dmolinagarcia/74HCT6526/img/20220725_B0.jpg

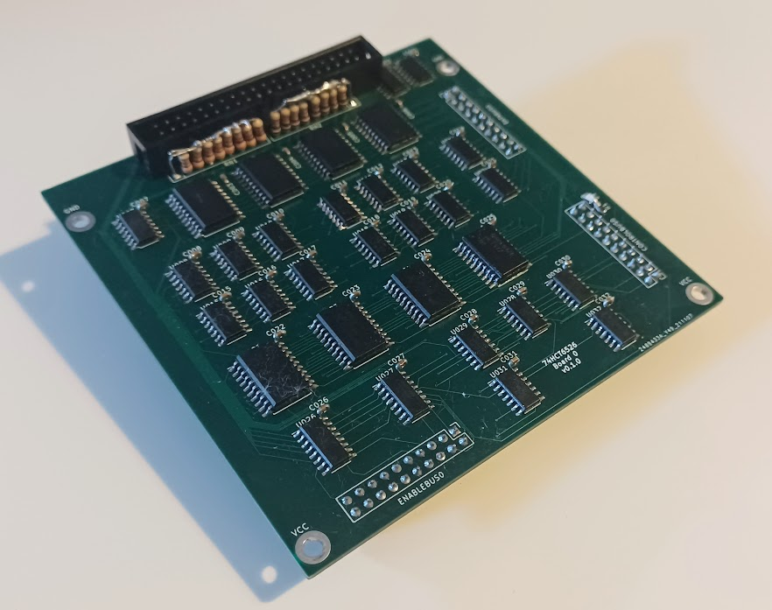
img/20220725_B0.jpg
