dmolinagarcia/74HCT6526/img/20220726_B1+B0+SBC.jpg

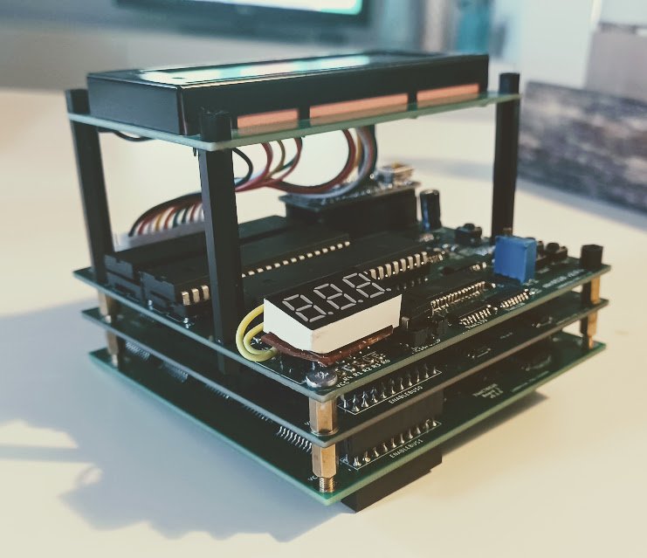
img/20220726_B1+B0+SBC.jpg
