dmolinagarcia/74HCT6526/img/20220726_B1.jpg

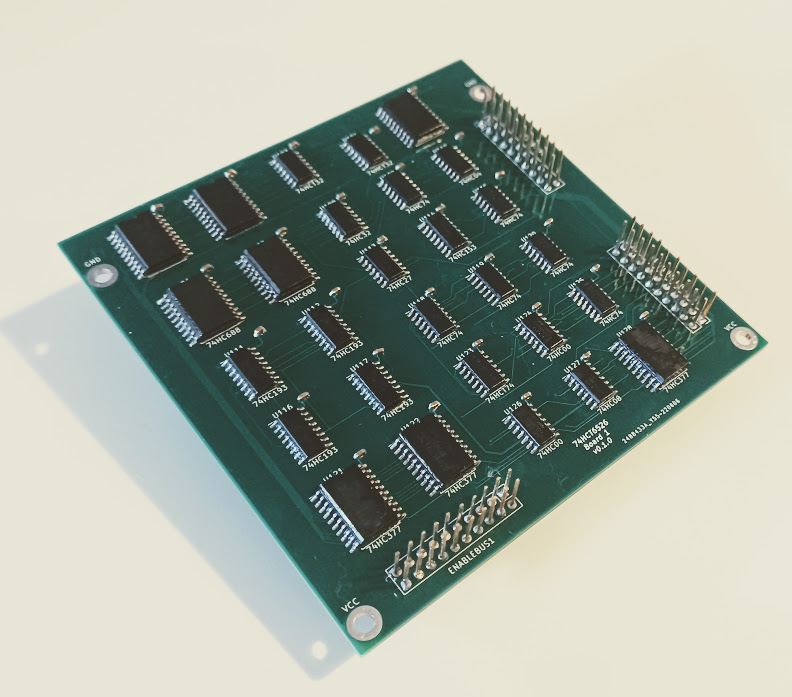
img/20220726_B1.jpg
