dmolinagarcia/74HCT6526/img/20230119_SDR_INPUT_fail.jpg

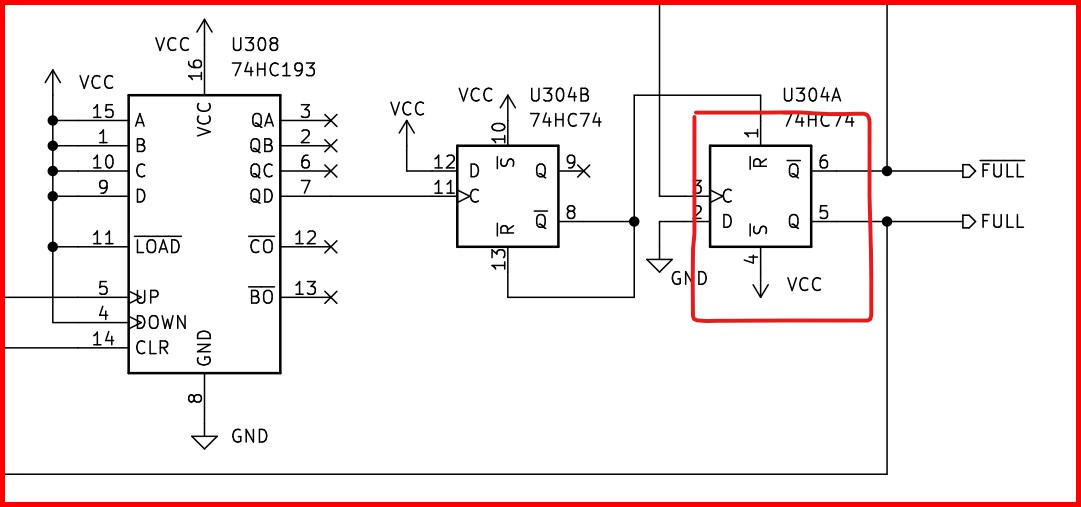
img/20230119_SDR_INPUT_fail.jpg
