dmolinagarcia/74HCT6526/img/20230120_SDR_RECEIVE_0x15.jpg

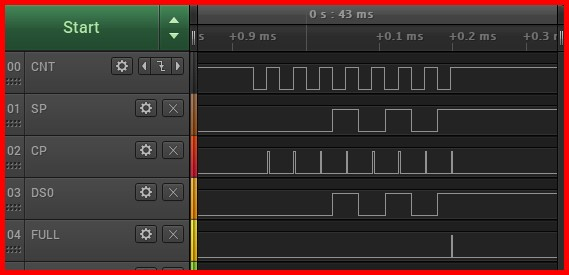
img/20230120_SDR_RECEIVE_0x15.jpg
