dmolinagarcia/74HCT6526/img/20230120_SDR_surgery2.jpg

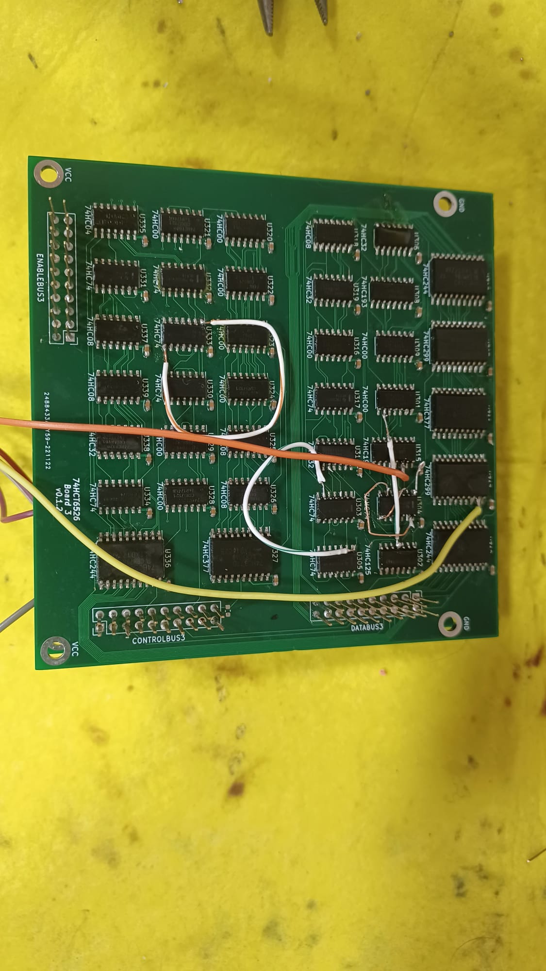
img/20230120_SDR_surgery2.jpg
