dmolinagarcia/74HCT6526/img/20230506_B3_NEWLOOK.jpeg

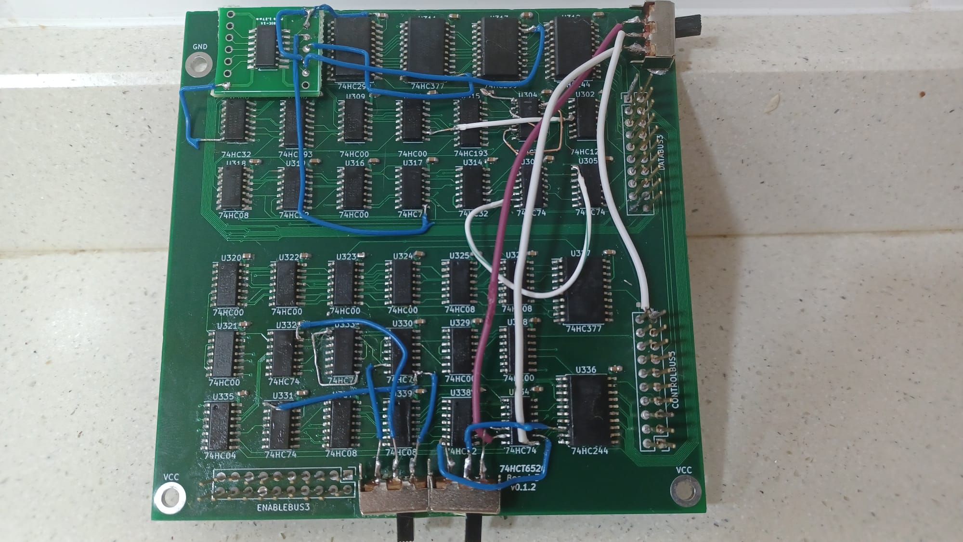
img/20230506_B3_NEWLOOK.jpeg
