dmolinagarcia/74HCT6526/img/All3_20221001.jpg

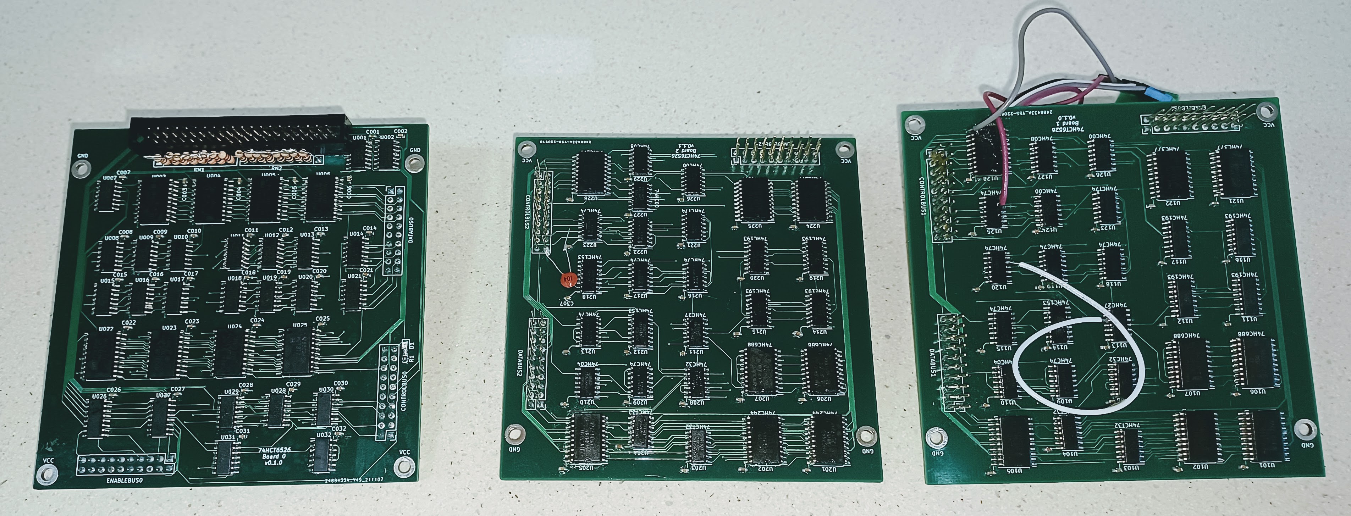
img/All3_20221001.jpg
