dmolinagarcia/74HCT6526/img/flag_detector_fail.jpg

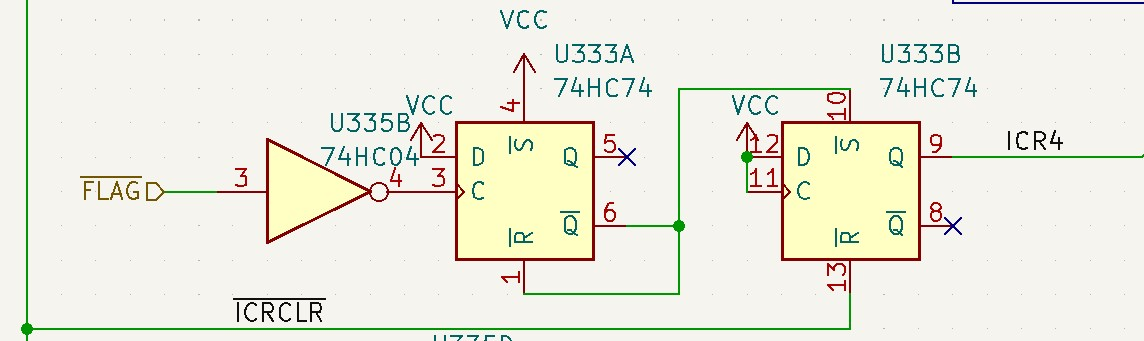
img/flag_detector_fail.jpg
