dmolinagarcia/74HCT6526/img/flag_detector_ok.jpg

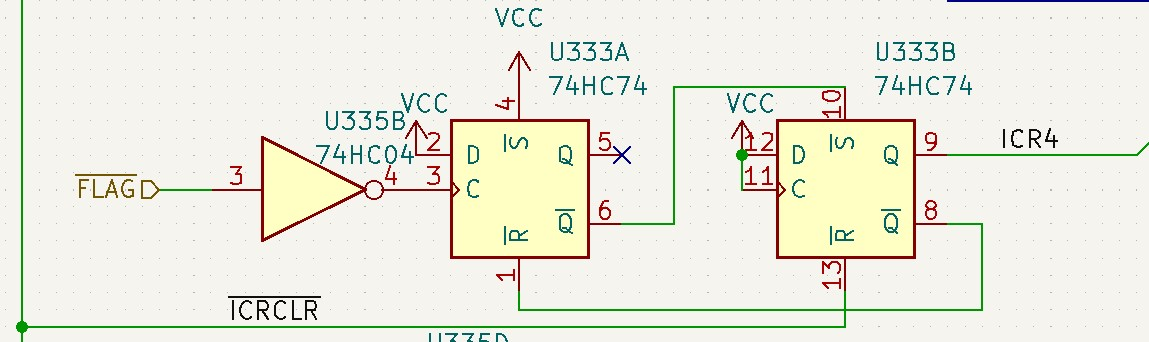
img/flag_detector_ok.jpg
