dmolinagarcia/74HCT6526/img/Photos-001/20230319_prefix.jpg

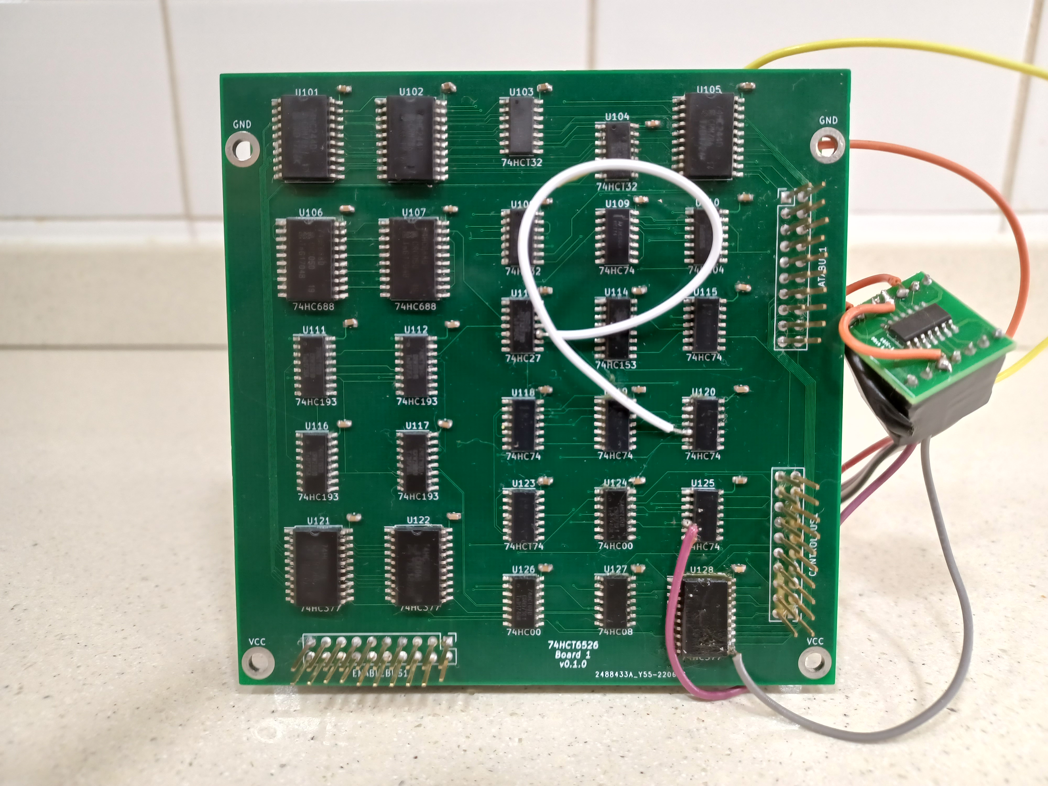
img/Photos-001/20230319_prefix.jpg
