dmolinagarcia/74HCT6526/img/SDR_stateMachine_v1.jpg

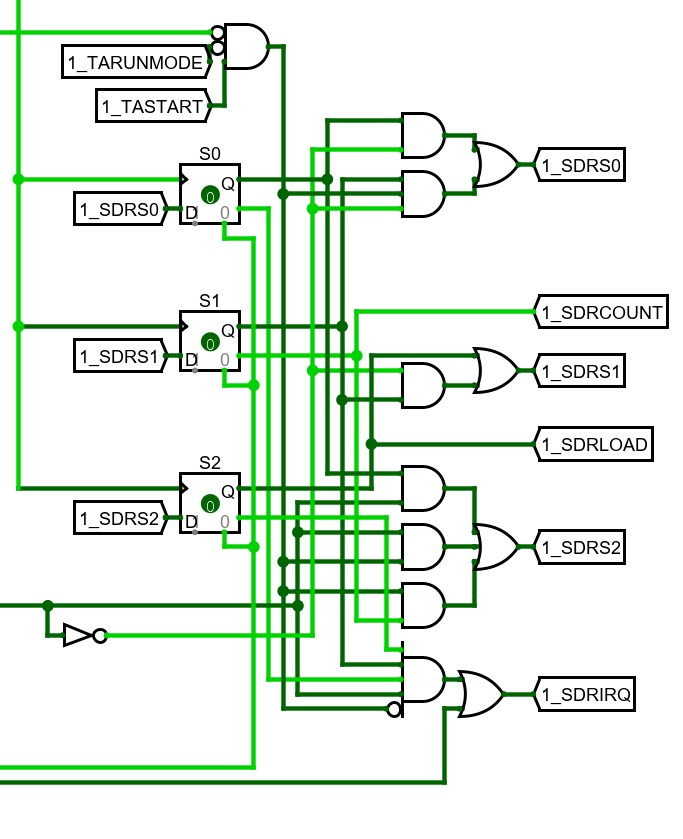
img/SDR_stateMachine_v1.jpg
