dmolinagarcia/74HCT6526/img/SDR_stateMachine_v2.jpg

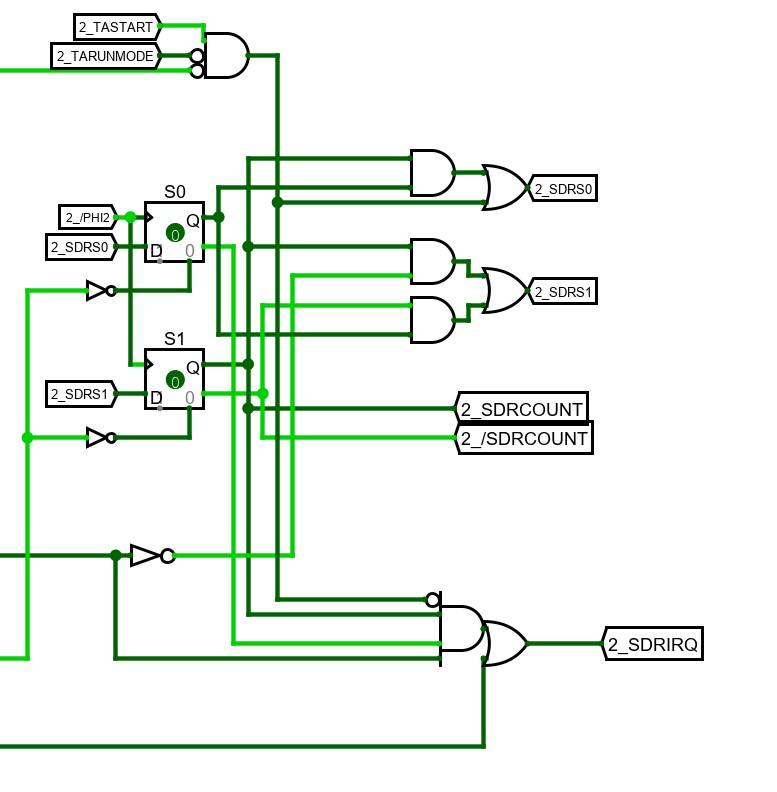
img/SDR_stateMachine_v2.jpg
