dmolinagarcia/74HCT6526/img/STACK_20221001.jpg

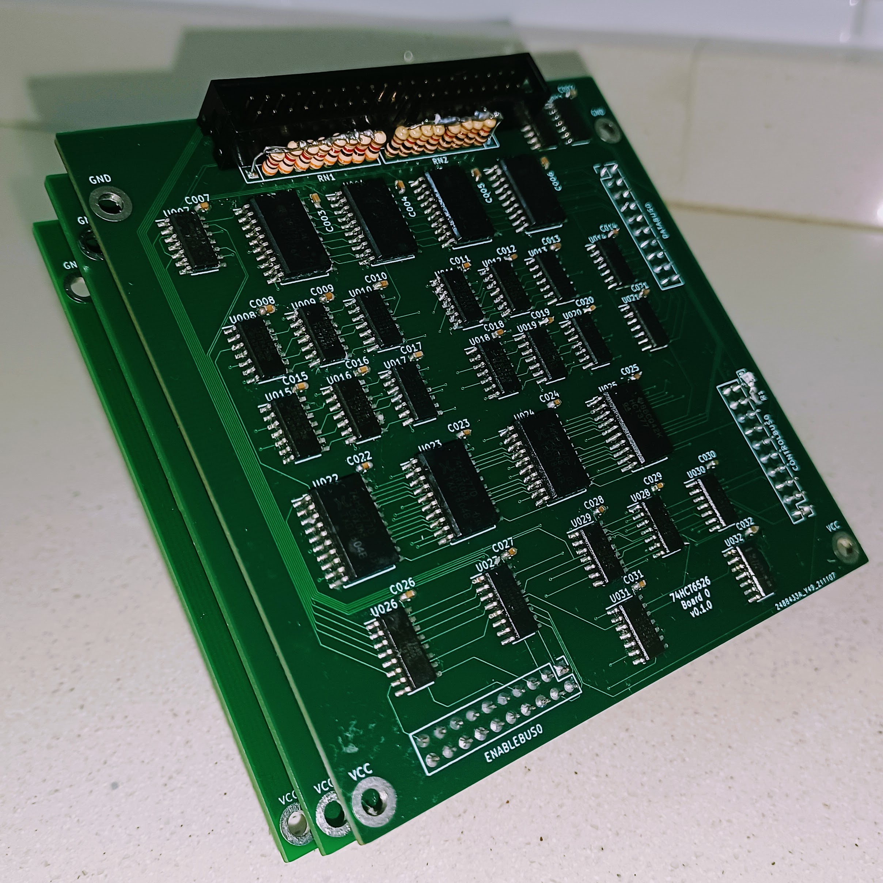
img/STACK_20221001.jpg
