dmolinagarcia/74HCT6526/img/timer2_clockpipeline - copia.png

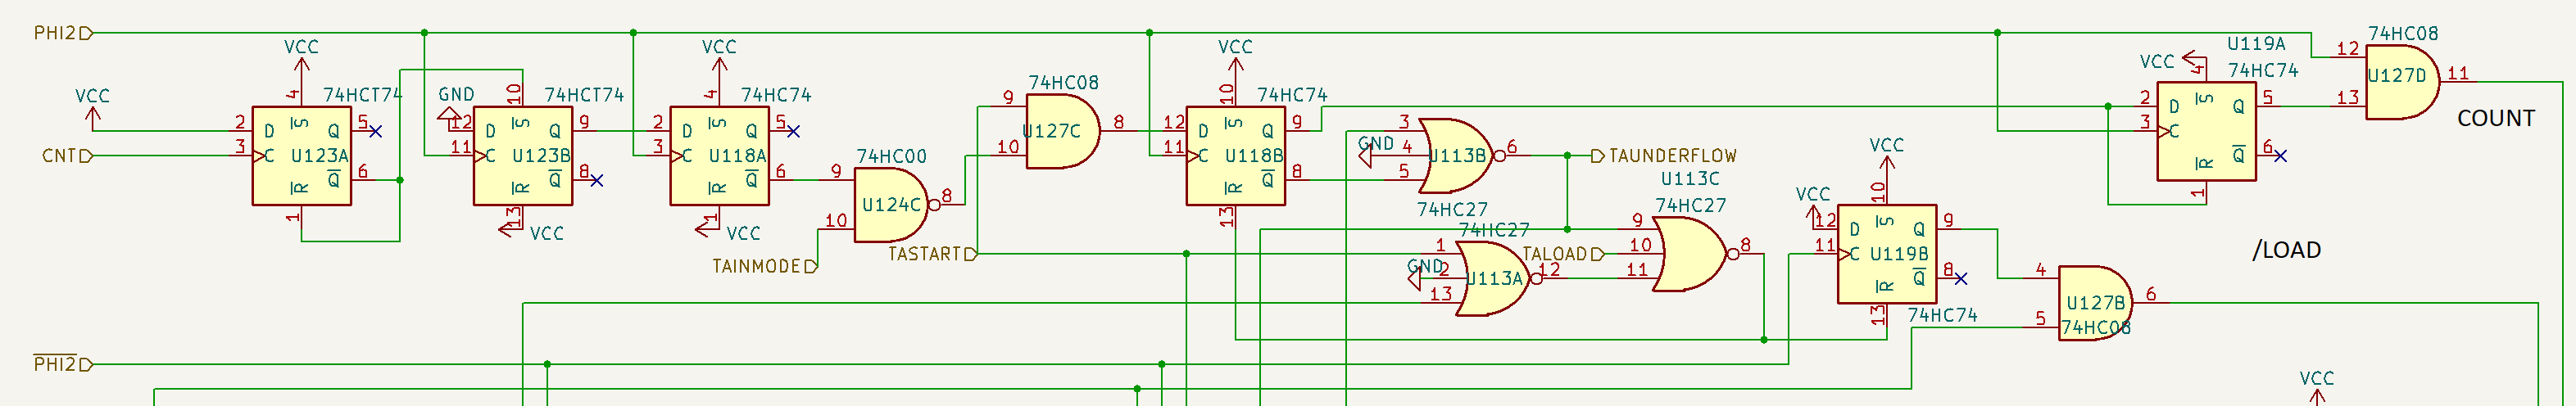
img/timer2_clockpipeline - copia.png
