dmolinagarcia/74HCT6526/img/timer2_clockpipeline_annotated.png

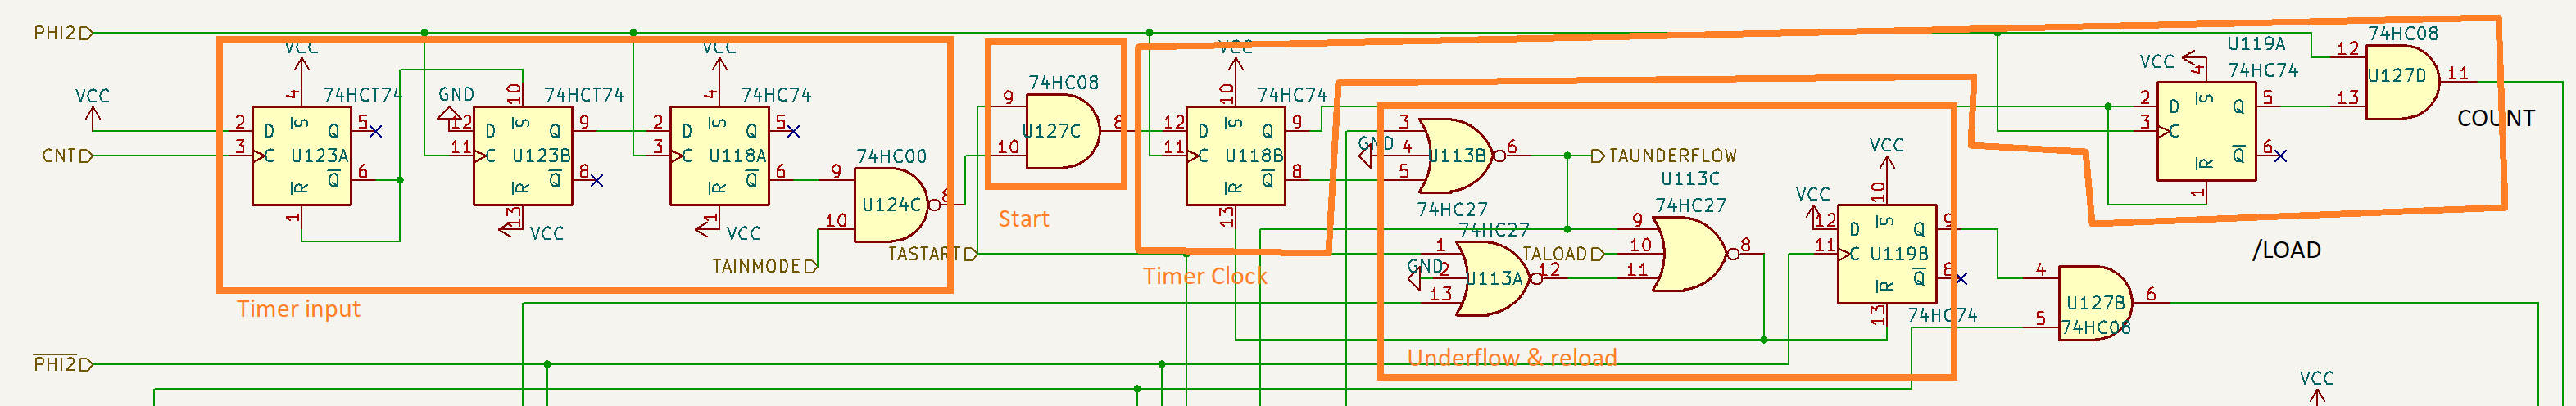
img/timer2_clockpipeline_annotated.png
