dmolinagarcia/74HCT6526/img/Photos-001/20230319_step2.jpg

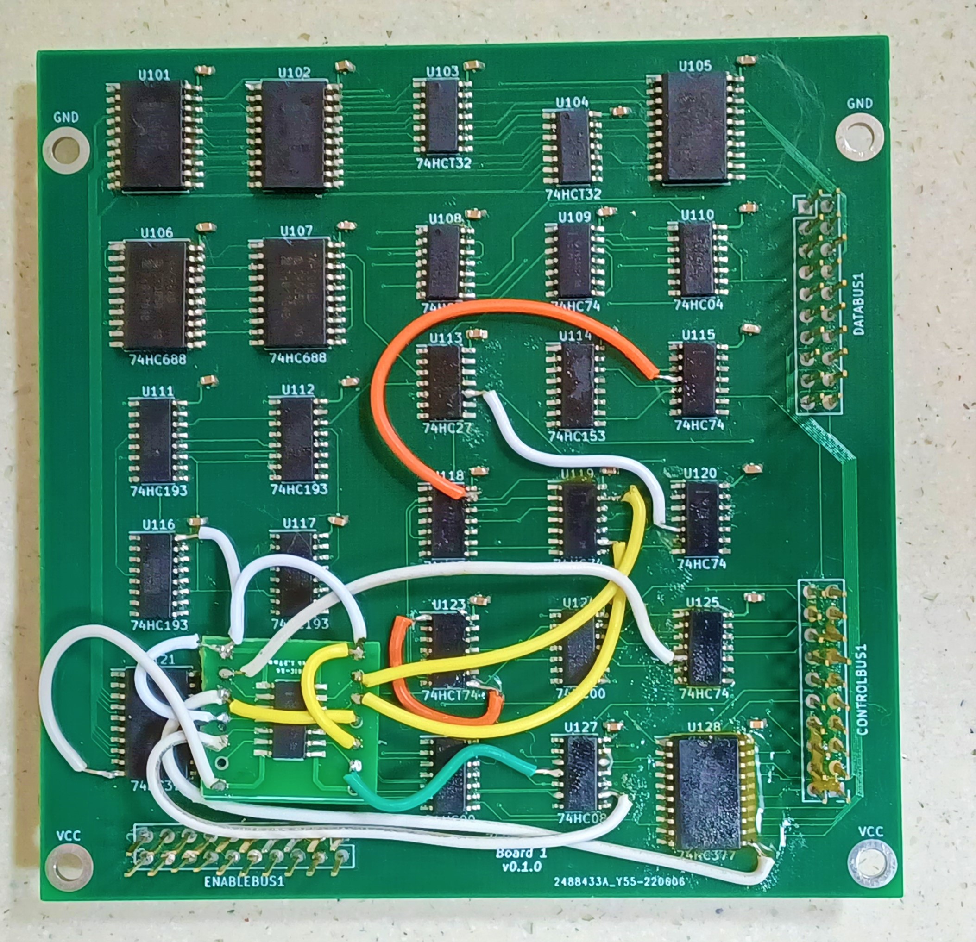
img/Photos-001/20230319_step2.jpg
