dmolinagarcia/74HCT6526/B3/Issues/02/STAGE0/02_old_hct_test6.csv

Time[s] | PHI2 | PB6 | PB7 | /CS | /IRQ | D0 | D1 | D7
0.099773000000000 | 1 | 1 | 1 | 0 | 1 | 0 | 0 | 0
0.099773125000000 | 1 | 1 | 1 | 0 | 1 | 0 | 0 | 0
0.099773250000000 | 1 | 1 | 1 | 0 | 1 | 0 | 0 | 0
0.099773375000000 | 1 | 1 | 1 | 0 | 1 | 0 | 0 | 0
0.099773500000000 | 0 | 1 | 1 | 1 | 1 | 0 | 0 | 0
0.099773625000000 | 0 | 1 | 1 | 1 | 1 | 0 | 0 | 0
0.099773750000000 | 0 | 1 | 1 | 1 | 1 | 0 | 0 | 1
0.099773875000000 | 0 | 1 | 1 | 1 | 1 | 0 | 0 | 1
0.099774000000000 | 1 | 1 | 1 | 1 | 1 | 0 | 0 | 1
0.099774125000000 | 1 | 1 | 1 | 1 | 1 | 0 | 0 | 1
0.099774250000000 | 1 | 1 | 1 | 1 | 1 | 1 | 0 | 1
0.099774375000000 | 1 | 1 | 1 | 1 | 1 | 1 | 0 | 1
0.099774500000000 | 0 | 1 | 1 | 1 | 1 | 1 | 0 | 1
0.099774625000000 | 0 | 1 | 1 | 1 | 1 | 1 | 0 | 1
0.099774750000000 | 0 | 1 | 1 | 1 | 1 | 0 | 0 | 0
0.099774875000000 | 0 | 1 | 1 | 1 | 1 | 0 | 0 | 0
0.099775000000000 | 1 | 1 | 1 | 1 | 1 | 0 | 0 | 0
0.099775125000000 | 1 | 1 | 1 | 1 | 1 | 0 | 0 | 0
0.099775250000000 | 1 | 1 | 1 | 1 | 1 | 0 | 0 | 0
0.099775375000000 | 1 | 1 | 1 | 1 | 1 | 0 | 0 | 0
0.099775500000000 | 0 | 1 | 1 | 1 | 1 | 0 | 0 | 0
0.099775625000000 | 0 | 1 | 1 | 1 | 1 | 0 | 0 | 0
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
