dmolinagarcia/74HCT6526/B3/Issues/02/STAGE0/02_old_hct_test7.csv

Time[s] | PHI2 | PB6 | PB7 | /CS | /IRQ | D0 | D1 | D7
0.119735750000000 | 1 | 1 | 1 | 0 | 1 | 0 | 0 | 0
0.119735875000000 | 1 | 1 | 1 | 0 | 1 | 0 | 0 | 0
0.119736000000000 | 1 | 1 | 1 | 0 | 1 | 0 | 0 | 0
0.119736125000000 | 1 | 1 | 1 | 0 | 1 | 0 | 0 | 0
0.119736250000000 | 0 | 1 | 1 | 1 | 1 | 0 | 0 | 0
0.119736375000000 | 0 | 1 | 1 | 1 | 1 | 0 | 0 | 0
0.119736500000000 | 0 | 1 | 1 | 1 | 1 | 0 | 0 | 0
0.119736625000000 | 0 | 1 | 1 | 1 | 1 | 0 | 0 | 0
0.119736750000000 | 1 | 1 | 1 | 1 | 1 | 0 | 0 | 0
0.119736875000000 | 1 | 1 | 1 | 1 | 1 | 0 | 0 | 0
0.119737000000000 | 1 | 1 | 1 | 1 | 1 | 1 | 0 | 1
0.119737125000000 | 1 | 1 | 1 | 1 | 1 | 1 | 0 | 1
0.119737250000000 | 0 | 1 | 1 | 1 | 1 | 1 | 0 | 1
0.119737375000000 | 0 | 1 | 1 | 1 | 1 | 1 | 0 | 1
0.119737500000000 | 0 | 1 | 1 | 1 | 1 | 0 | 0 | 0
0.119737625000000 | 0 | 1 | 1 | 1 | 1 | 0 | 0 | 0
0.119737750000000 | 1 | 1 | 1 | 1 | 1 | 0 | 0 | 0
0.119737875000000 | 1 | 1 | 1 | 1 | 1 | 0 | 0 | 0
0.119738000000000 | 1 | 1 | 1 | 1 | 1 | 0 | 0 | 0
0.119738125000000 | 1 | 1 | 1 | 1 | 1 | 0 | 0 | 0
0.119738250000000 | 0 | 1 | 1 | 1 | 1 | 0 | 0 | 0
0.119738375000000 | 0 | 1 | 1 | 1 | 1 | 0 | 0 | 0
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
