dmolinagarcia/74HCT6526/B3/Issues/02/STAGE0/02_old_real_test4.csv

Time[s] | PHI2 | PB6 | PB7 | /CS | /IRQ | D0 | D1 | D7
0.019945375000000 | 1 | 1 | 1 | 1 | 1 | 0 | 0 | 1
0.019945500000000 | 1 | 1 | 1 | 0 | 1 | 0 | 0 | 1
0.019945625000000 | 1 | 1 | 1 | 0 | 1 | 0 | 0 | 0
0.019945750000000 | 1 | 1 | 1 | 0 | 1 | 0 | 0 | 0
0.019945875000000 | 0 | 1 | 1 | 0 | 1 | 0 | 0 | 0
0.019946000000000 | 0 | 1 | 1 | 1 | 1 | 0 | 0 | 0
0.019946125000000 | 0 | 1 | 1 | 1 | 1 | 0 | 0 | 0
0.019946250000000 | 0 | 1 | 1 | 1 | 1 | 0 | 0 | 0
0.019946375000000 | 0 | 1 | 1 | 1 | 1 | 0 | 0 | 0
0.019946500000000 | 1 | 1 | 1 | 1 | 1 | 0 | 0 | 0
0.019946625000000 | 1 | 1 | 1 | 1 | 1 | 0 | 0 | 0
0.019946750000000 | 1 | 1 | 1 | 1 | 1 | 1 | 0 | 1
0.019946875000000 | 0 | 1 | 1 | 1 | 1 | 1 | 0 | 1
0.019947000000000 | 0 | 1 | 1 | 1 | 1 | 1 | 0 | 1
0.019947125000000 | 0 | 1 | 1 | 1 | 1 | 1 | 0 | 1
0.019947250000000 | 0 | 1 | 1 | 1 | 1 | 0 | 0 | 0
0.019947375000000 | 0 | 1 | 1 | 1 | 1 | 0 | 0 | 0
0.019947500000000 | 1 | 1 | 1 | 1 | 1 | 0 | 0 | 0
0.019947625000000 | 1 | 1 | 1 | 1 | 1 | 0 | 0 | 0
0.019947750000000 | 1 | 1 | 1 | 1 | 1 | 0 | 0 | 0
0.019947875000000 | 1 | 1 | 1 | 1 | 1 | 0 | 0 | 0
0.019948000000000 | 0 | 1 | 1 | 1 | 1 | 0 | 0 | 0
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
