dmolinagarcia/74HCT6526/B3/Issues/02/STAGE0/02_old_real_test5.csv

Time[s] | PHI2 | PB6 | PB7 | /CS | /IRQ | D0 | D1 | D7
0.139693500000000 | 1 | 1 | 1 | 0 | 1 | 1 | 1 | 1
0.139693625000000 | 1 | 1 | 1 | 0 | 1 | 0 | 0 | 0
0.139693750000000 | 1 | 1 | 1 | 0 | 1 | 0 | 0 | 0
0.139693875000000 | 0 | 1 | 1 | 0 | 1 | 0 | 0 | 0
0.139694000000000 | 0 | 1 | 1 | 1 | 1 | 0 | 0 | 0
0.139694125000000 | 0 | 1 | 1 | 1 | 1 | 0 | 0 | 0
0.139694250000000 | 0 | 1 | 1 | 1 | 1 | 0 | 0 | 0
0.139694375000000 | 0 | 1 | 1 | 1 | 1 | 0 | 0 | 0
0.139694500000000 | 1 | 1 | 1 | 1 | 1 | 0 | 0 | 0
0.139694625000000 | 1 | 1 | 1 | 1 | 1 | 0 | 0 | 0
0.139694750000000 | 1 | 1 | 1 | 1 | 1 | 1 | 0 | 1
0.139694875000000 | 1 | 1 | 1 | 1 | 1 | 1 | 0 | 1
0.139695000000000 | 0 | 1 | 1 | 1 | 1 | 1 | 0 | 1
0.139695125000000 | 0 | 1 | 1 | 1 | 1 | 1 | 0 | 1
0.139695250000000 | 0 | 1 | 1 | 1 | 1 | 0 | 0 | 0
0.139695375000000 | 0 | 1 | 1 | 1 | 1 | 0 | 0 | 0
0.139695500000000 | 1 | 1 | 1 | 1 | 1 | 0 | 0 | 0
0.139695625000000 | 1 | 1 | 1 | 1 | 1 | 0 | 0 | 0
0.139695750000000 | 1 | 1 | 1 | 1 | 1 | 0 | 0 | 0
0.139695875000000 | 1 | 1 | 1 | 1 | 1 | 0 | 0 | 0
0.139696000000000 | 0 | 1 | 1 | 1 | 1 | 0 | 0 | 0
0.139696125000000 | 0 | 1 | 1 | 1 | 1 | 0 | 0 | 0
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
