dmolinagarcia/74HCT6526/img/20230506_TEST02_NEWHCT.jpeg

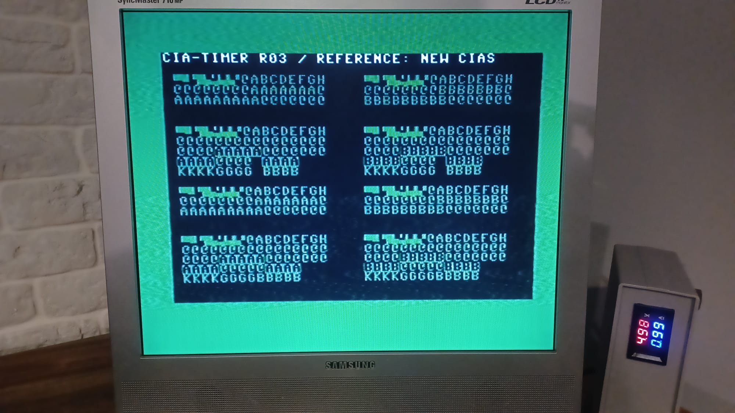
img/20230506_TEST02_NEWHCT.jpeg
