dmolinagarcia/74HCT6526/img/v0.2.2 6526 forum post/20230622_test02_new_ok.jpg

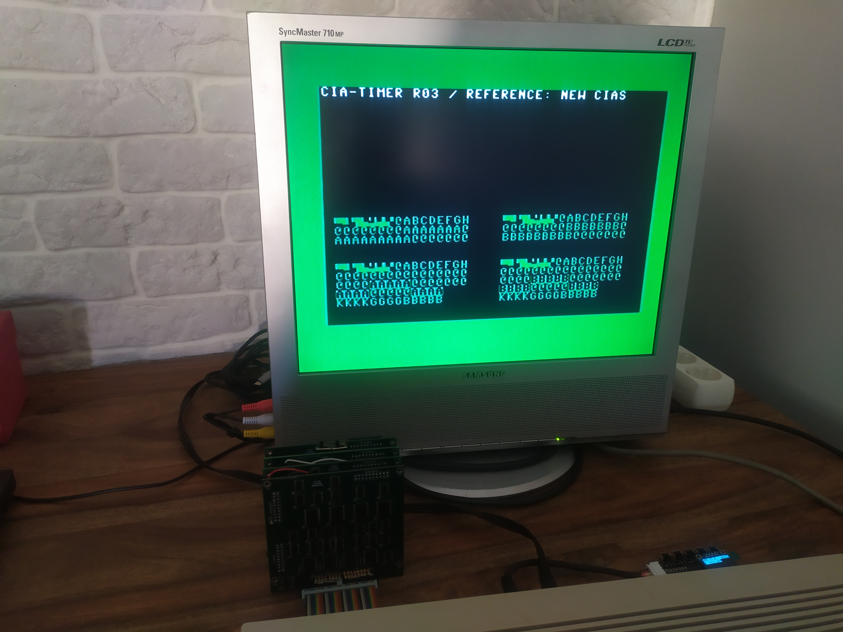
img/v0.2.2 6526 forum post/20230622_test02_new_ok.jpg
