dmolinagarcia/74HCT6526/img/20220810_TA_fix_sch.jpg

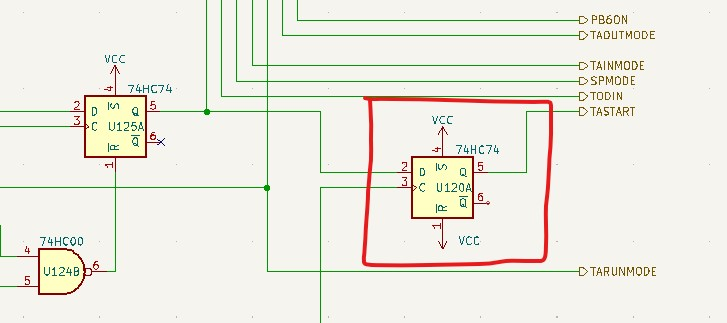
img/20220810_TA_fix_sch.jpg
