dmolinagarcia/74HCT6526/img/20230118_SDR_Output_Fix.jpg

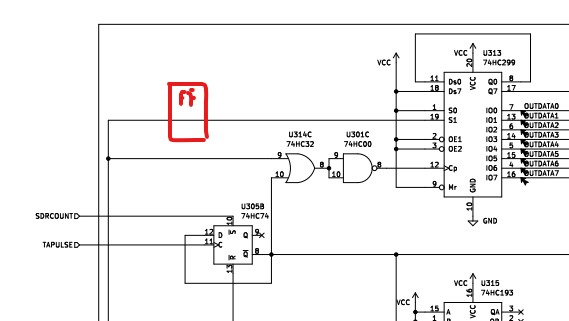
img/20230118_SDR_Output_Fix.jpg
