dmolinagarcia/74HCT6526/img/20230206_TB_Underflow_Issue.png

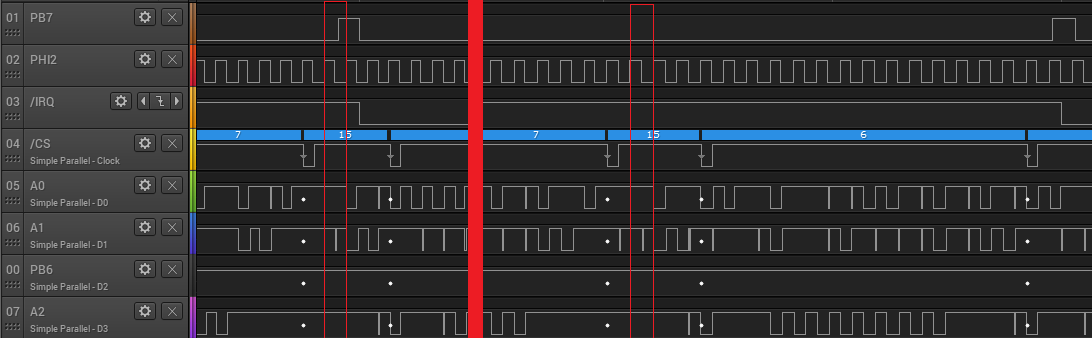
img/20230206_TB_Underflow_Issue.png
