dmolinagarcia/74HCT6526/pdf/B0.sch.v0.1.0.pdf

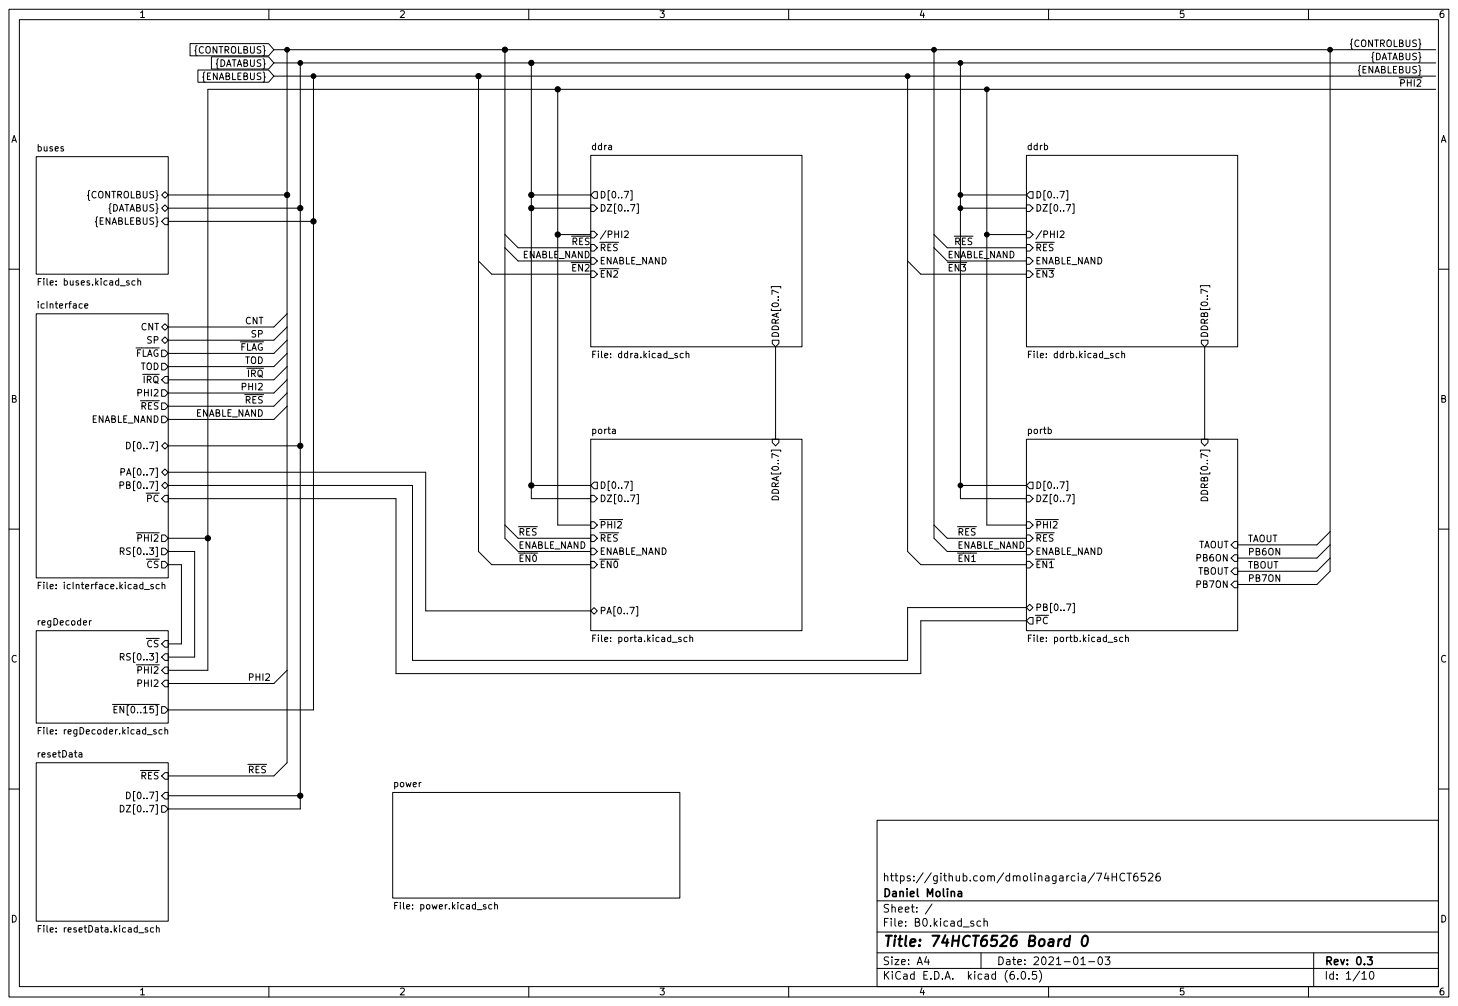
[picture p89: page 1]

DZ[0..7] resetData File: resetData.kicad_sch

https://github.com/dmolinagarcia/74HCT6526
File: B0.kicad_sch Sheet: / Daniel Molina

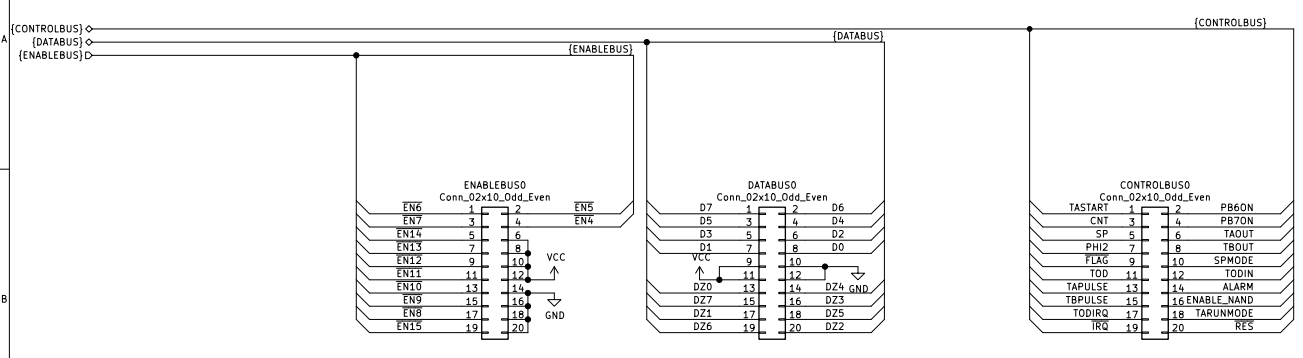
[picture p90: page 2]

https://github.com/dmolinagarcia/74HCT6526
File: buses.kicad_sch Sheet: /buses/ Daniel Molina

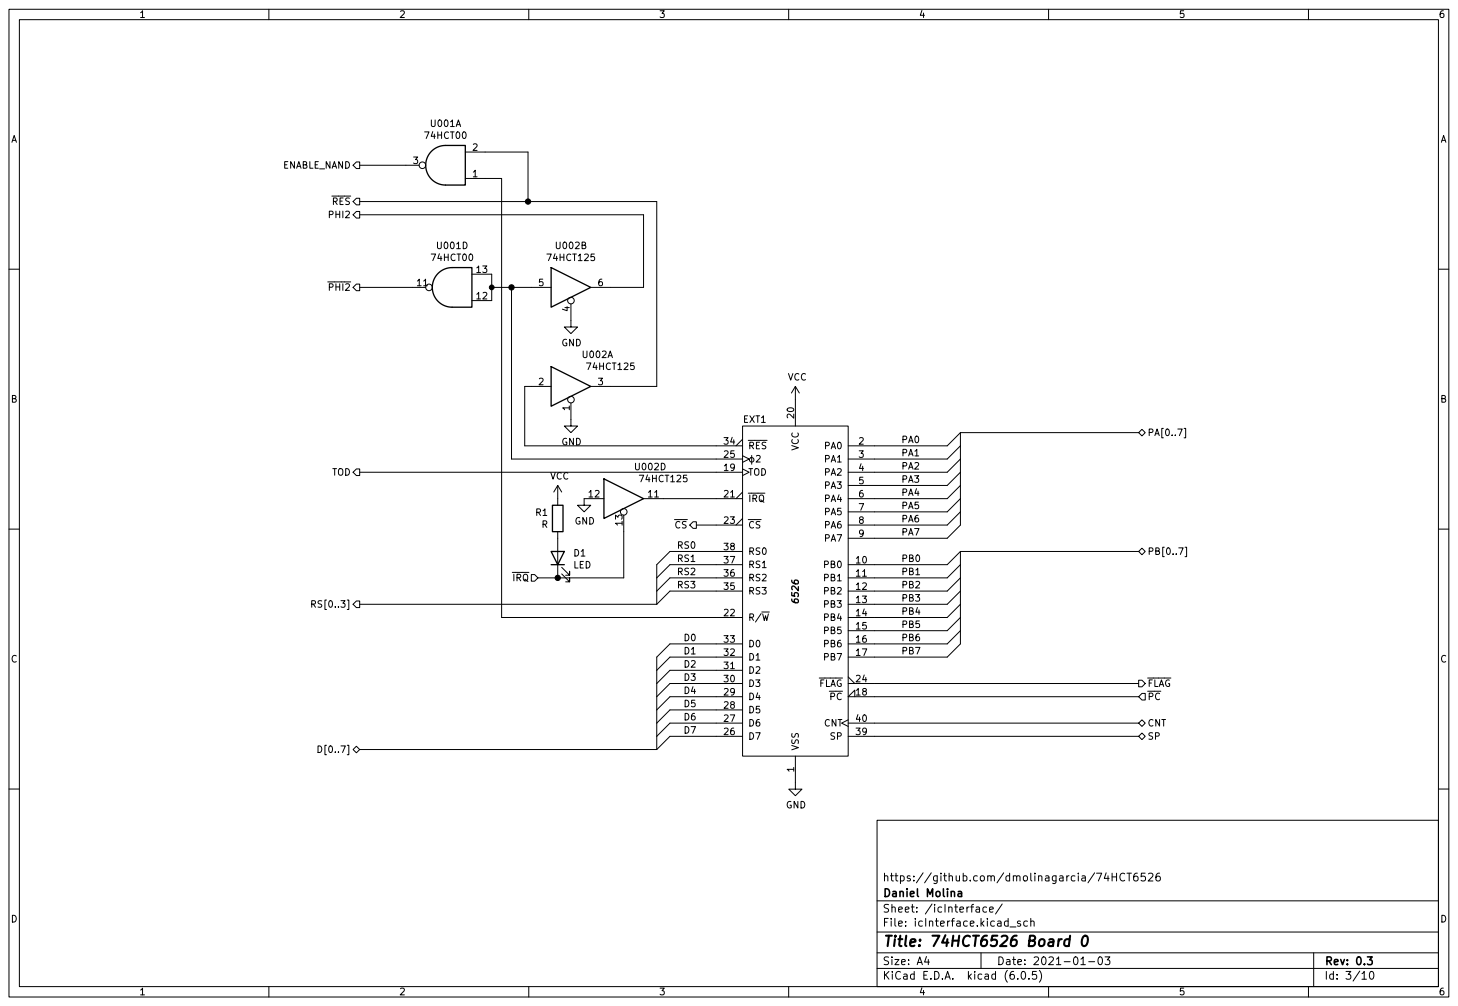
[picture p91: page 3]

https://github.com/dmolinagarcia/74HCT6526 12 3 U001A
74HCT00

File: icInterface.kicad_sch Sheet: /icInterface/ Daniel Molina

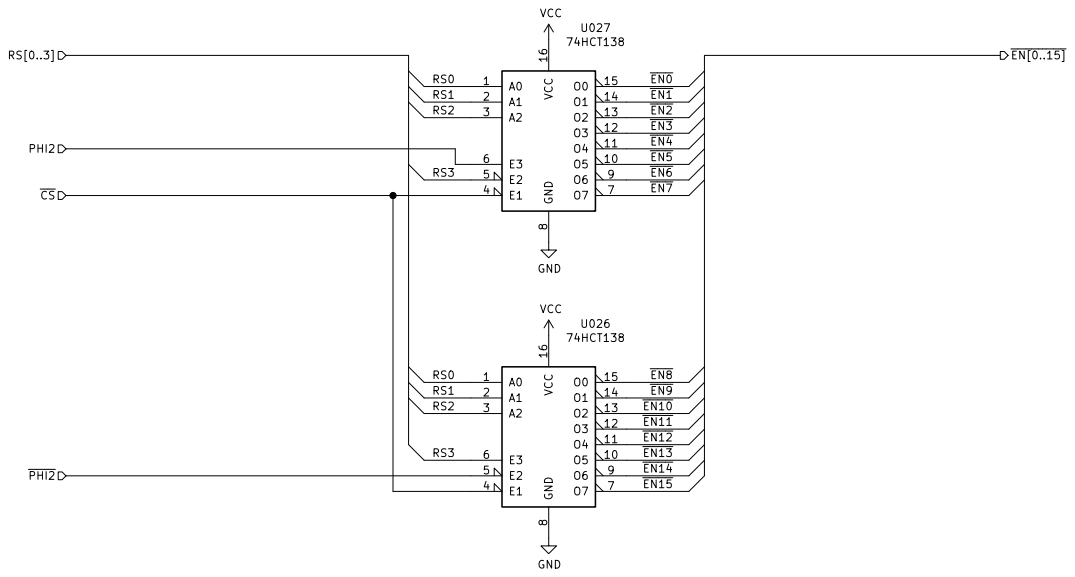
[picture p92: page 4]

https://github.com/dmolinagarcia/74HCT6526
Sheet: /regDecoder/ Daniel Molina

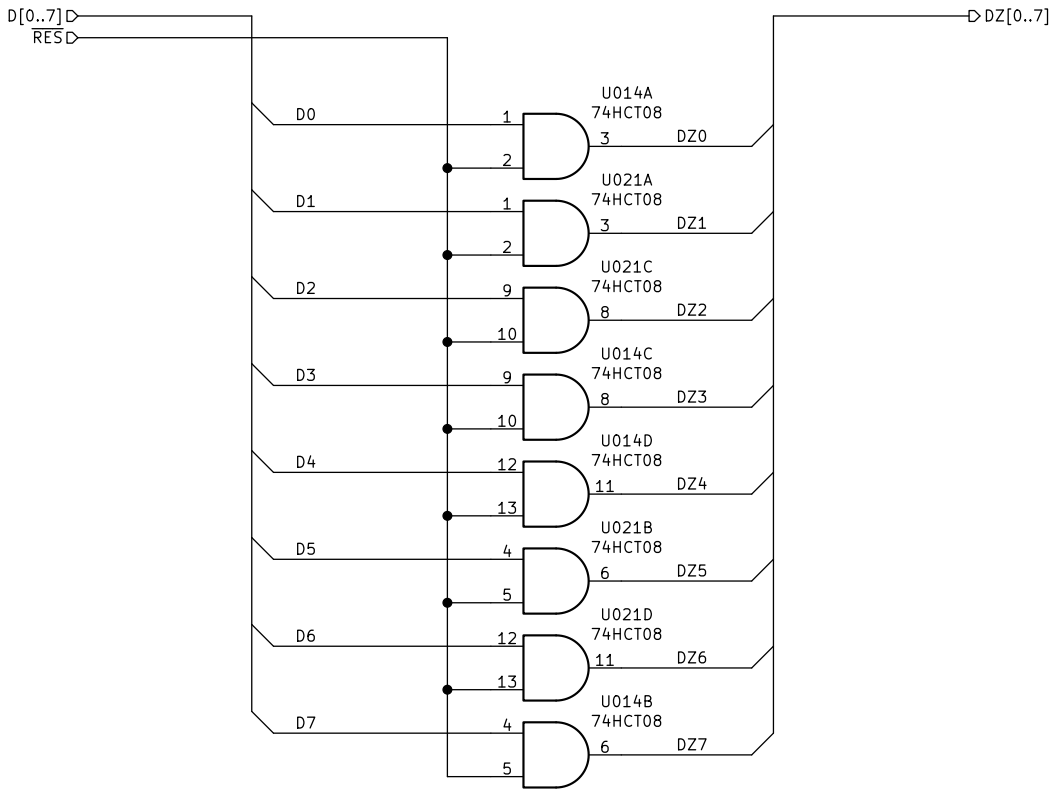
[picture p93: page 5]

https://github.com/dmolinagarcia/74HCT6526
File: resetData.kicad_sch Sheet: /resetData/ Daniel Molina

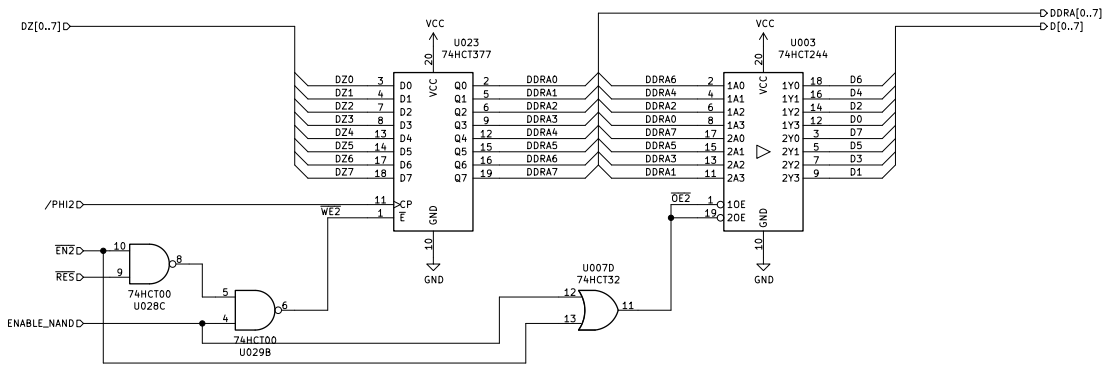
[picture p94: page 6]

https://github.com/dmolinagarcia/74HCT6526 GND

File: ddra.kicad_sch Sheet: /ddra/ Daniel Molina

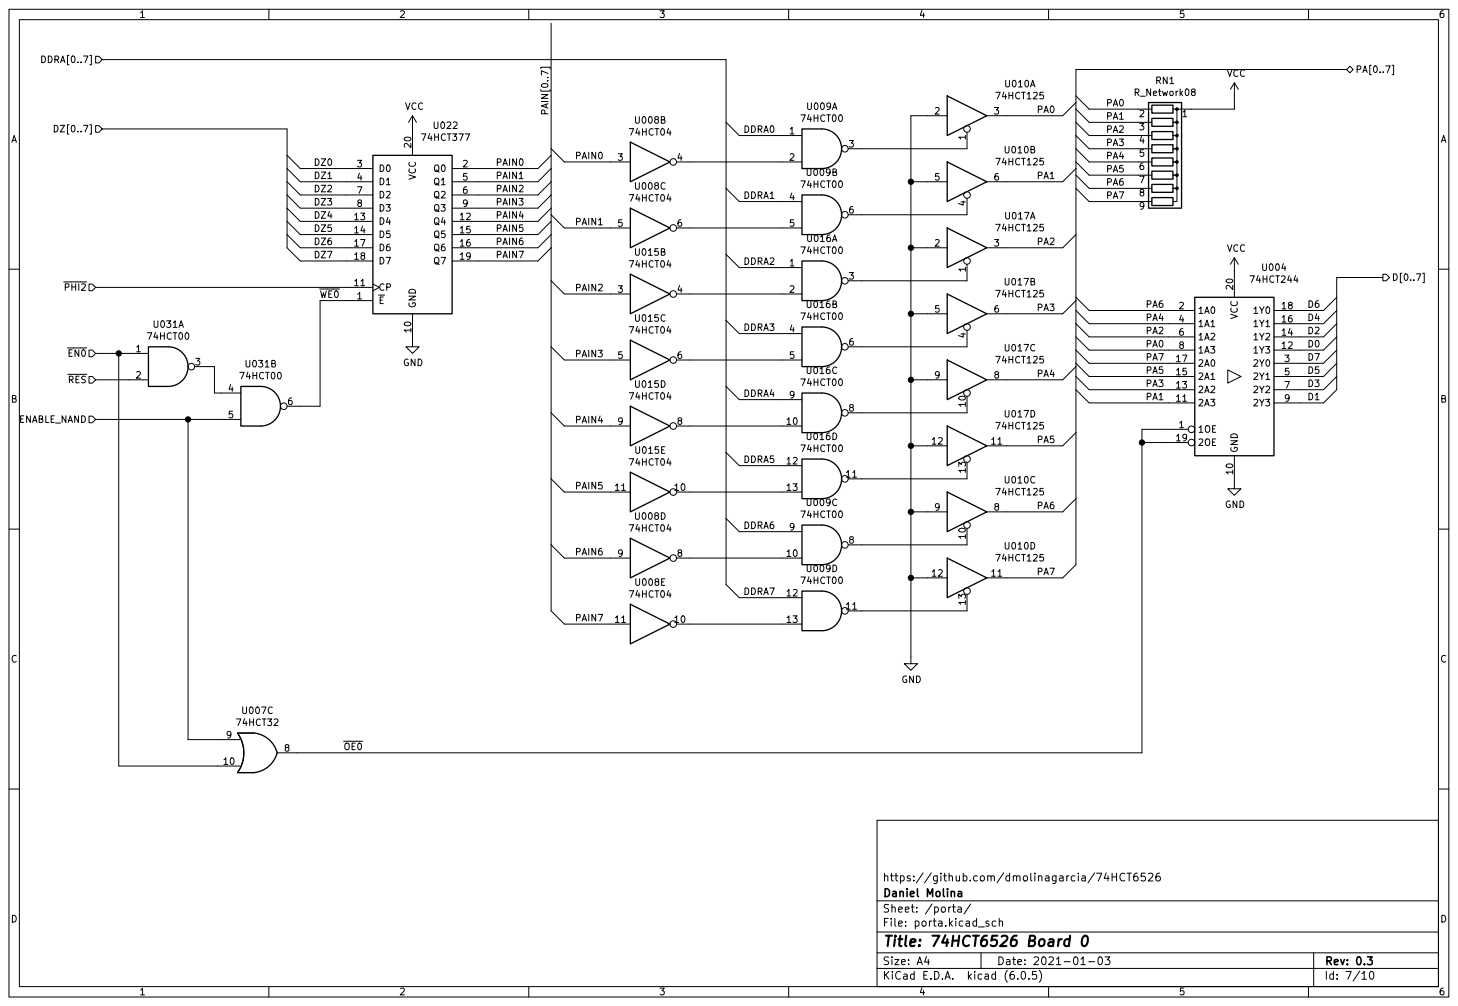
[picture p95: page 7]

Sheet: /porta/ Daniel Molina

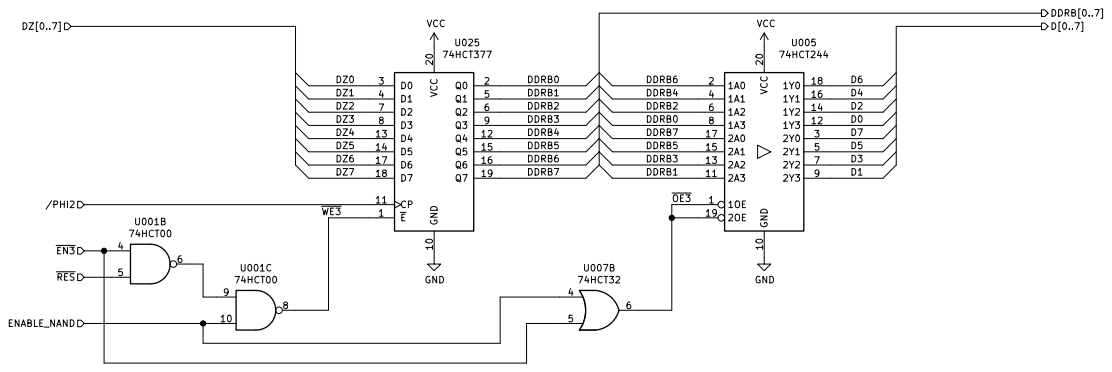
[picture p96: page 8]

https://github.com/dmolinagarcia/74HCT6526
File: ddrb.kicad_sch Sheet: /ddrb/ Daniel Molina

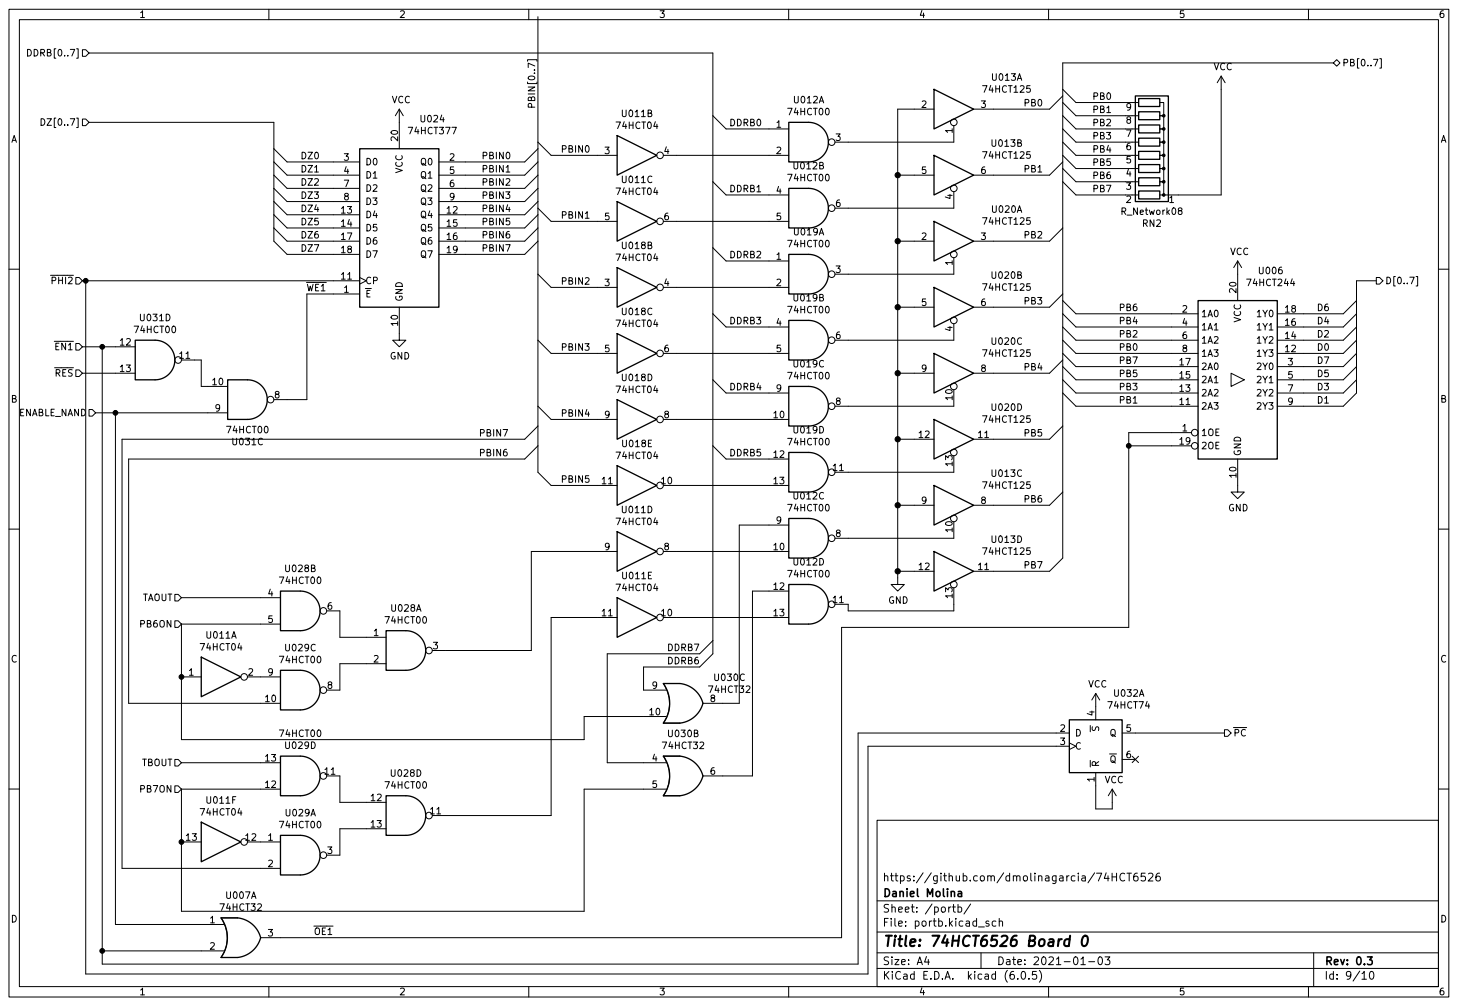
[picture p97: page 9]

https://github.com/dmolinagarcia/74HCT6526
Sheet: /portb/ Daniel Molina

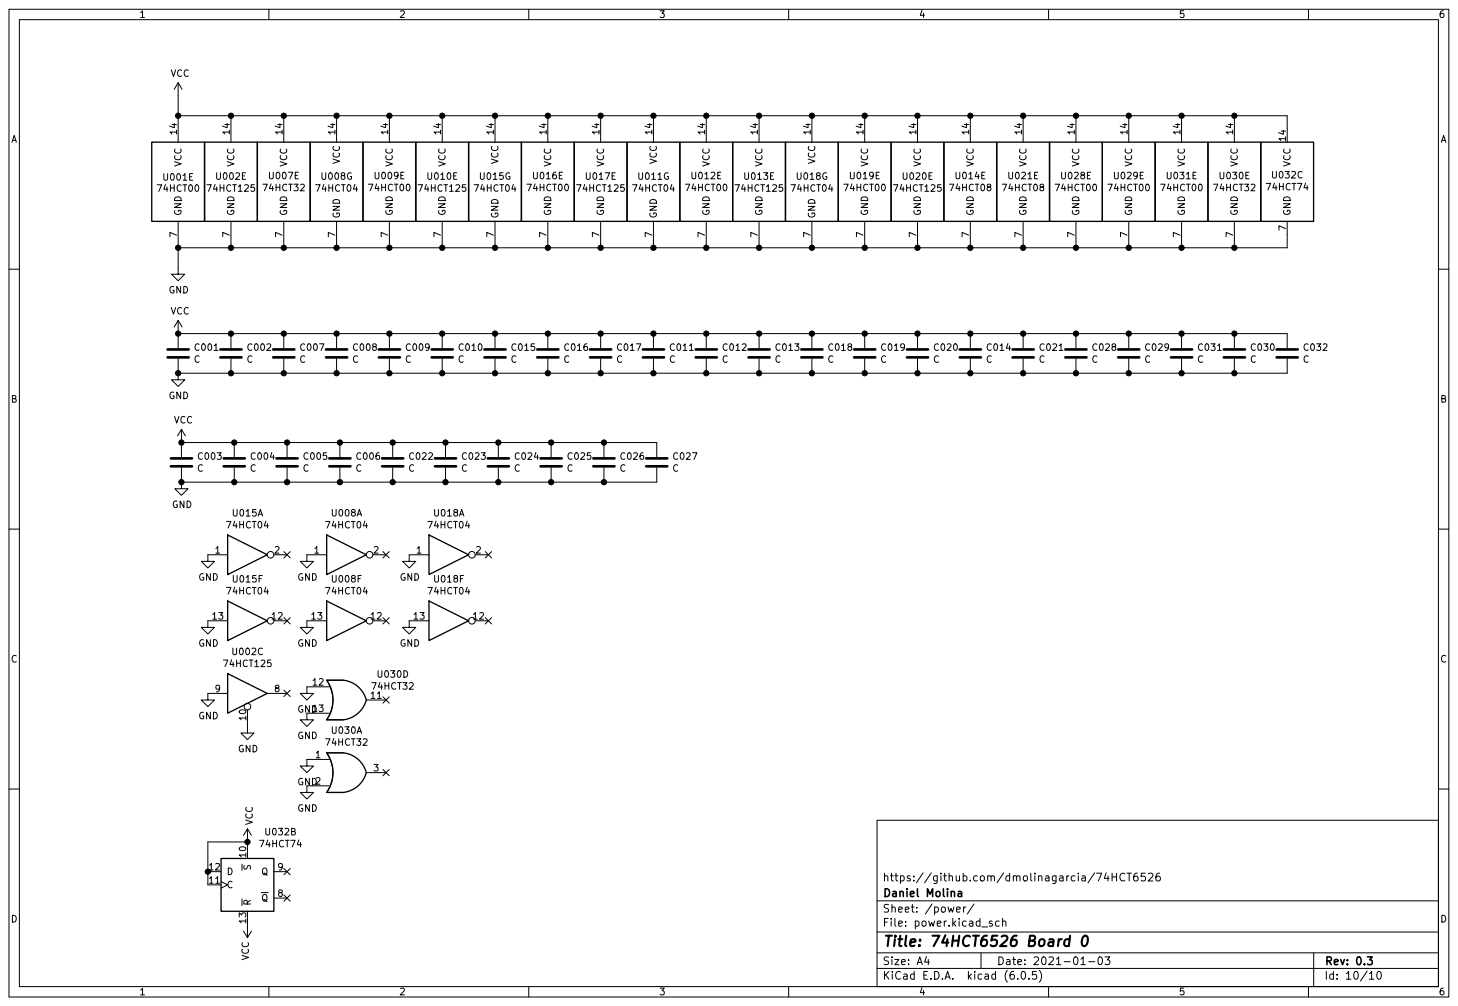
[picture p98: page 10]

https://github.com/dmolinagarcia/74HCT6526 GND

Sheet: /power/ Daniel Molina
