dmolinagarcia/74HCT6526/pdf/B0.sch.v0.1.2.pdf

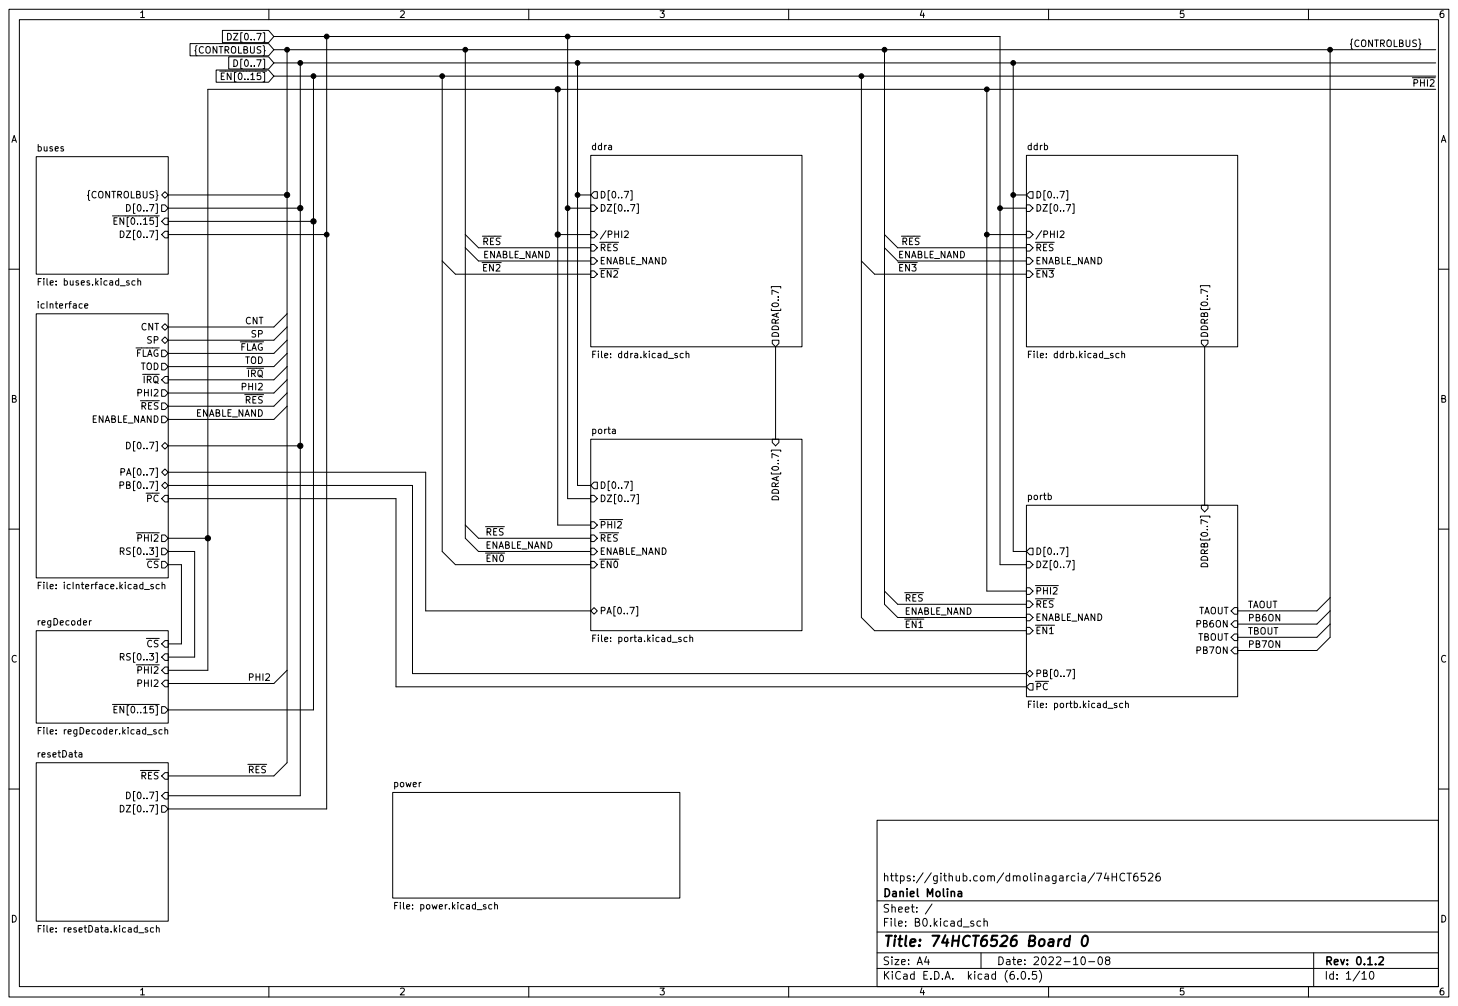
[picture p105: page 1]

DZ[0..7] buses File: buses.kicad_sch D[0..7]

DZ[0..7] resetData File: resetData.kicad_sch

https://github.com/dmolinagarcia/74HCT6526
File: B0.kicad_sch Sheet: / Daniel Molina

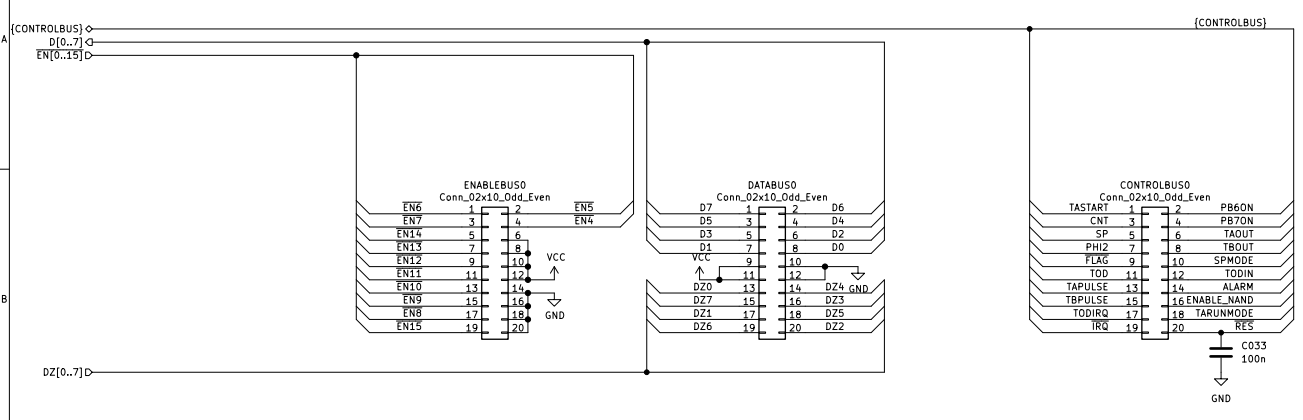
[picture p106: page 2]

https://github.com/dmolinagarcia/74HCT6526
File: buses.kicad_sch Sheet: /buses/ Daniel Molina

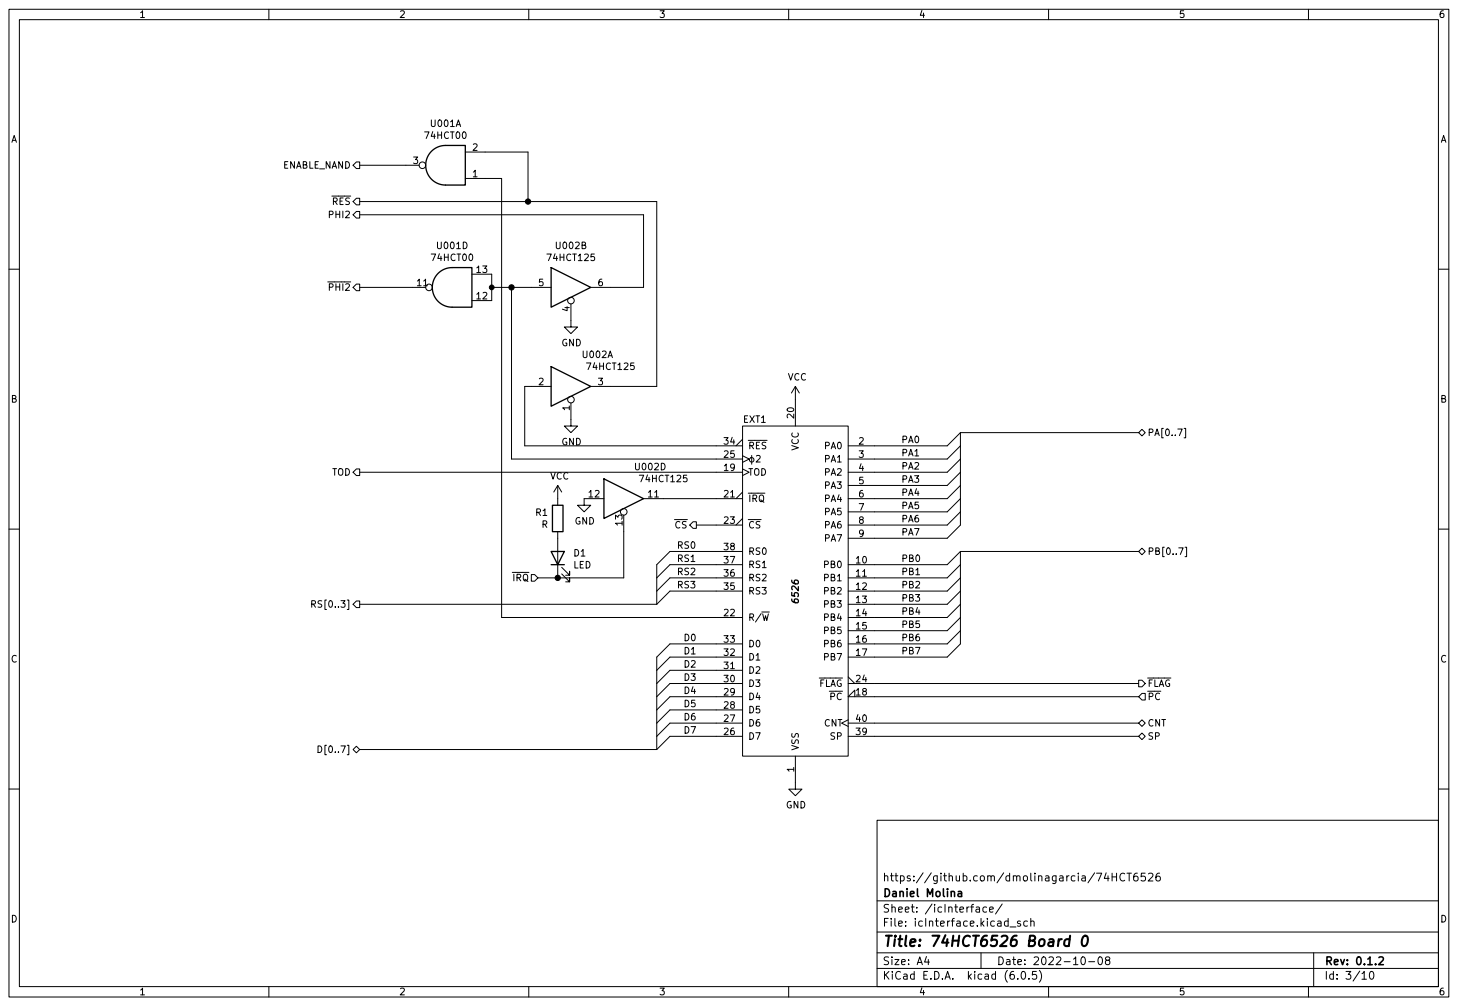
[picture p107: page 3]

https://github.com/dmolinagarcia/74HCT6526 12 3 U001A
74HCT00

File: icInterface.kicad_sch Sheet: /icInterface/ Daniel Molina


https://github.com/dmolinagarcia/74HCT6526
Sheet: /regDecoder/ Daniel Molina


https://github.com/dmolinagarcia/74HCT6526
File: resetData.kicad_sch Sheet: /resetData/ Daniel Molina


https://github.com/dmolinagarcia/74HCT6526 GND

File: ddra.kicad_sch Sheet: /ddra/ Daniel Molina

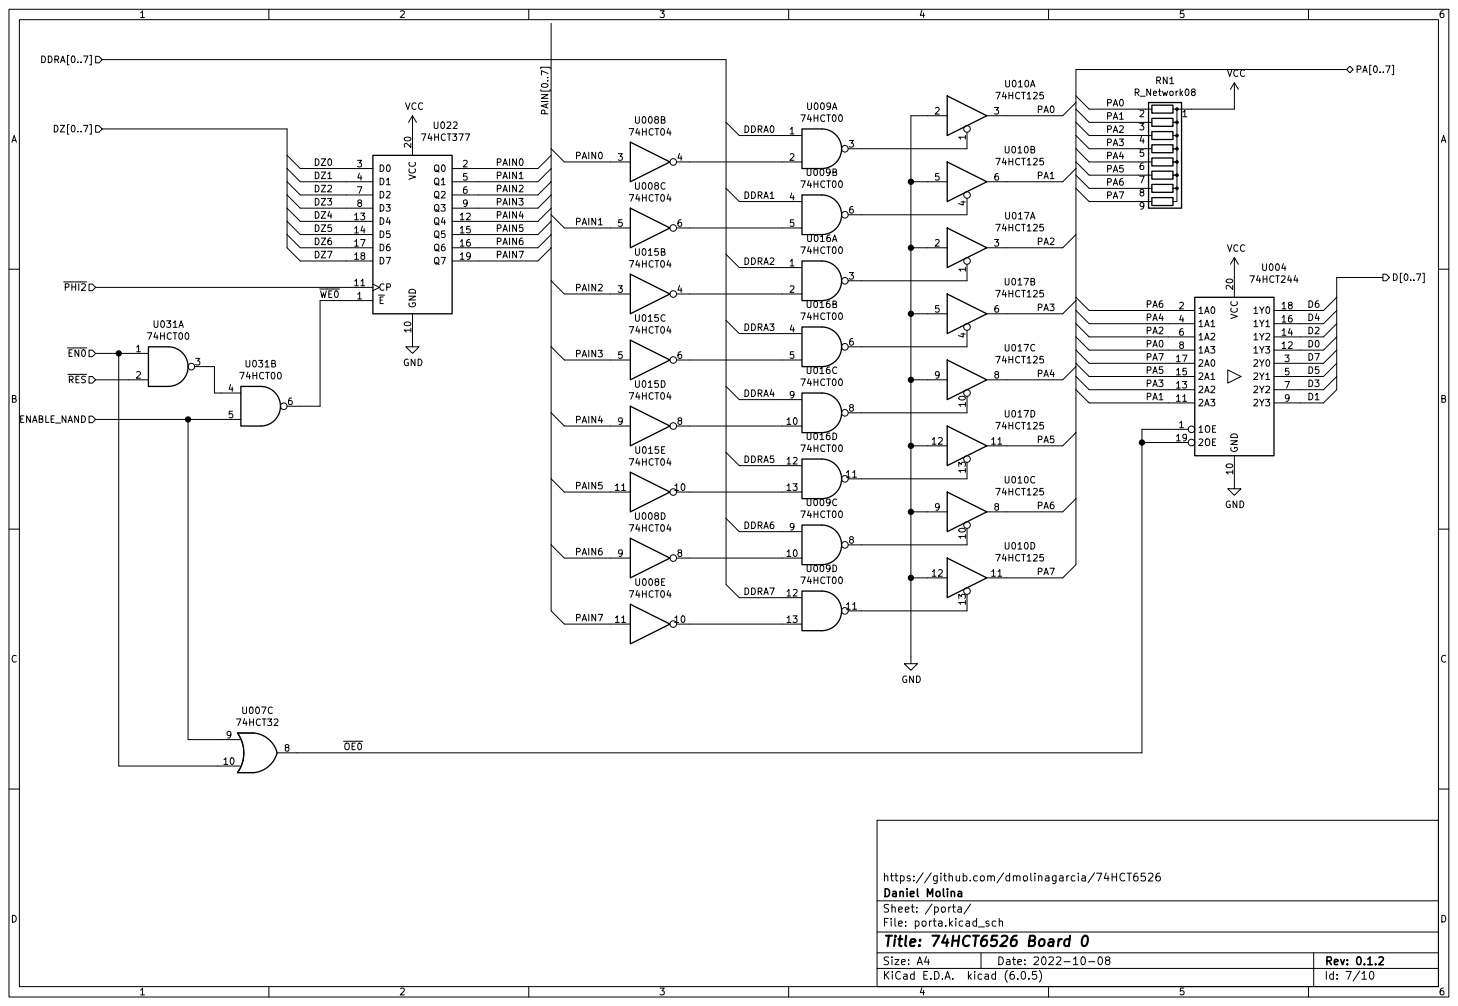
[picture p108: page 7]

Sheet: /porta/ Daniel Molina


https://github.com/dmolinagarcia/74HCT6526
File: ddrb.kicad_sch Sheet: /ddrb/ Daniel Molina

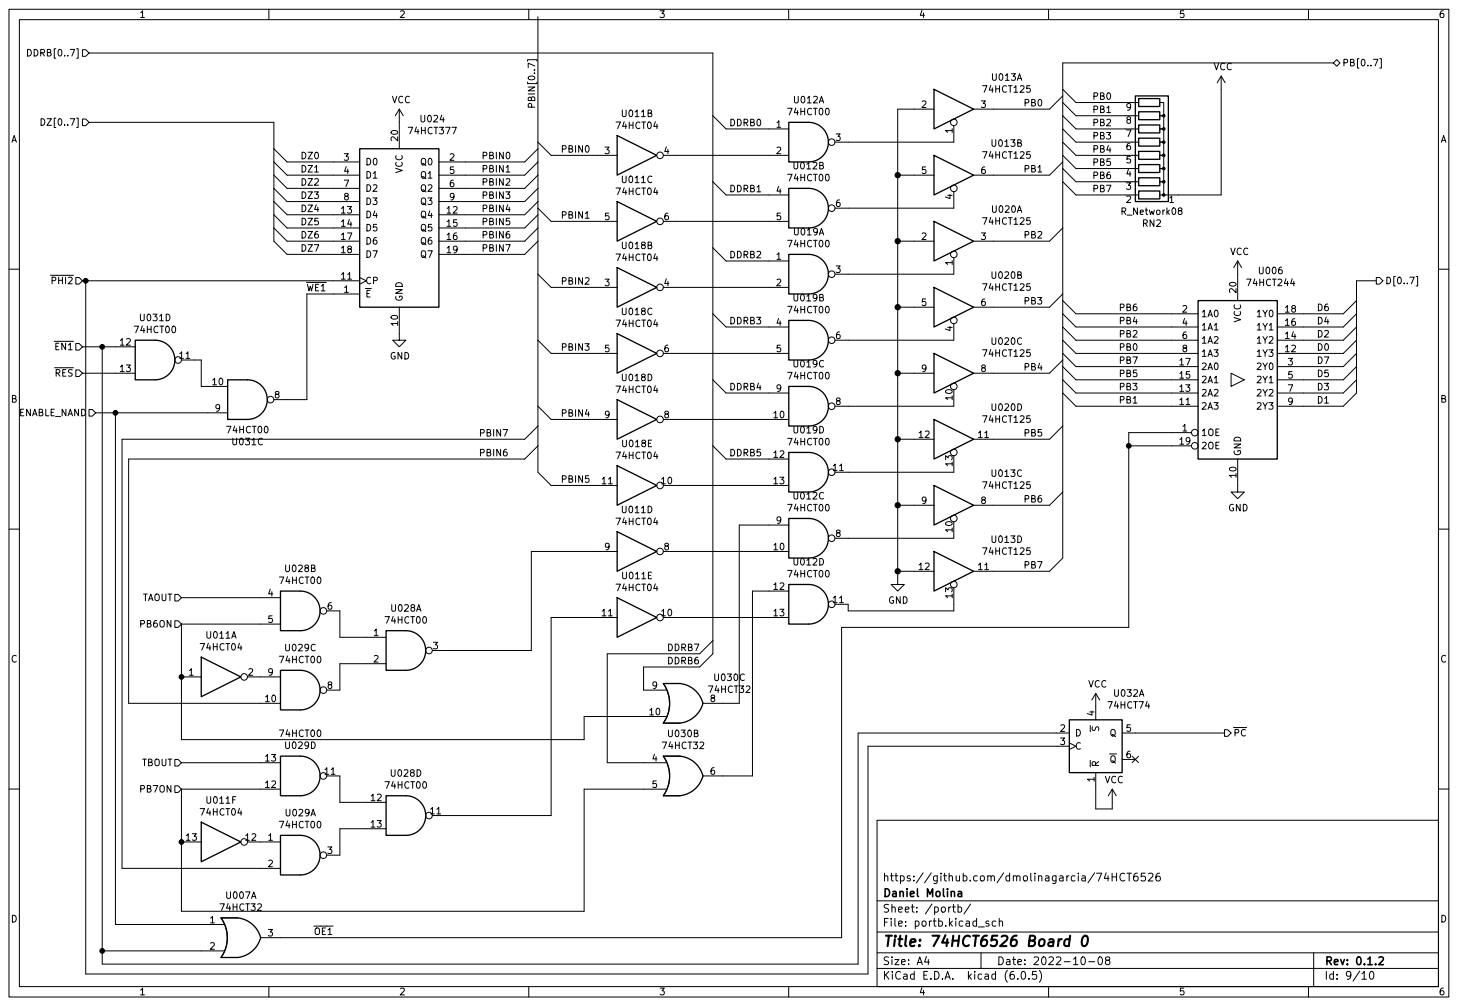
[picture p109: page 9]

https://github.com/dmolinagarcia/74HCT6526
Sheet: /portb/ Daniel Molina

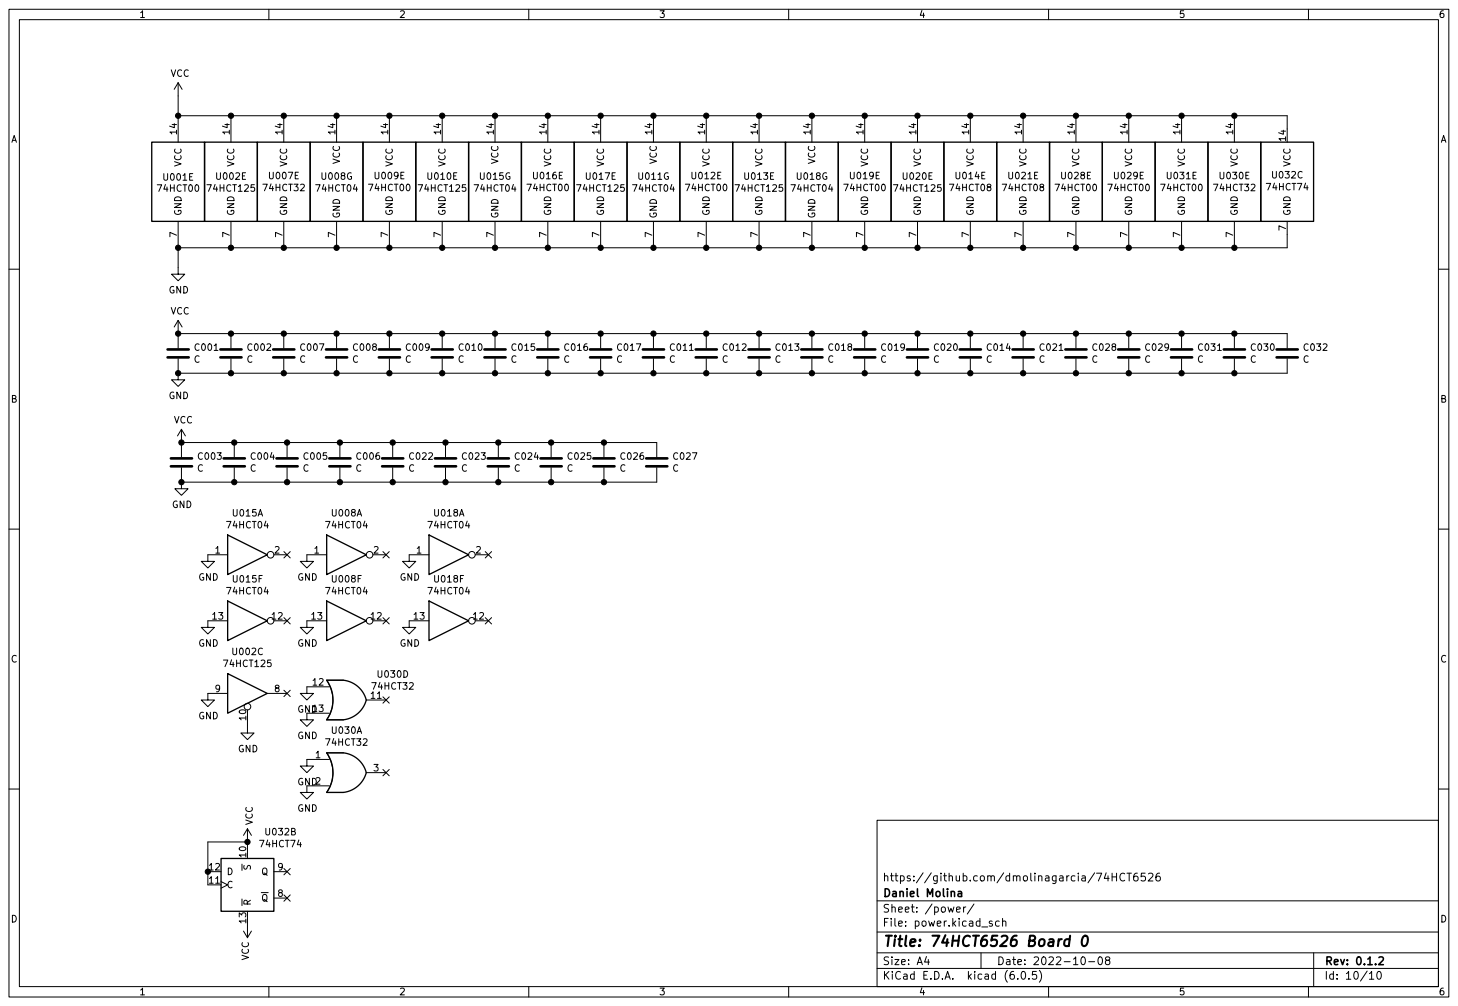
[picture p110: page 10]

https://github.com/dmolinagarcia/74HCT6526 GND

Sheet: /power/ Daniel Molina
