dmolinagarcia/74HCT6526/pdf/B1.sch.v0.1.0.pdf

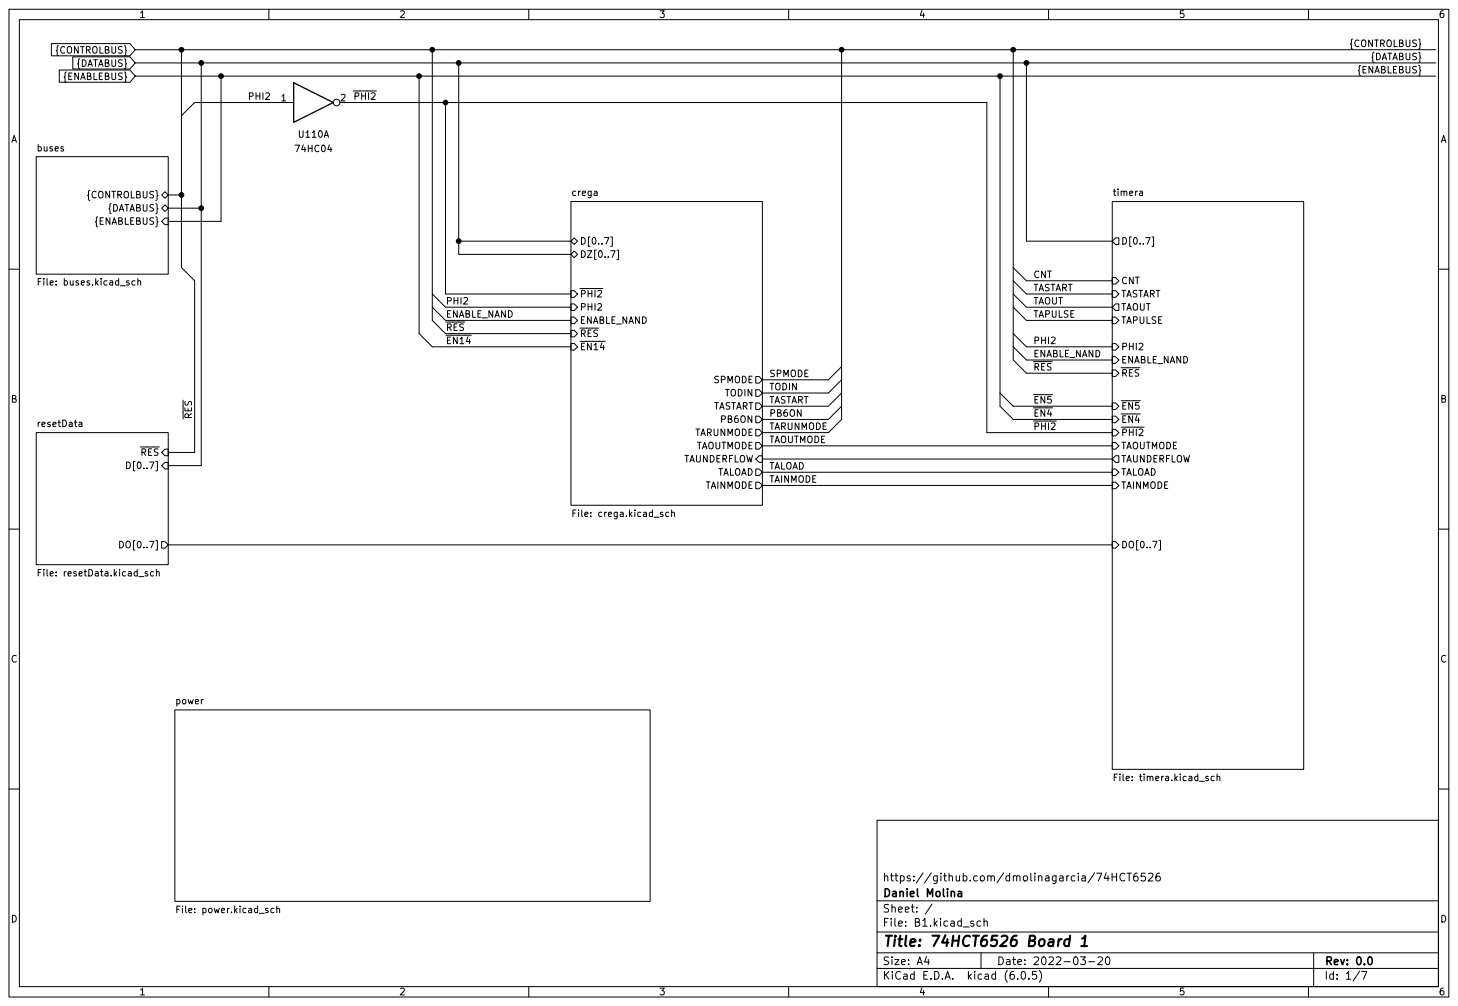
[picture p111: page 1]

{ENABLEBUS} buses File: buses.kicad_sch

timera File: timera.kicad_sch DO[0..7]
{DATABUS}

https://github.com/dmolinagarcia/74HCT6526
File: B1.kicad_sch Sheet: / Daniel Molina

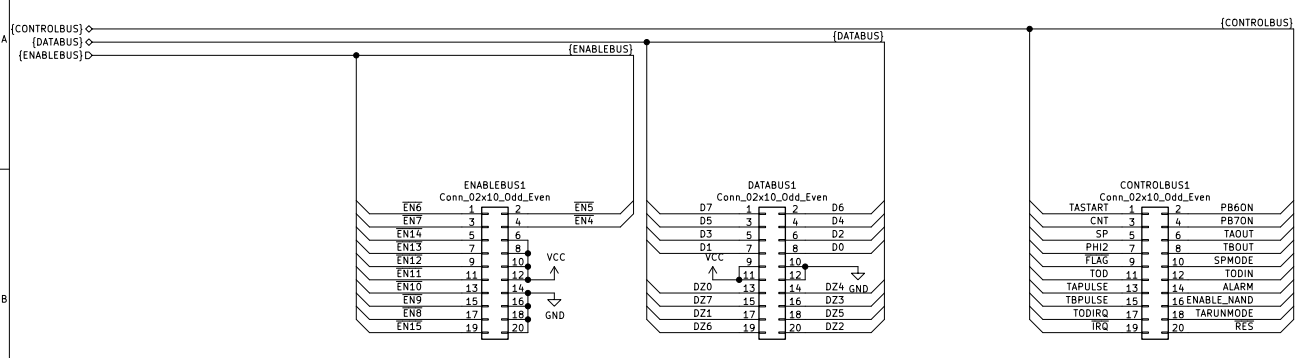
[picture p112: page 2]

https://github.com/dmolinagarcia/74HCT6526
File: buses.kicad_sch Sheet: /buses/ Daniel Molina

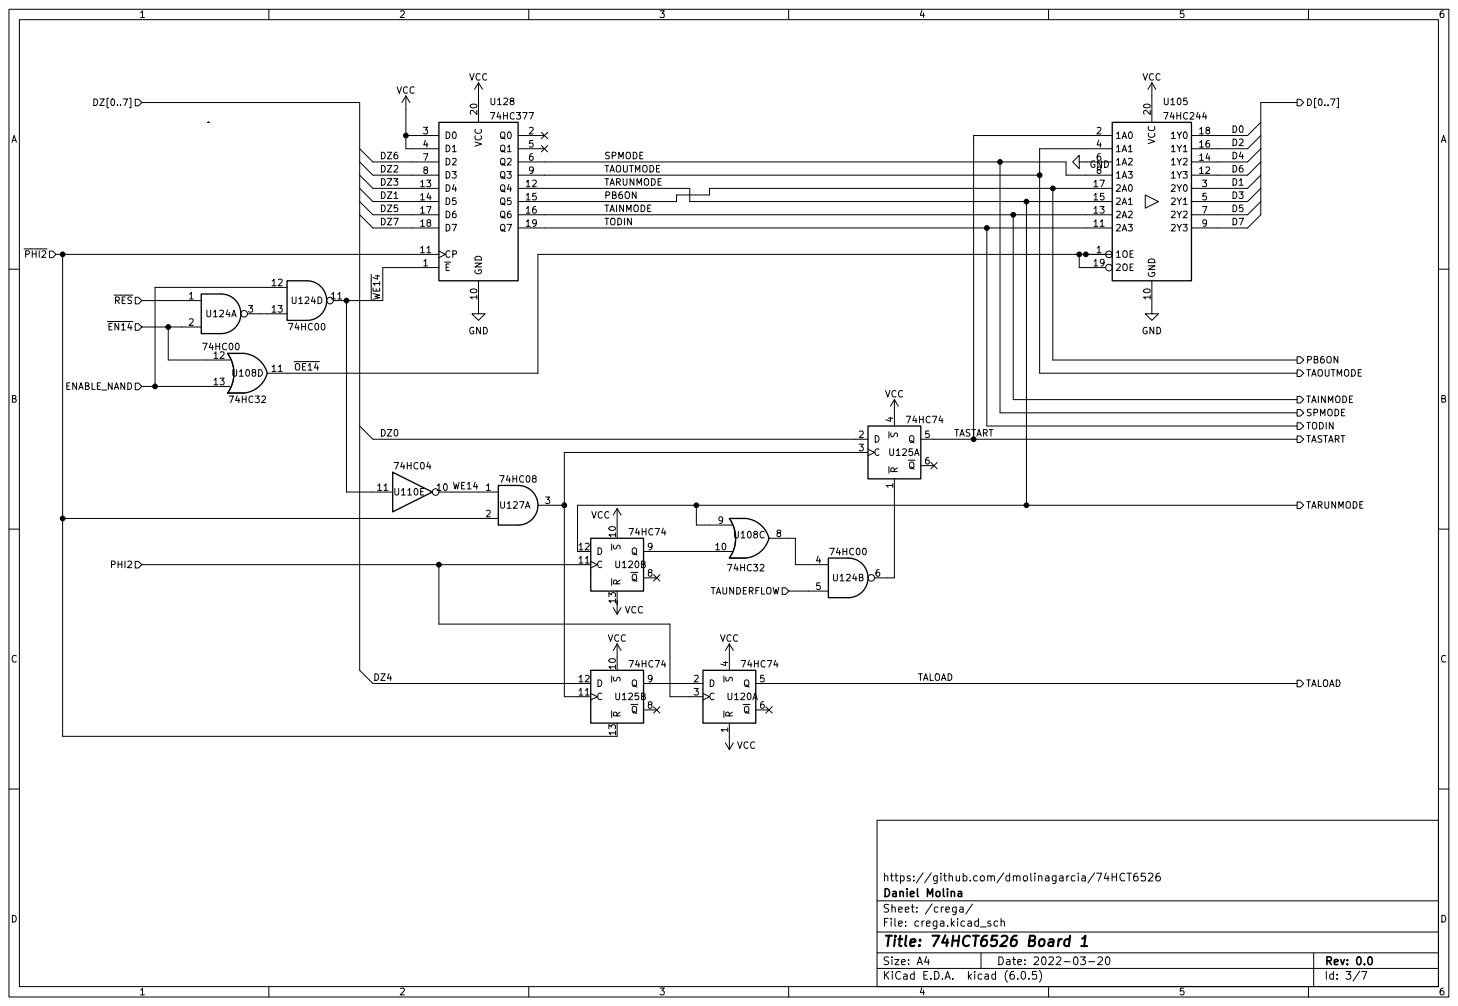
[picture p113: page 3]

1A1 4
1A2 6 1A3 8

https://github.com/dmolinagarcia/74HCT6526
Sheet: /crega/ Daniel Molina

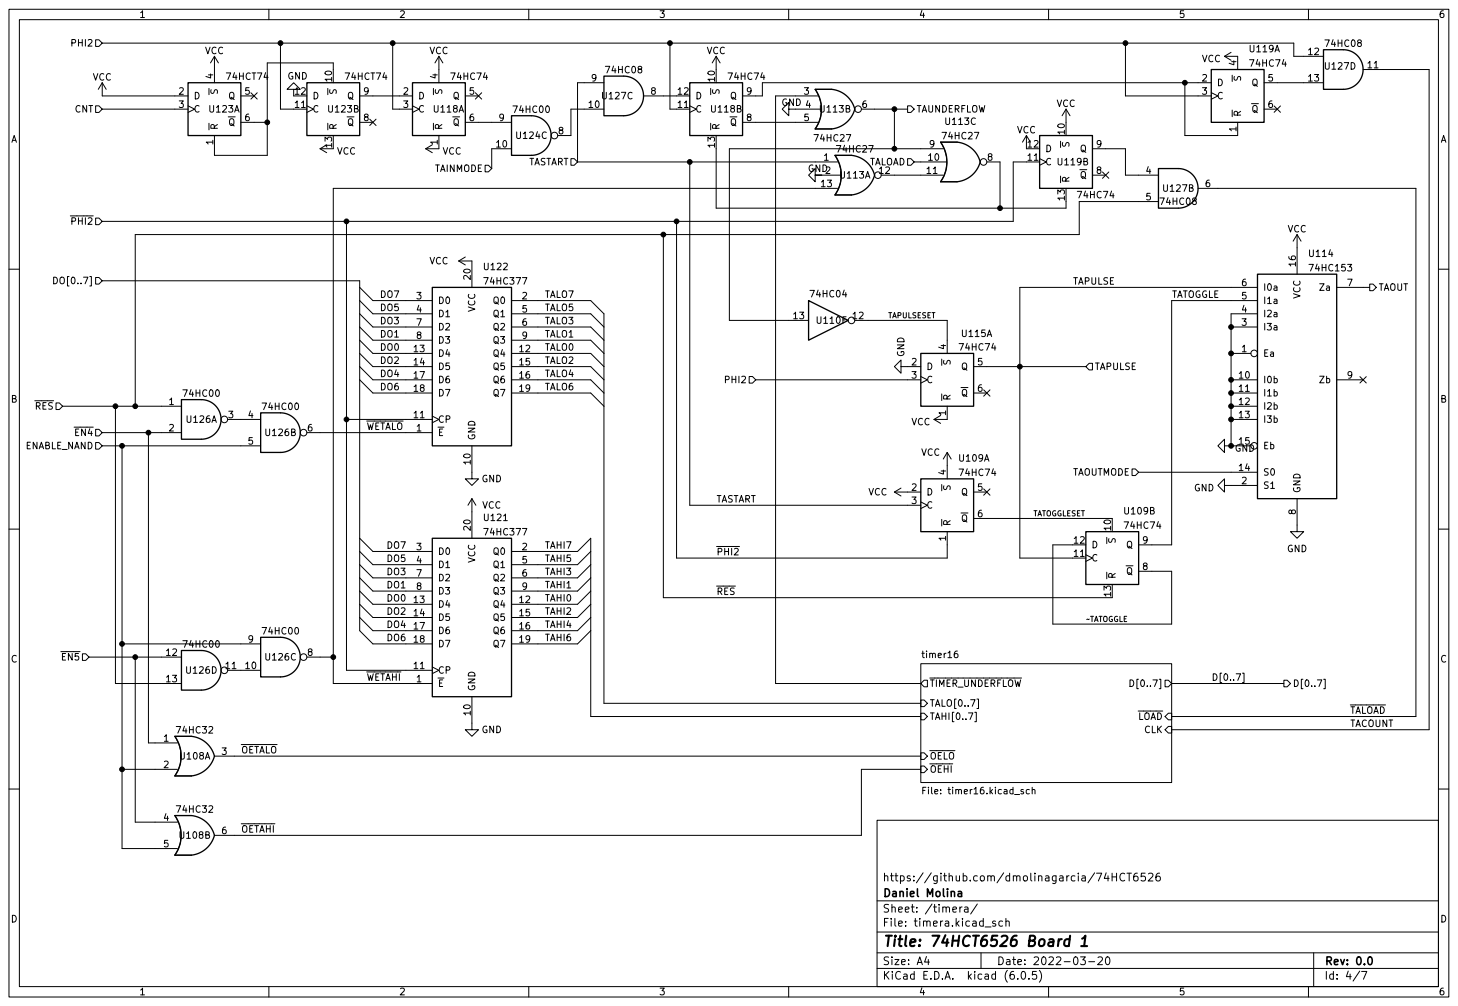
[picture p114: page 4]

File: timera.kicad_sch Sheet: /timera/ Daniel Molina

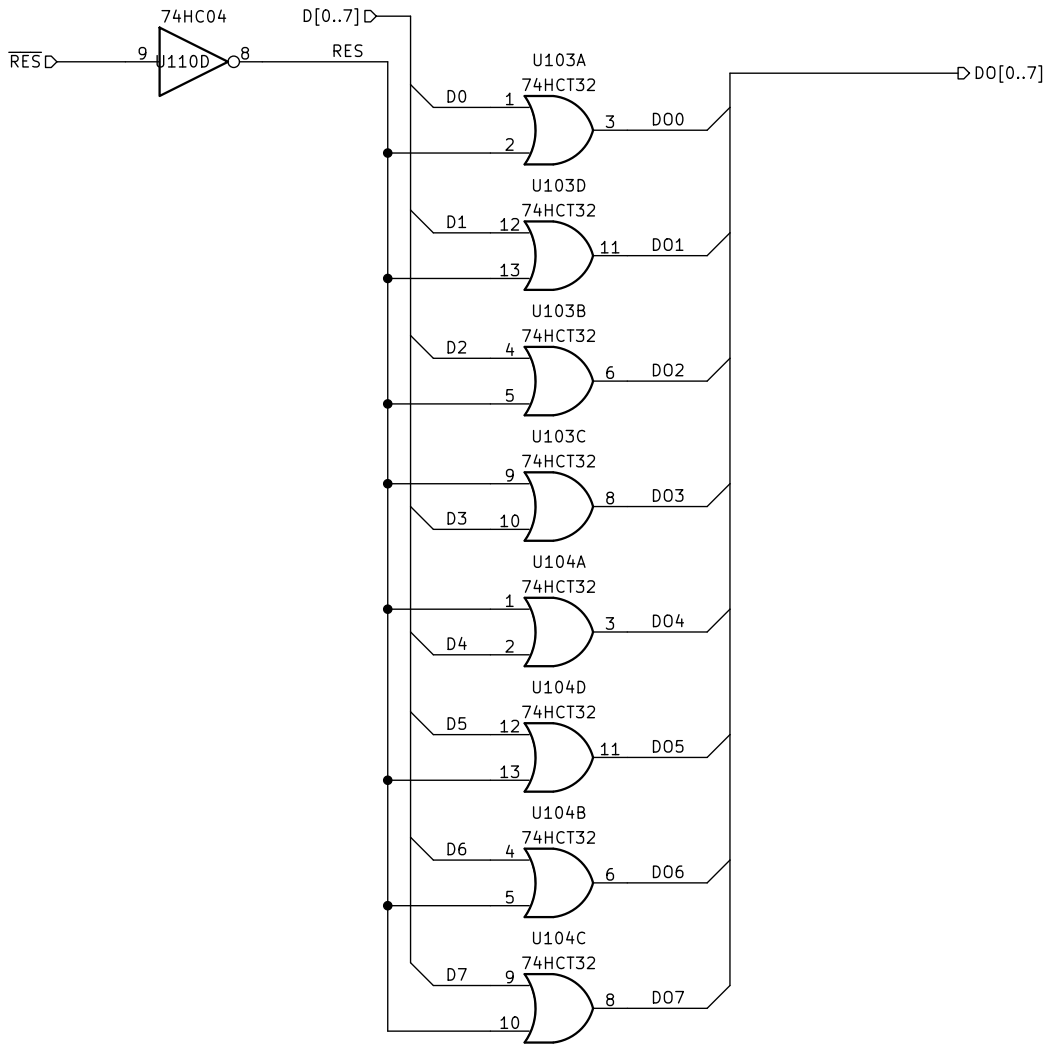
[picture p115: page 5]

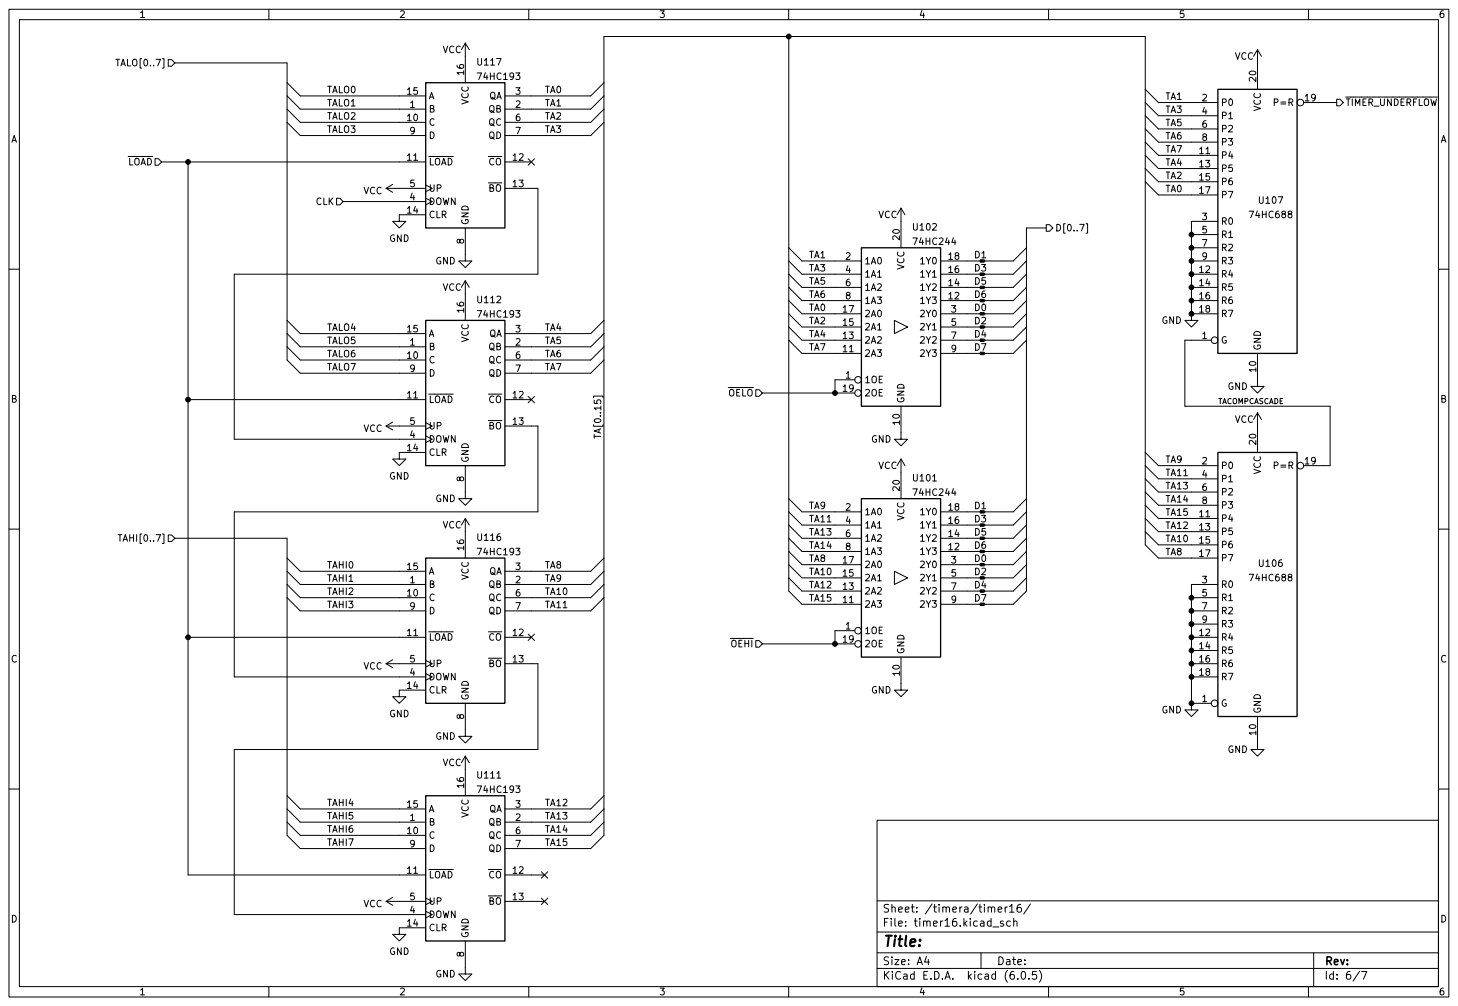
[picture p116: page 6]

File: timer16.kicad_sch Sheet: /timera/timer16/ VCC

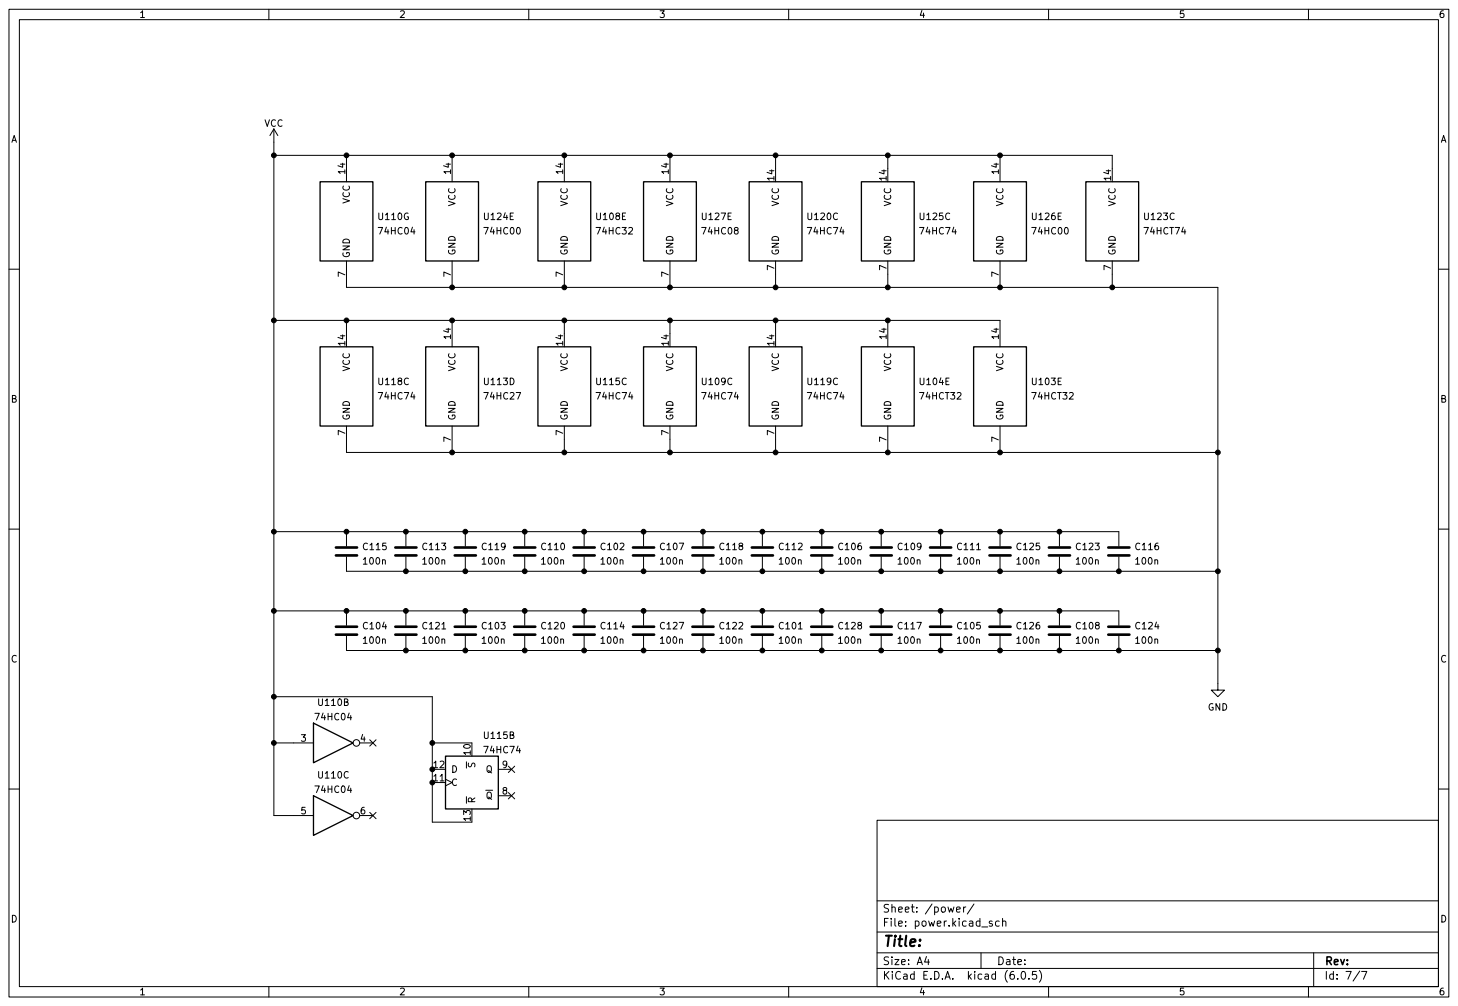
[picture p117: page 7]
