dmolinagarcia/74HCT6526/pdf/B1.sch.v0.1.1.pdf

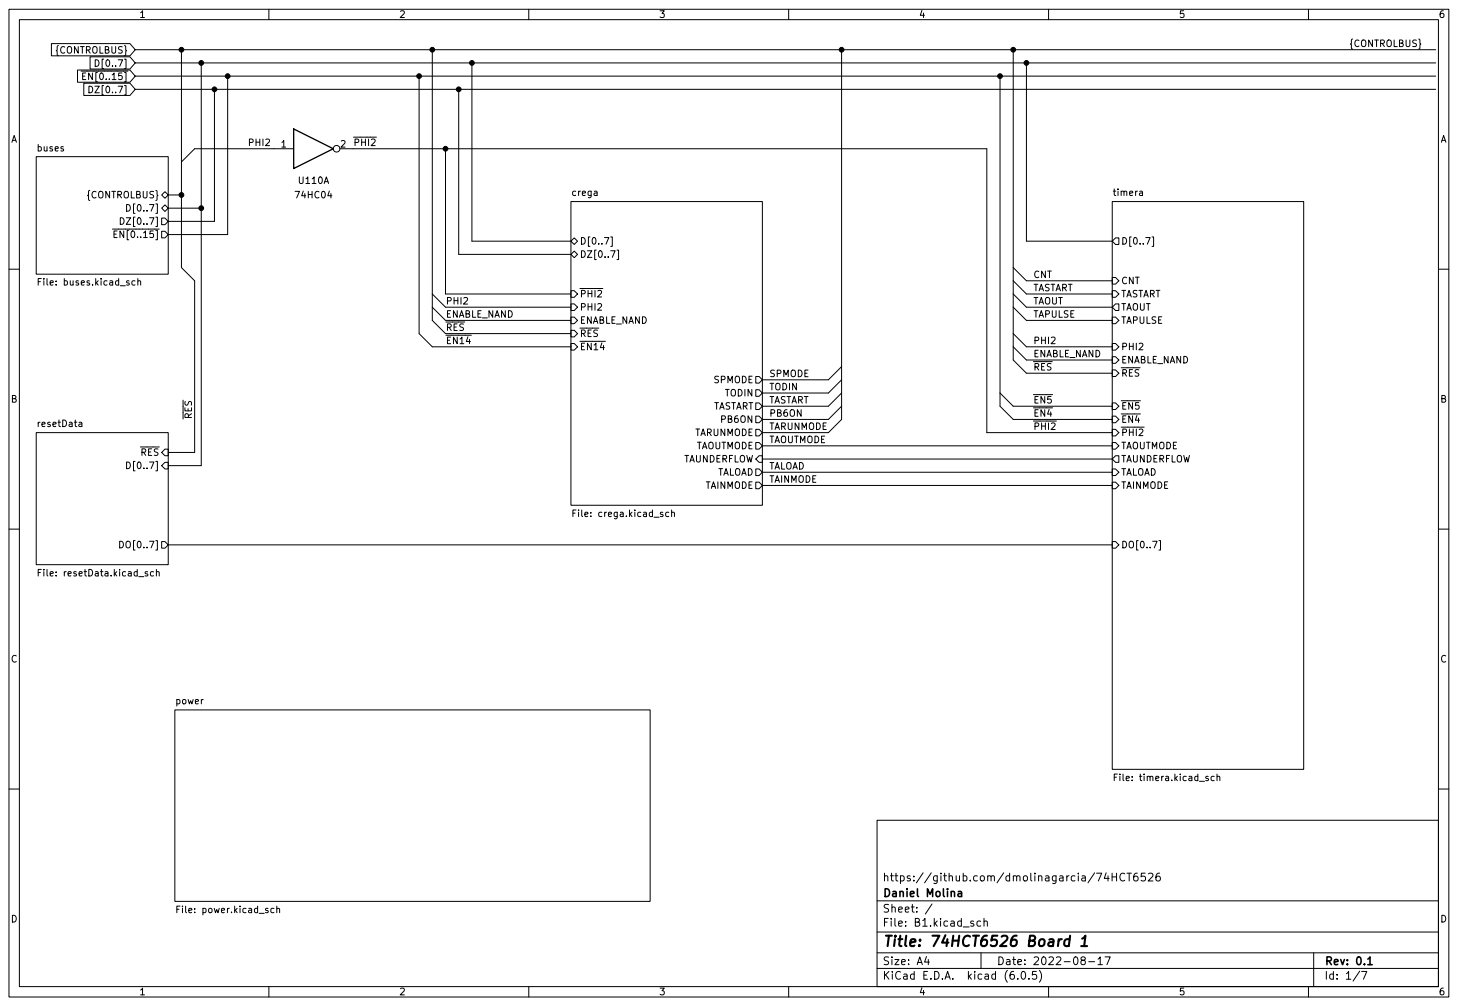
[picture p118: page 1]

~{EN[0..15]} buses File: buses.kicad_sch

https://github.com/dmolinagarcia/74HCT6526
File: B1.kicad_sch Sheet: / Daniel Molina

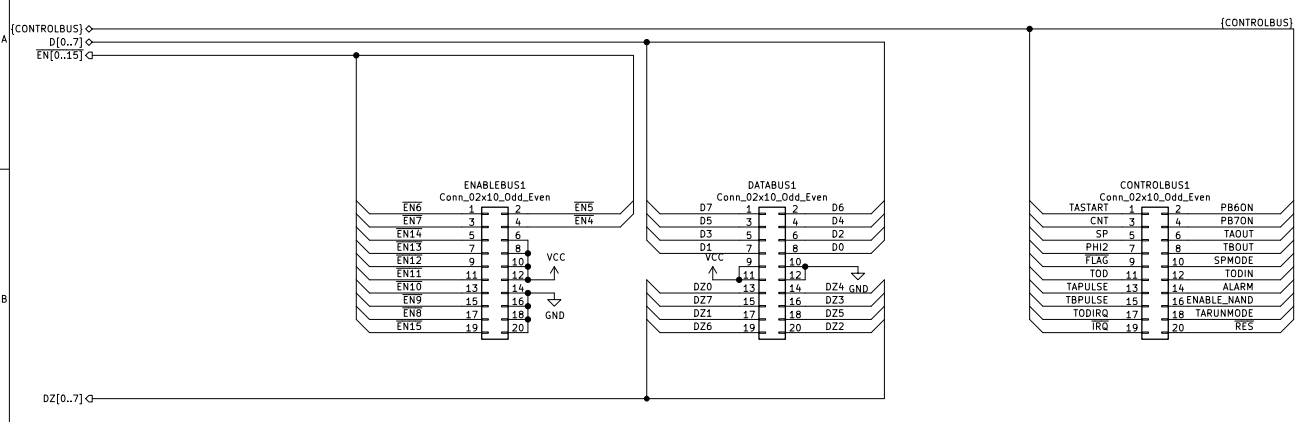
[picture p119: page 2]

https://github.com/dmolinagarcia/74HCT6526
File: buses.kicad_sch Sheet: /buses/ Daniel Molina

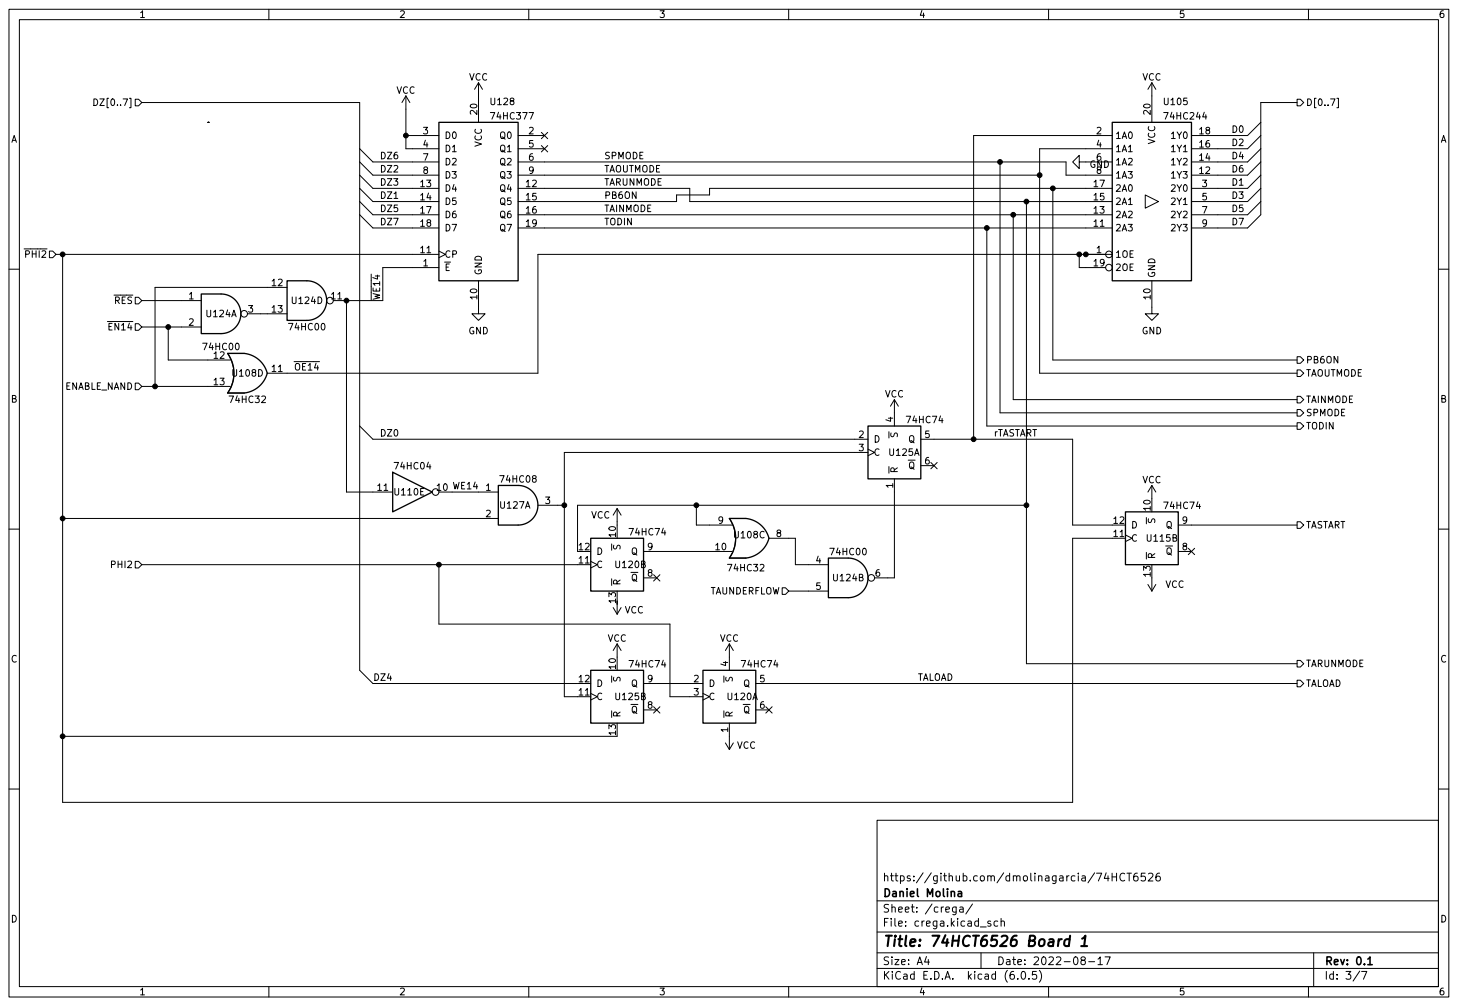
[picture p120: page 3]

TAOUTMODE | D4 DZ7 D6 D2 TODIN

1A1 4
1A2 6 1A3 8

https://github.com/dmolinagarcia/74HCT6526
Sheet: /crega/ Daniel Molina

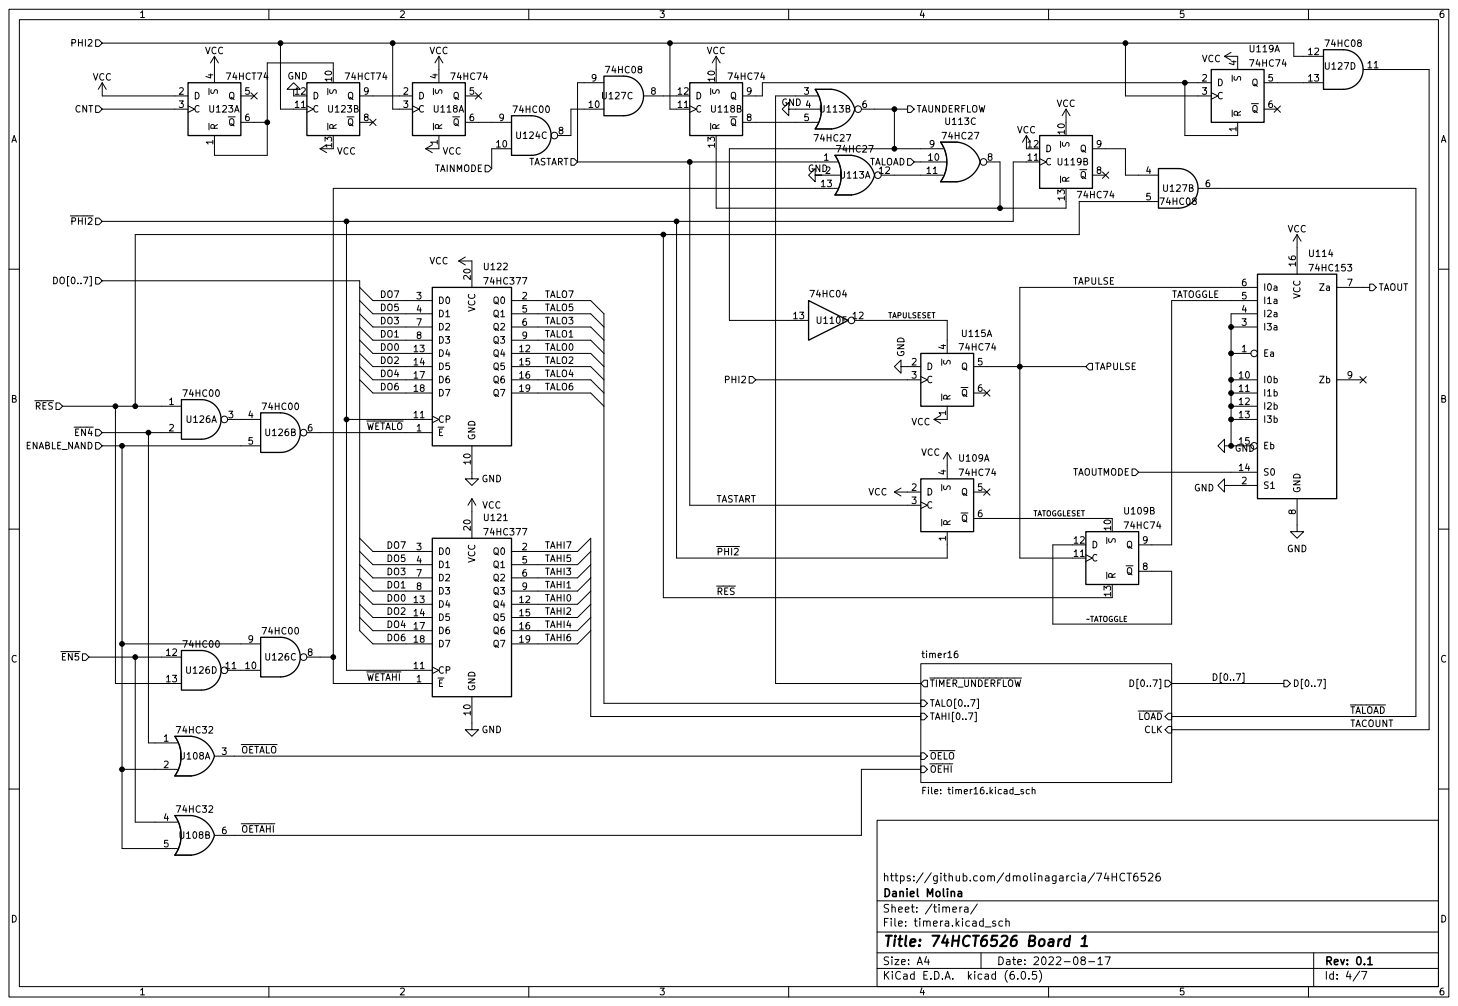
[picture p121: page 4]

File: timera.kicad_sch Sheet: /timera/ Daniel Molina


https://github.com/dmolinagarcia/74HCT6526
File: resetData.kicad_sch Sheet: /resetData/ Daniel Molina

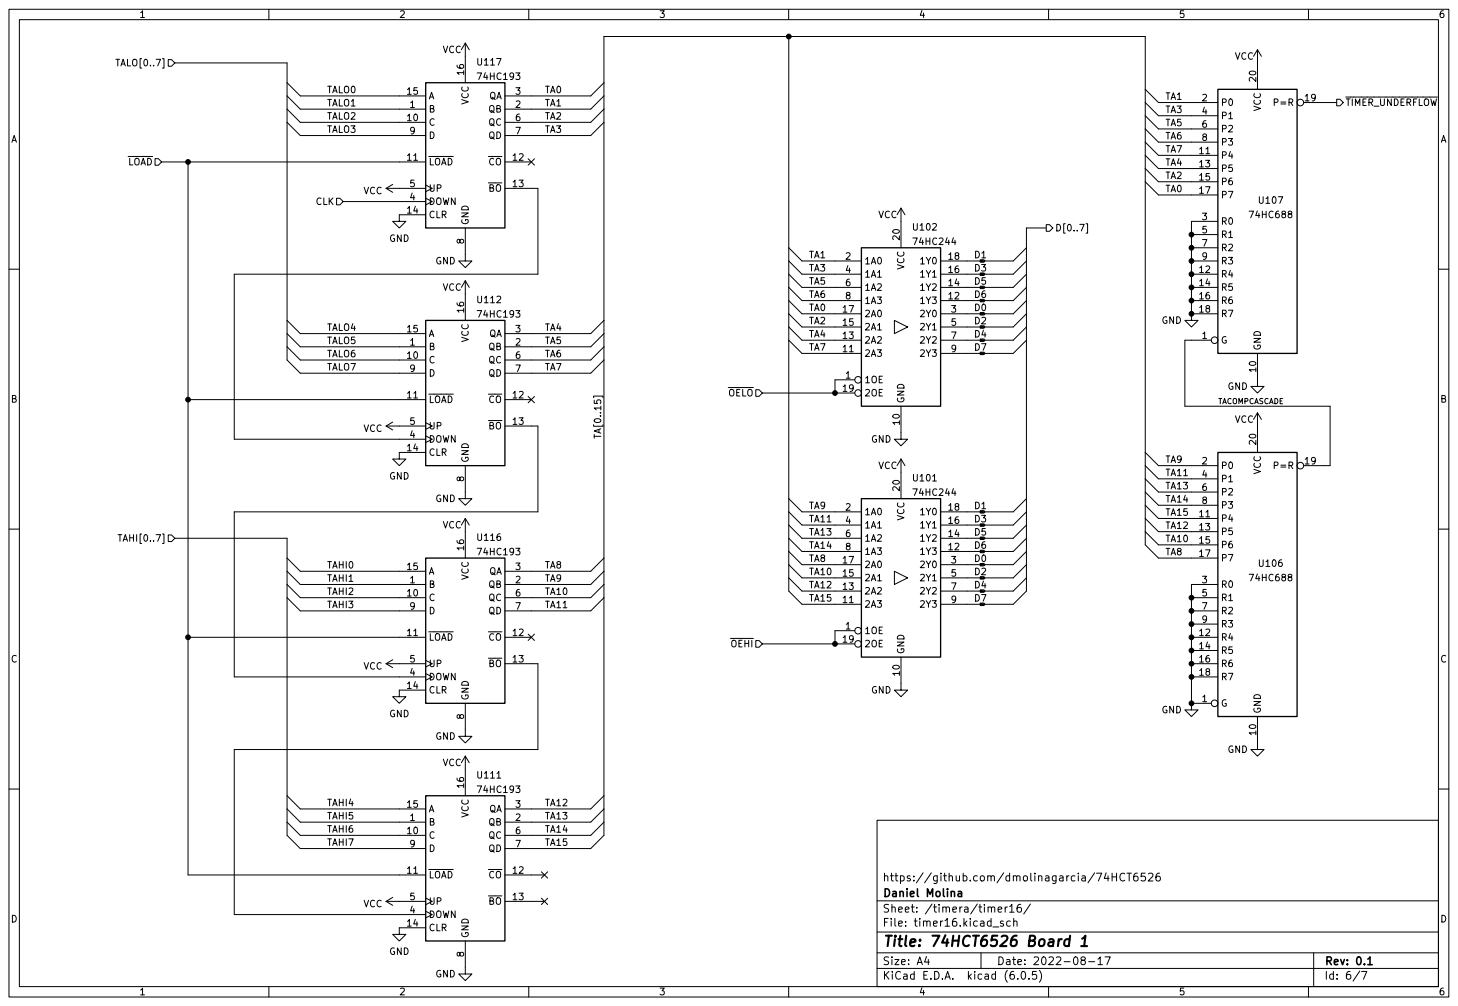
[picture p122: page 6]

https://github.com/dmolinagarcia/74HCT6526 VCC

File: timer16.kicad_sch Sheet: /timera/timer16/ Daniel Molina

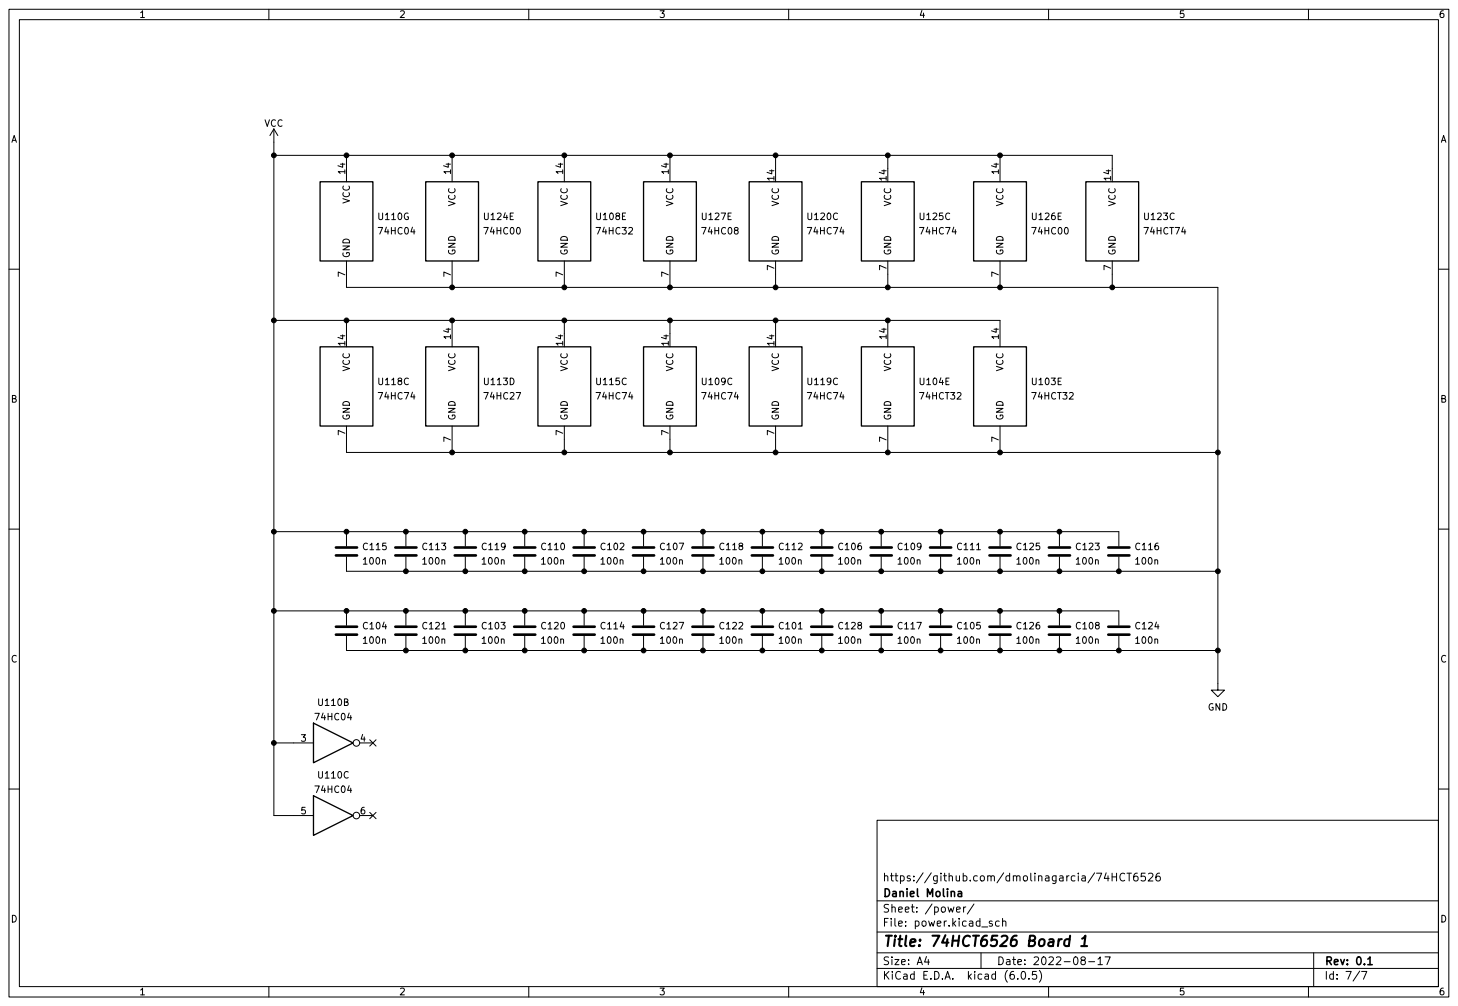
[picture p123: page 7]

C125 | 100n VCC 14 GND

74HC74 | 100n VCC 14 GND 74HCT32 C111 | 100n VCC 14 GND

https://github.com/dmolinagarcia/74HCT6526 C109

Sheet: /power/ Daniel Molina
