dmolinagarcia/74HCT6526/pdf/B2.sch.v0.1.1.pdf

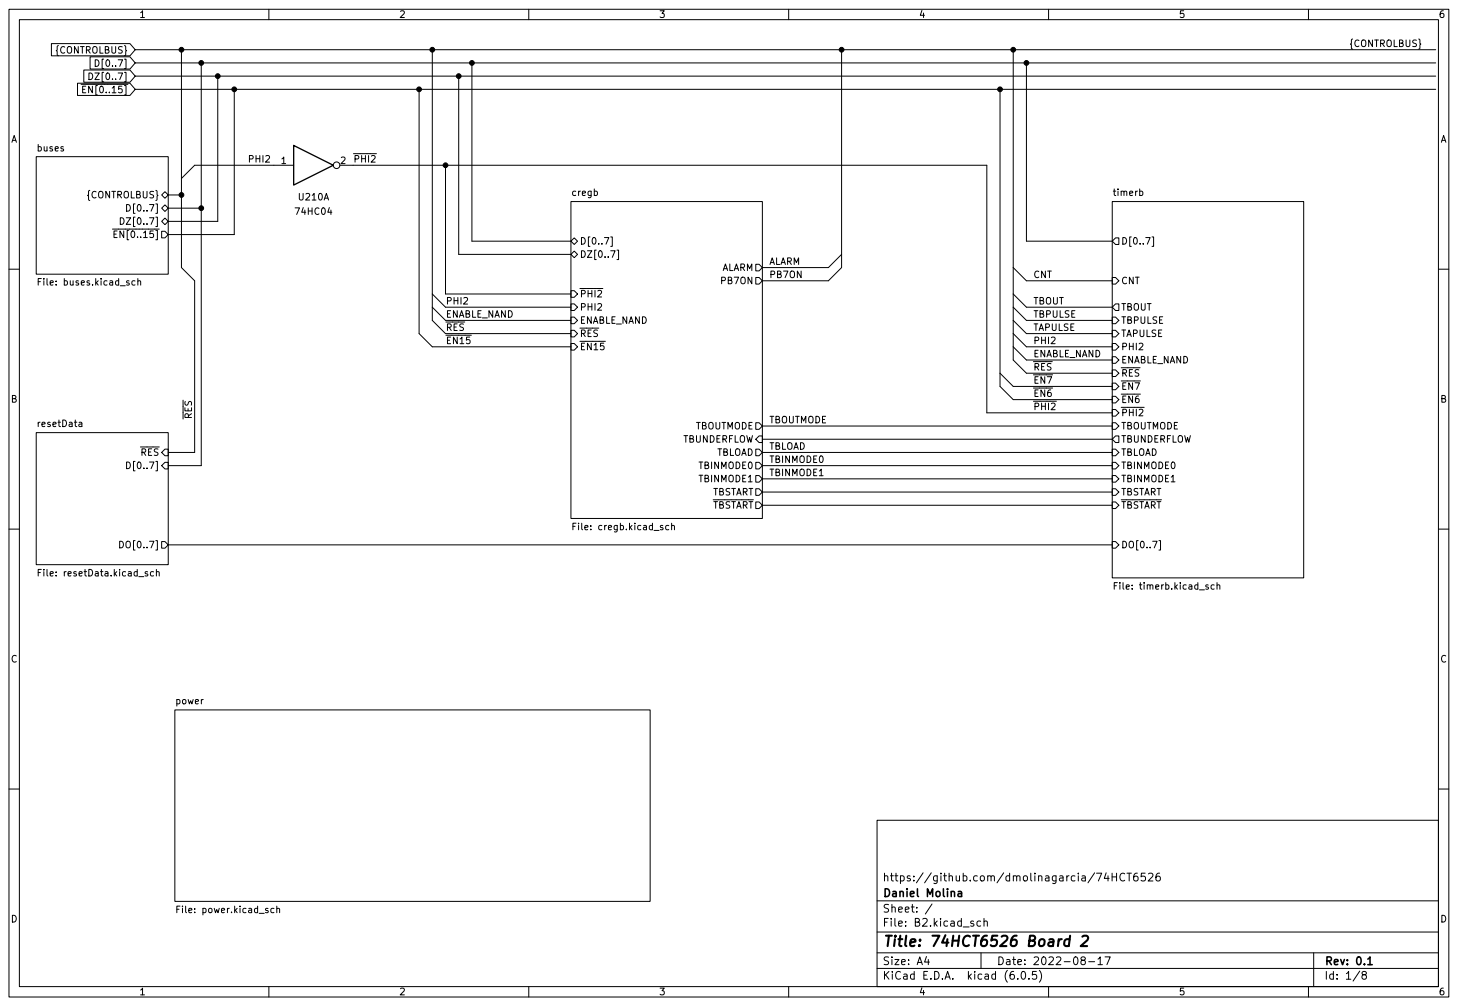
[picture p130: page 1]

~{EN[0..15]} buses File: buses.kicad_schDO[0..7]

timerb File: timerb.kicad_sch DZ[0..7]
TBINMODE0 ALARM

https://github.com/dmolinagarcia/74HCT6526
File: B2.kicad_sch Sheet: / Daniel Molina

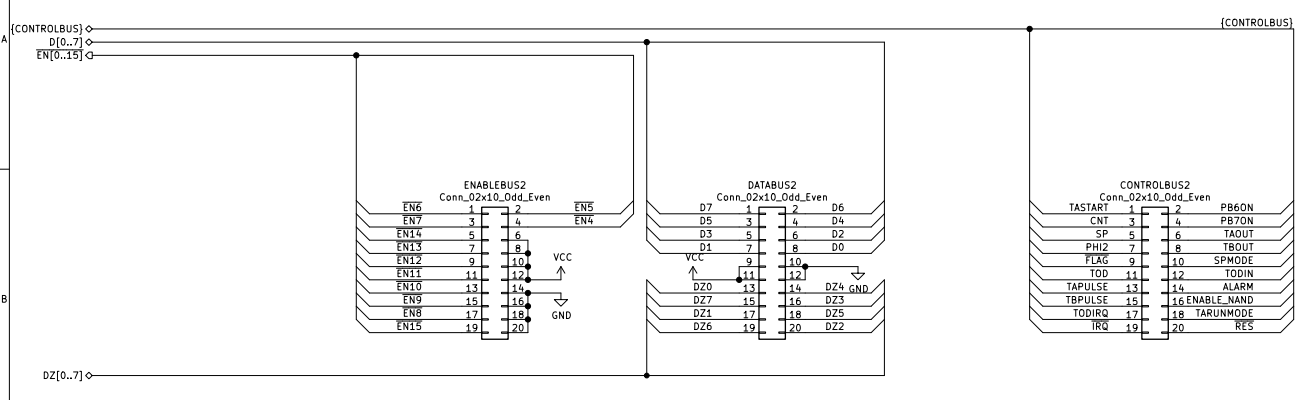
[picture p131: page 2]

https://github.com/dmolinagarcia/74HCT6526
File: buses.kicad_sch Sheet: /buses/ Daniel Molina

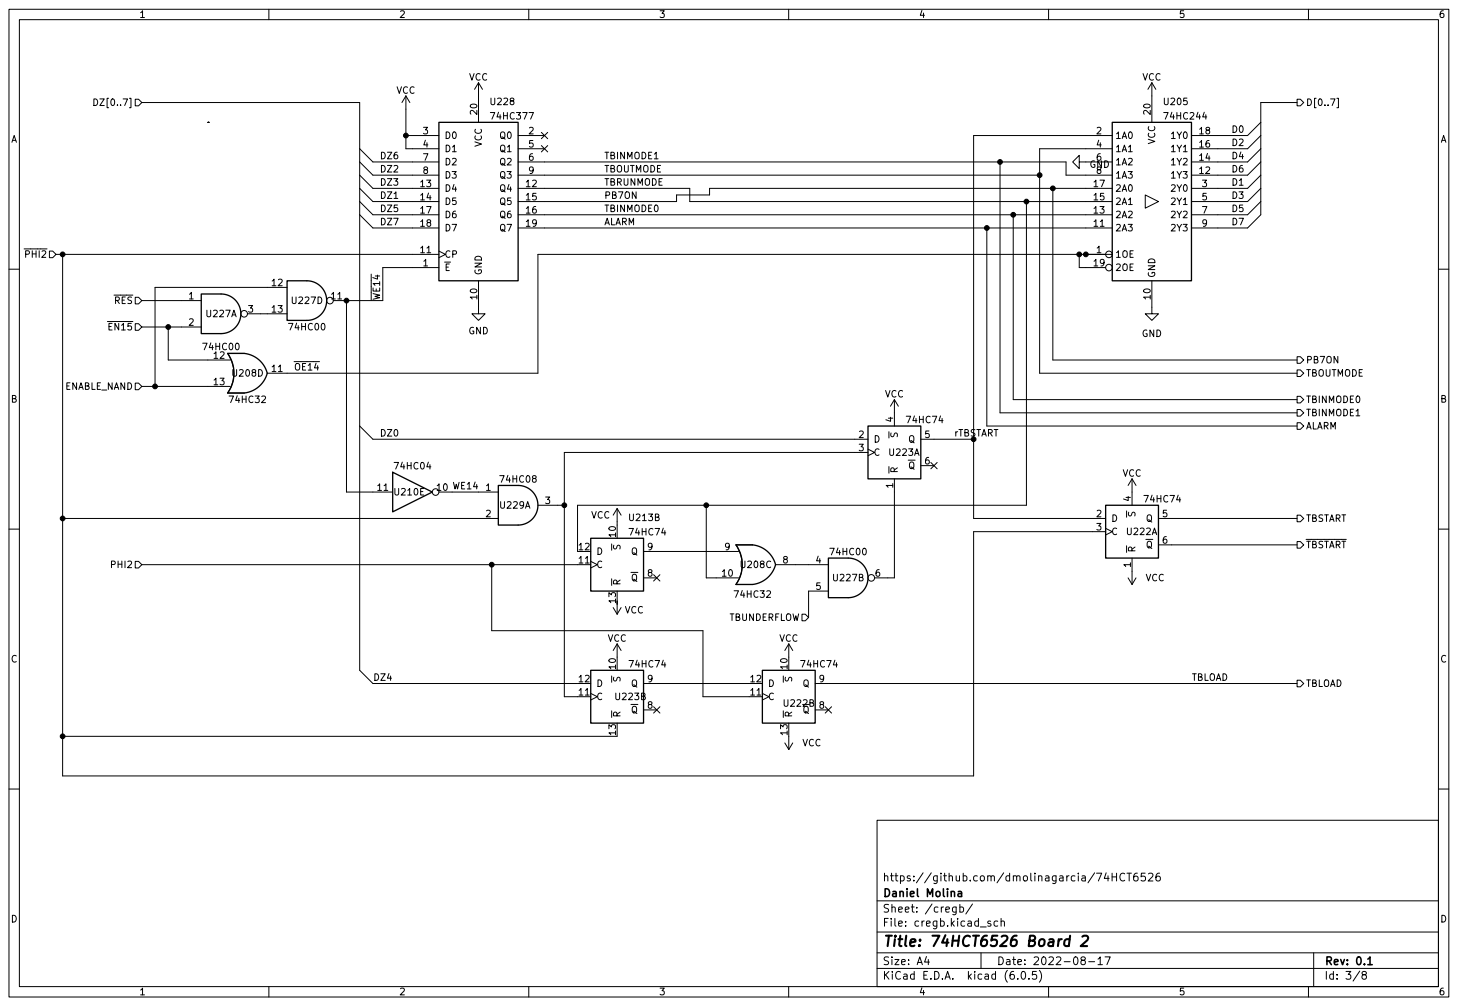
[picture p132: page 3]

1A1 4
1A2 6 1A3 8

TBRUNMODE | | 2A0 17

https://github.com/dmolinagarcia/74HCT6526
Sheet: /cregb/ Daniel Molina

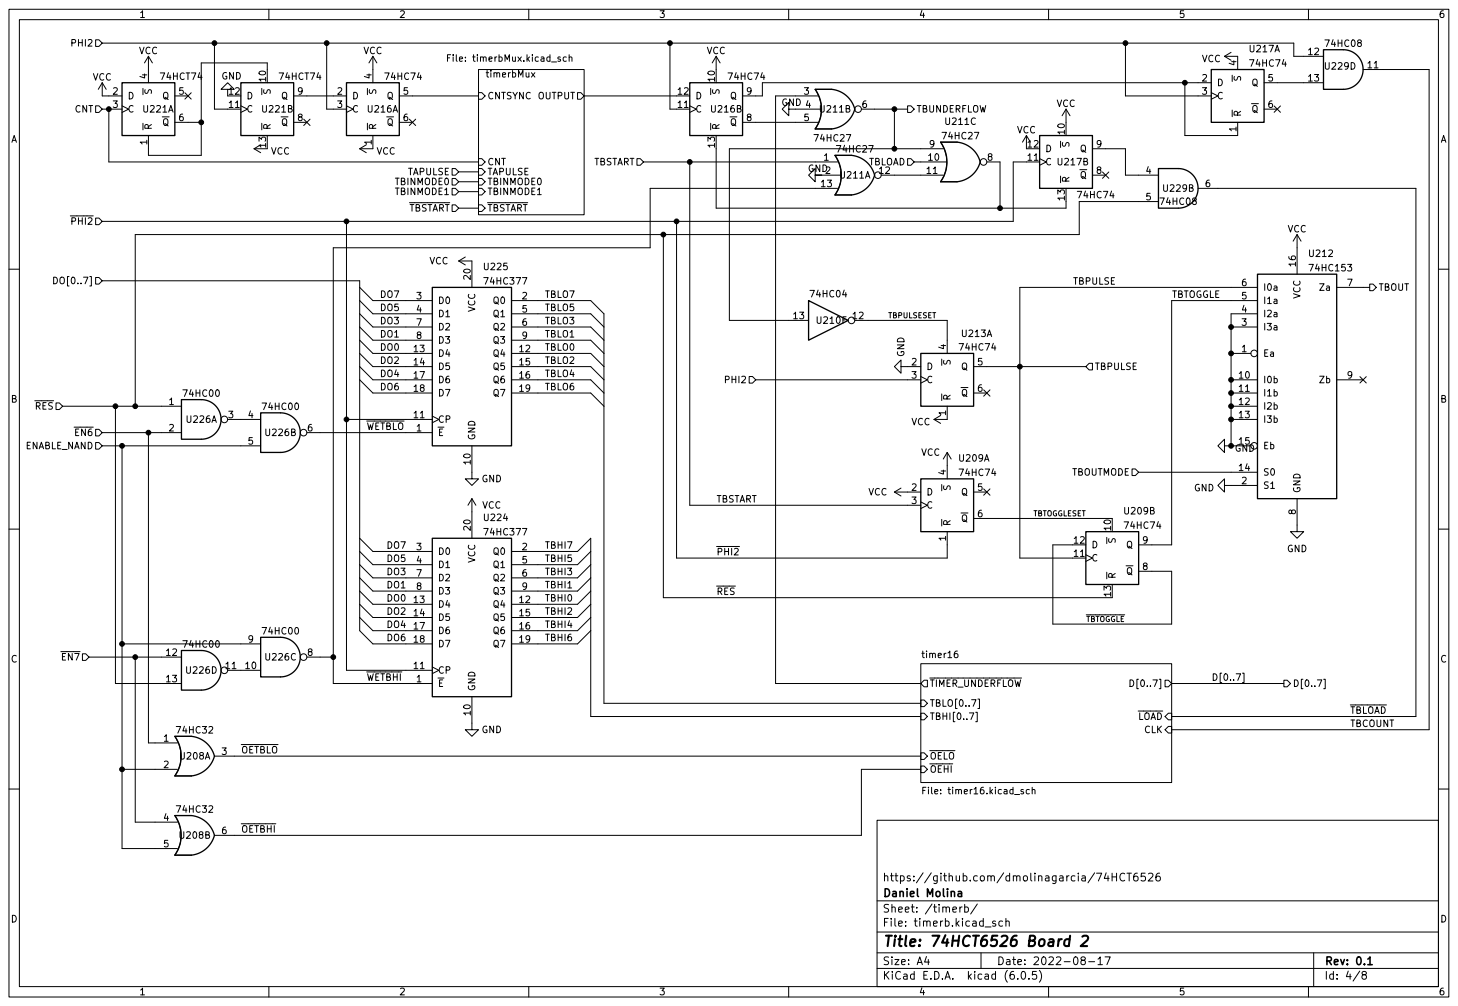
[picture p133: page 4]

https://github.com/dmolinagarcia/74HCT6526
File: timerb.kicad_sch Sheet: /timerb/ Daniel Molina

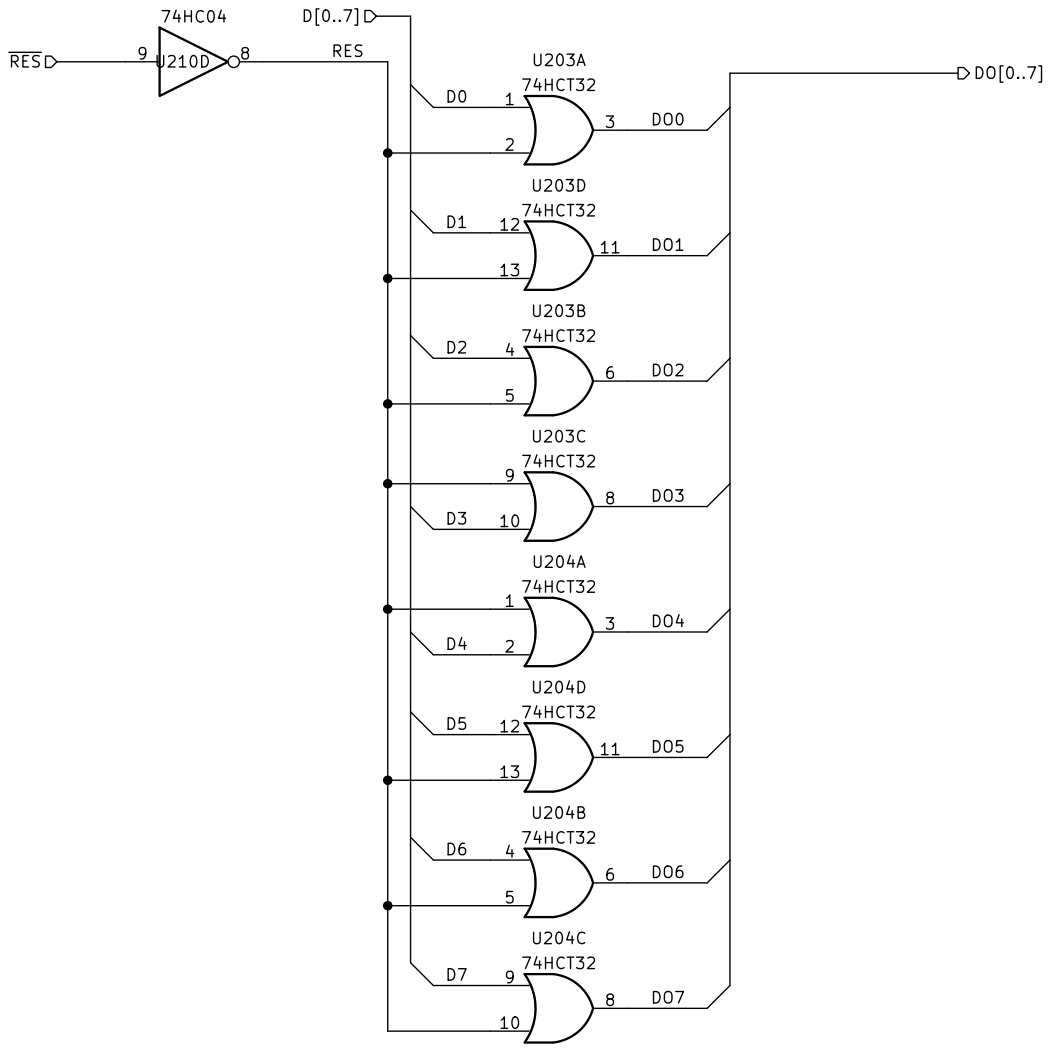
[picture p134: page 5]

https://github.com/dmolinagarcia/74HCT6526
File: resetData.kicad_sch Sheet: /resetData/ Daniel Molina

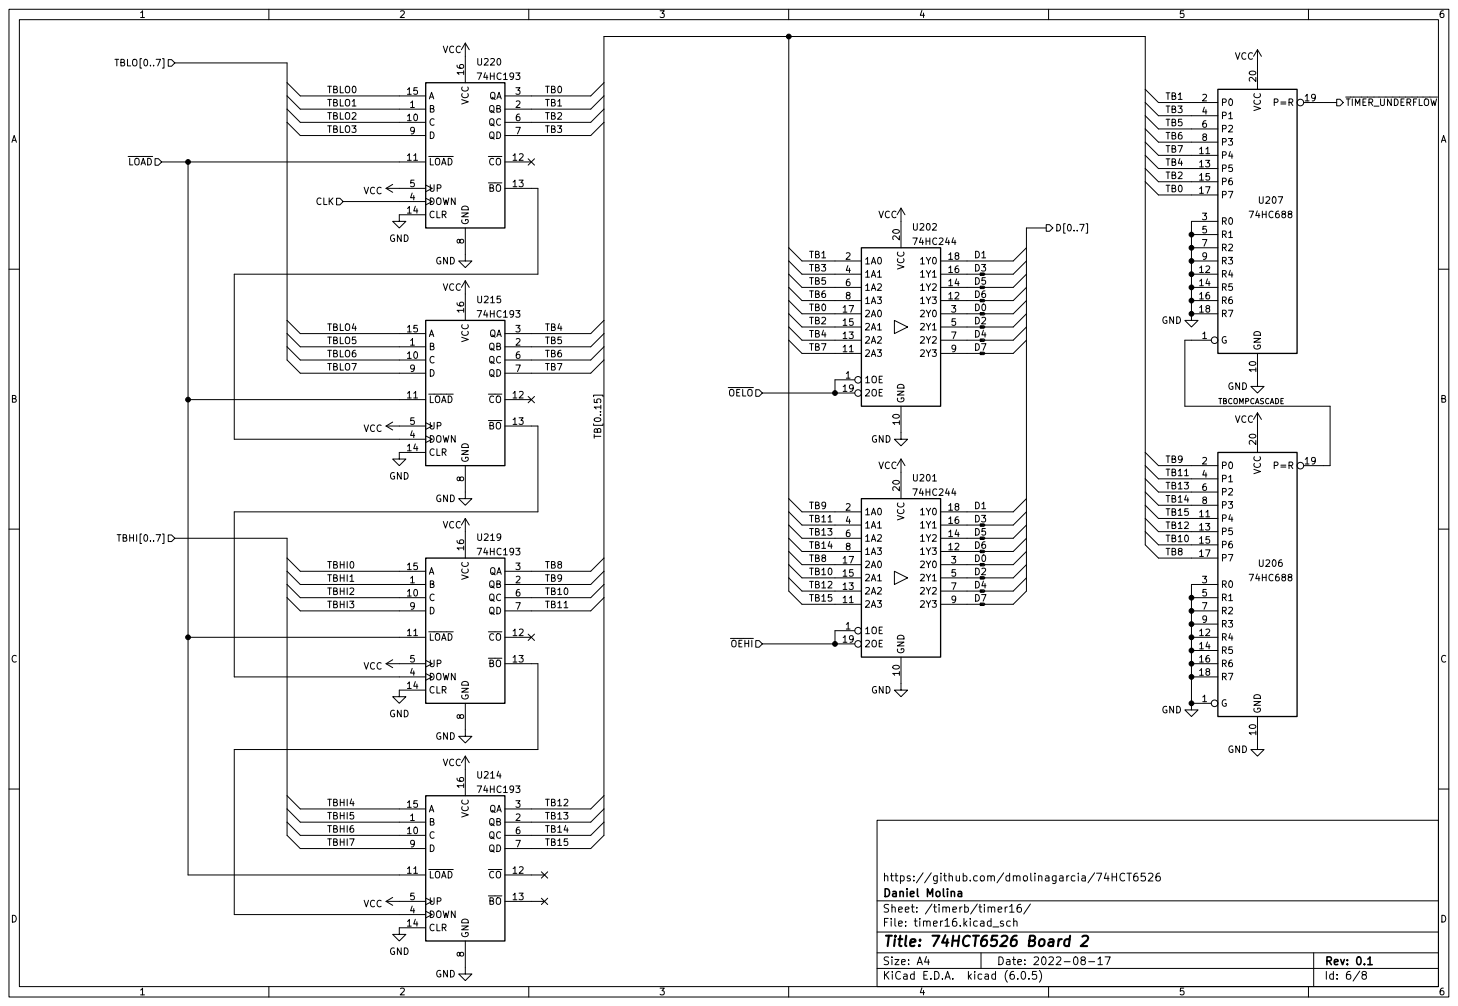
[picture p135: page 6]

https://github.com/dmolinagarcia/74HCT6526 VCC

File: timer16.kicad_sch Sheet: /timerb/timer16/ Daniel Molina

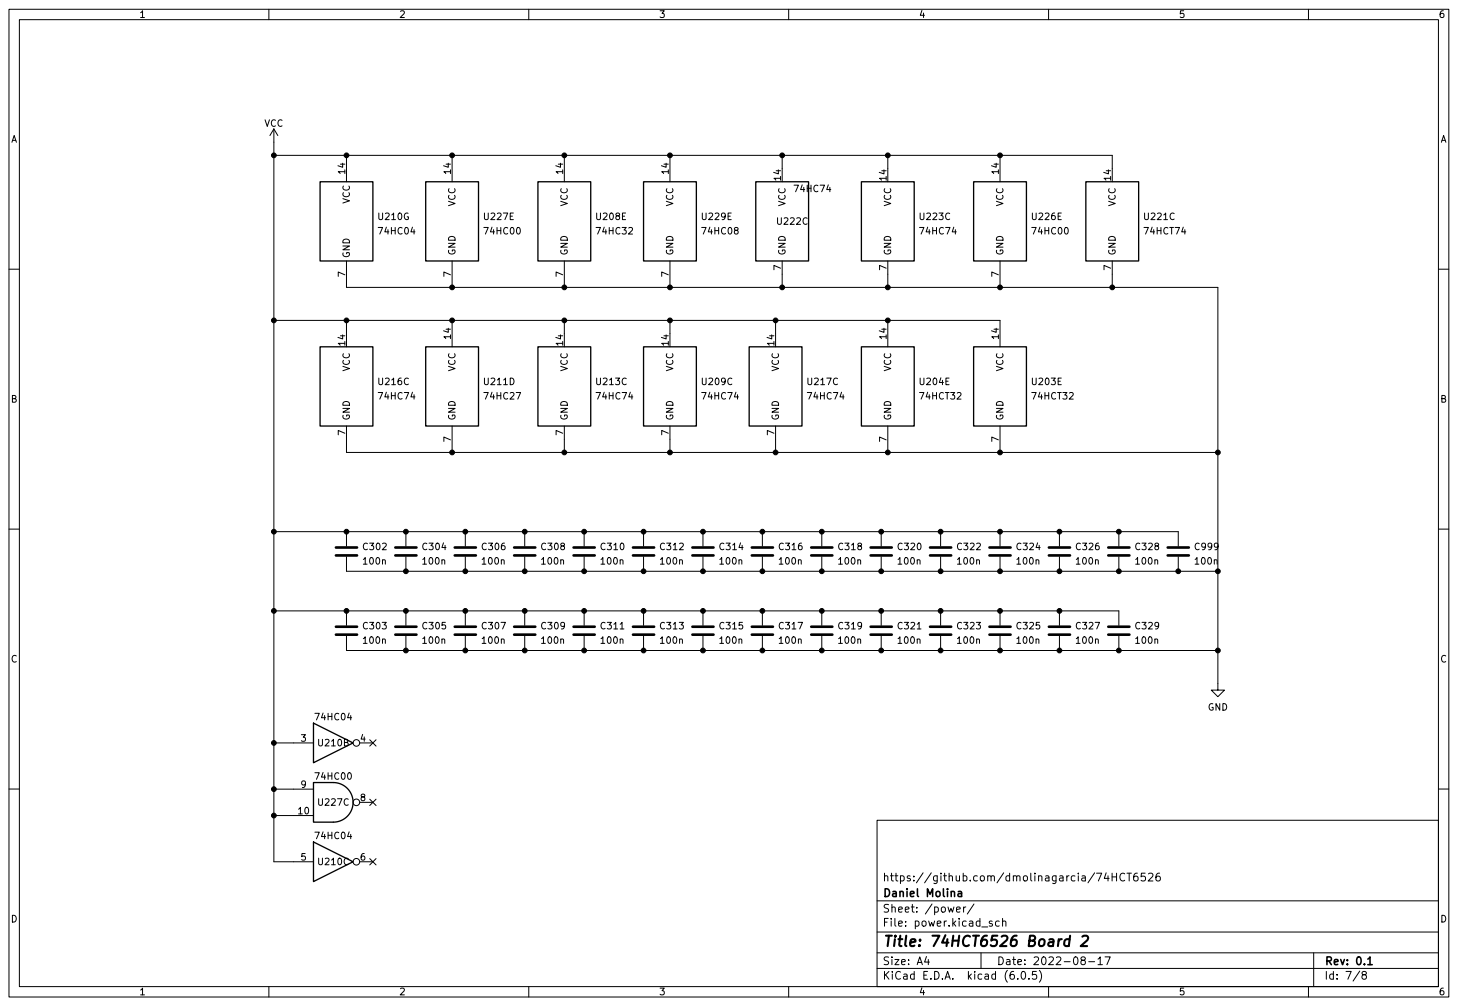
[picture p136: page 7]

Sheet: /power/ Daniel Molina

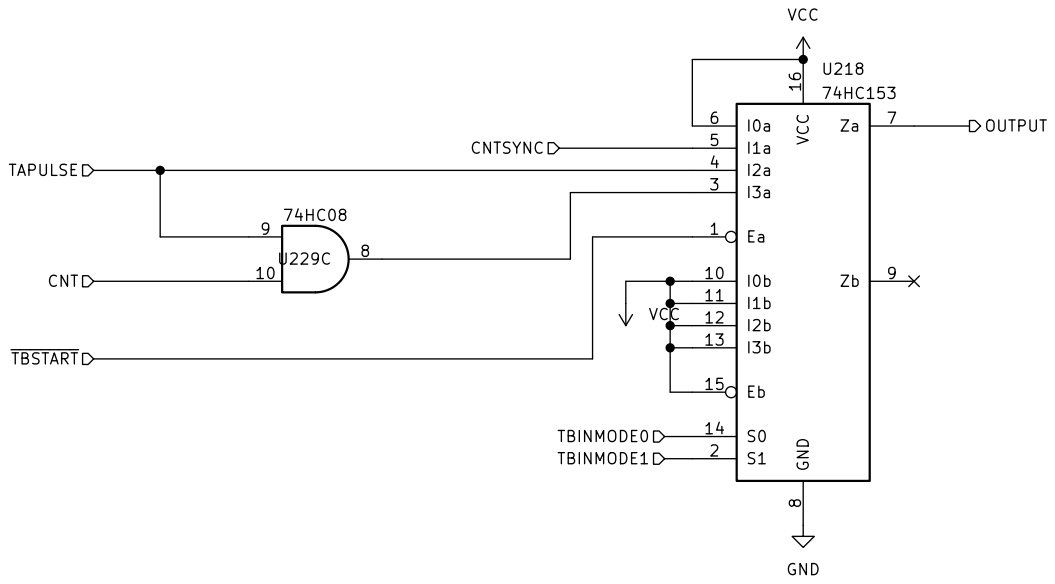
[picture p137: page 8]

https://github.com/dmolinagarcia/74HCT6526
File: timerbMux.kicad_sch Sheet: /timerb/timerbMux/ Daniel Molina
