dmolinagarcia/74HCT6526/pdf/B3.sch.v0.1.2.pdf

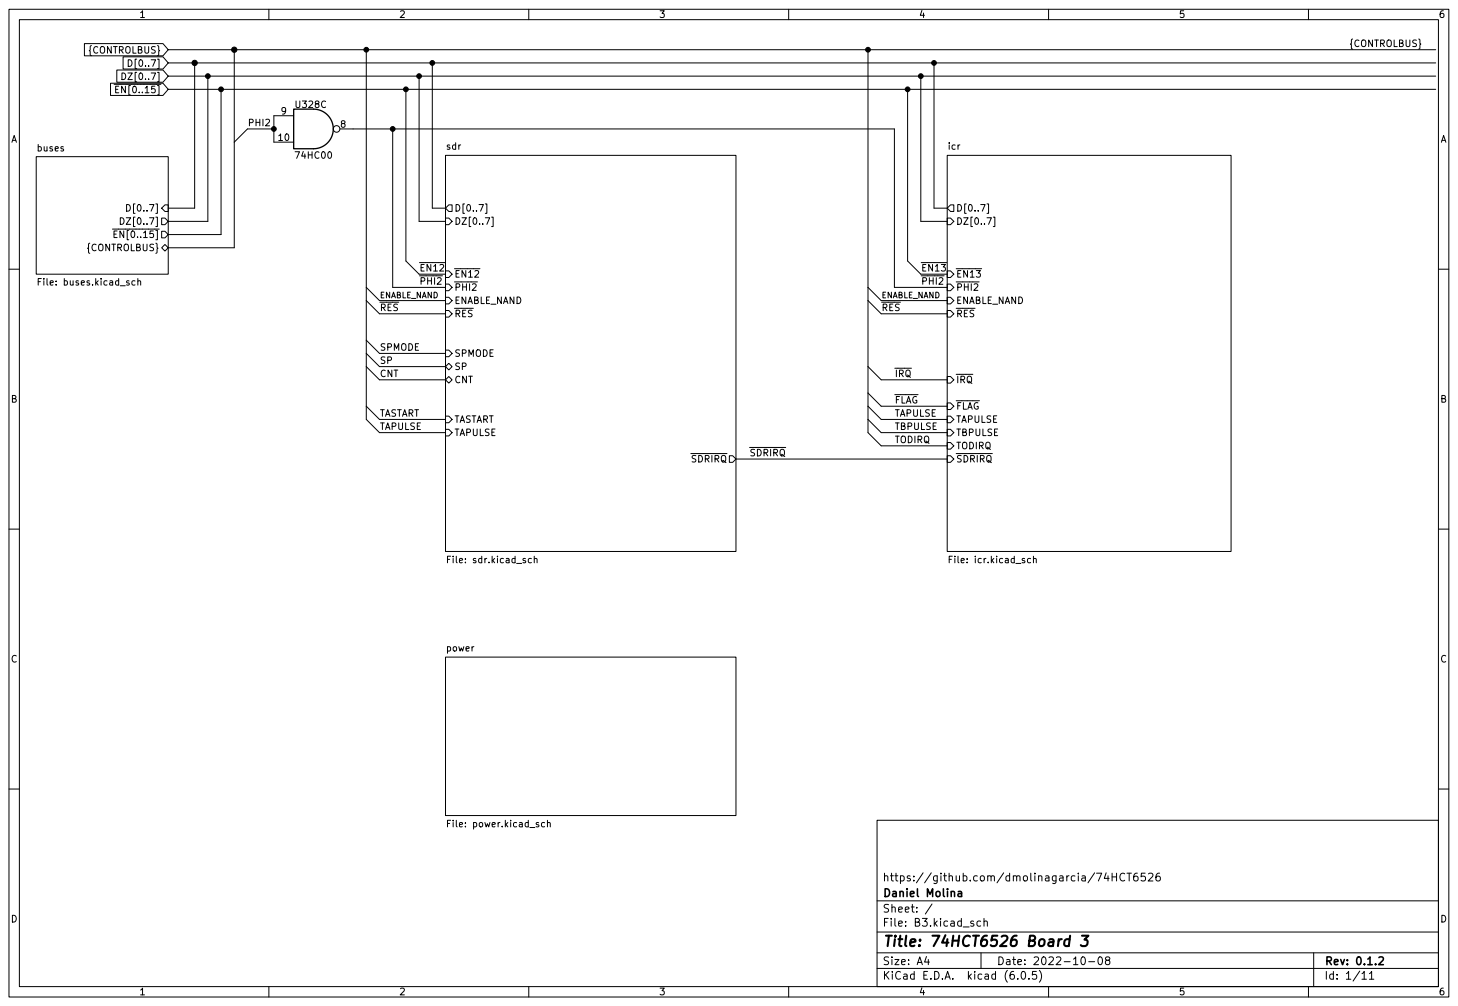
[picture p145: page 1]

https://github.com/dmolinagarcia/74HCT6526
File: B3.kicad_sch Sheet: / Daniel Molina

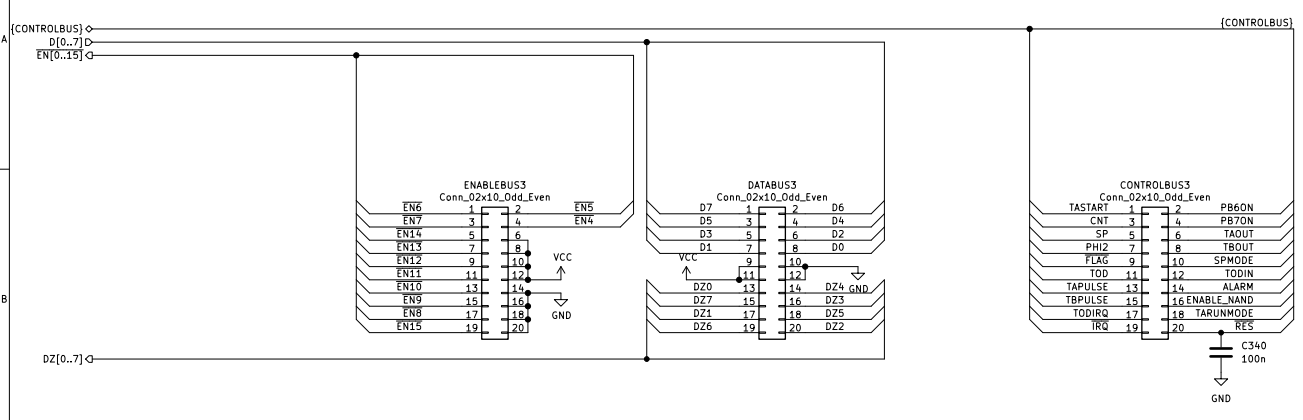
[picture p146: page 2]

https://github.com/dmolinagarcia/74HCT6526
File: buses.kicad_sch Sheet: /buses/ Daniel Molina

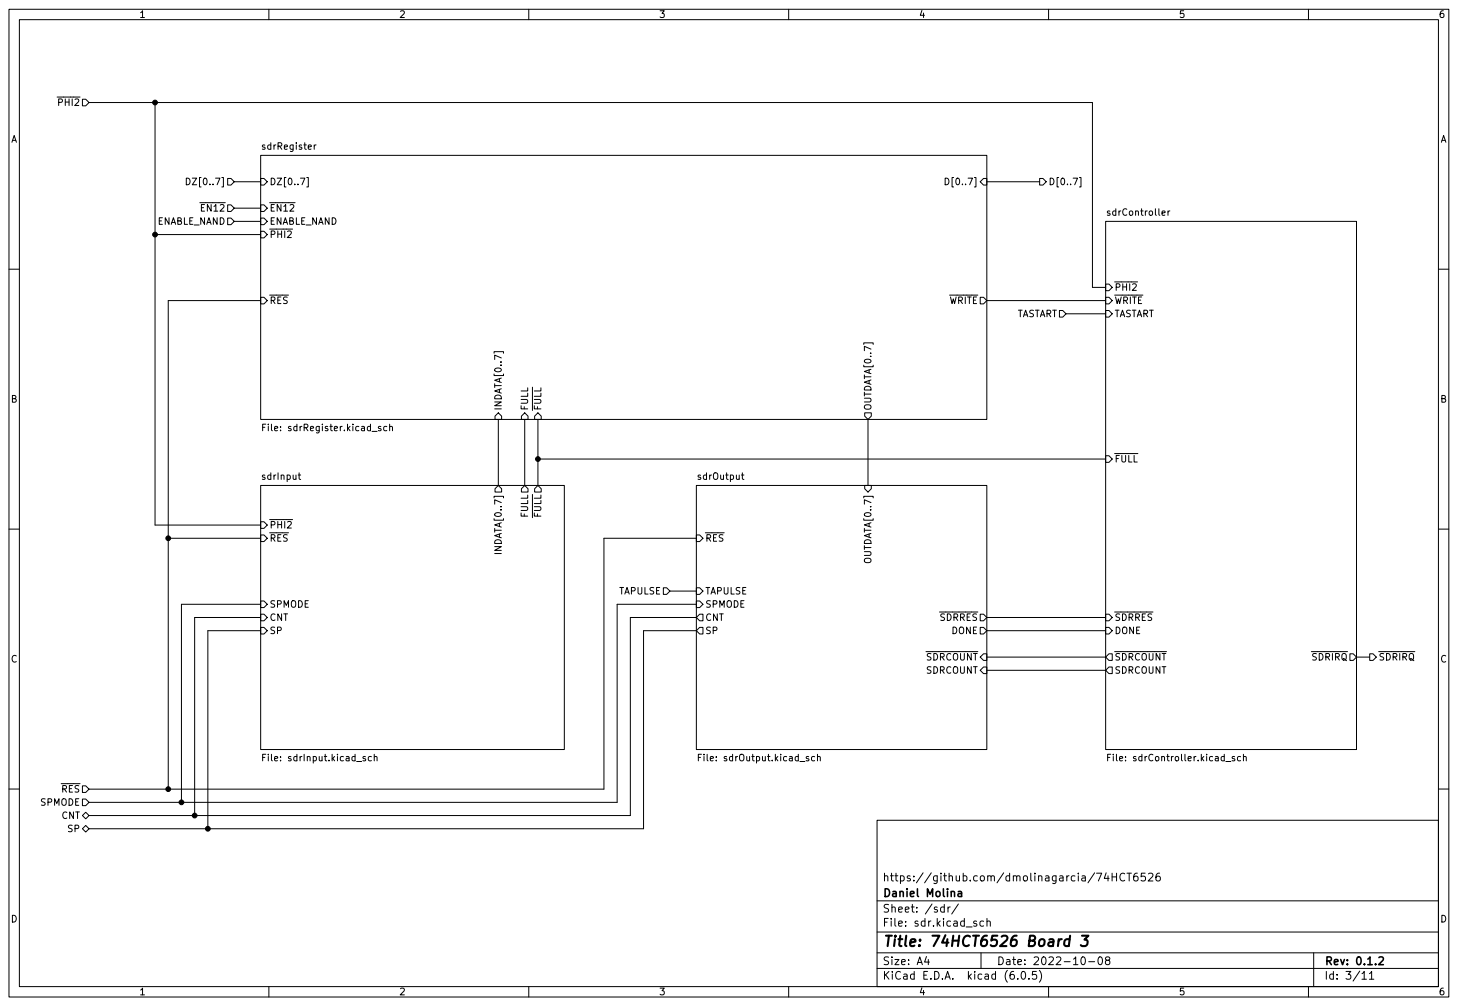
[picture p147: page 3]

~{EN12} ENABLE_NAND
sdrController File: sdrController.kicad_sch CNT

File: sdrOutput.kicad_sch SP CNT SPMODE

https://github.com/dmolinagarcia/74HCT6526
File: sdr.kicad_sch Sheet: /sdr/ Daniel Molina

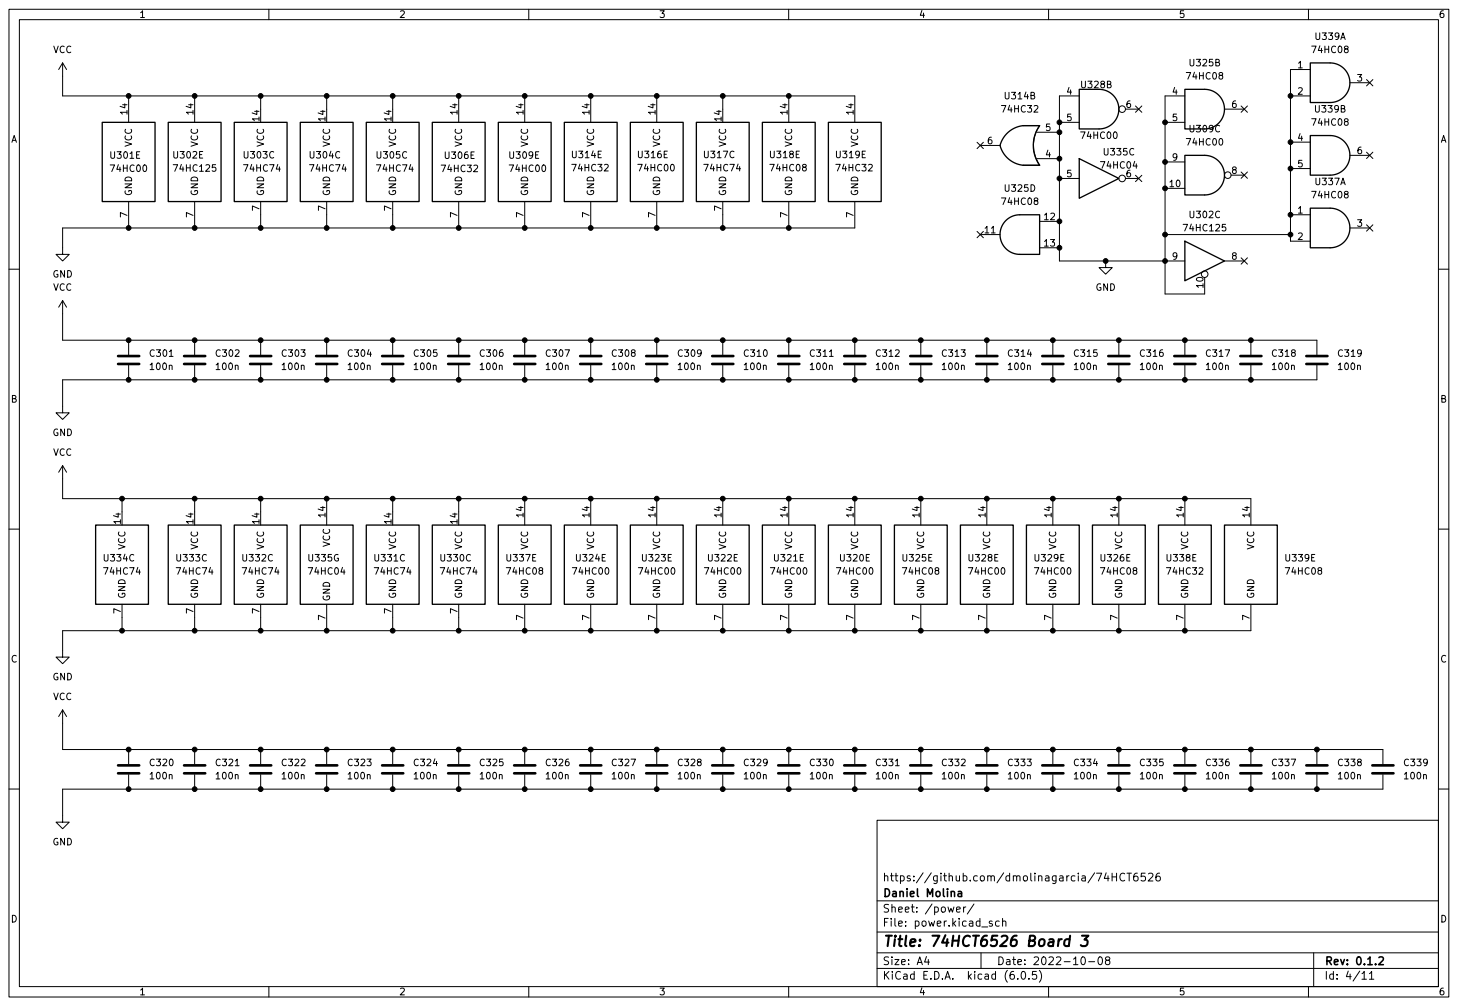
[picture p148: page 4]

https://github.com/dmolinagarcia/74HCT6526
Sheet: /power/ Daniel Molina

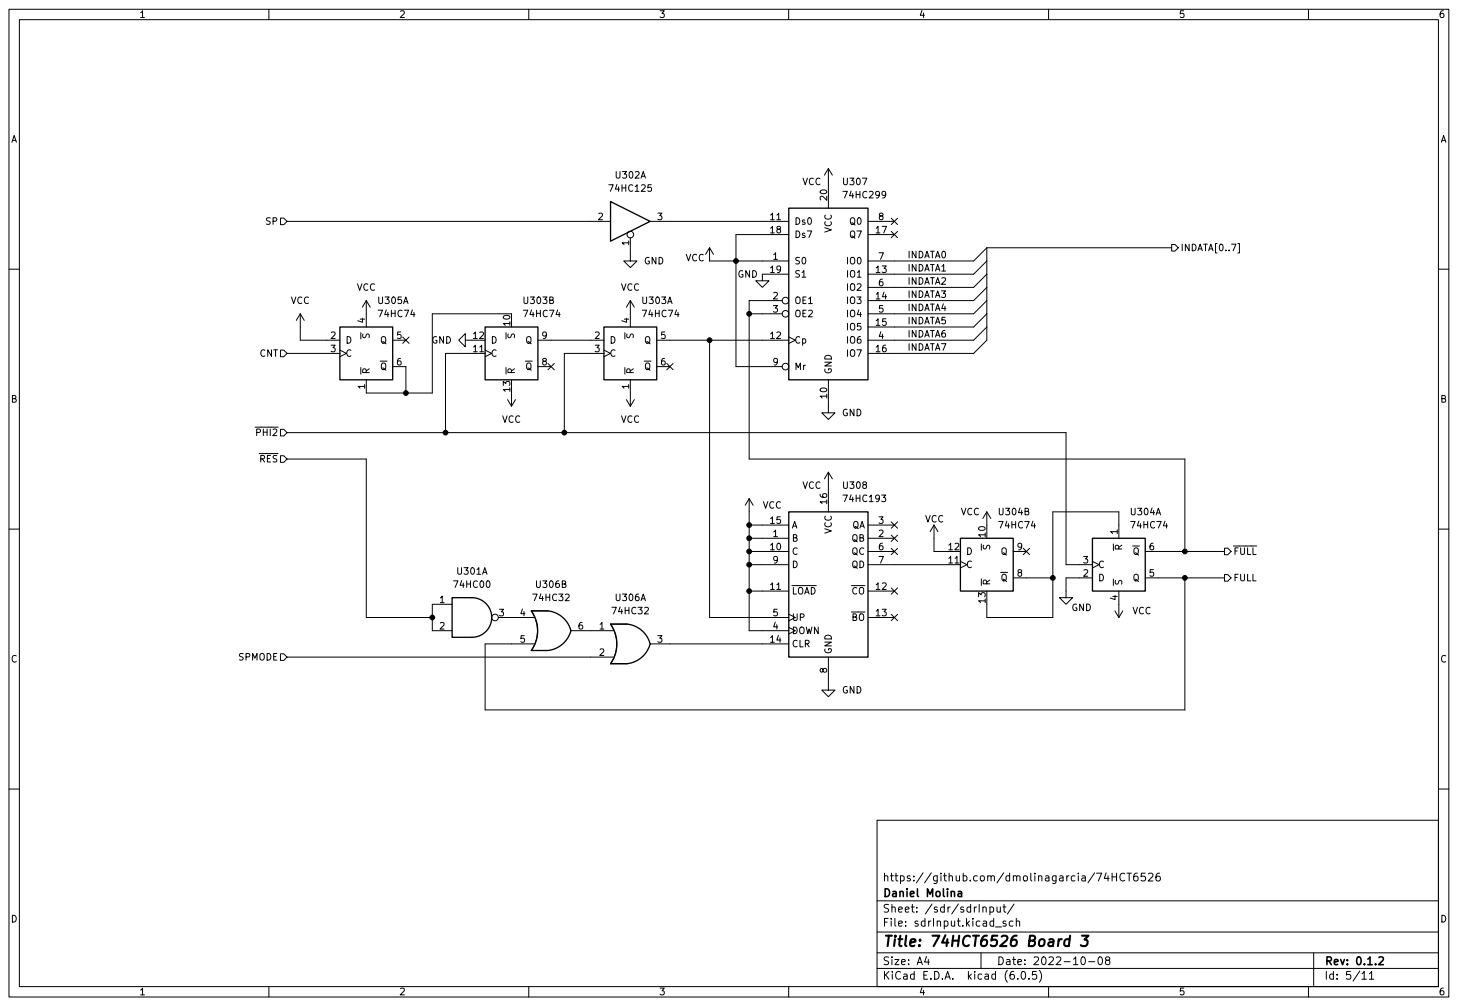
[picture p149: page 5]

https://github.com/dmolinagarcia/74HCT6526 GND

Sheet: /sdr/sdrInput/ Daniel Molina

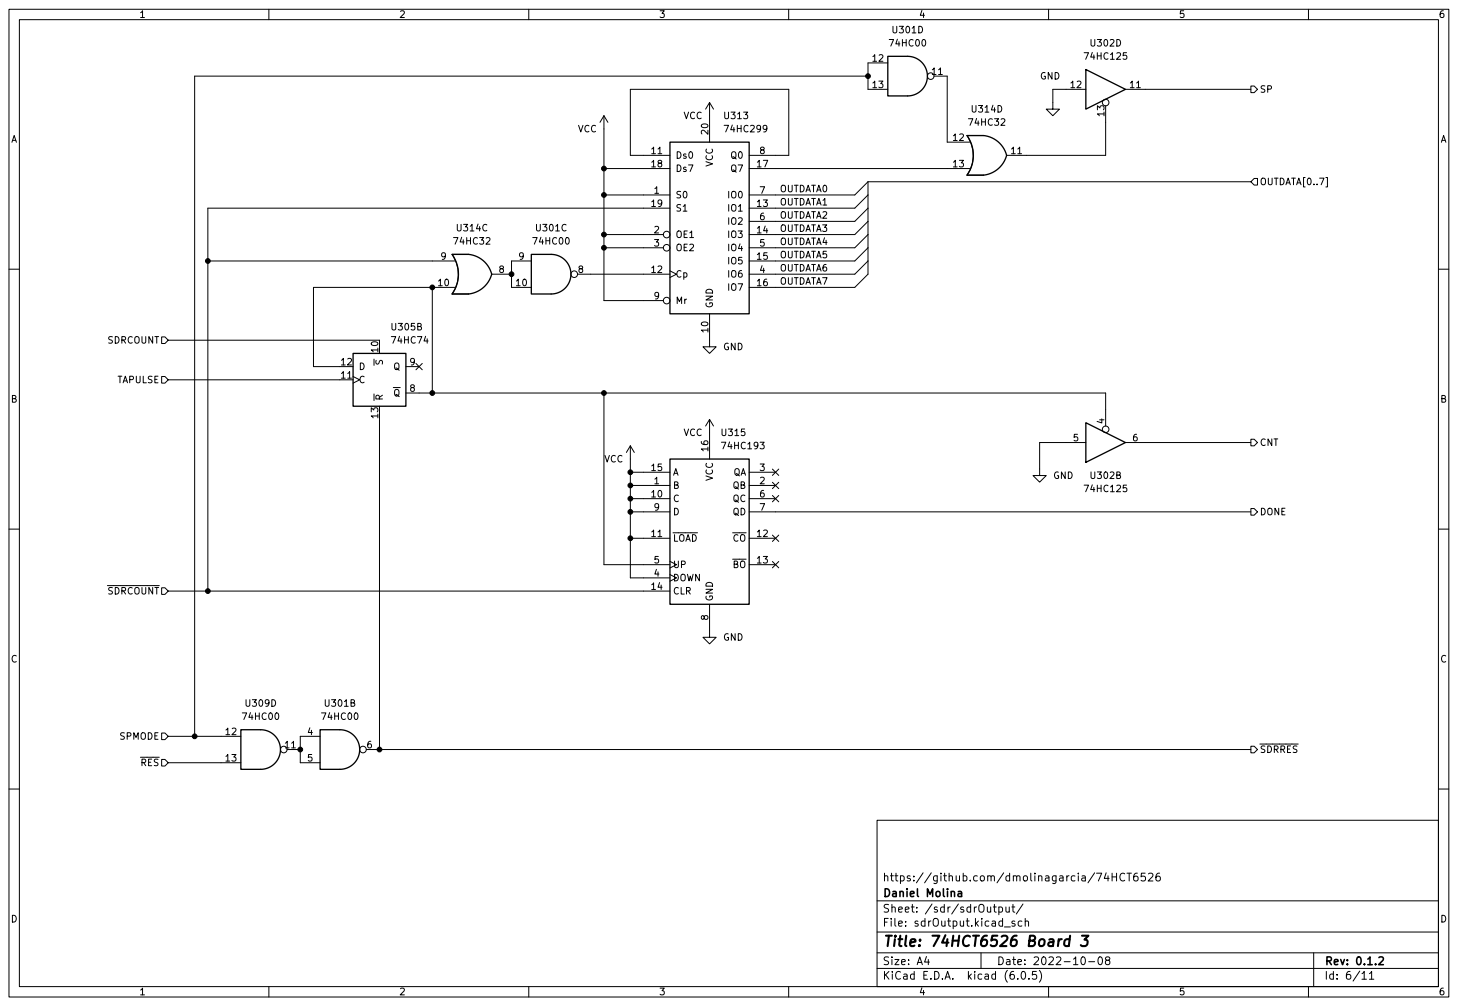
[picture p150: page 6]

~{SDRRES} DONE CNT SPMODE

https://github.com/dmolinagarcia/74HCT6526 VCC

Sheet: /sdr/sdrOutput/ Daniel Molina

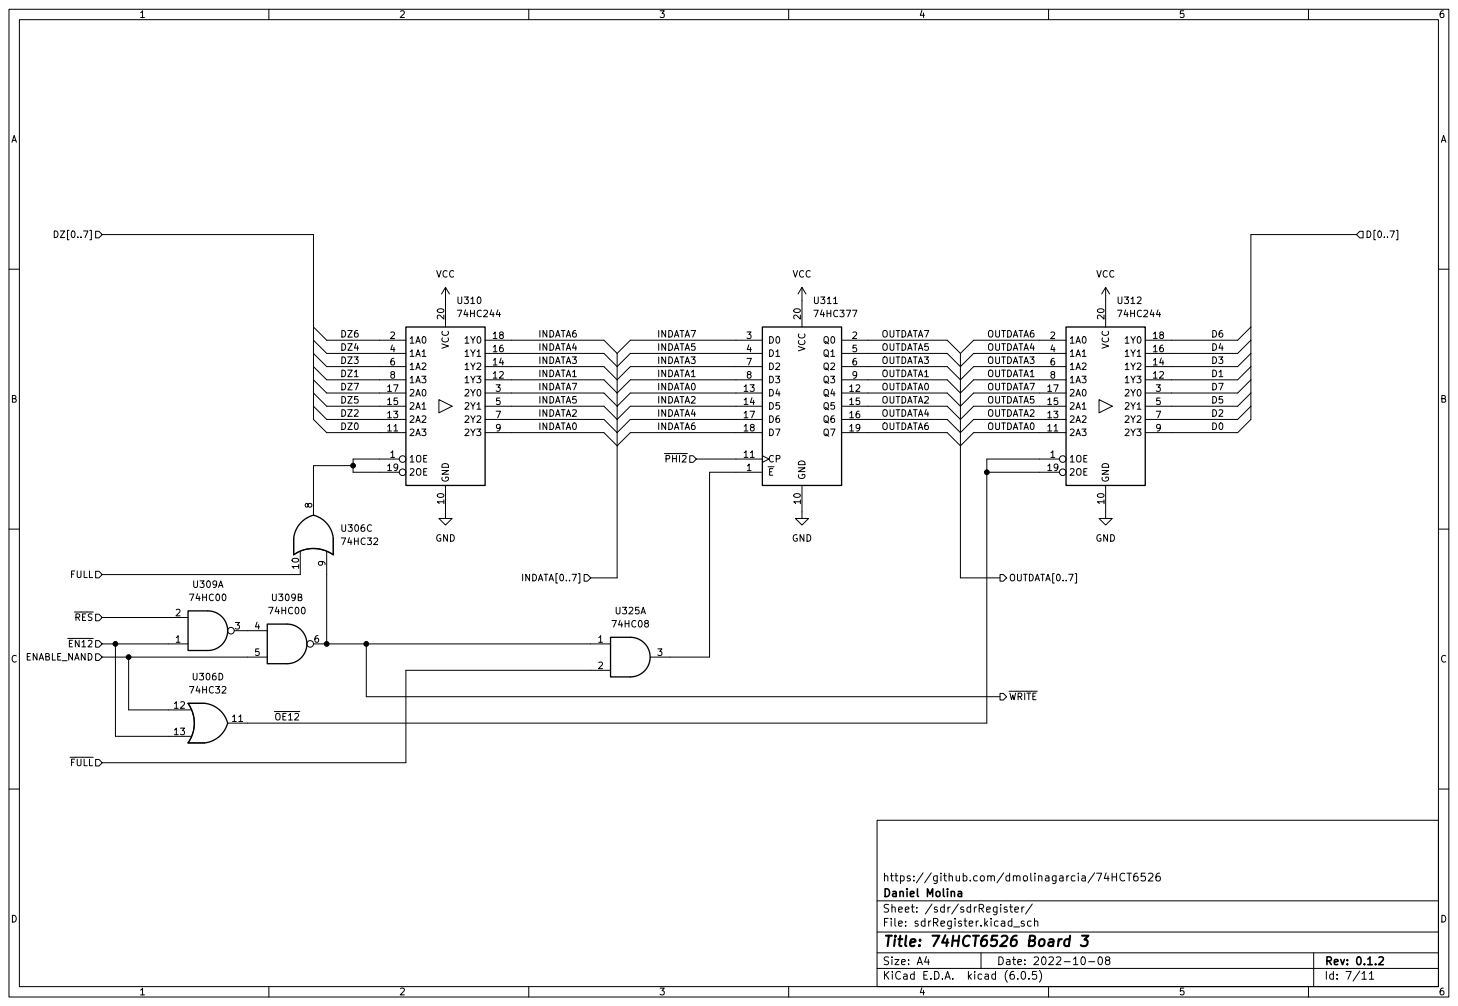
[picture p151: page 7]

https://github.com/dmolinagarcia/74HCT6526
Sheet: /sdr/sdrRegister/ Daniel Molina

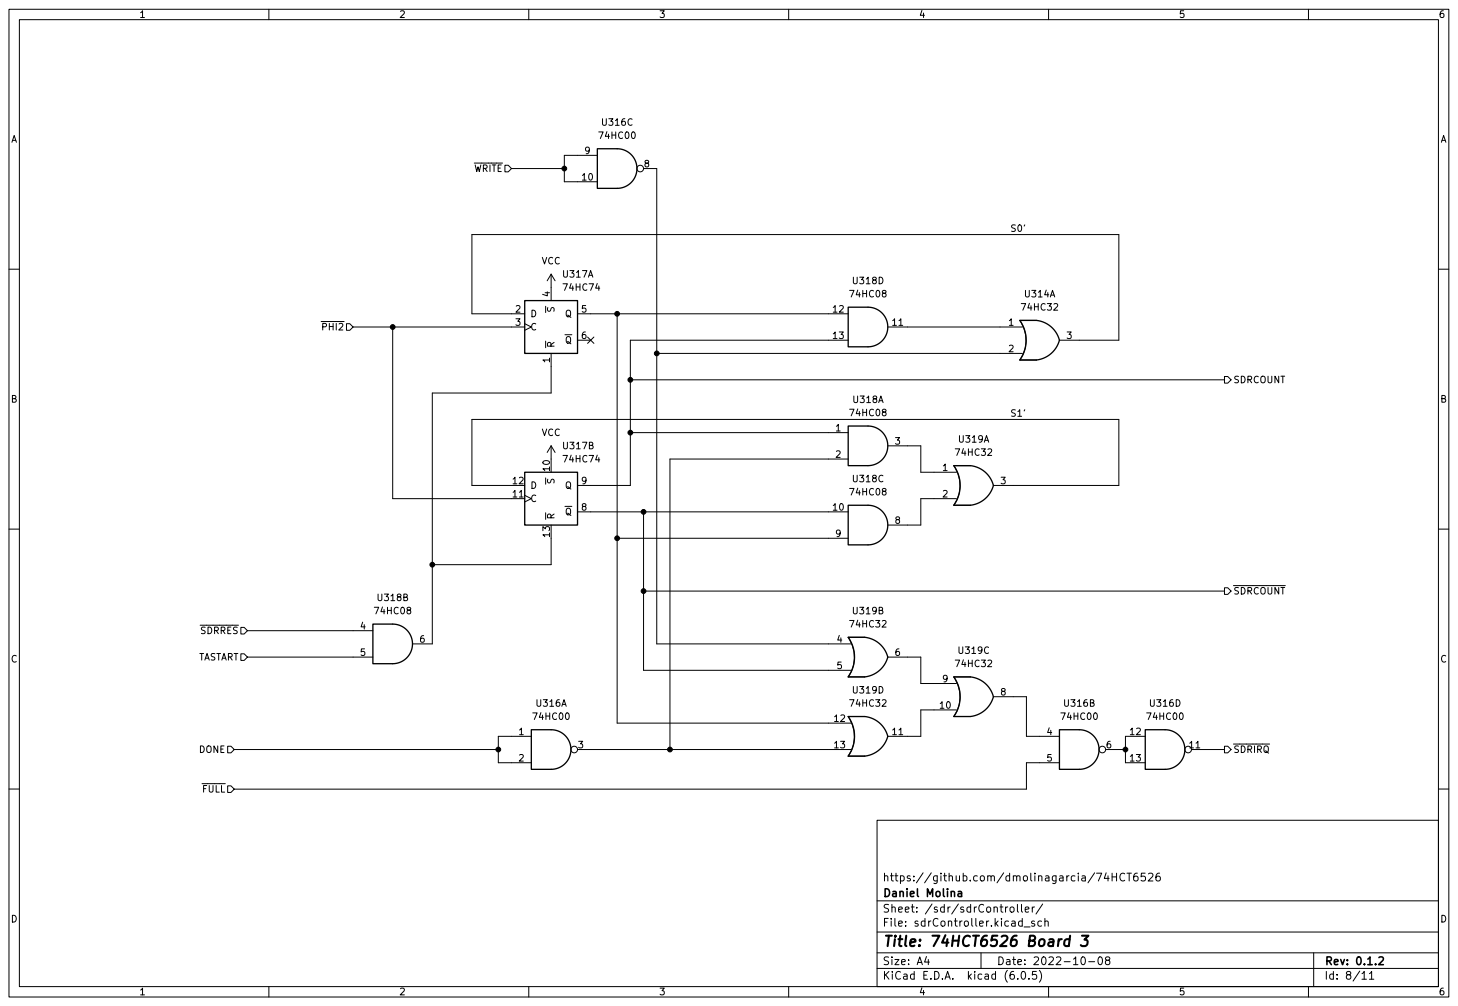
[picture p152: page 8]

https://github.com/dmolinagarcia/74HCT6526
File: sdrController.kicad_sch Sheet: /sdr/sdrController/ Daniel Molina

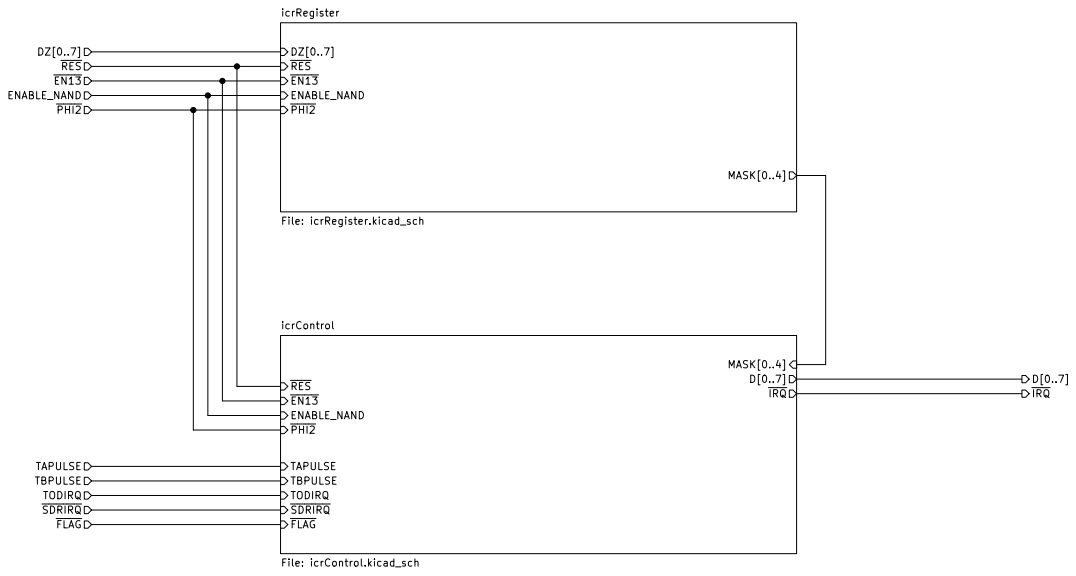
[picture p153: page 9]

https://github.com/dmolinagarcia/74HCT6526
File: icr.kicad_sch Sheet: /icr/ Daniel Molina

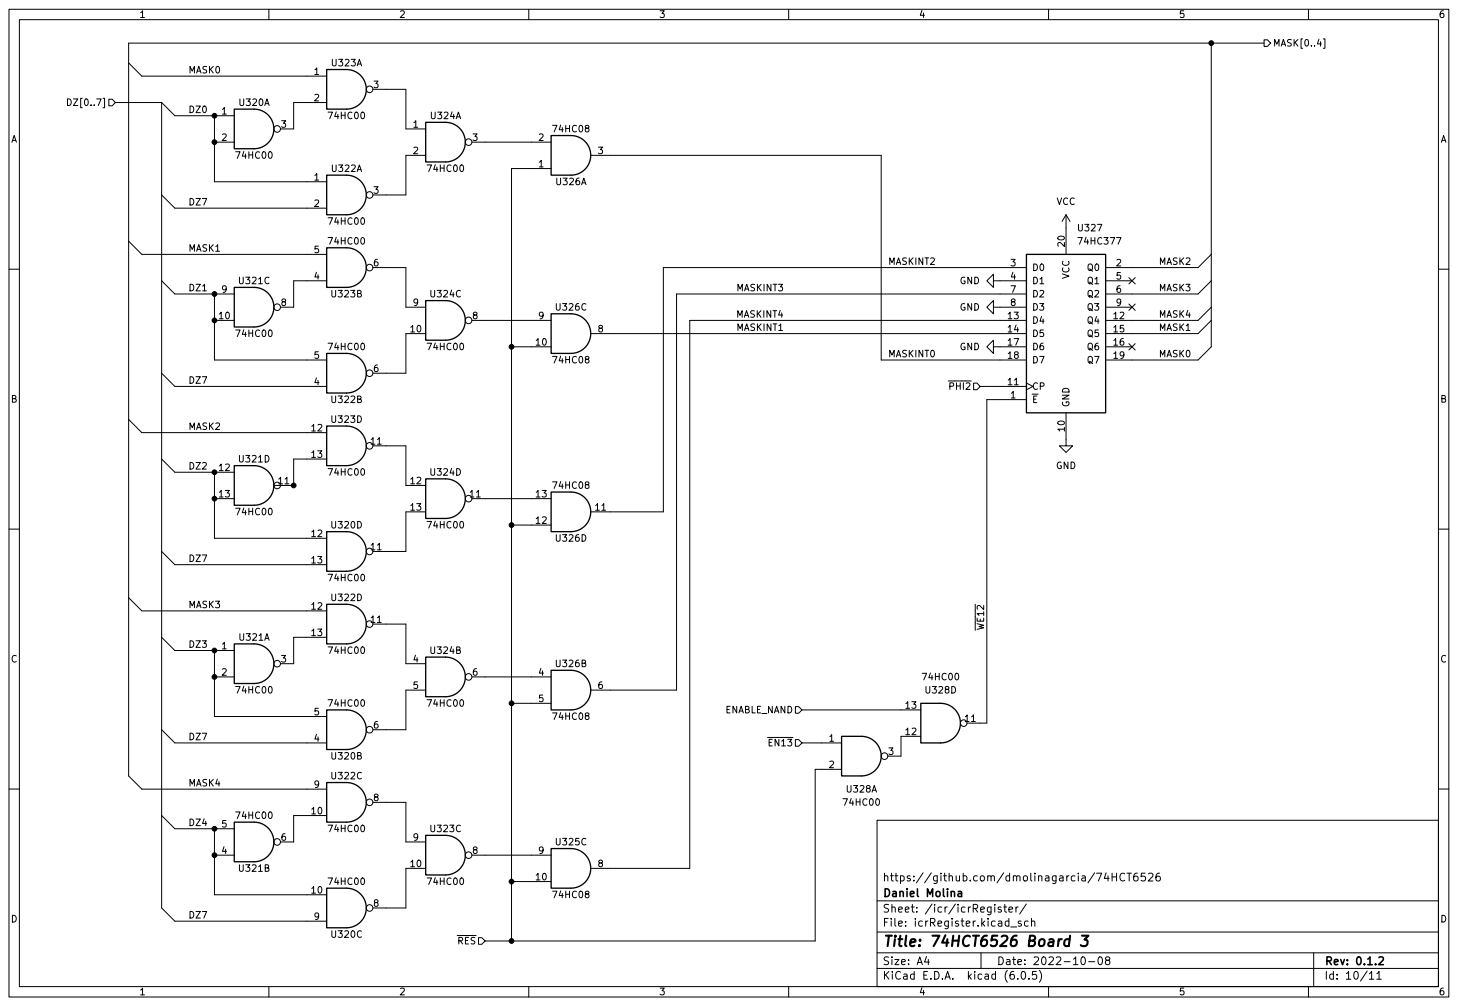
[picture p154: page 10]

Sheet: /icr/icrRegister/ Daniel Molina

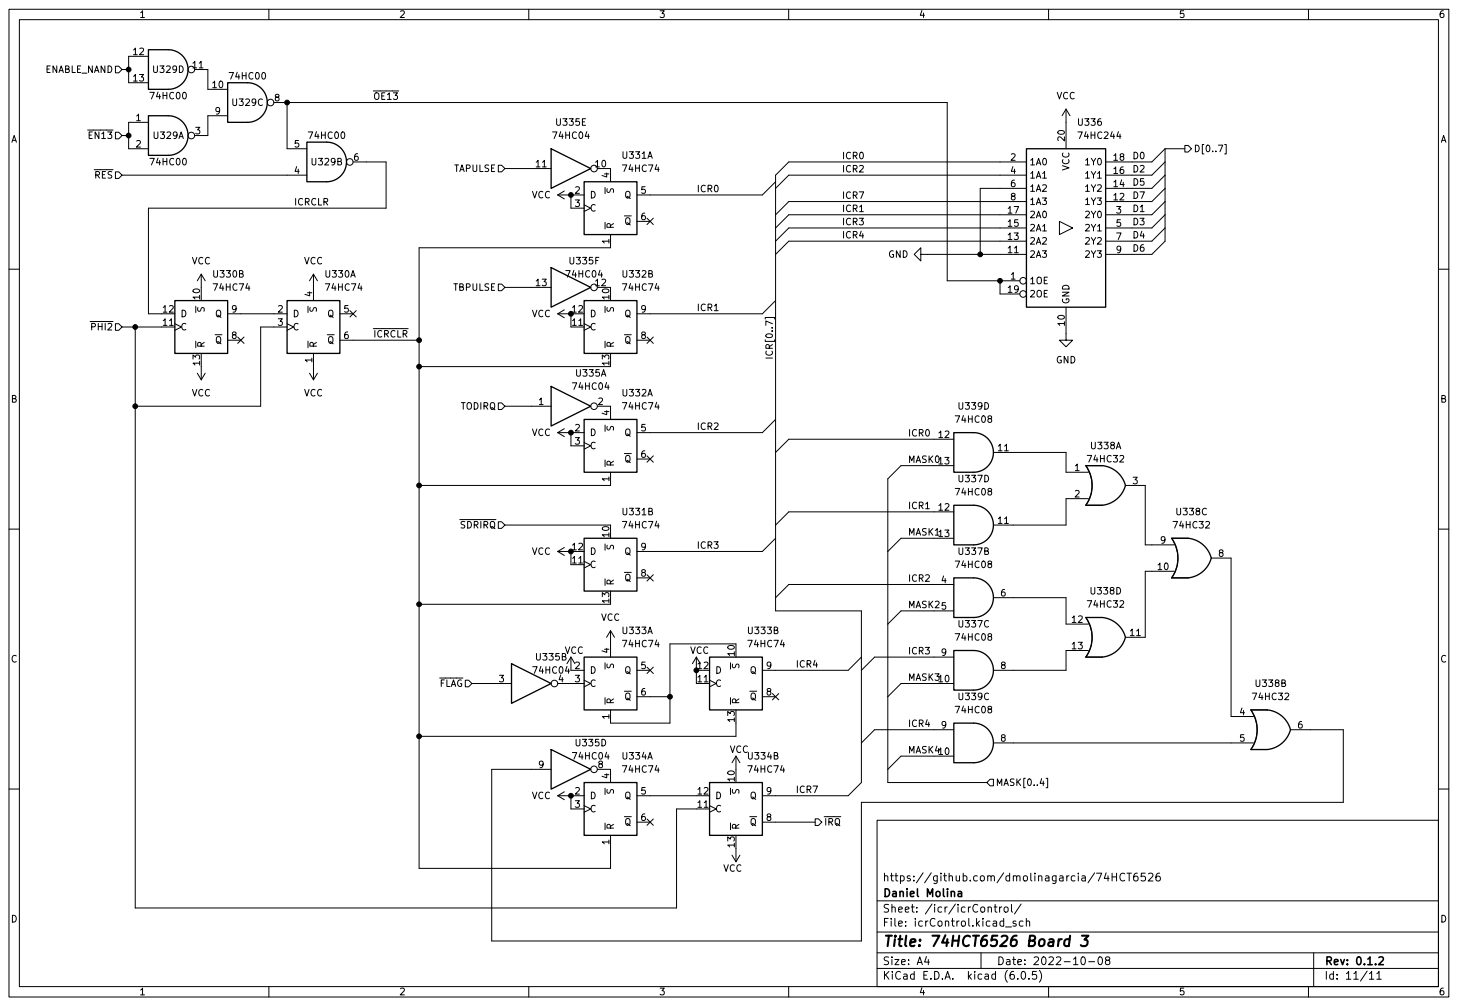
[picture p155: page 11]

https://github.com/dmolinagarcia/74HCT6526
File: icrControl.kicad_sch Sheet: /icr/icrControl/ Daniel Molina
