dmolinagarcia/74HCT6526/pdf/B0.sch.v0.2.1.pdf

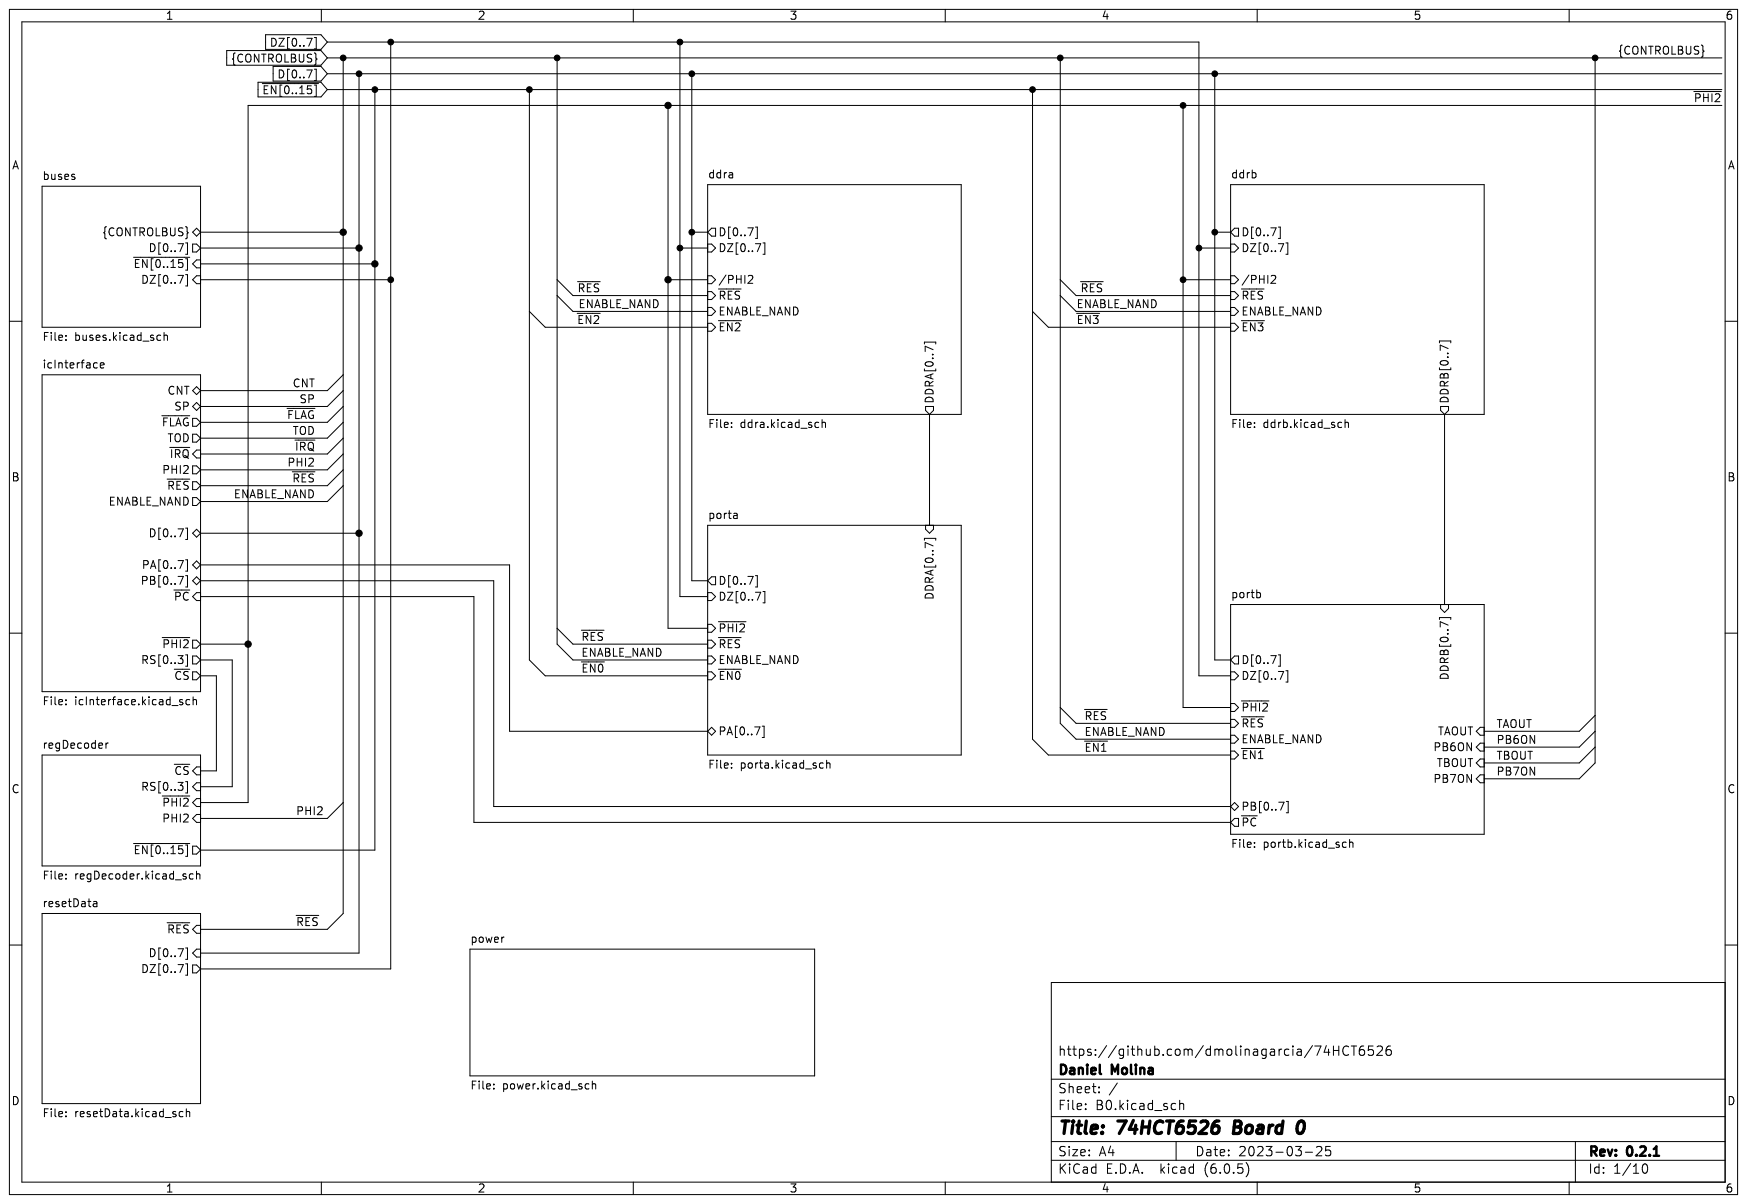
[picture p157: page 1]


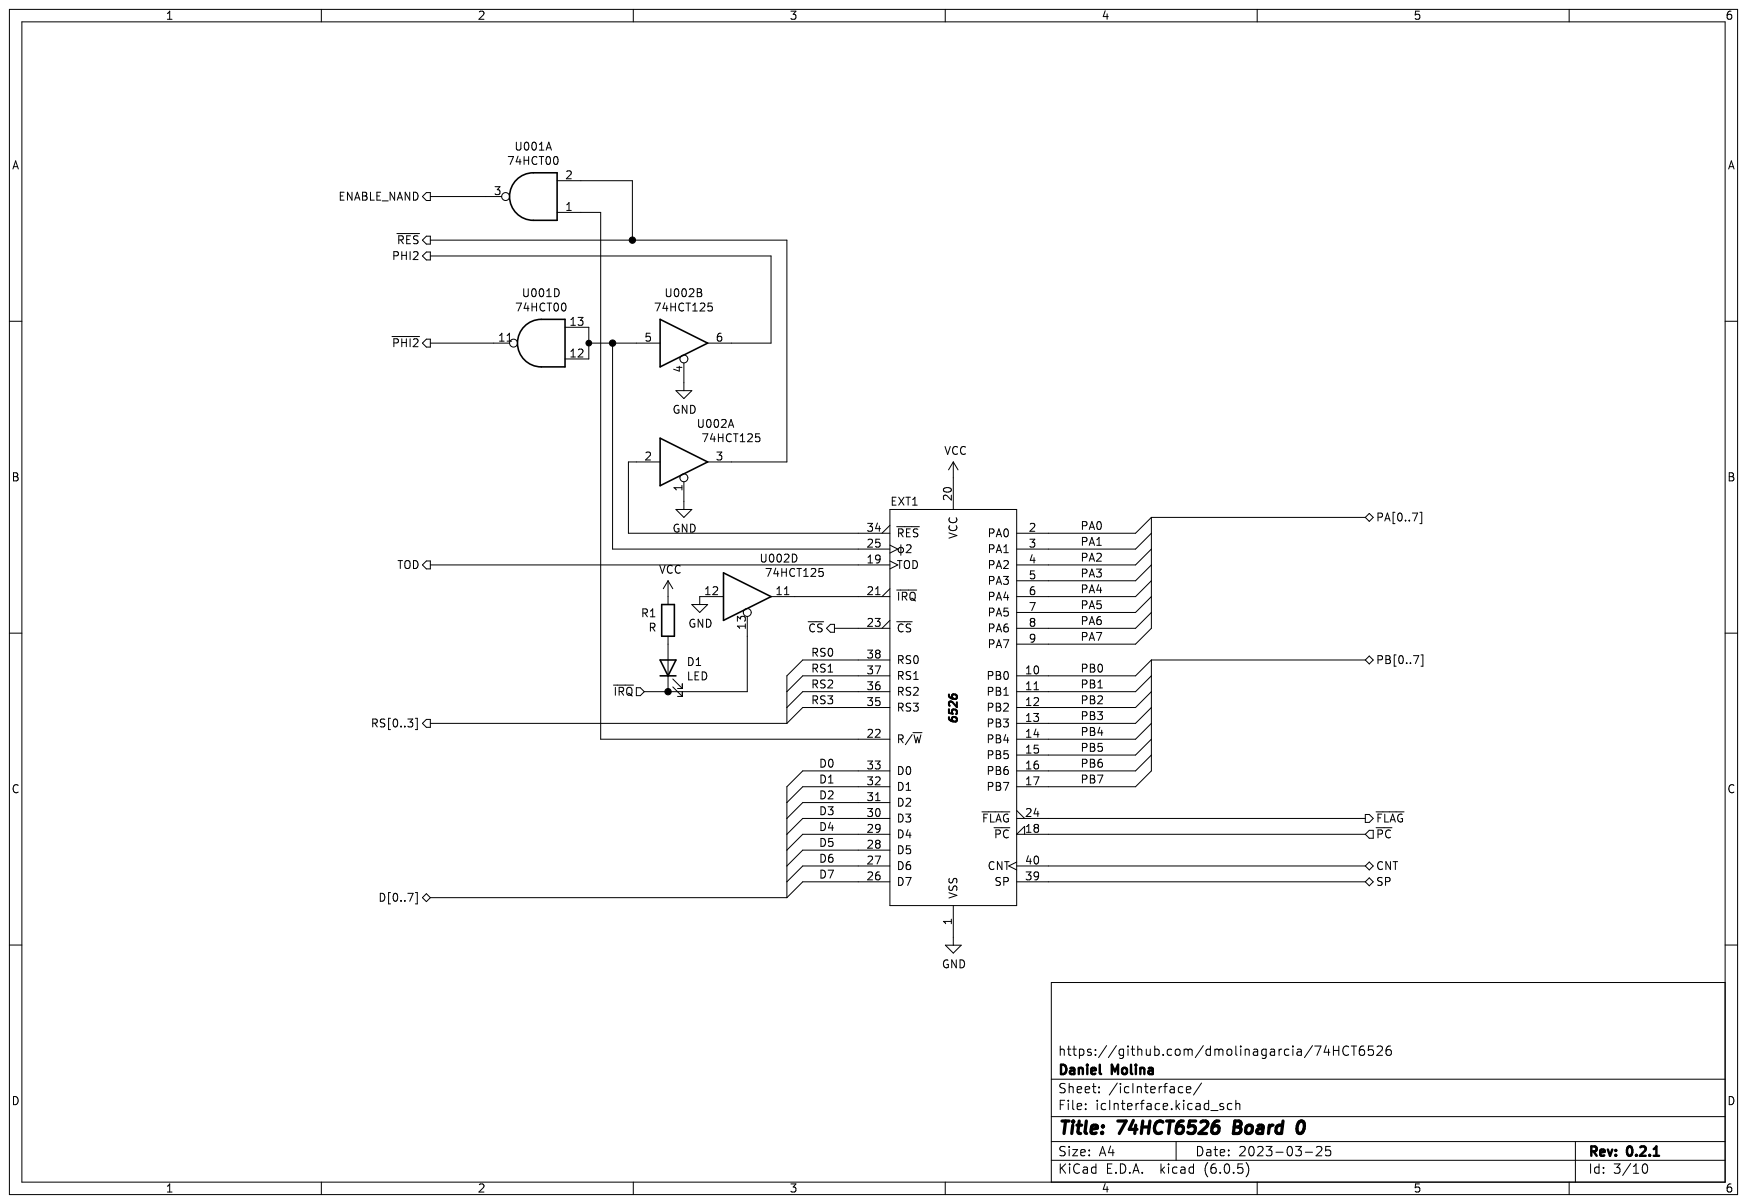
[picture p158: page 3]



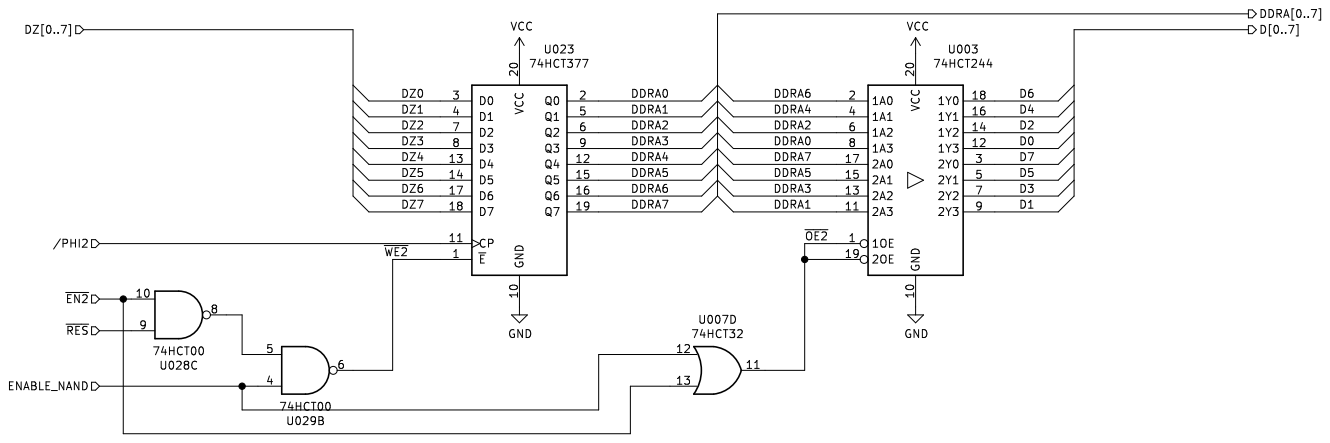
[picture p159: page 6]

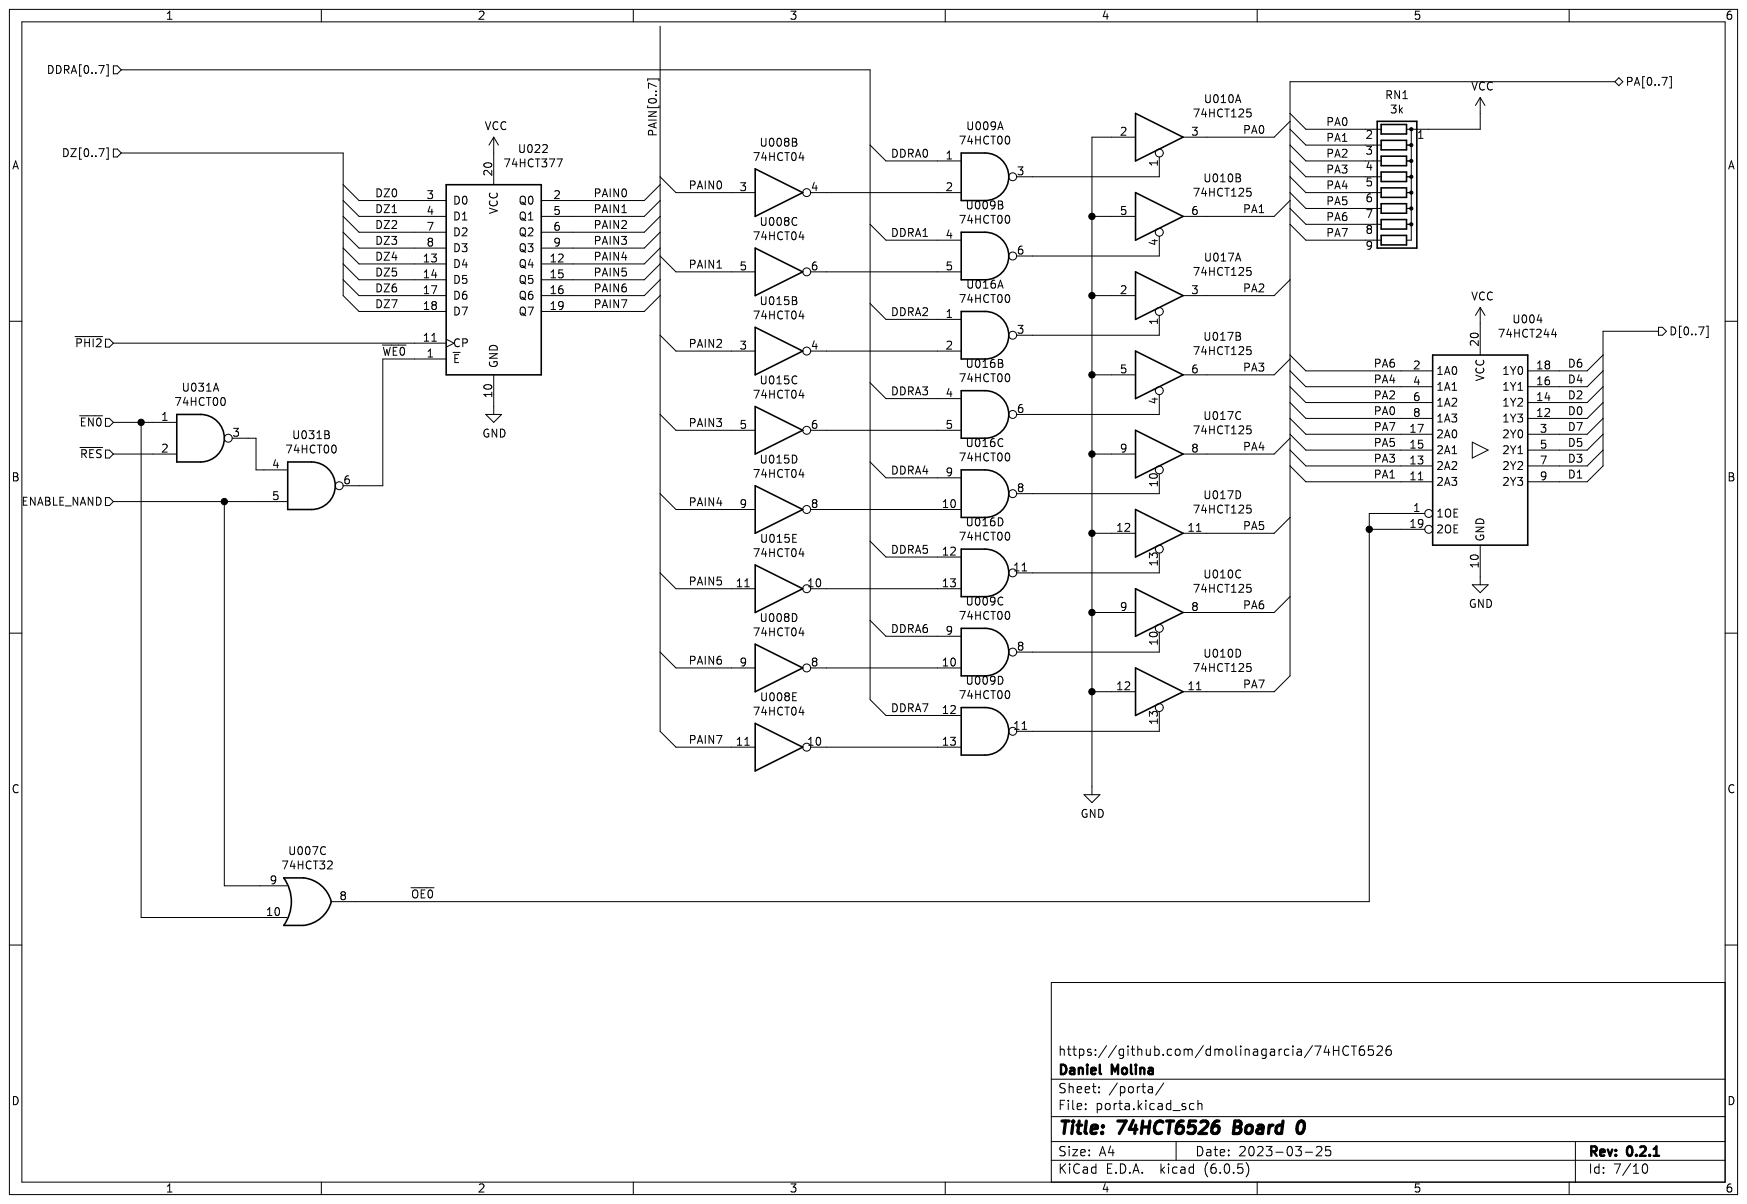
[picture p160: page 7]

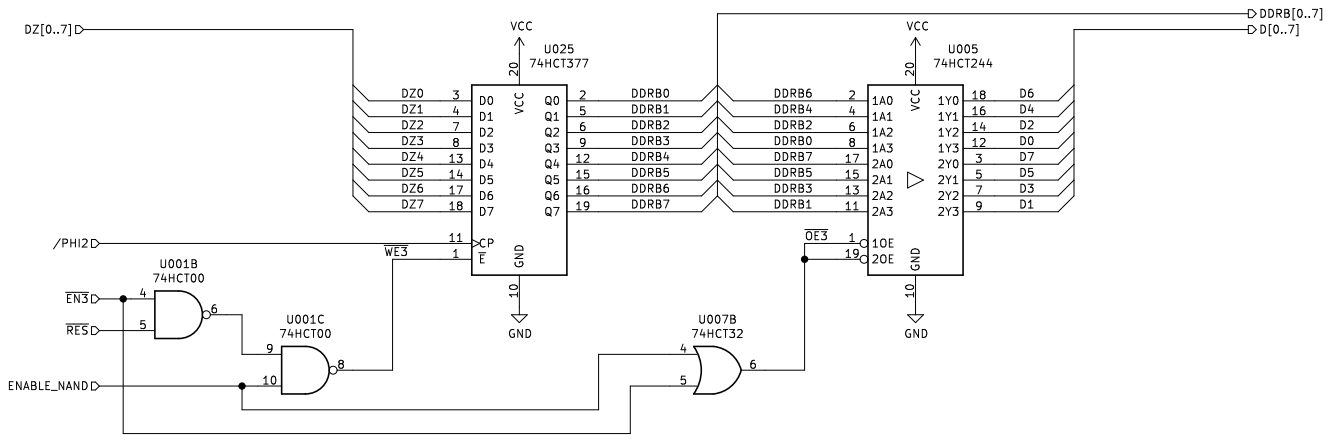
[picture p161: page 8]

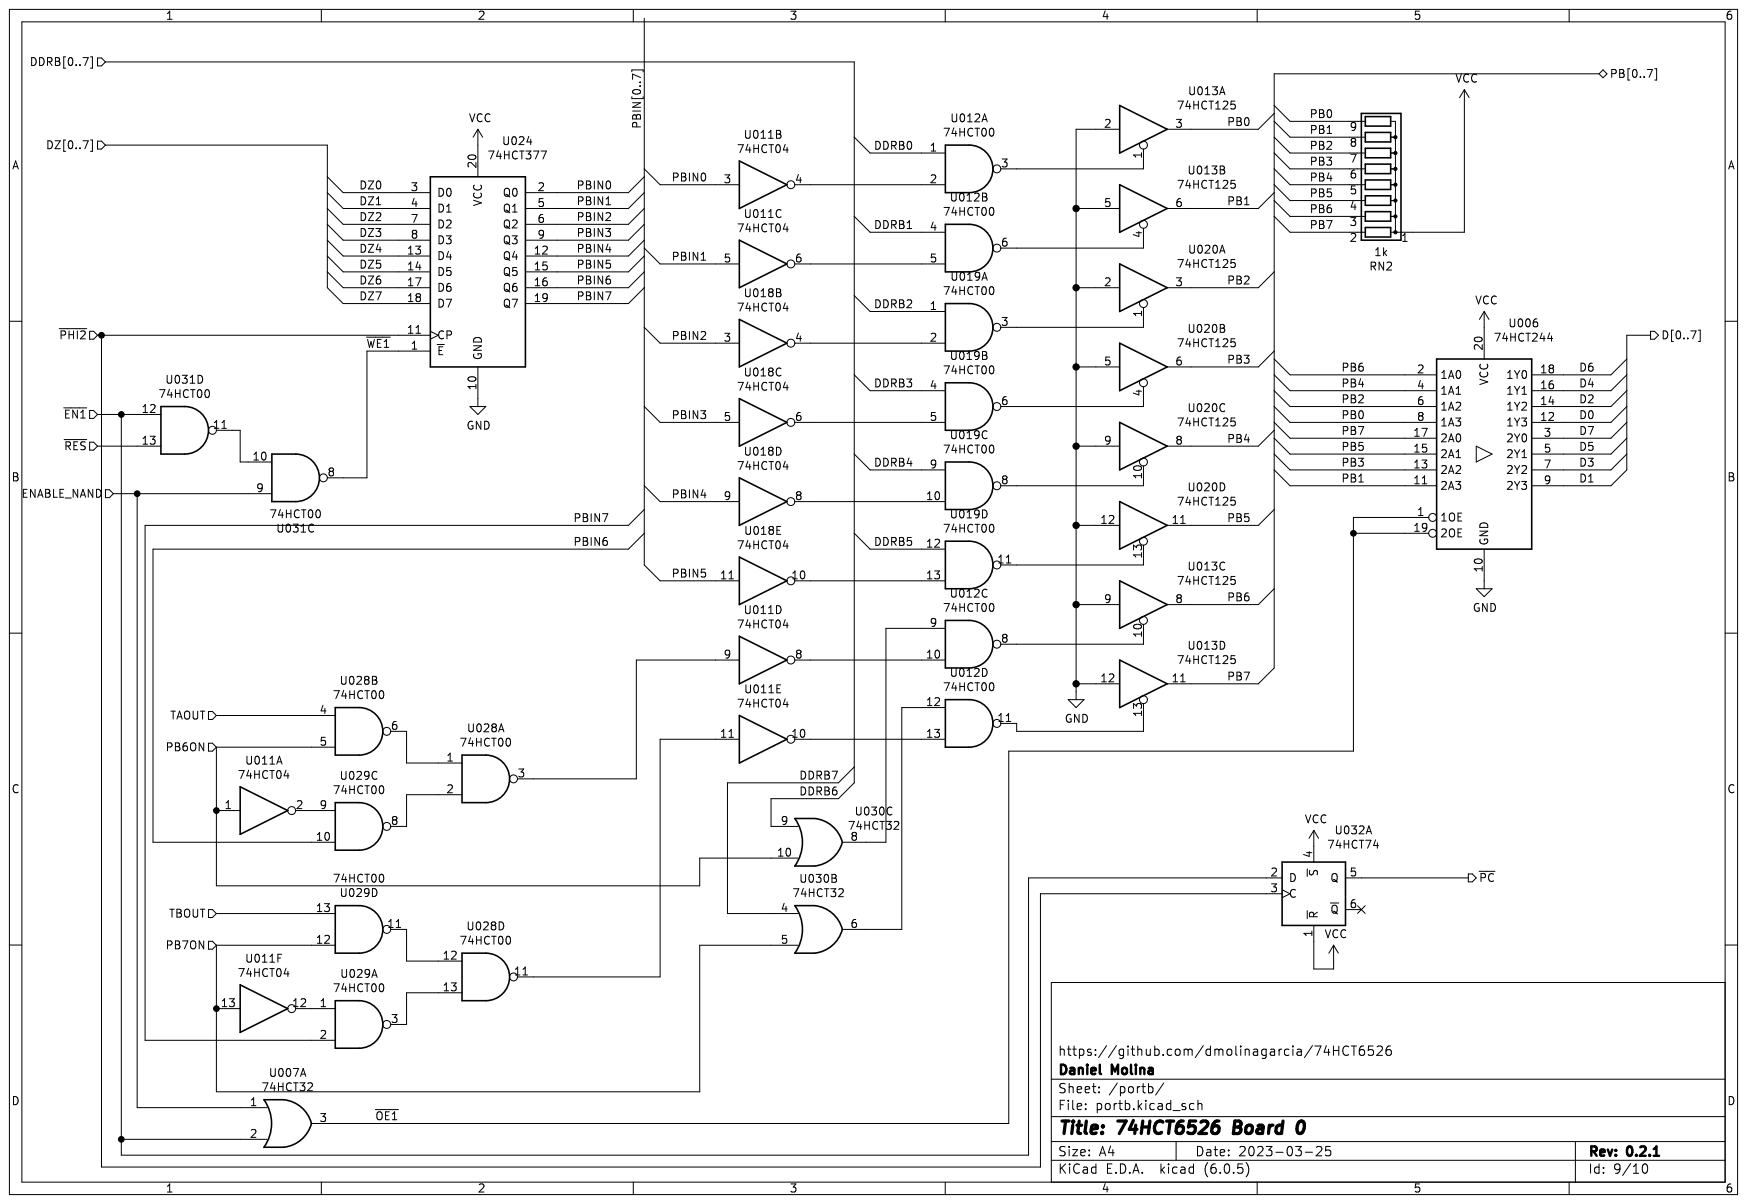
[picture p162: page 9]

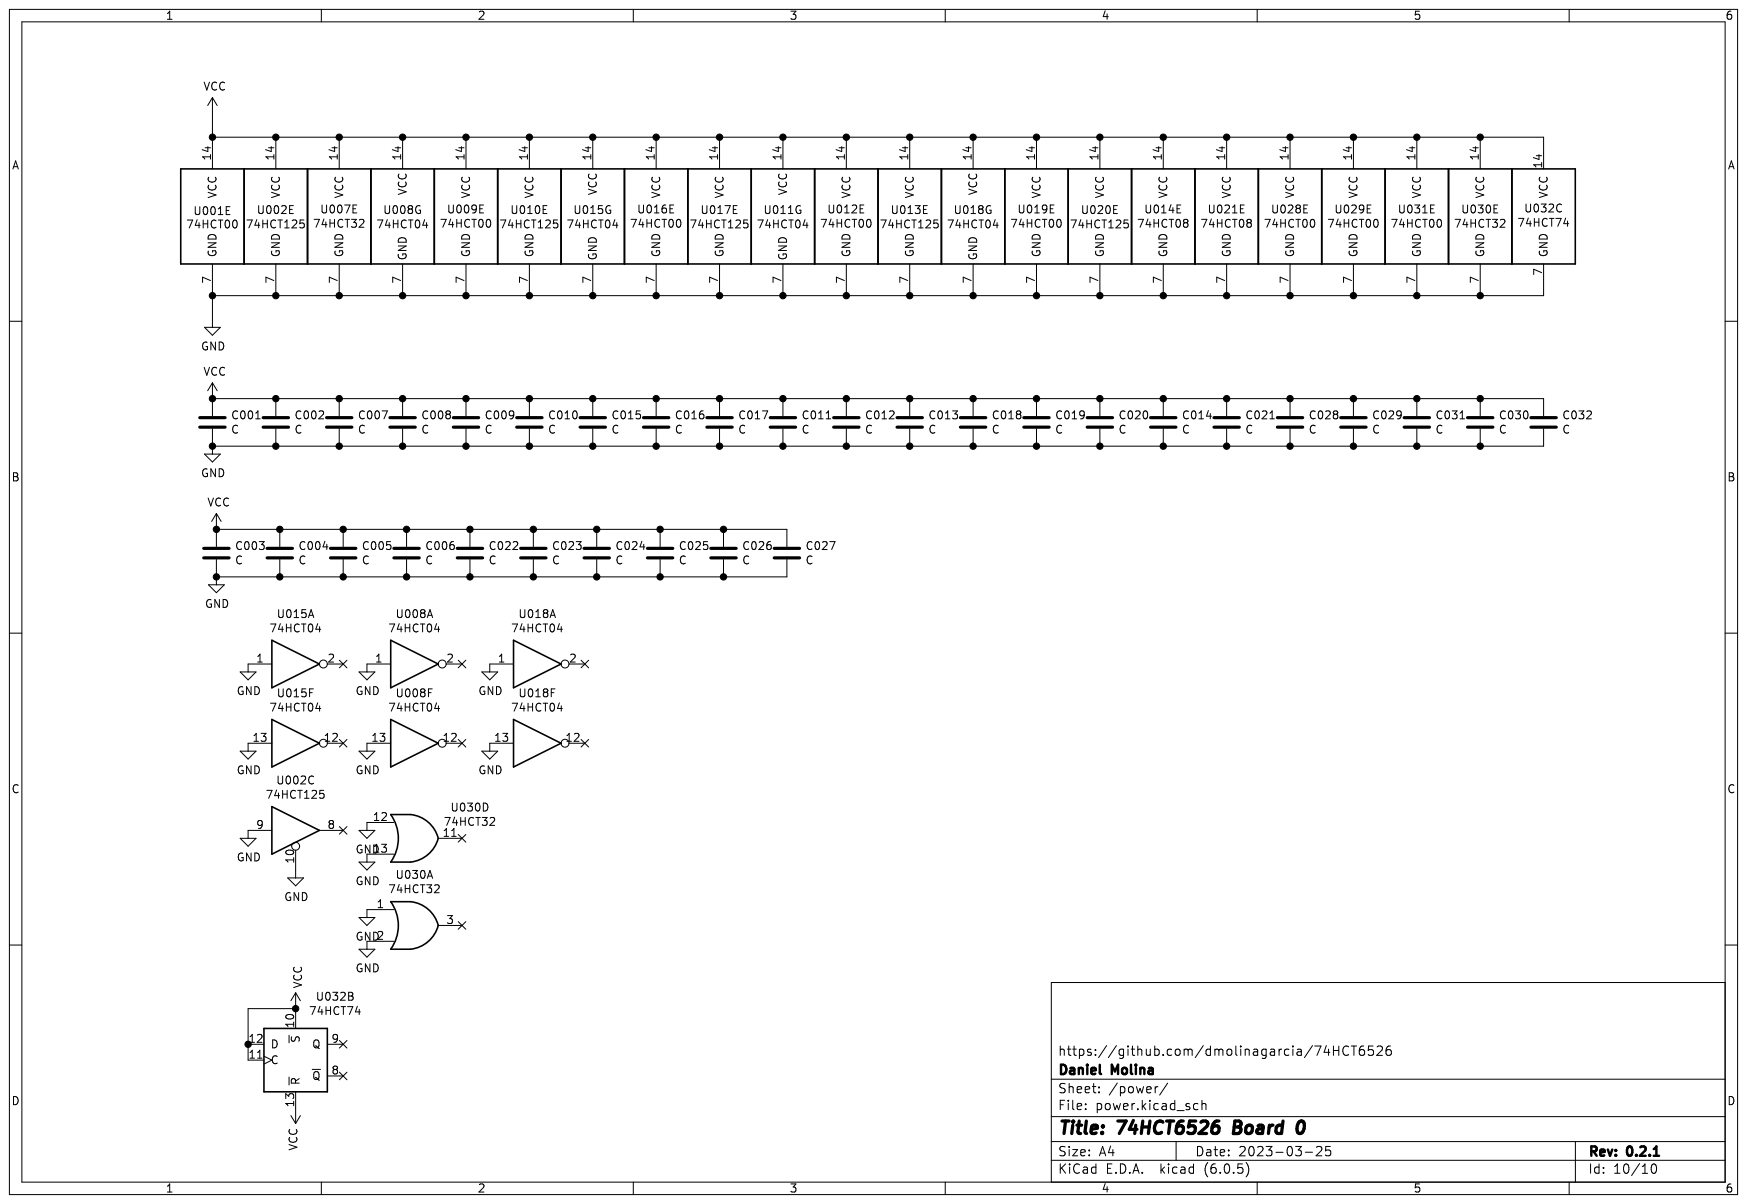
[picture p163: page 10]
