dmolinagarcia/74HCT6526/pdf/B1.pcb.v0.2.1.pdf

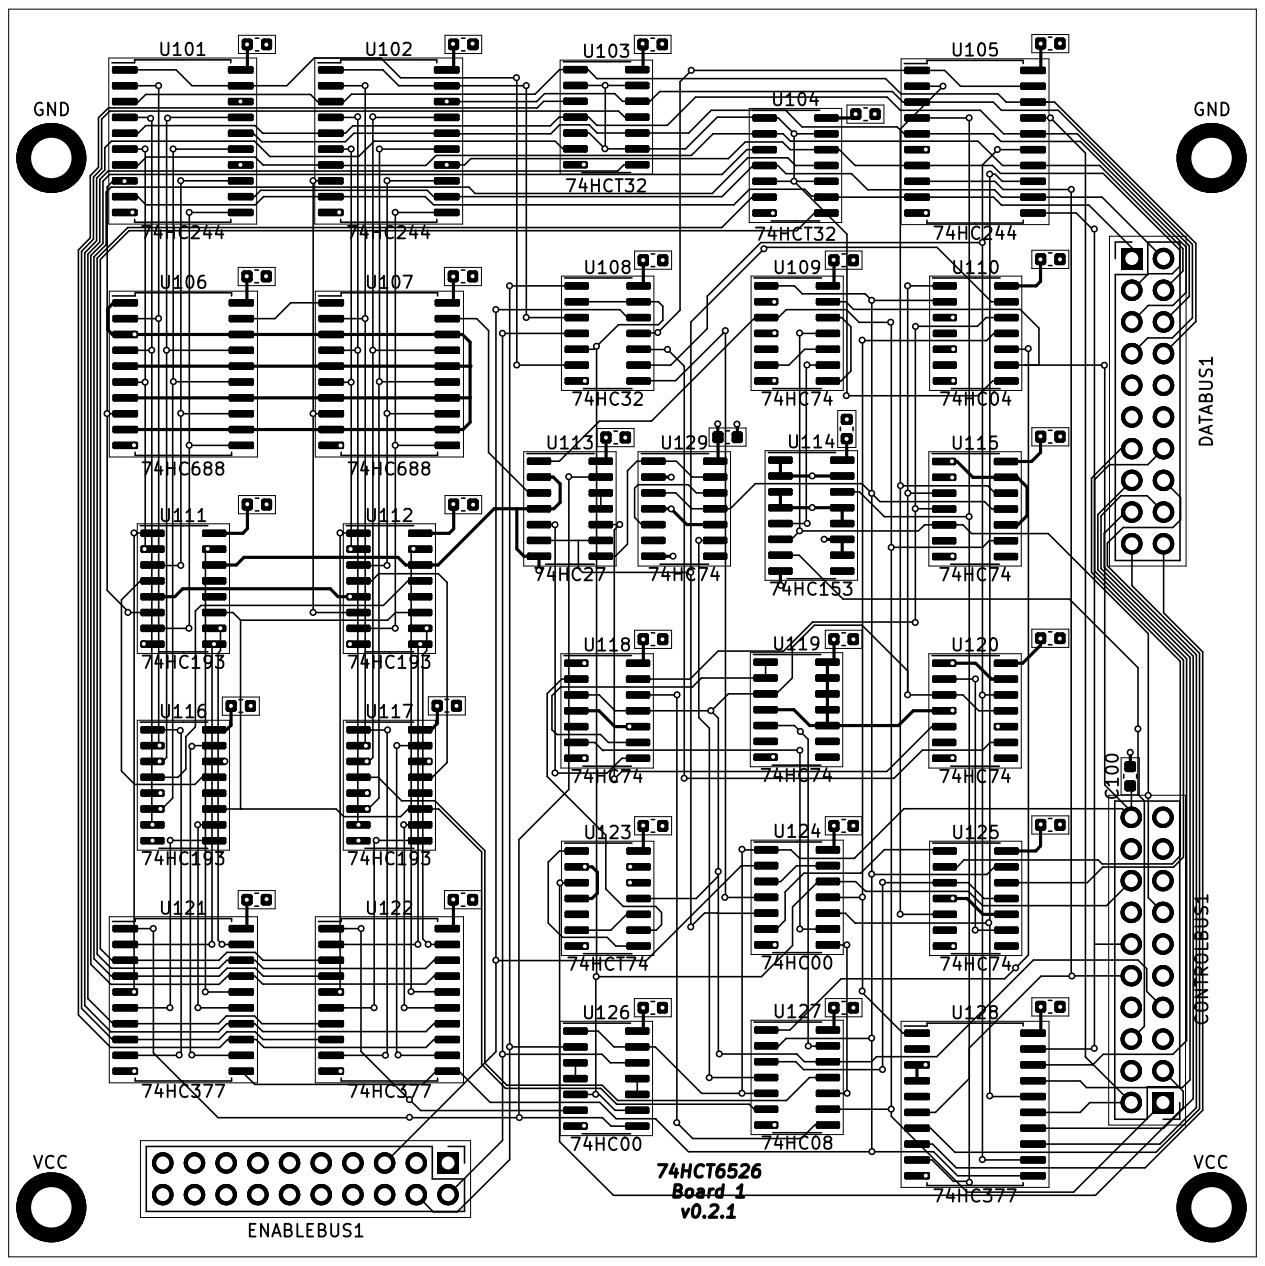
[picture p164: page 1]
