dmolinagarcia/74HCT6526/pdf/B1.sch.v0.2.1.pdf

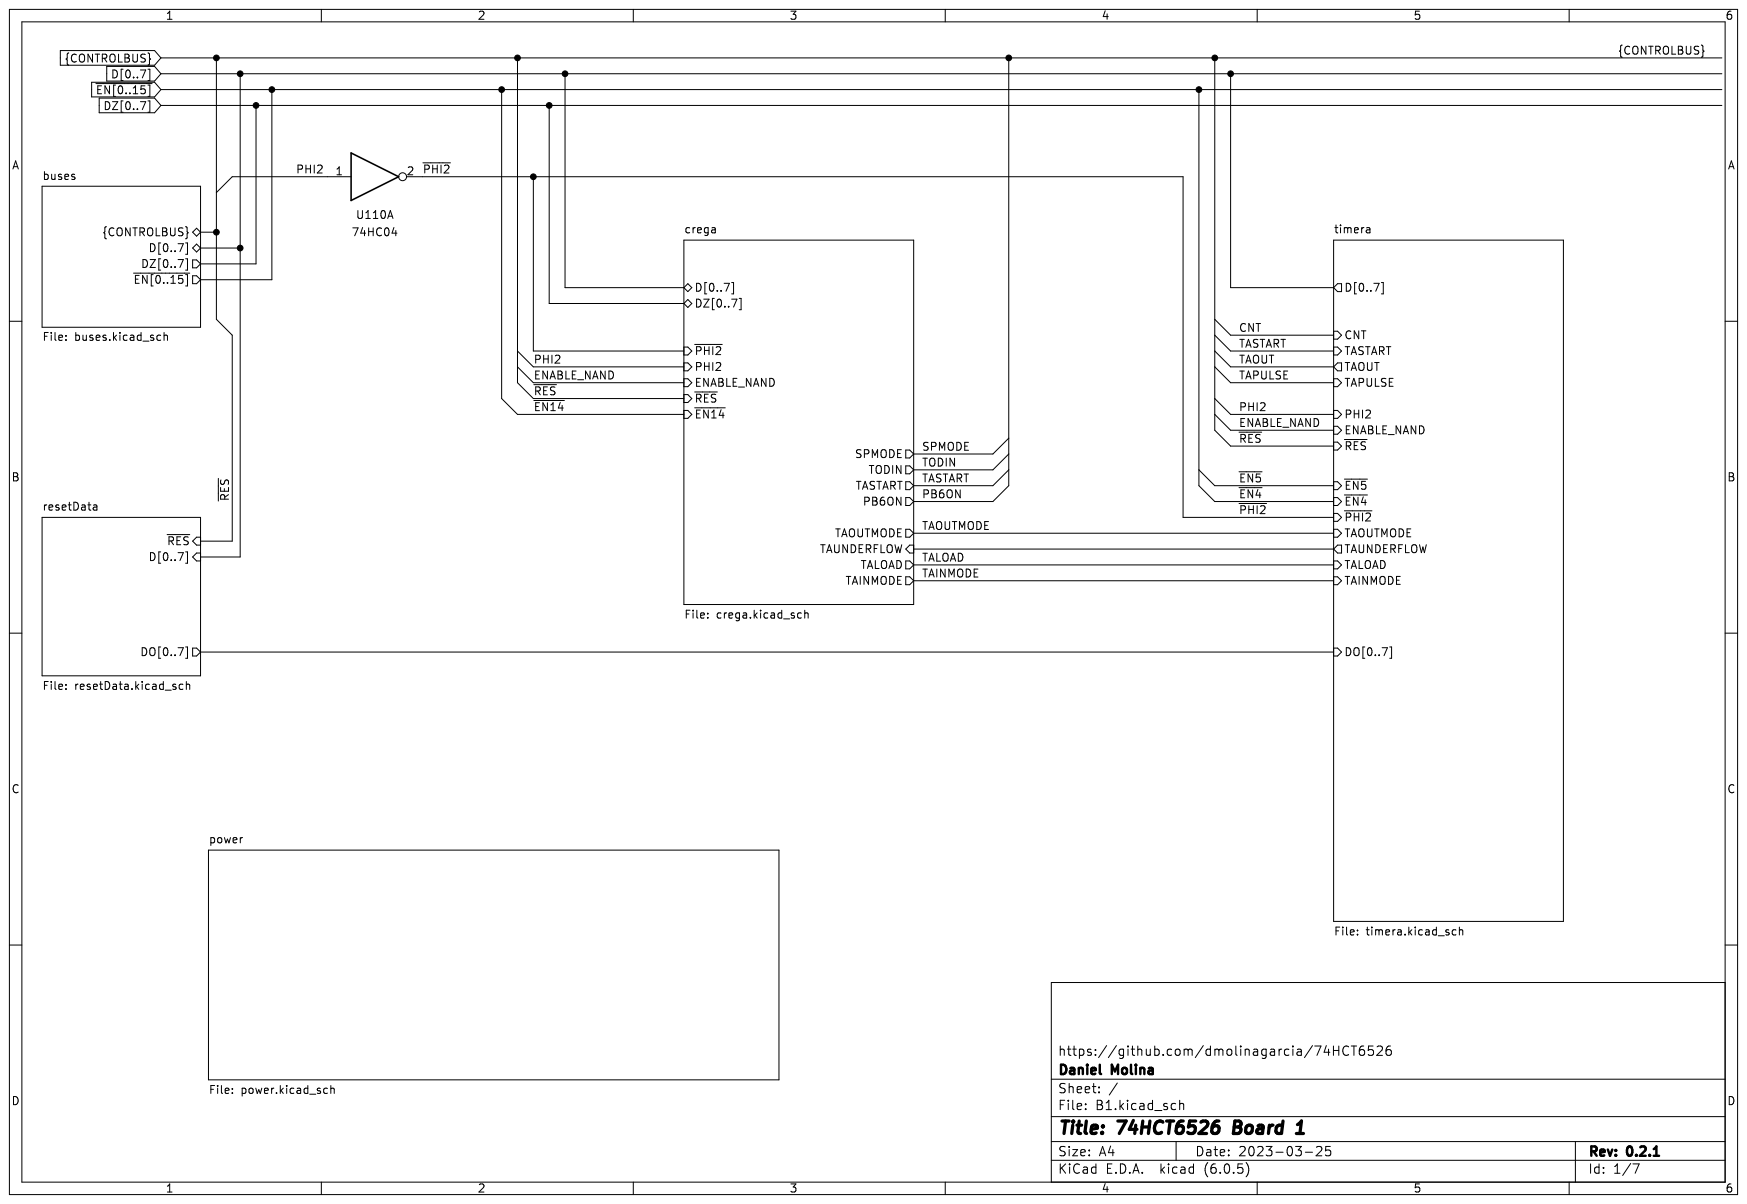
[picture p165: page 1]

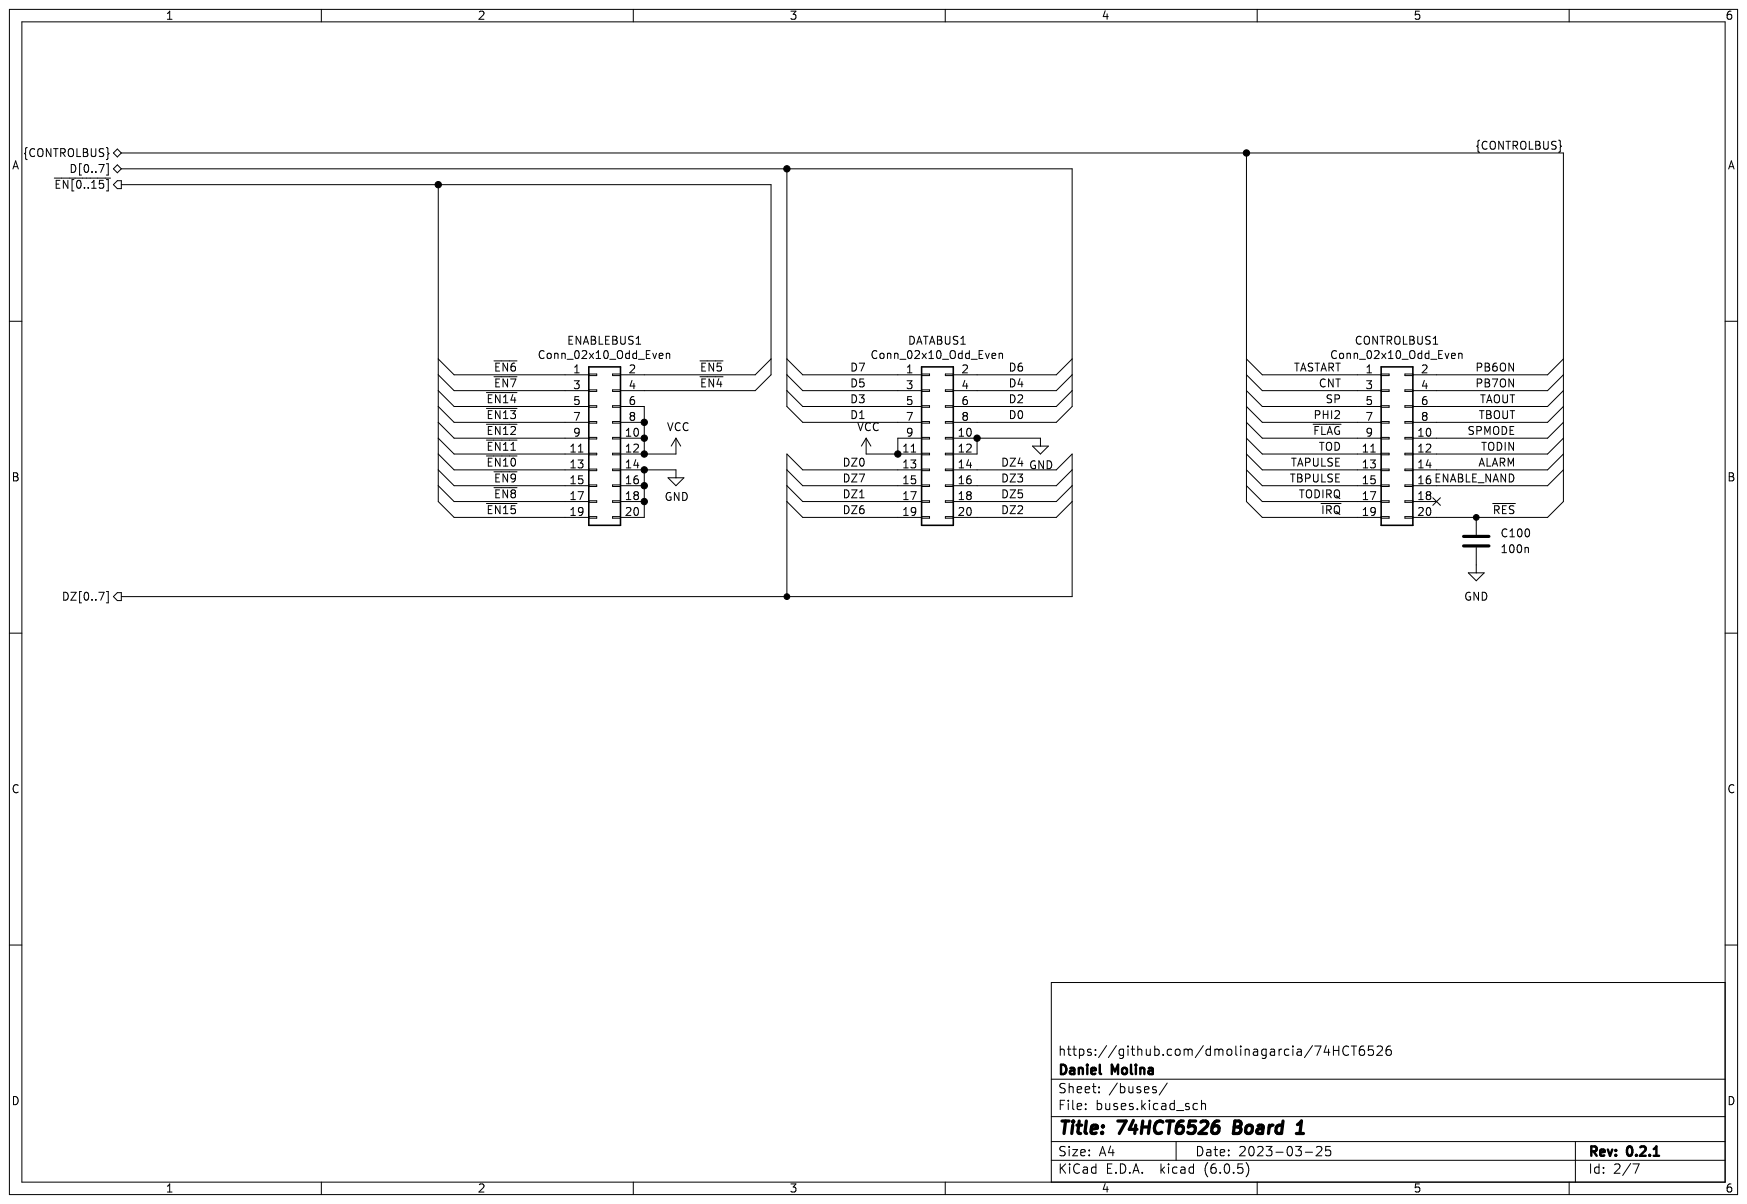
[picture p166: page 2]

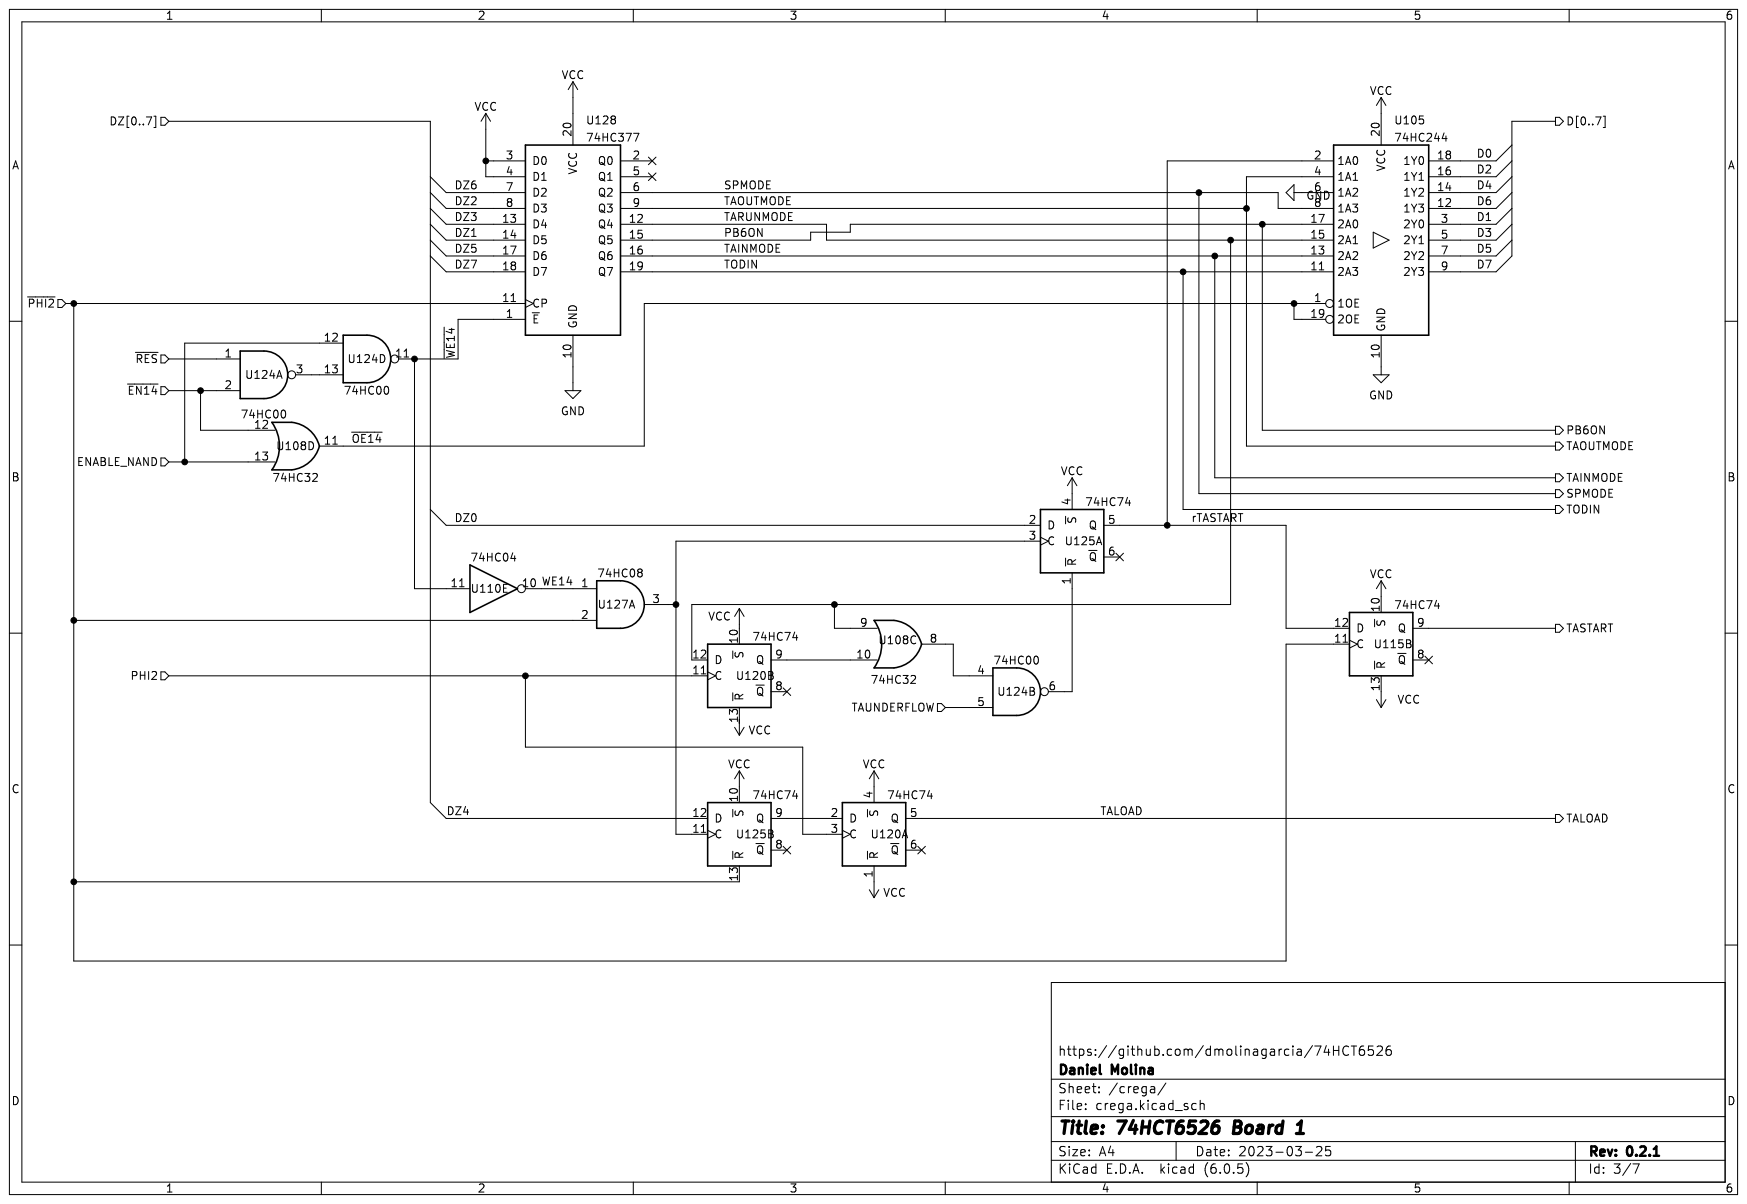
[picture p167: page 3]

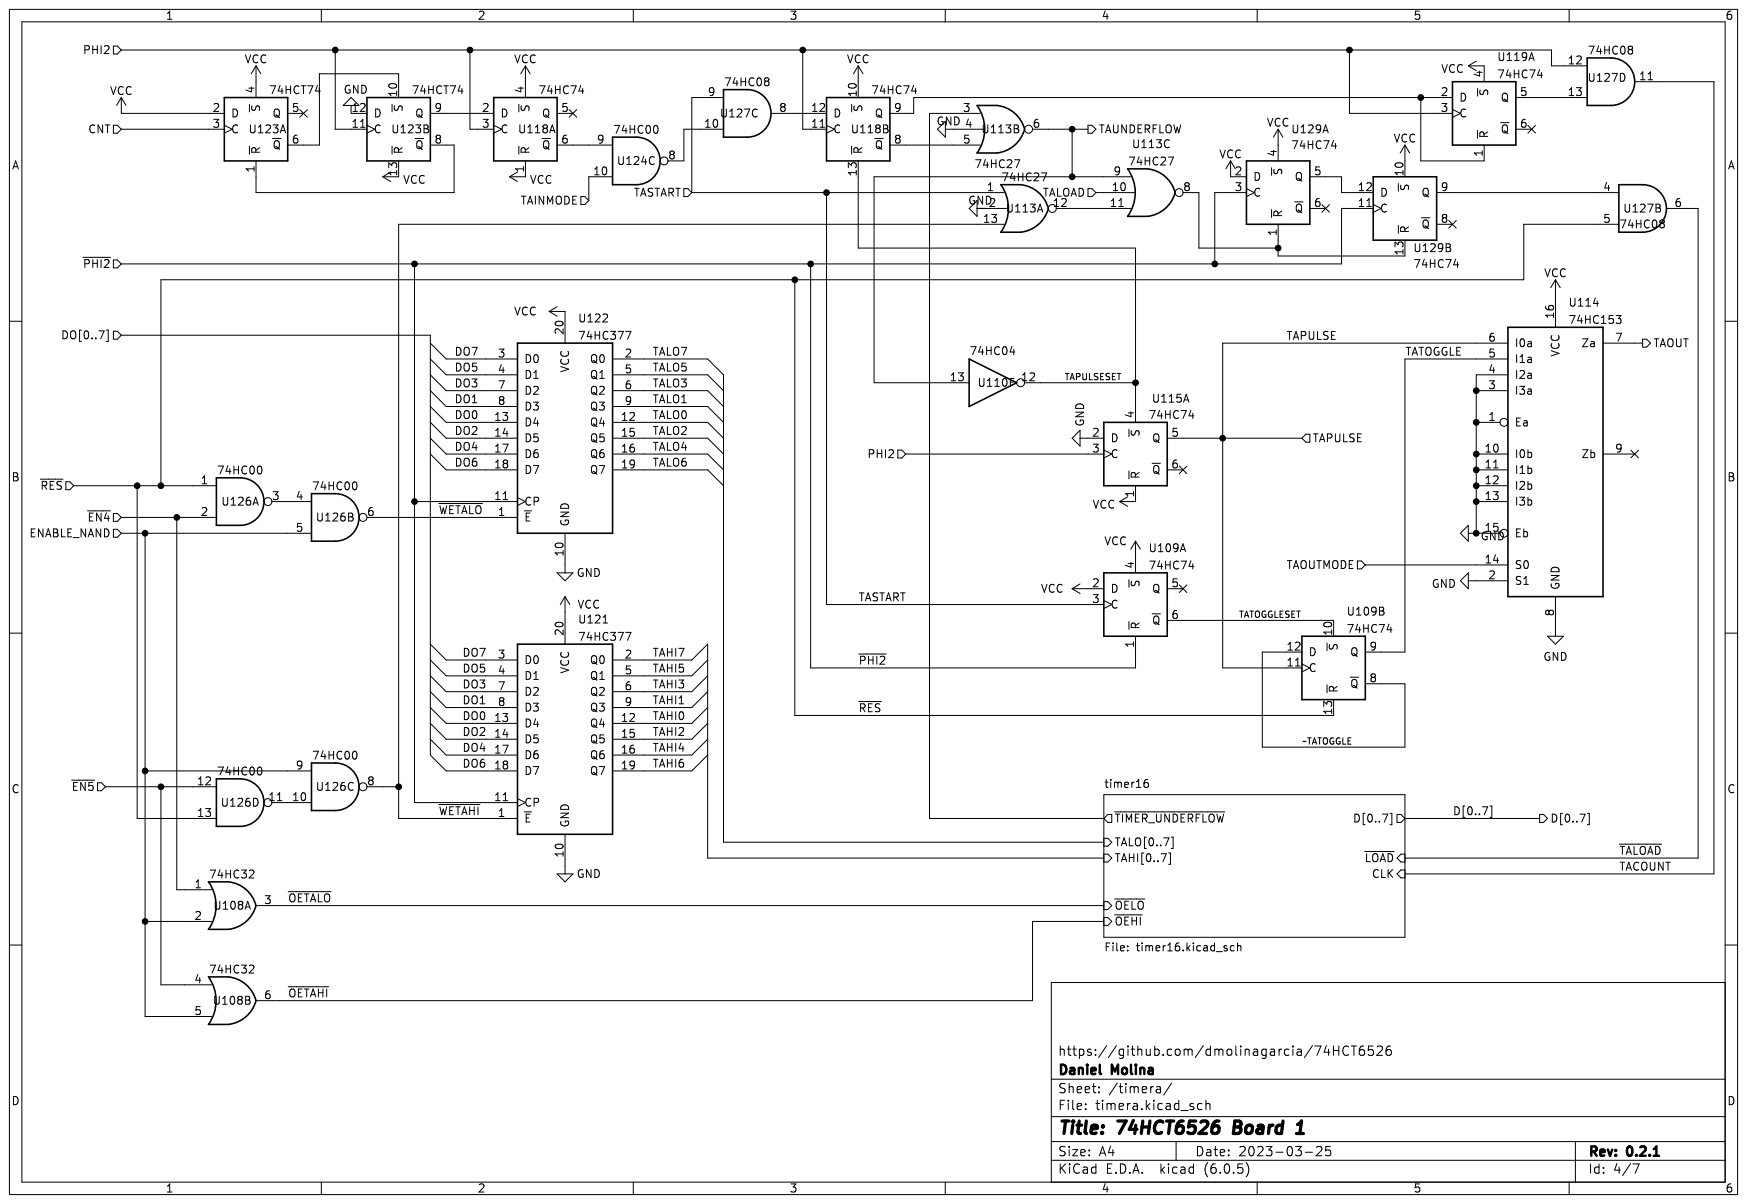
[picture p168: page 4]

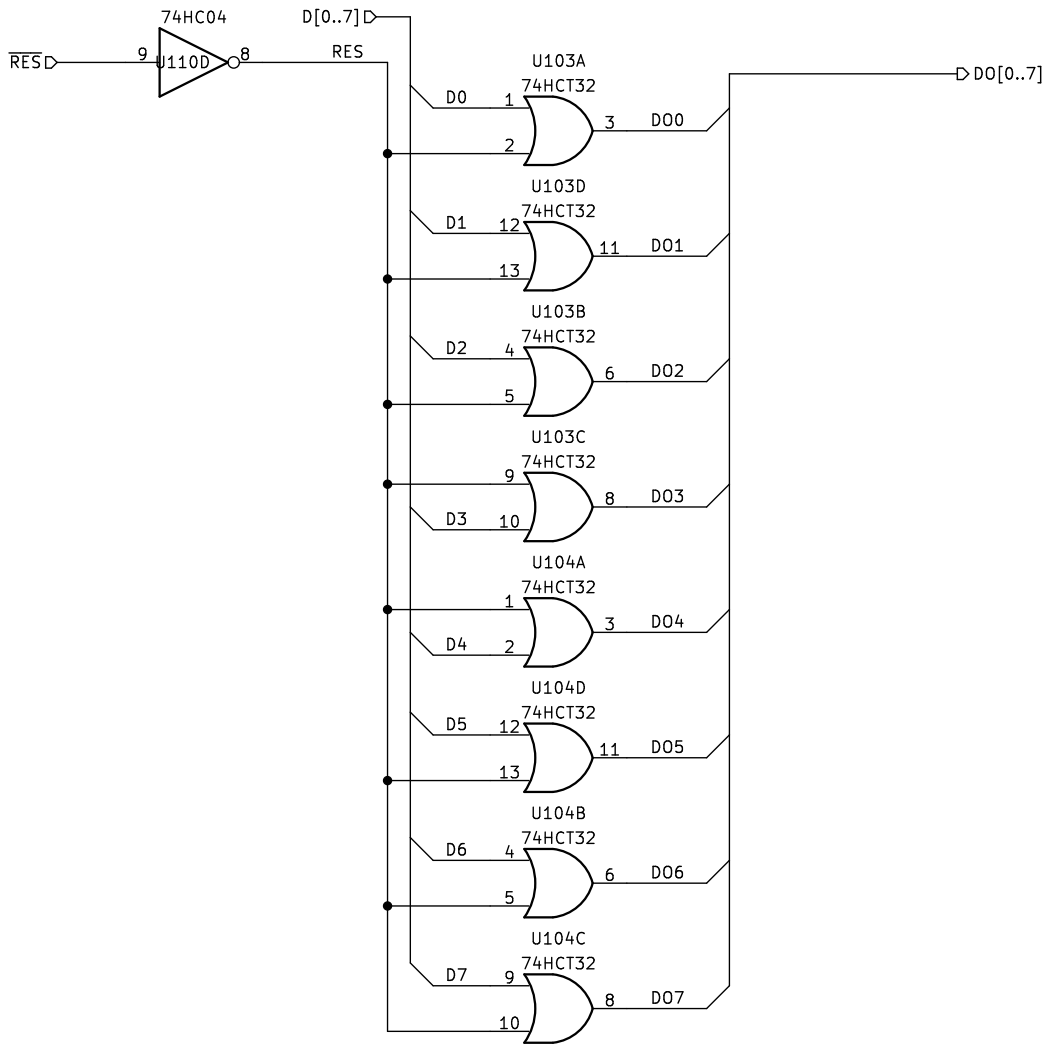
[picture p169: page 5]

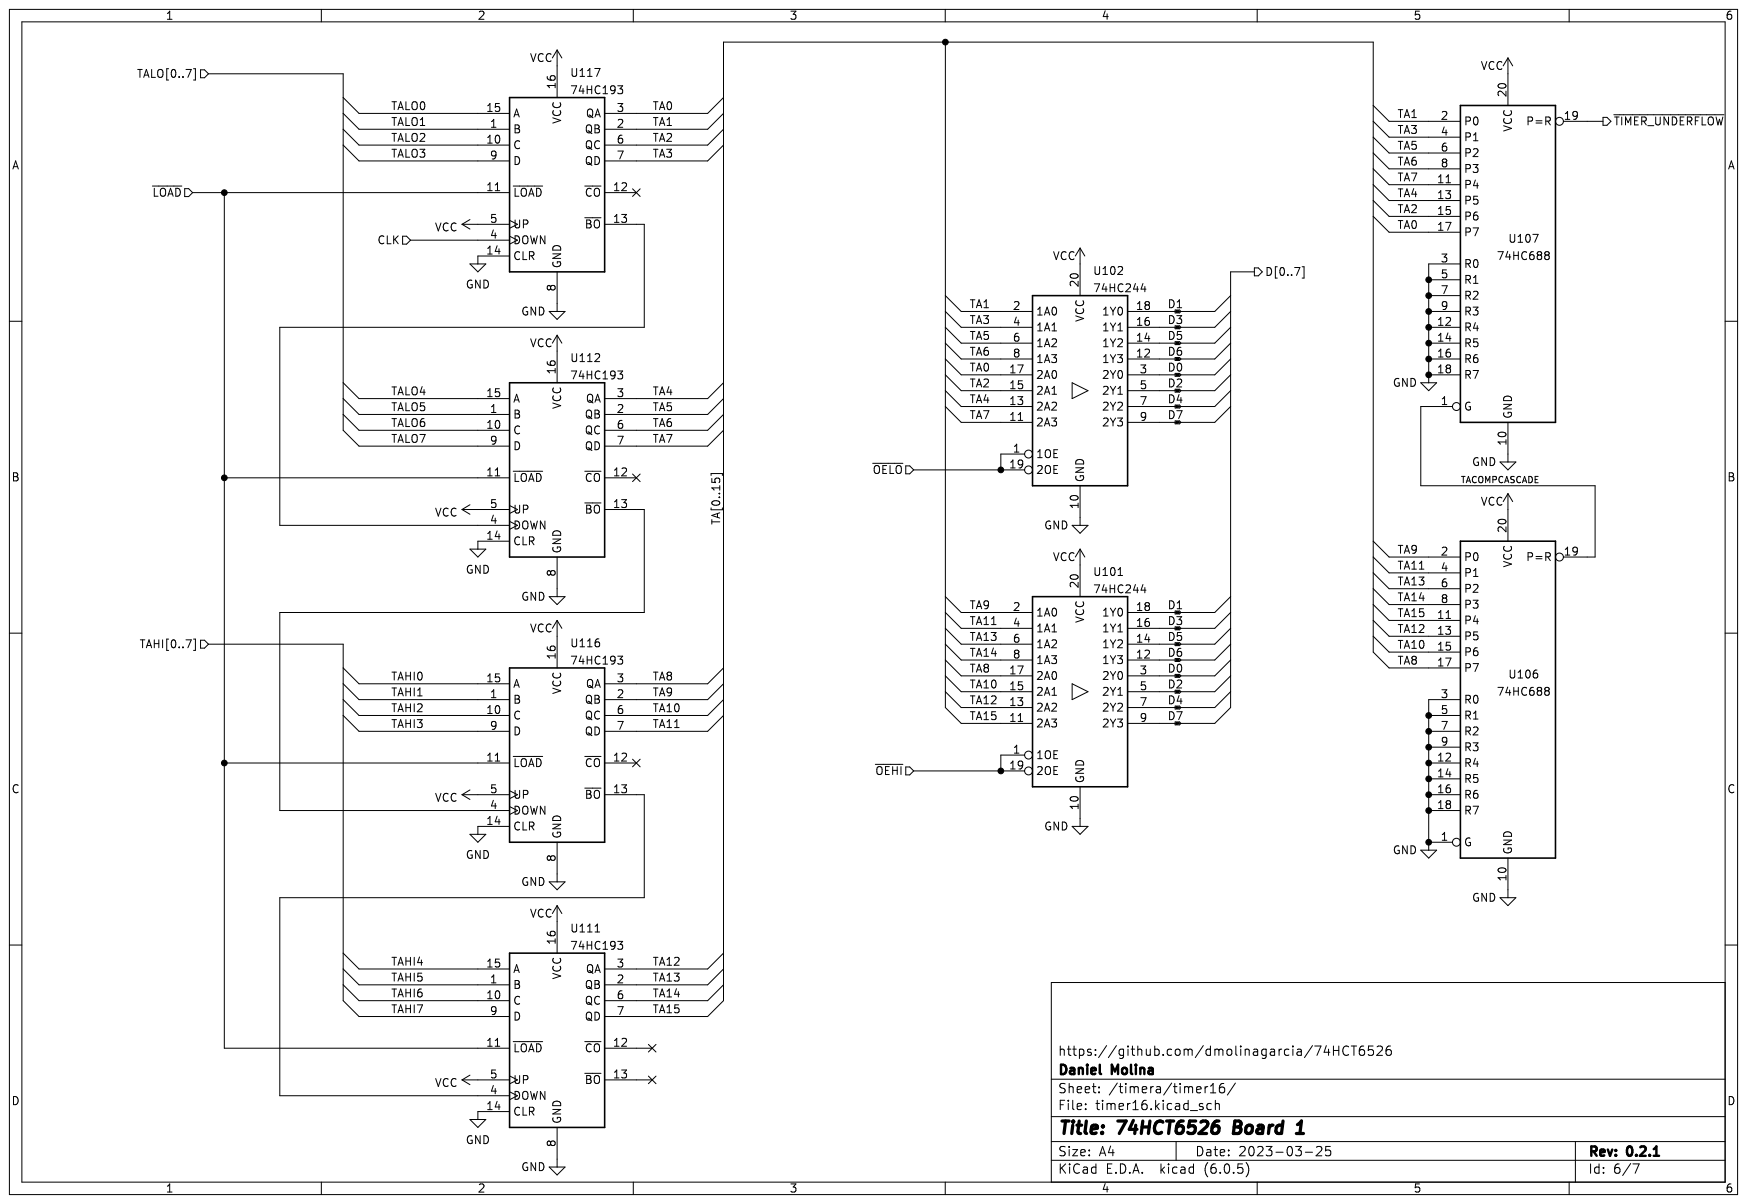
[picture p170: page 6]

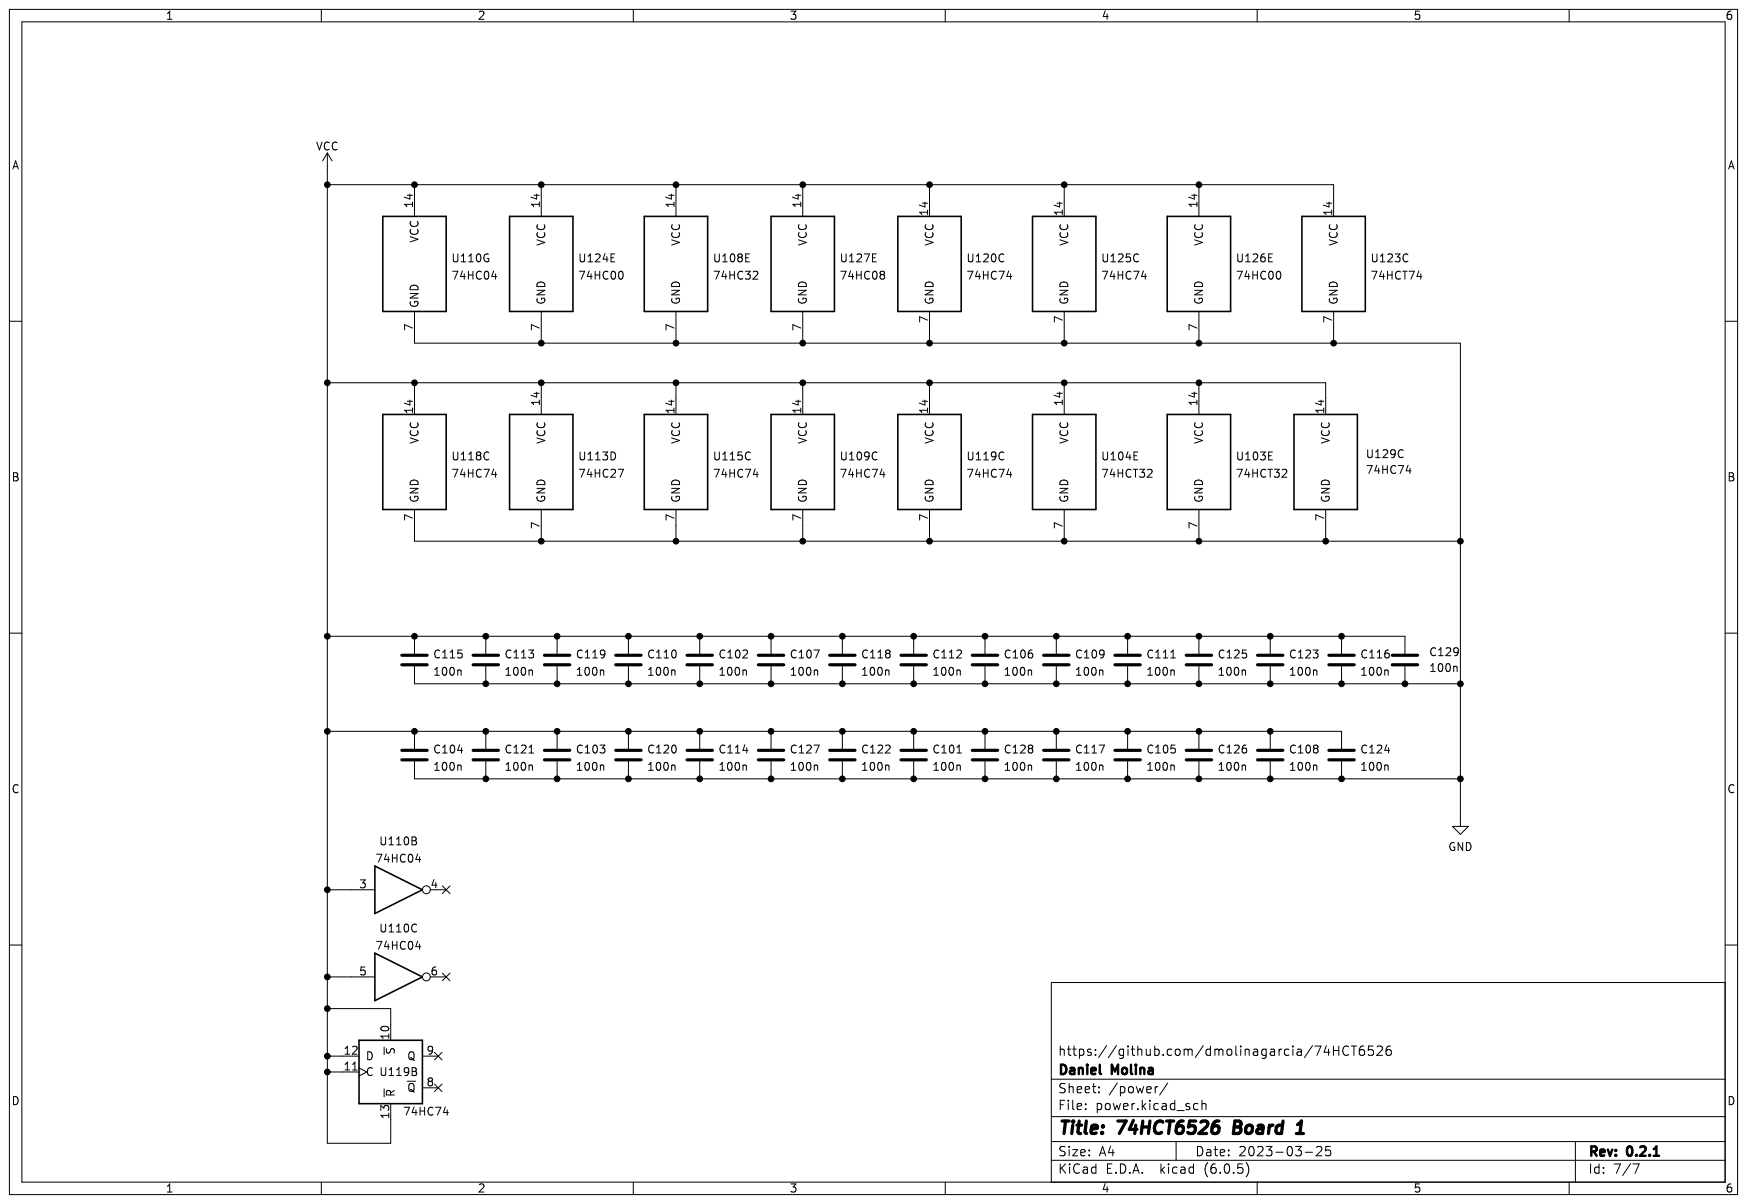
[picture p171: page 7]
