dmolinagarcia/74HCT6526/pdf/B2.pcb.v0.2.1.pdf

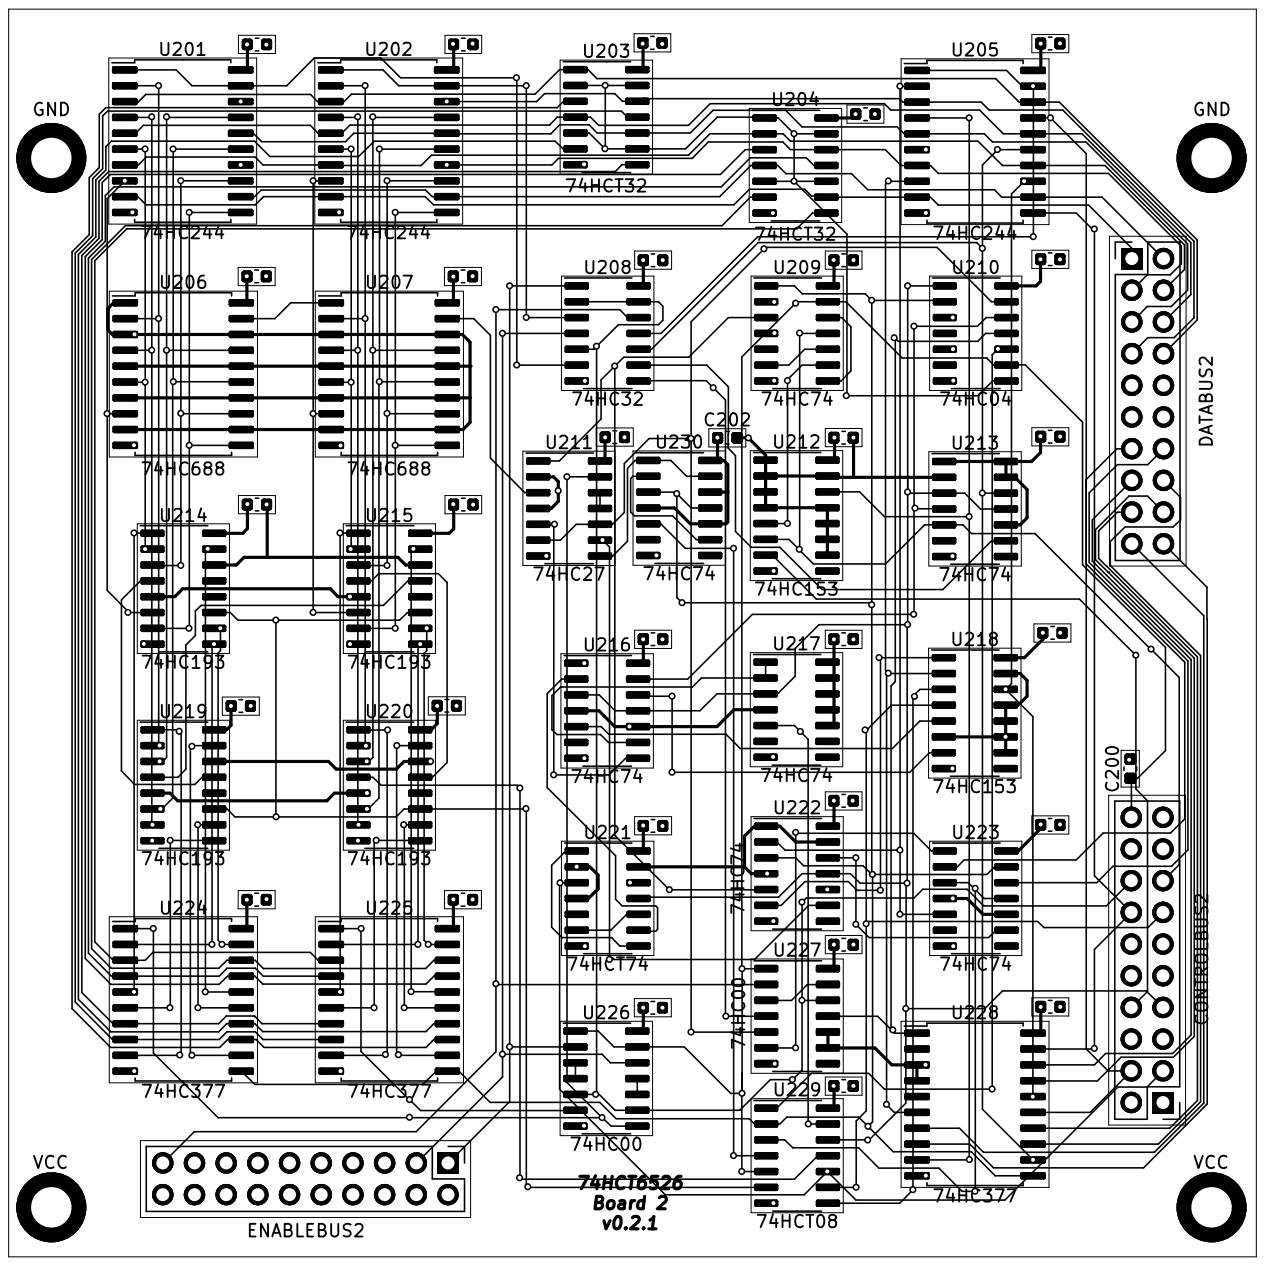
[picture p172: page 1]
