dmolinagarcia/74HCT6526/pdf/B2.sch.v0.2.1.pdf

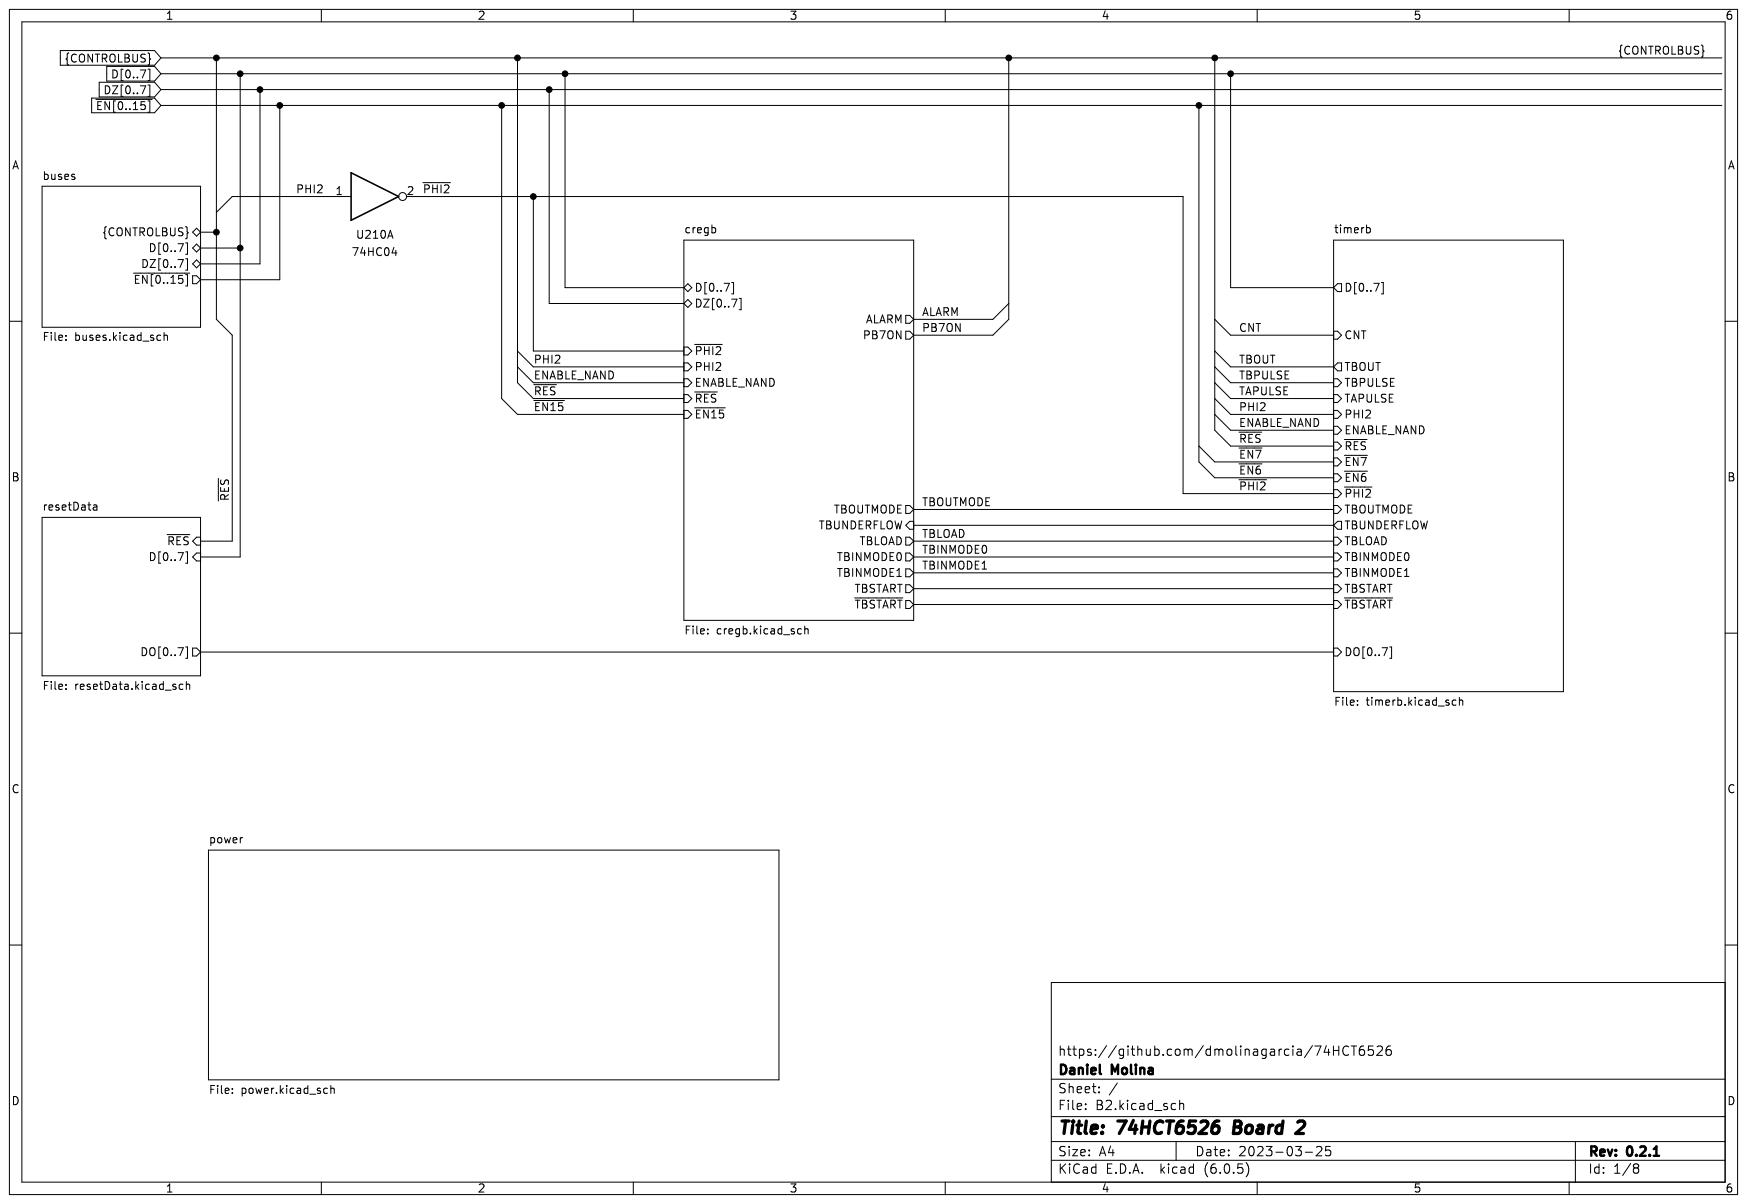
[picture p173: page 1]


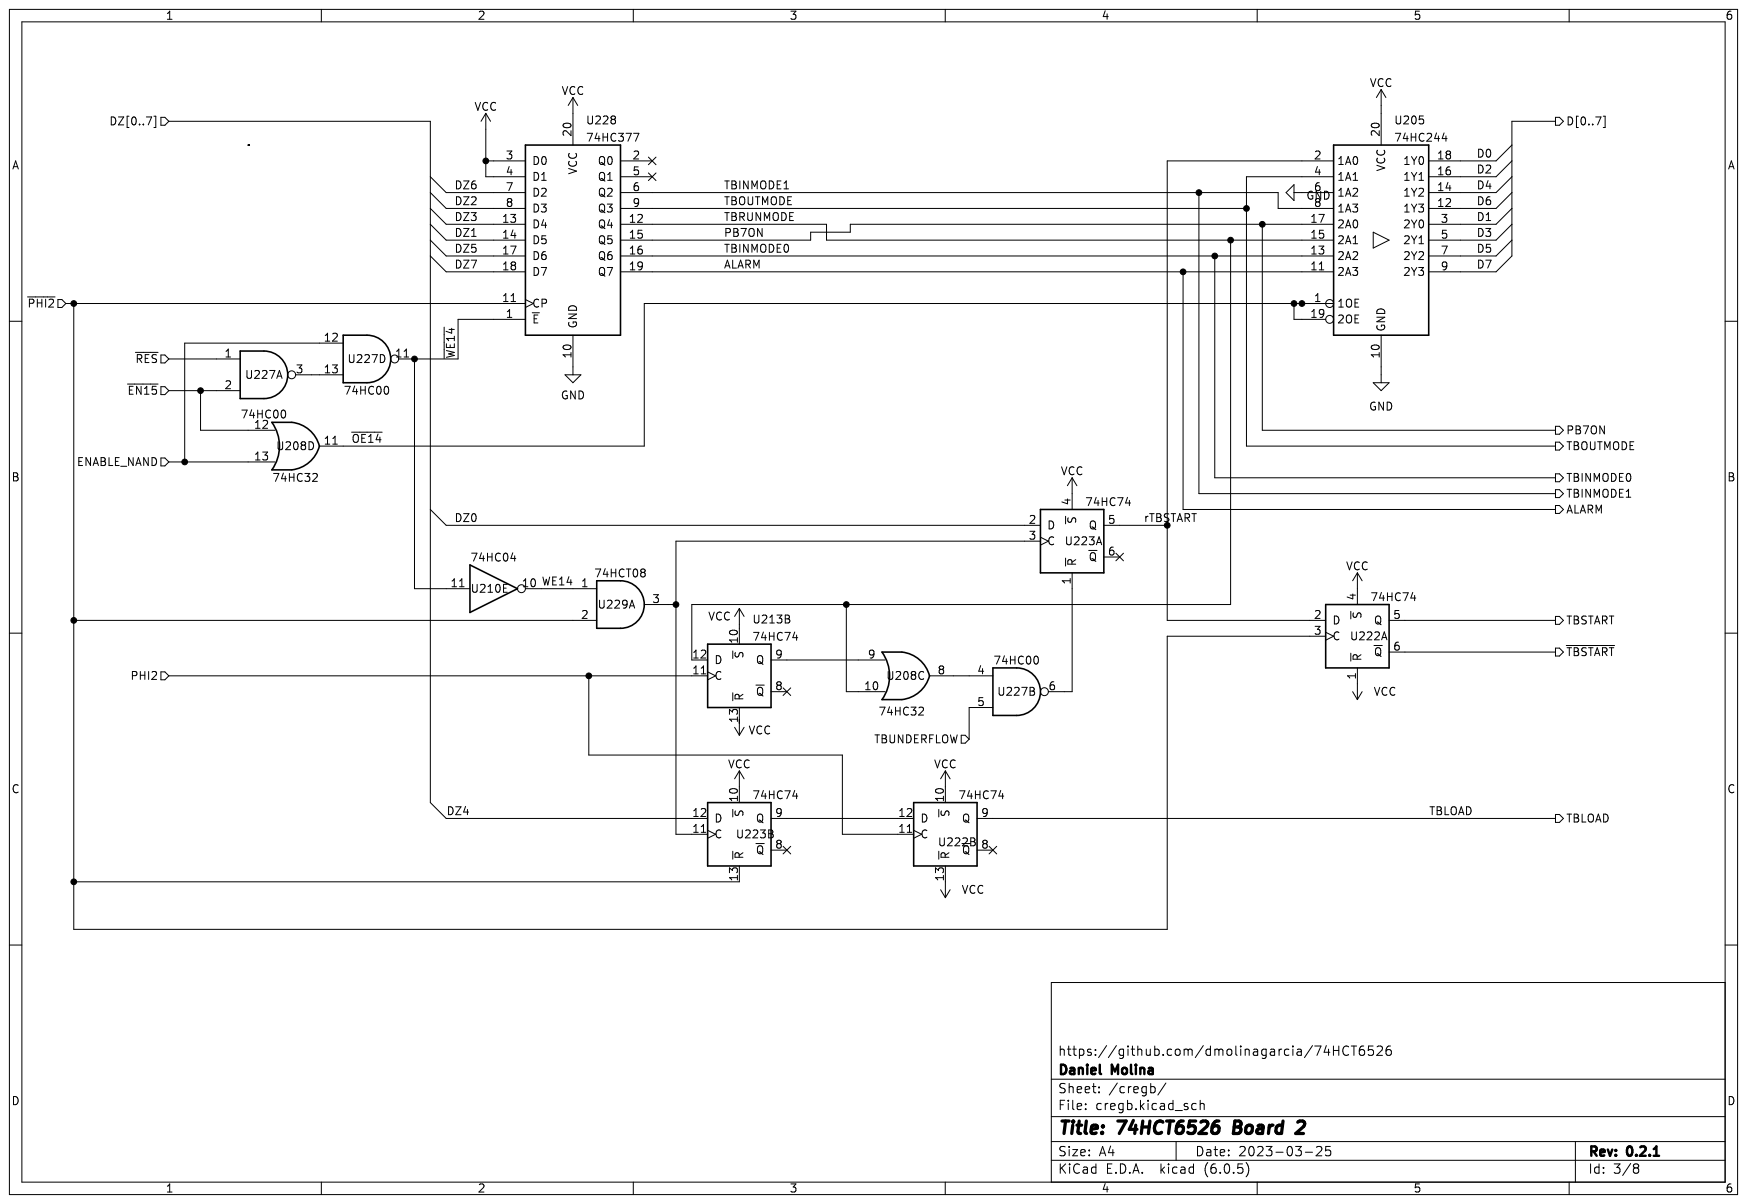
[picture p174: page 3]

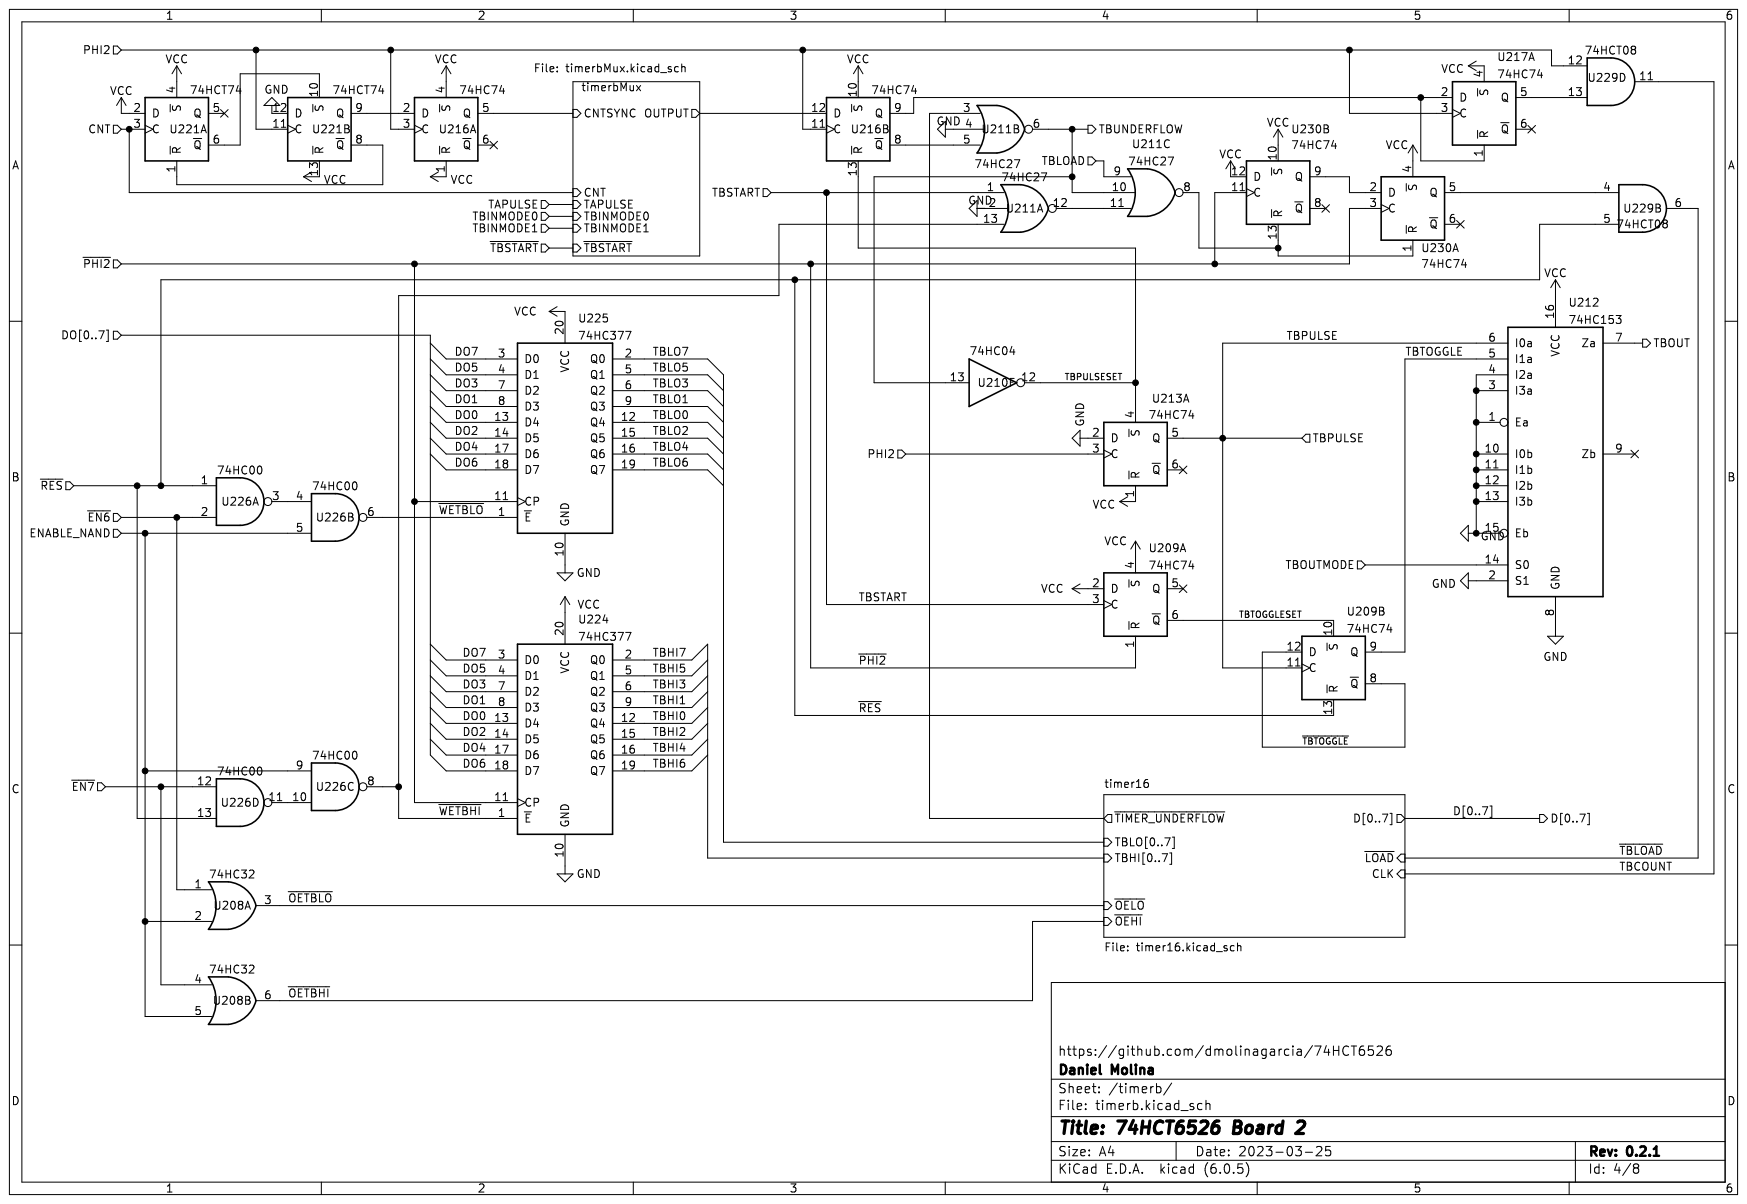
[picture p175: page 4]

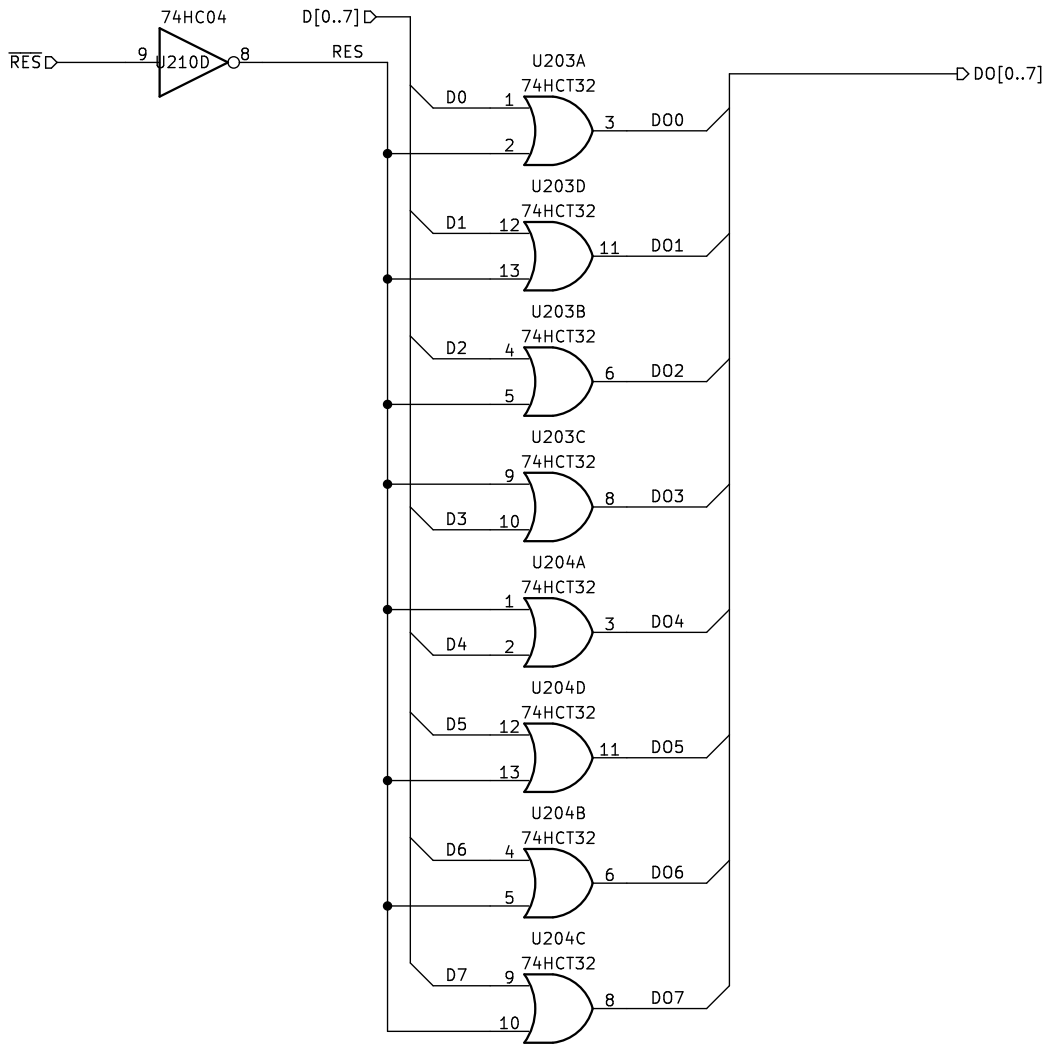
[picture p176: page 5]

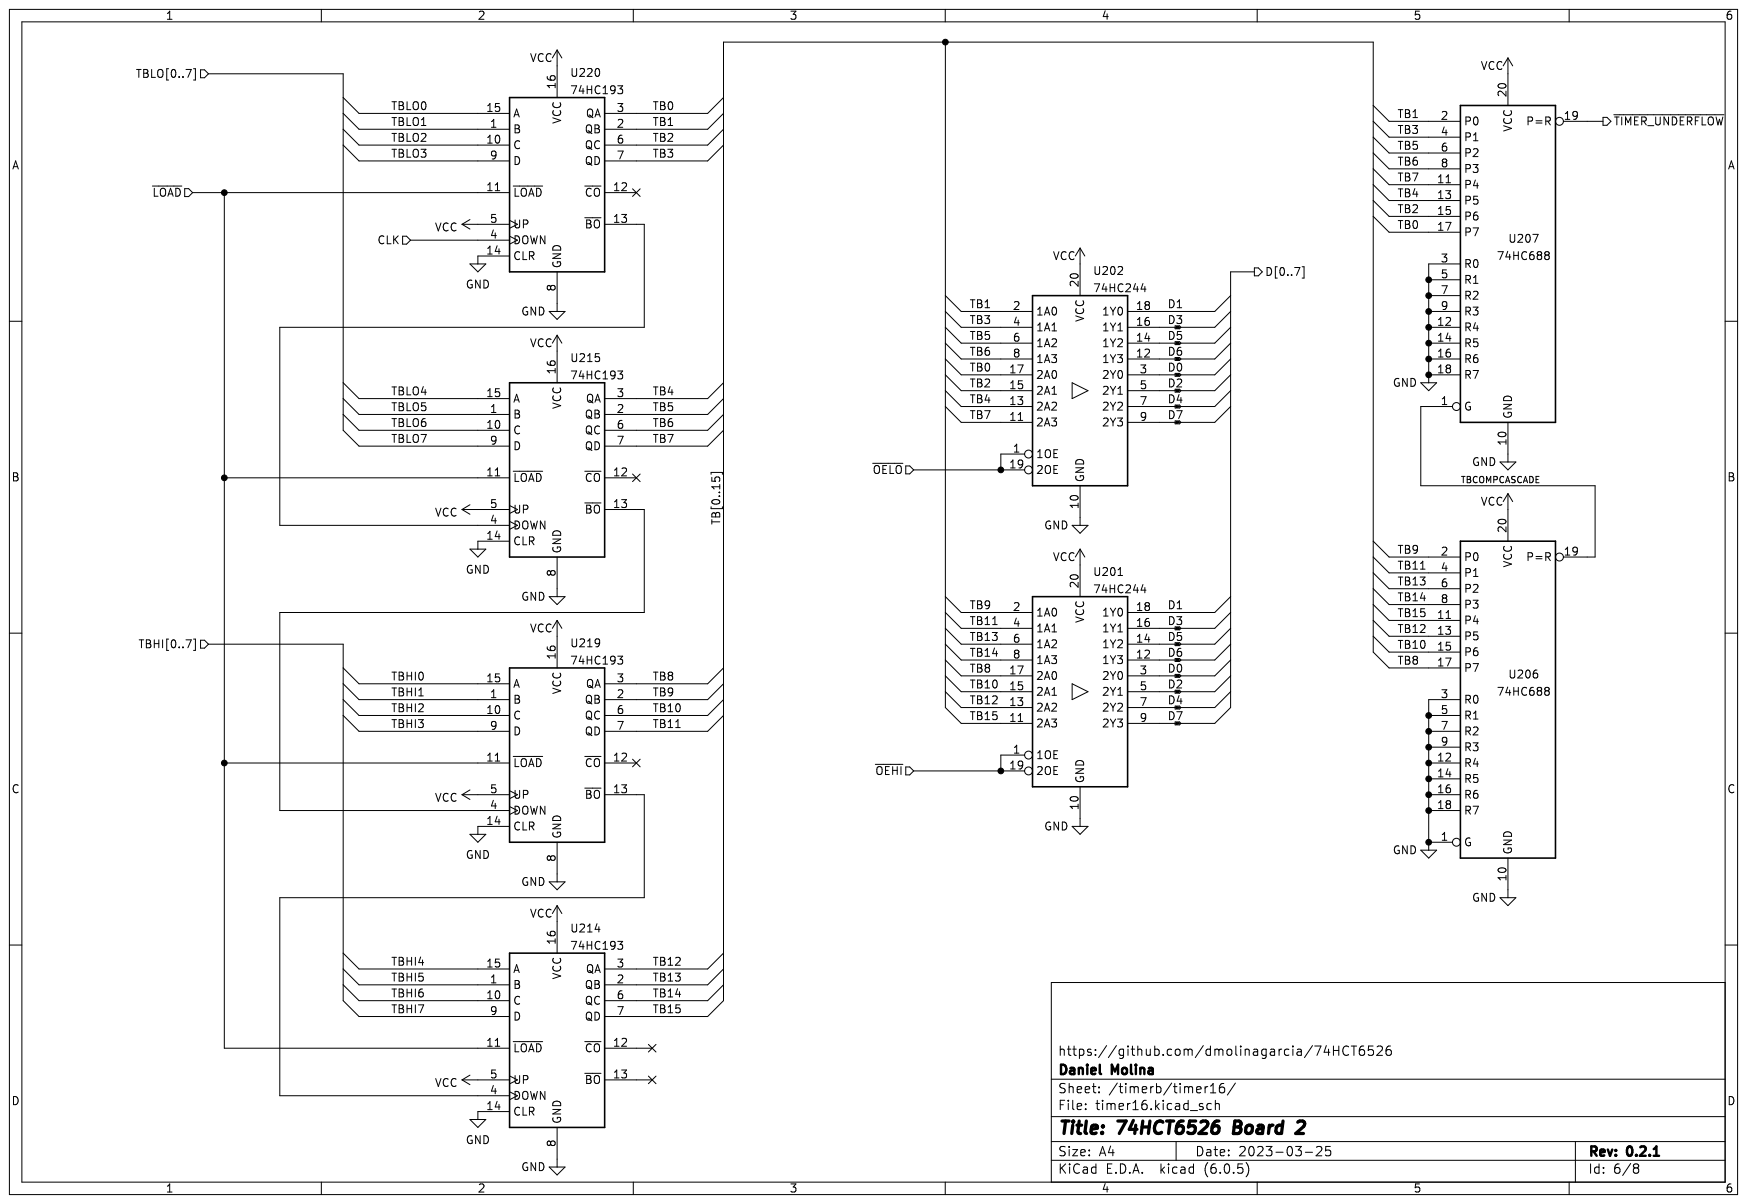
[picture p177: page 6]

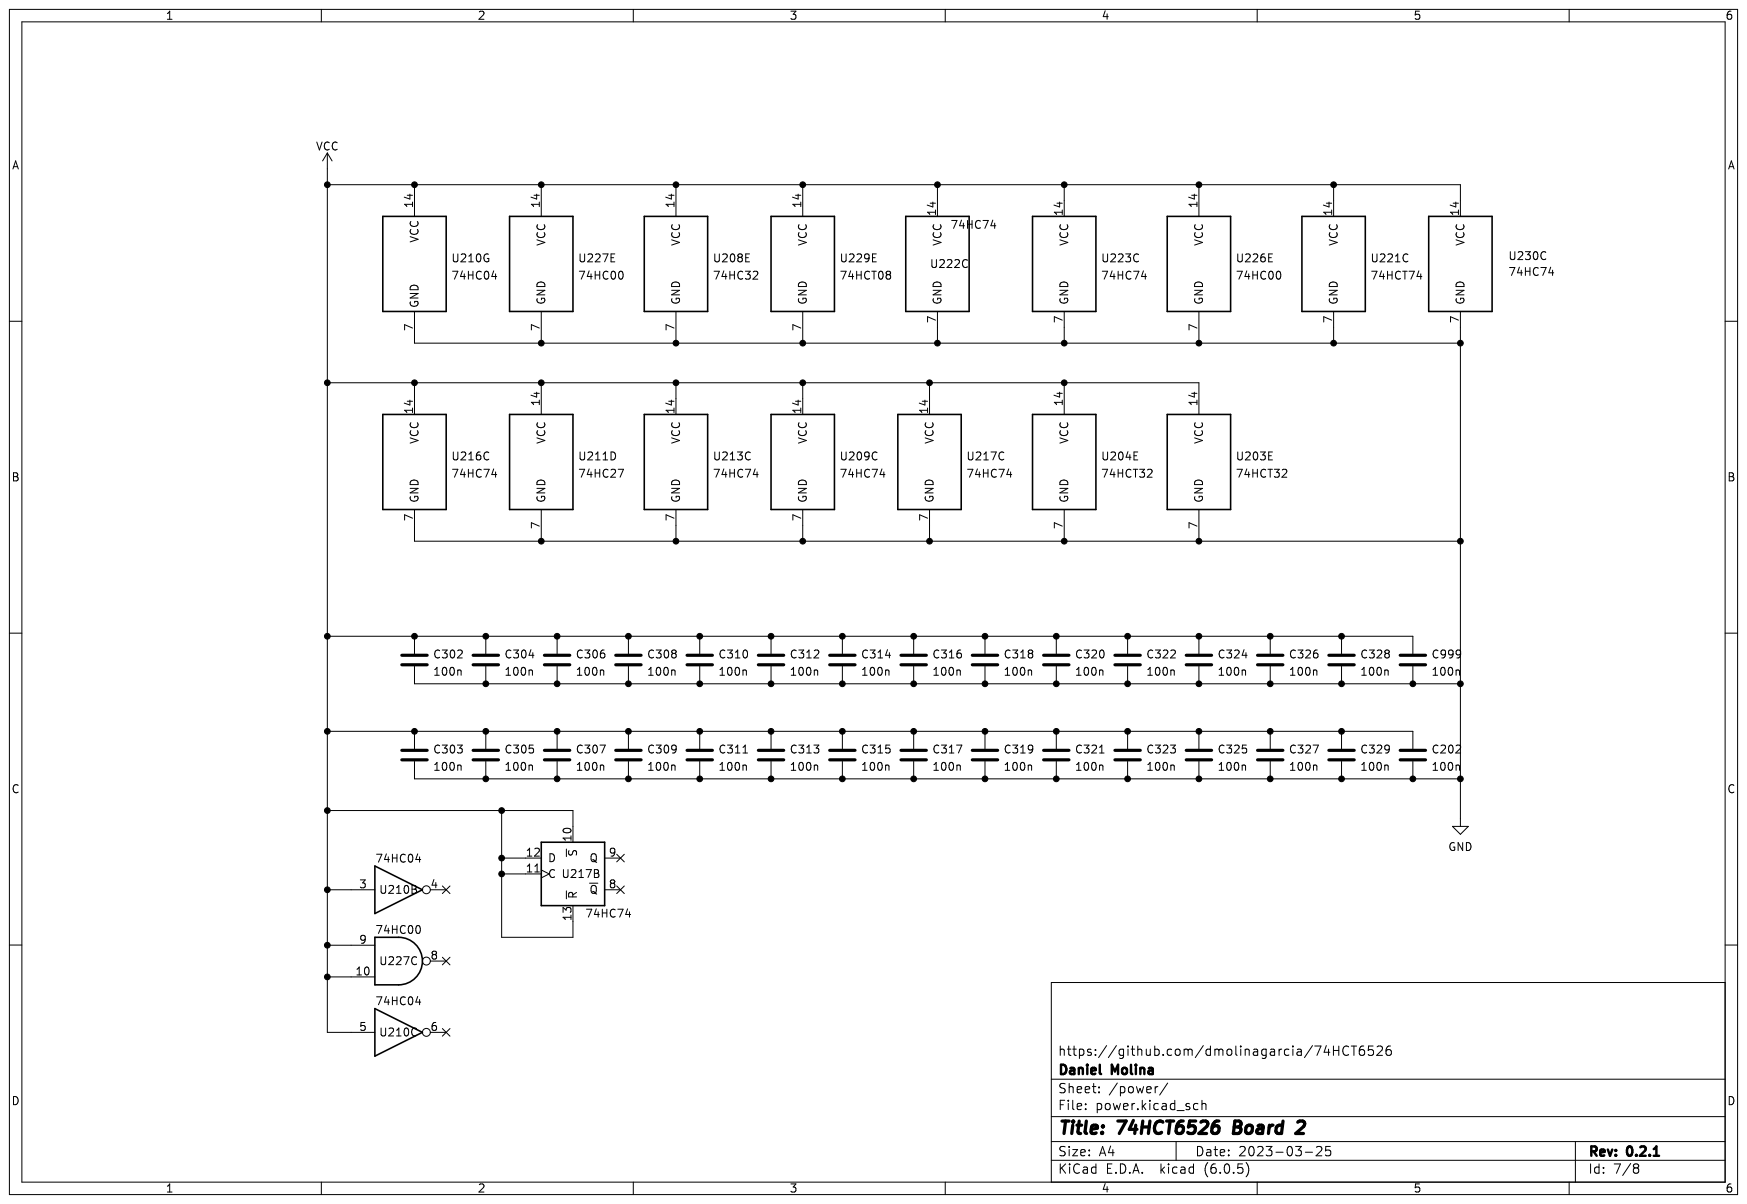
[picture p178: page 7]
