dmolinagarcia/74HCT6526/pdf/B3.pcb.v0.2.1.pdf

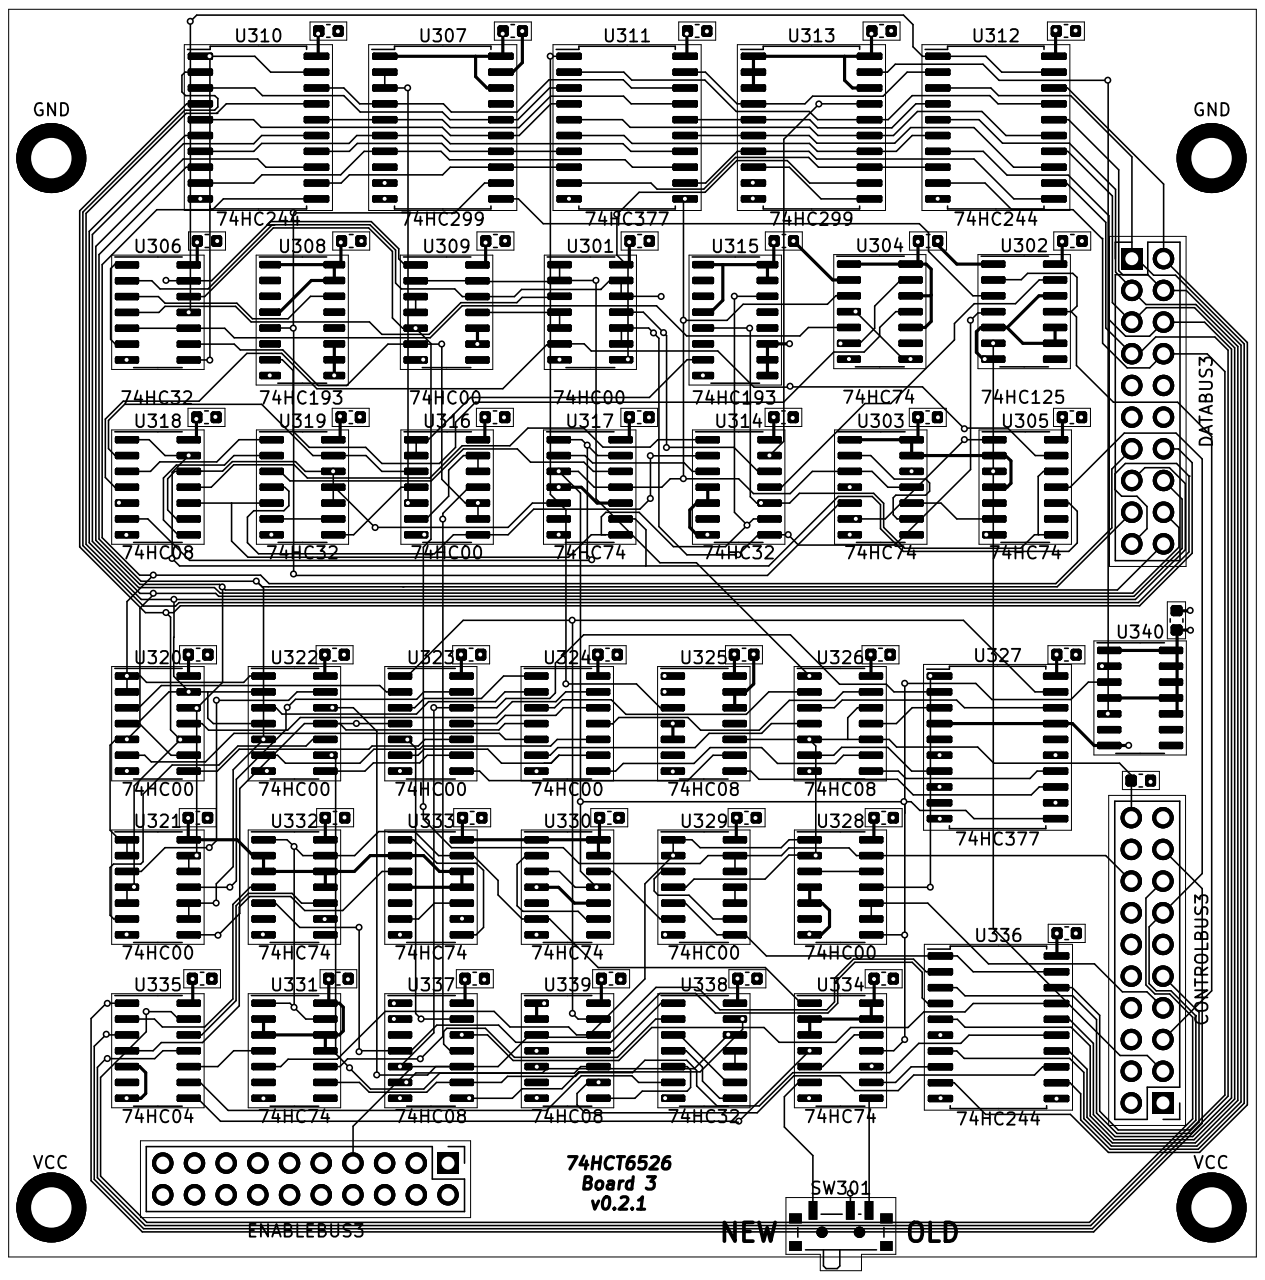
[picture p179: page 1]
