dmolinagarcia/74HCT6526/pdf/B3.sch.v0.2.1.pdf

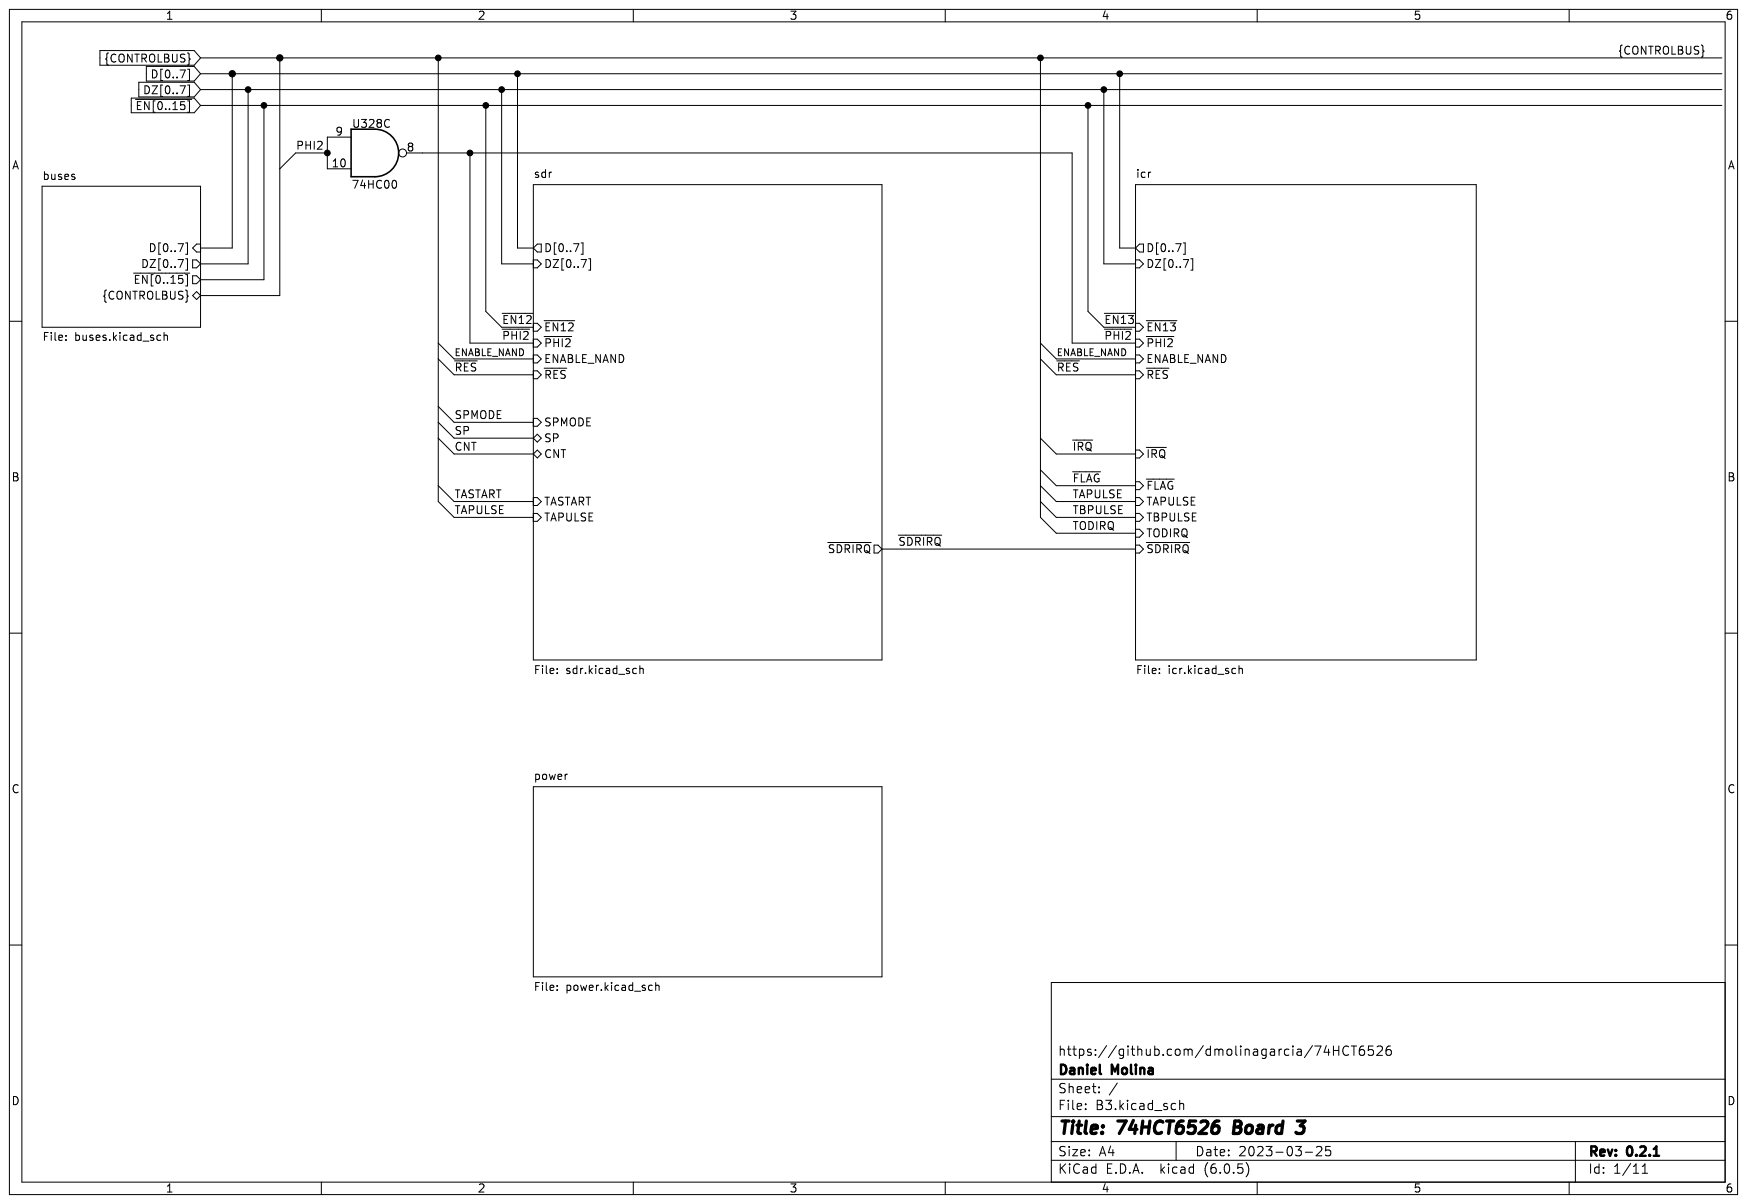
[picture p180: page 1]


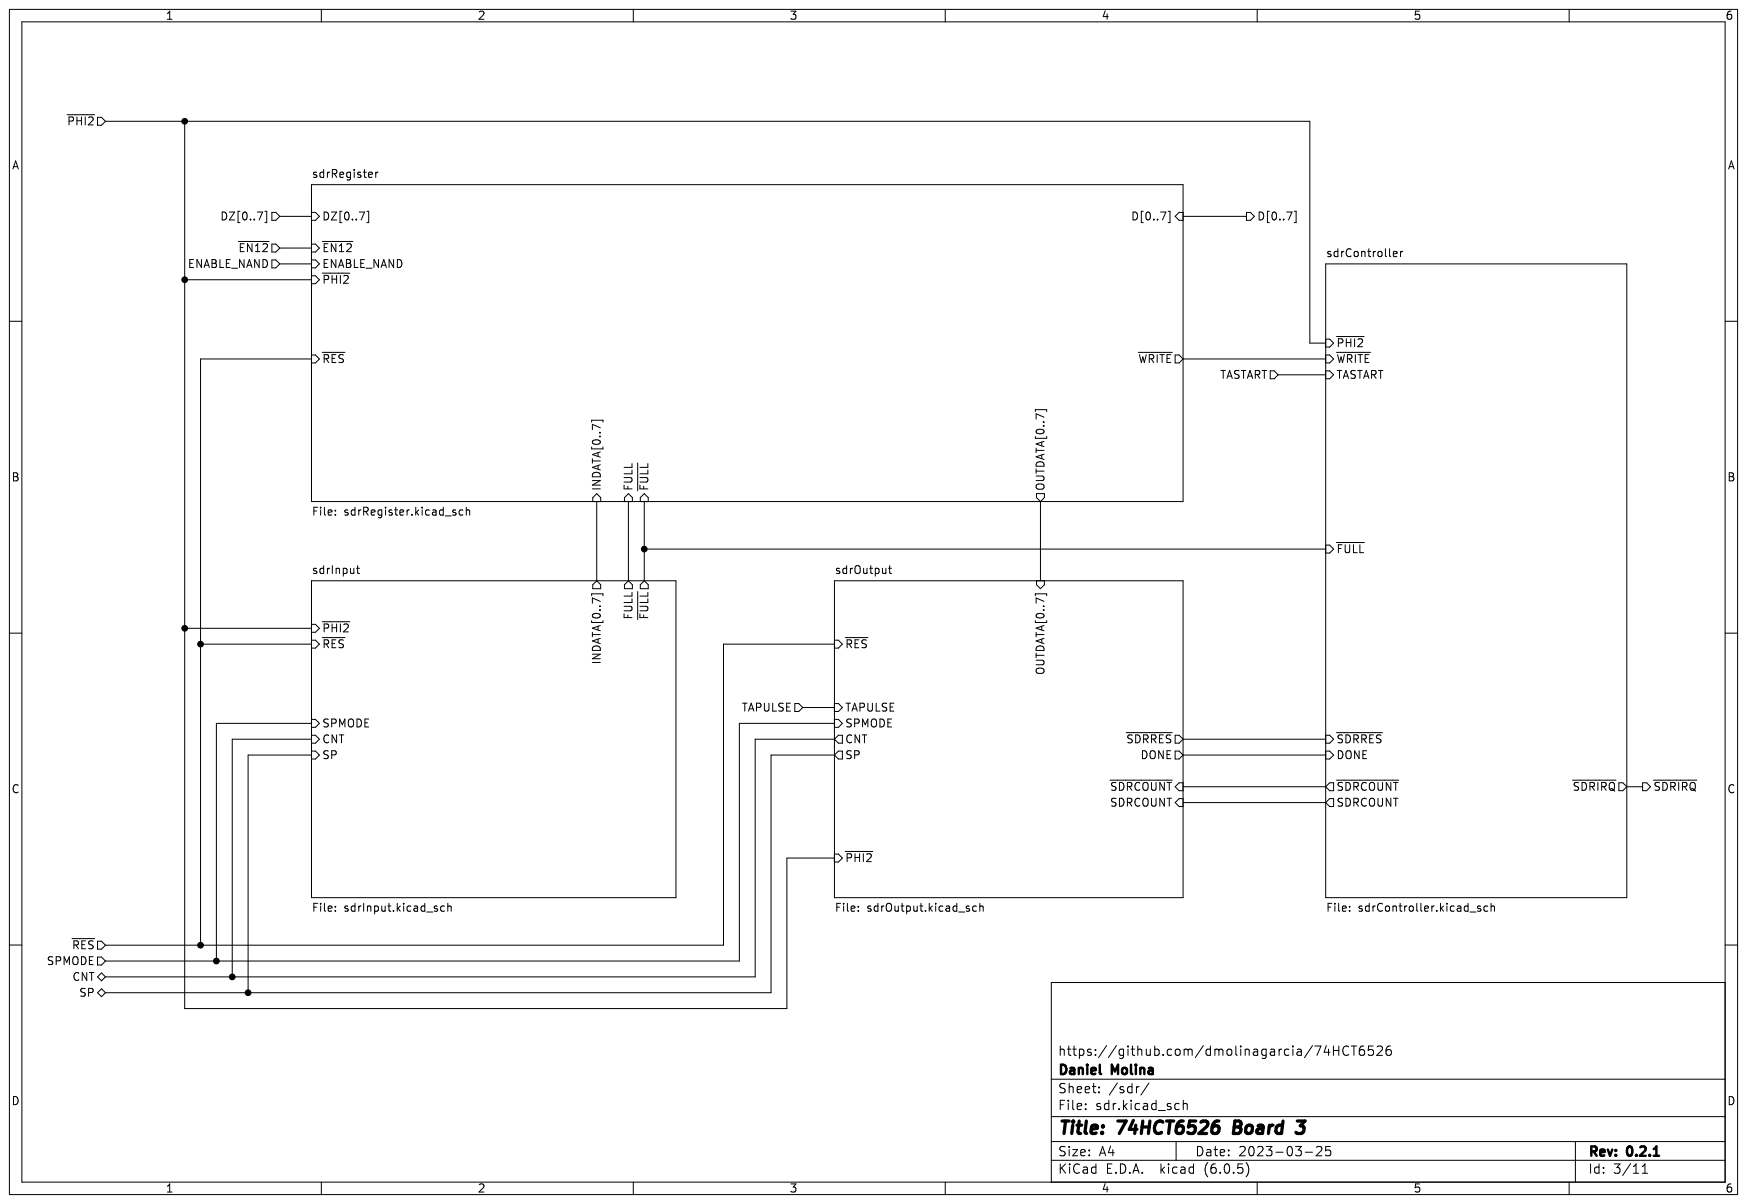
[picture p181: page 3]

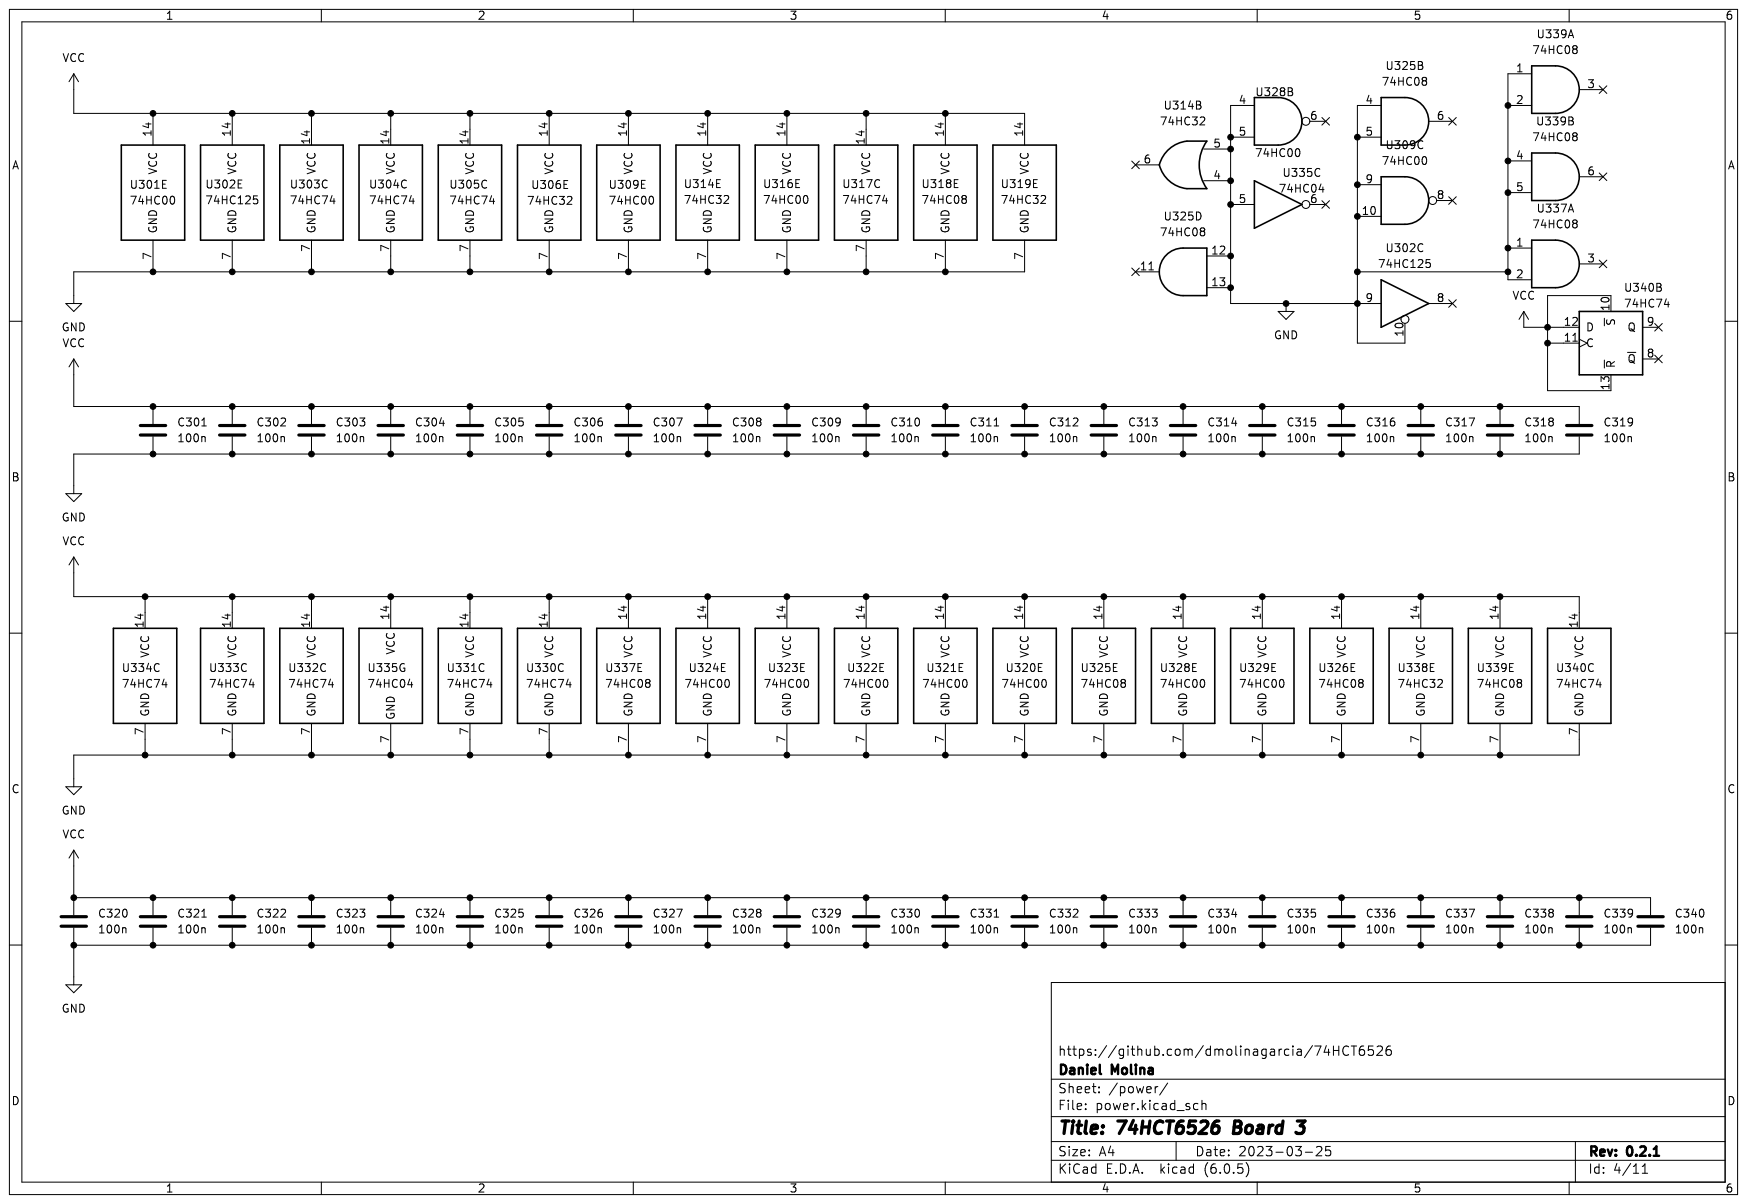
[picture p182: page 4]

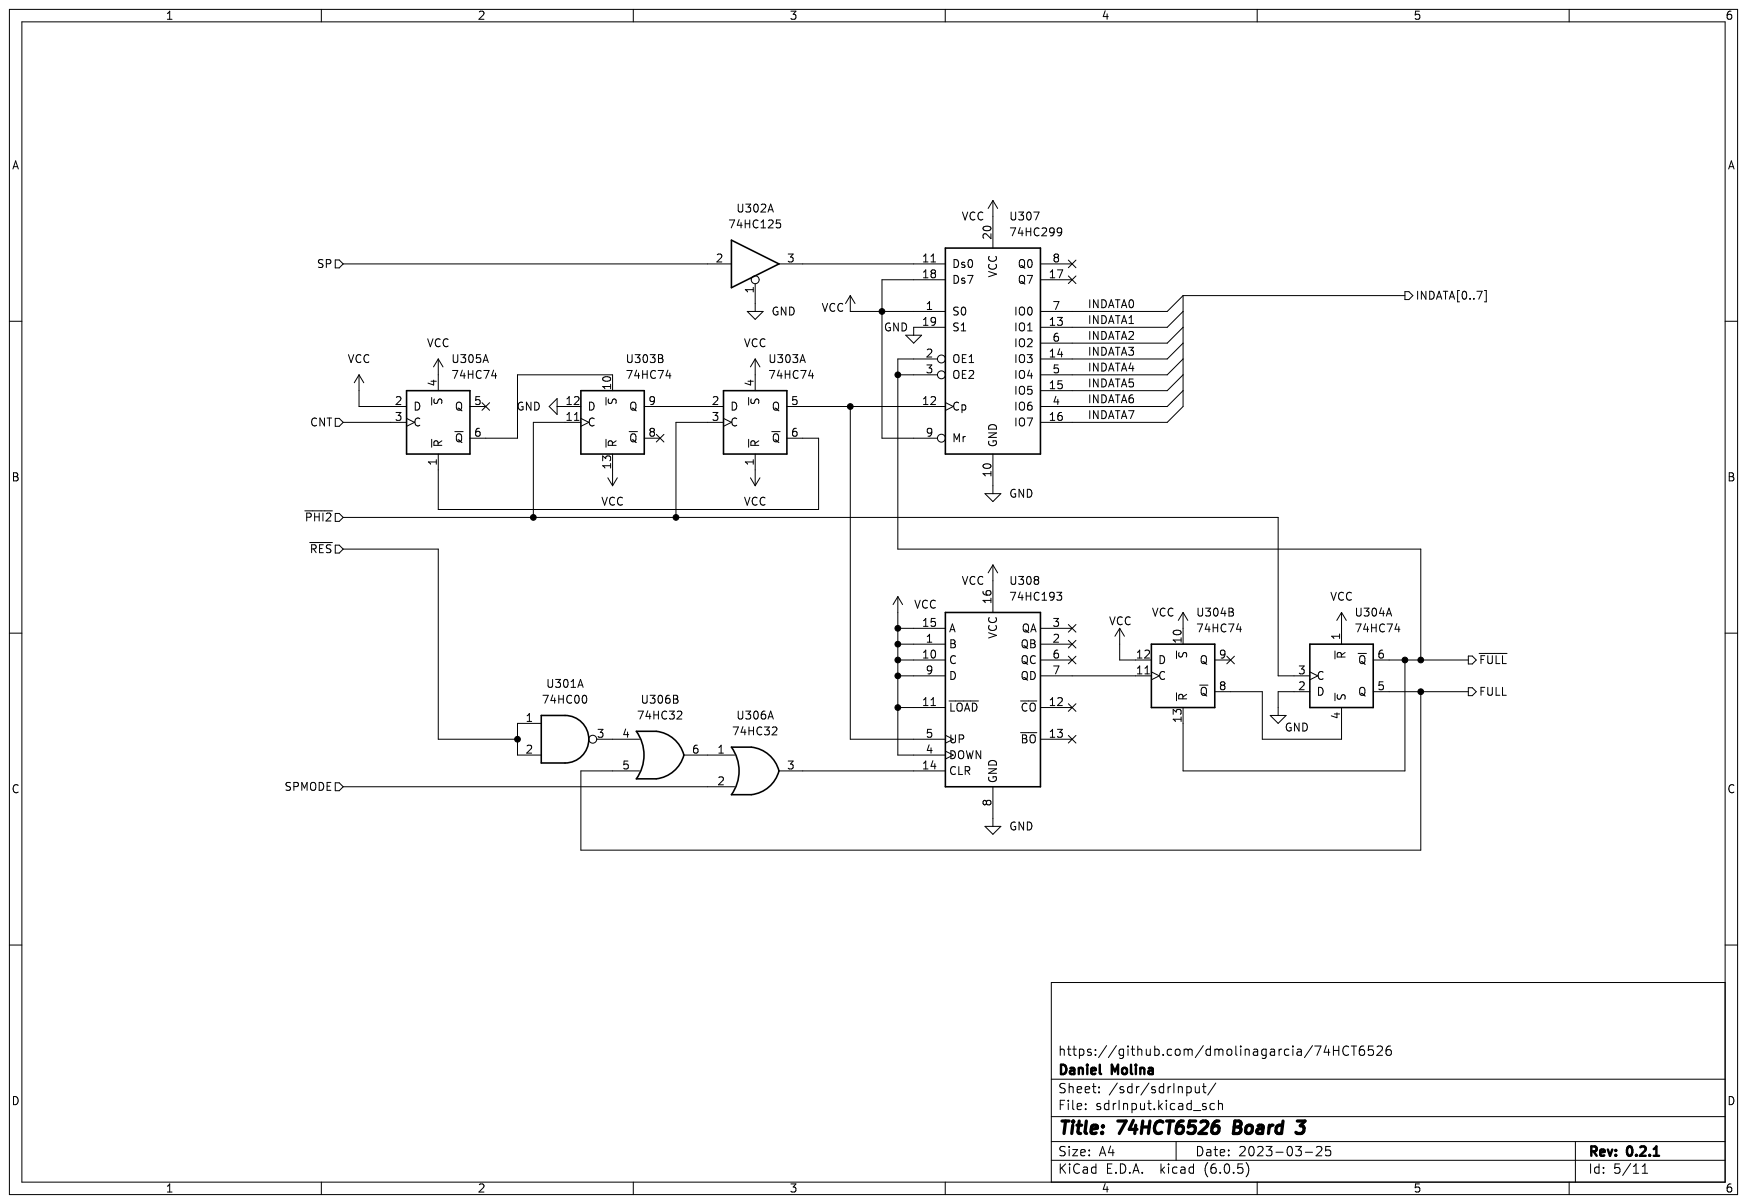
[picture p183: page 5]

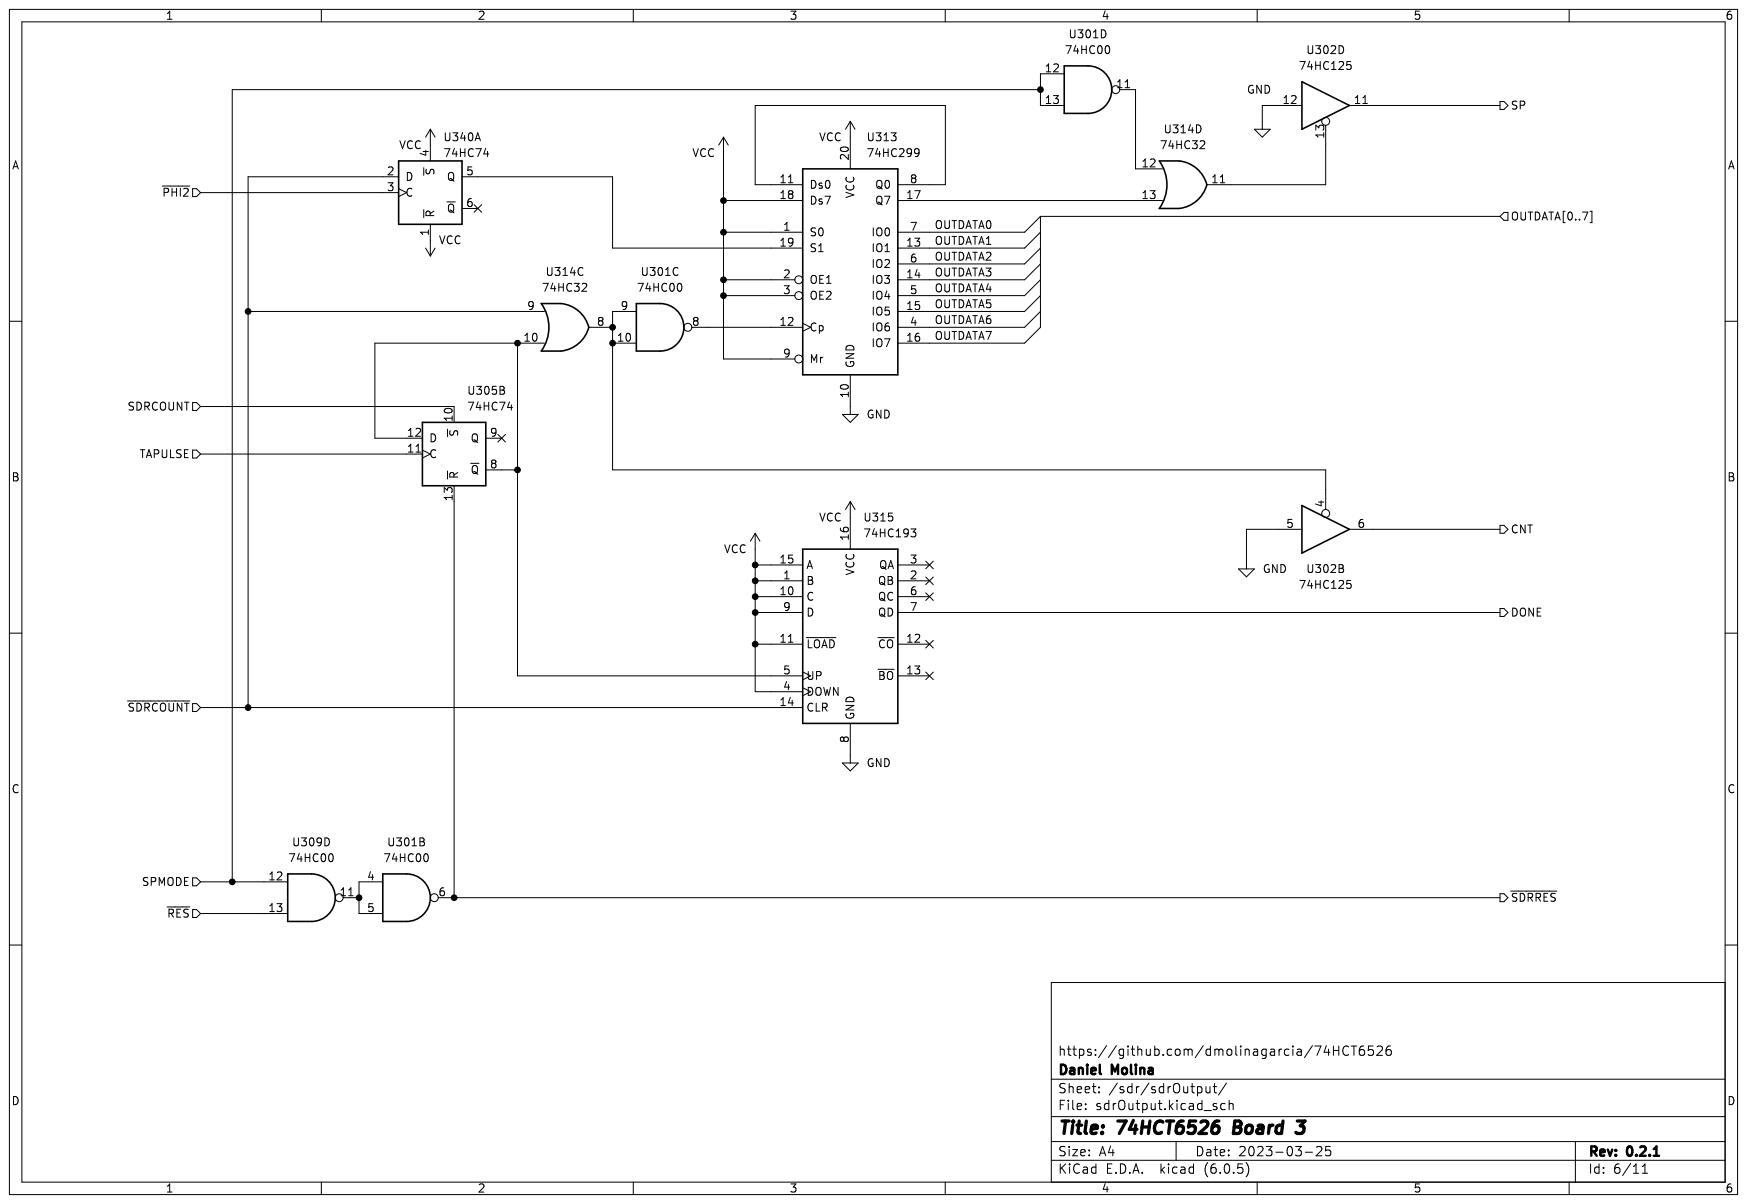
[picture p184: page 6]

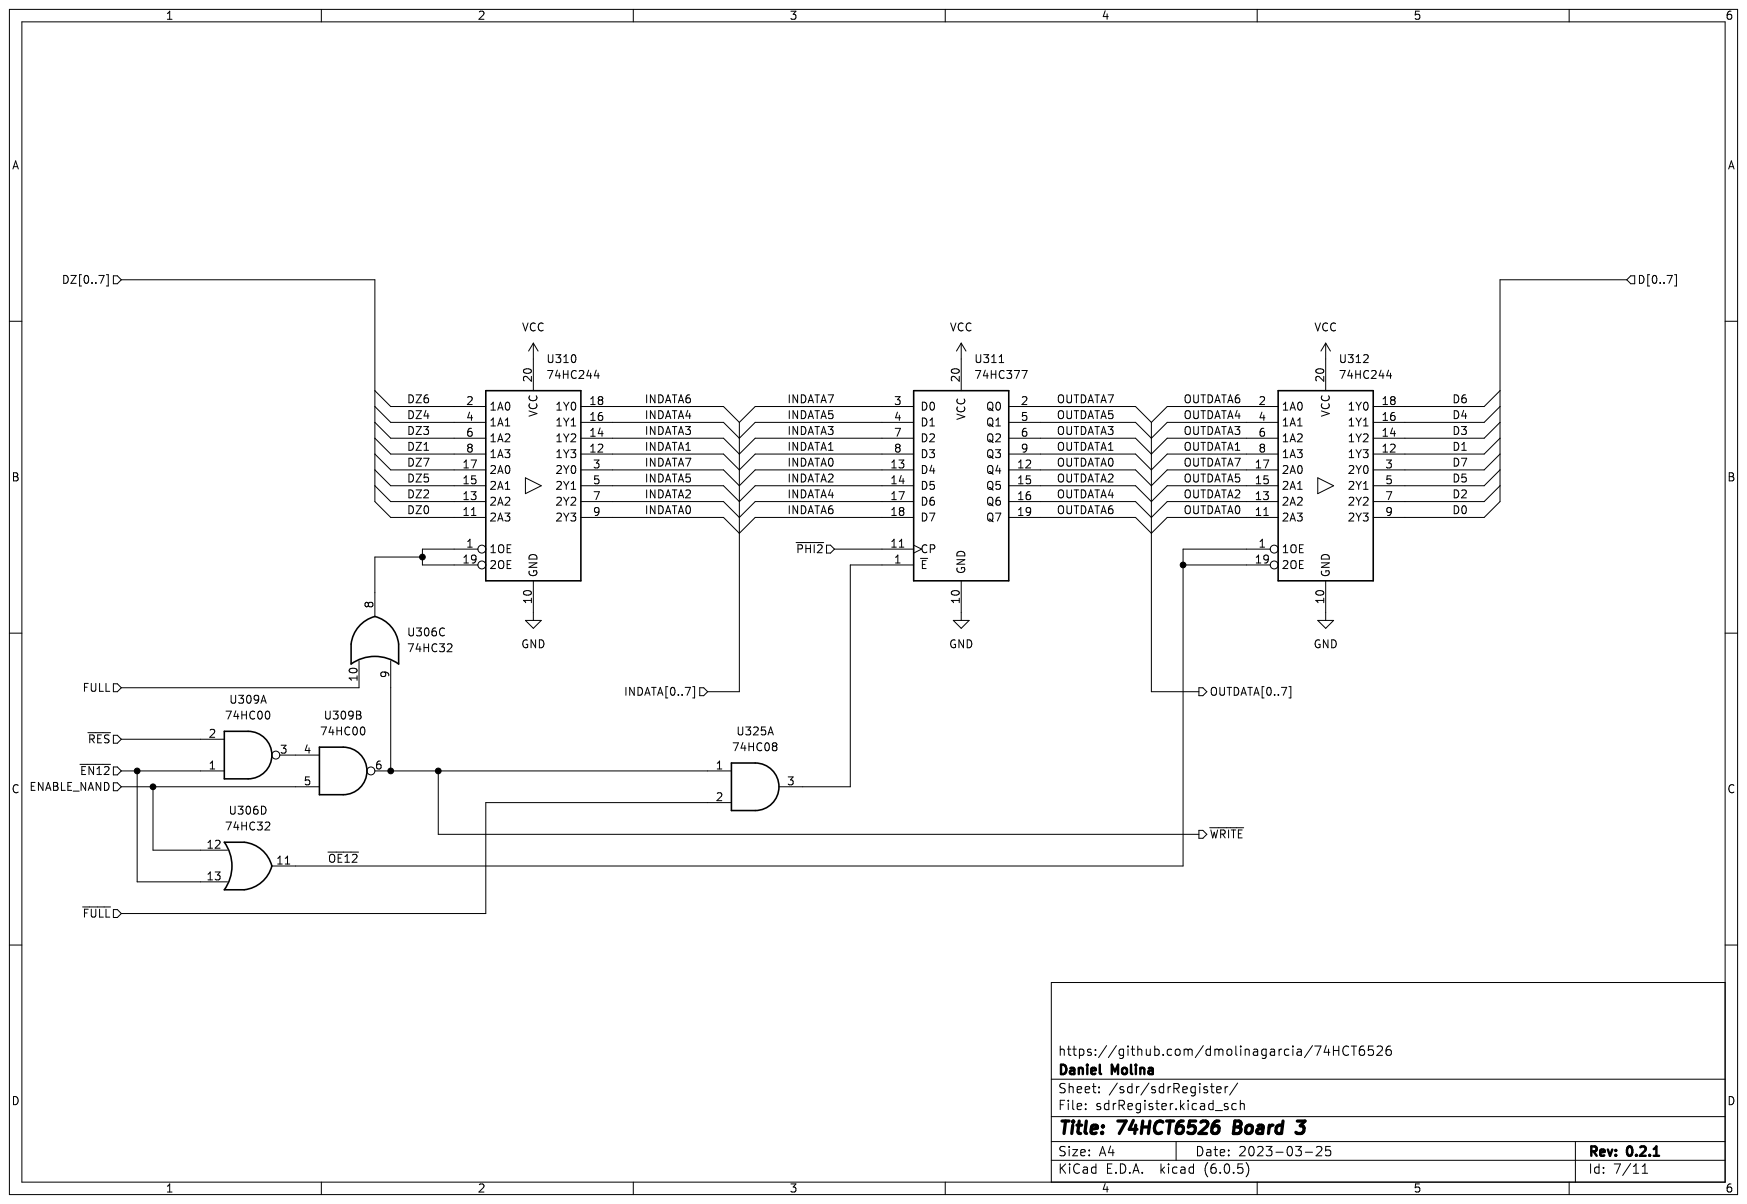
[picture p185: page 7]

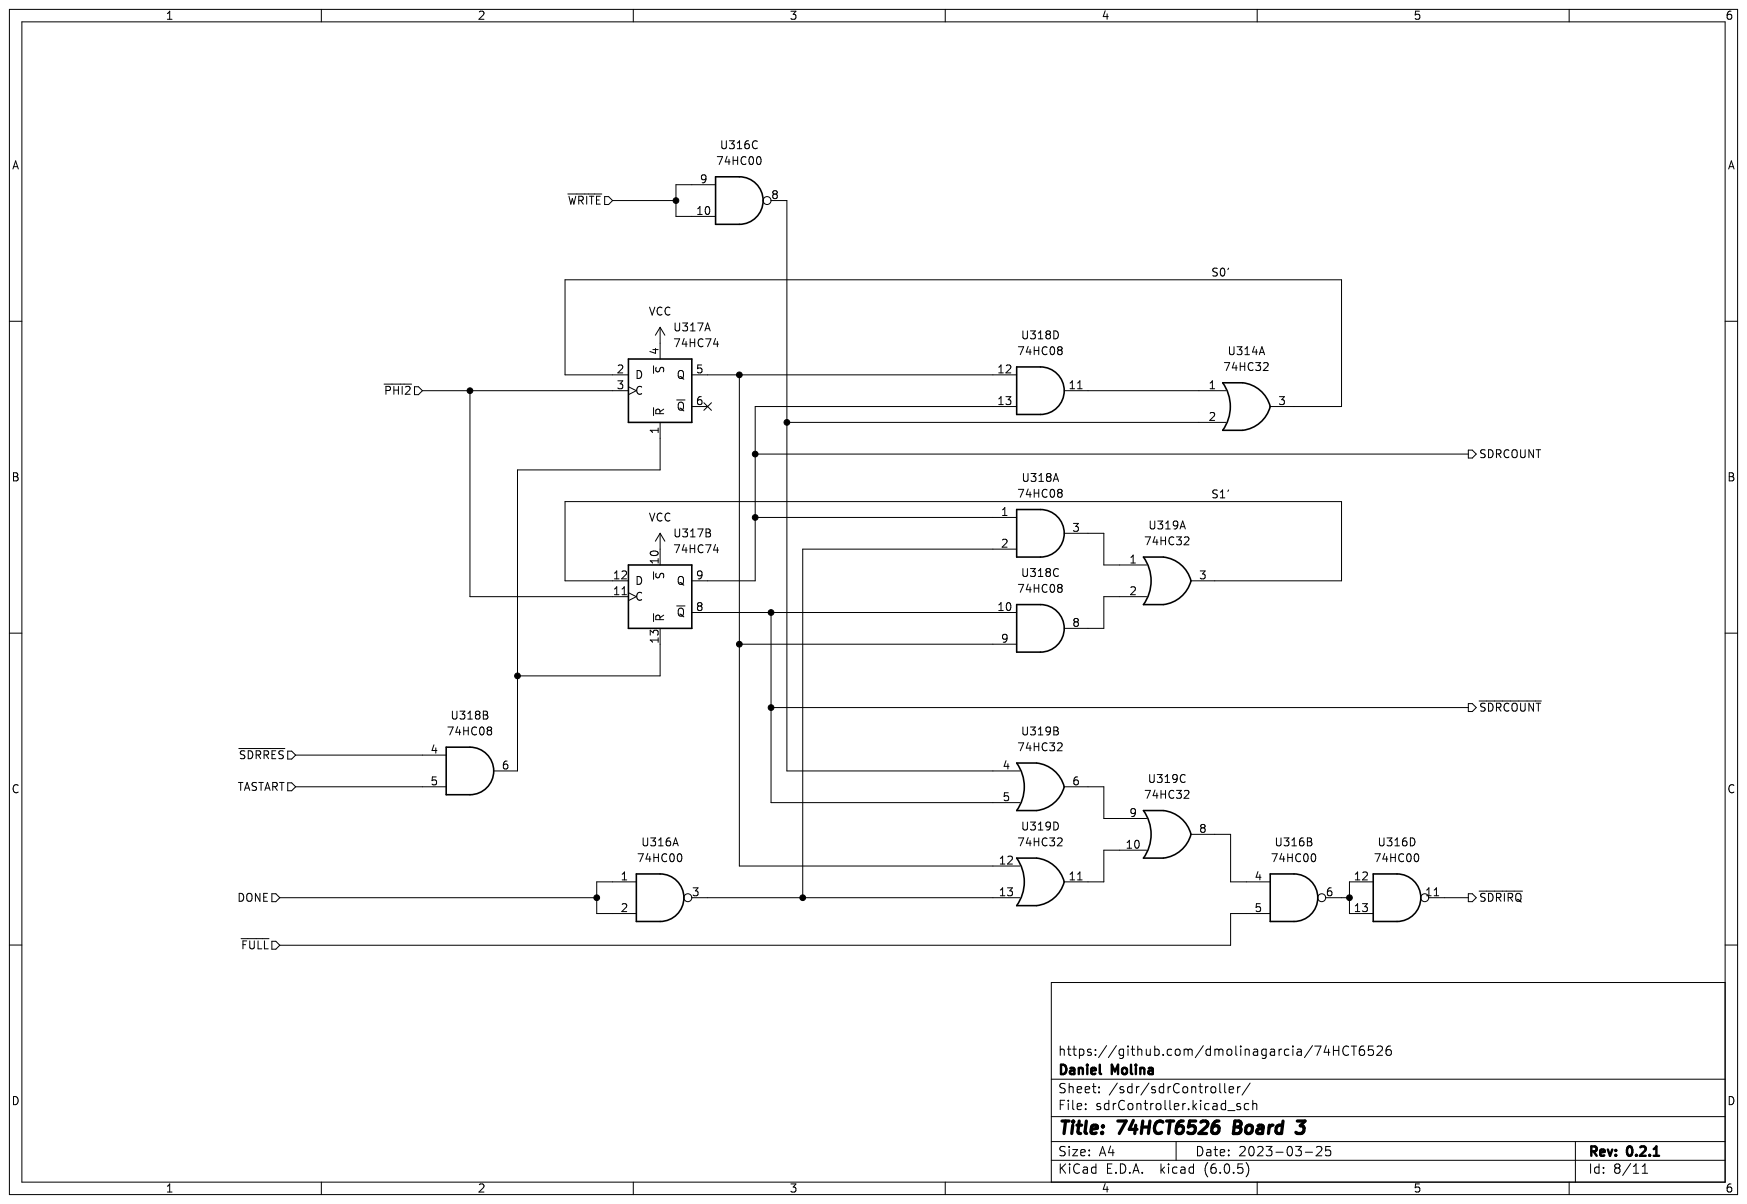
[picture p186: page 8]


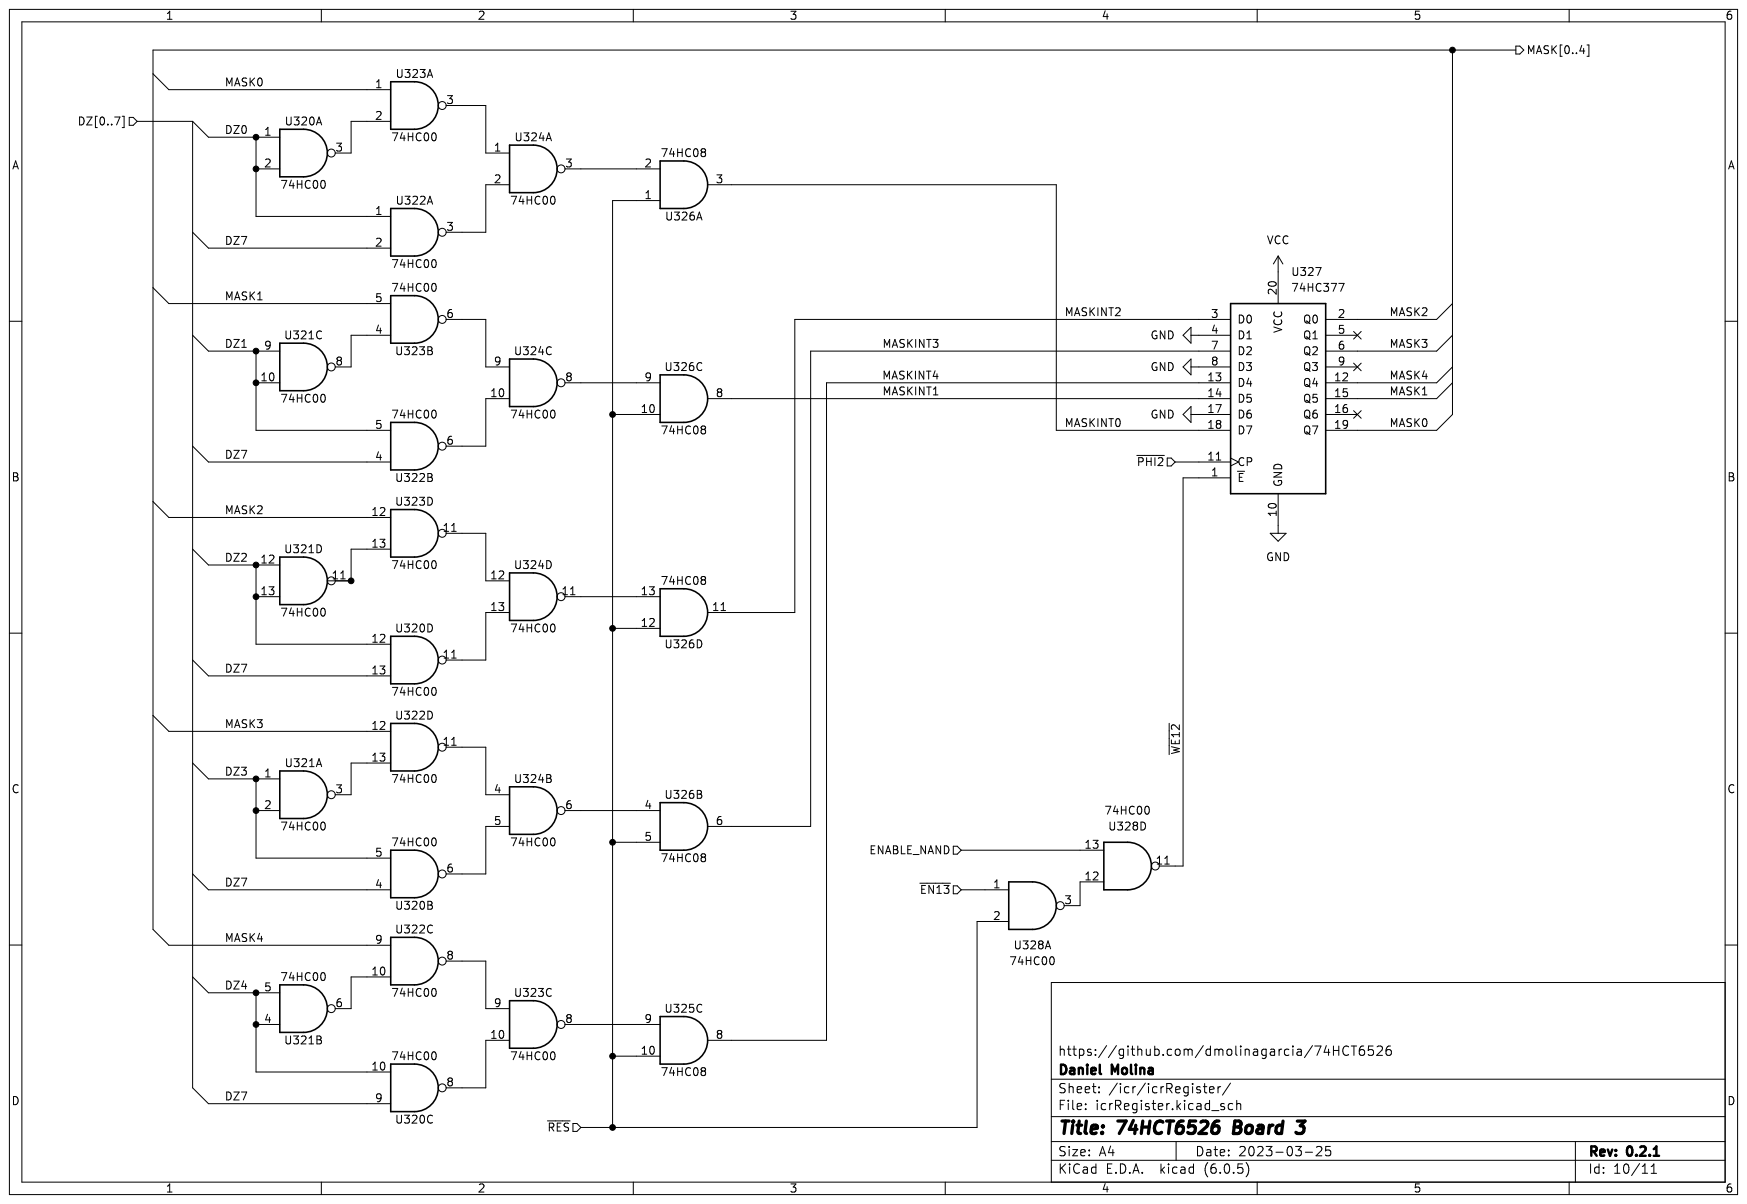
[picture p187: page 10]

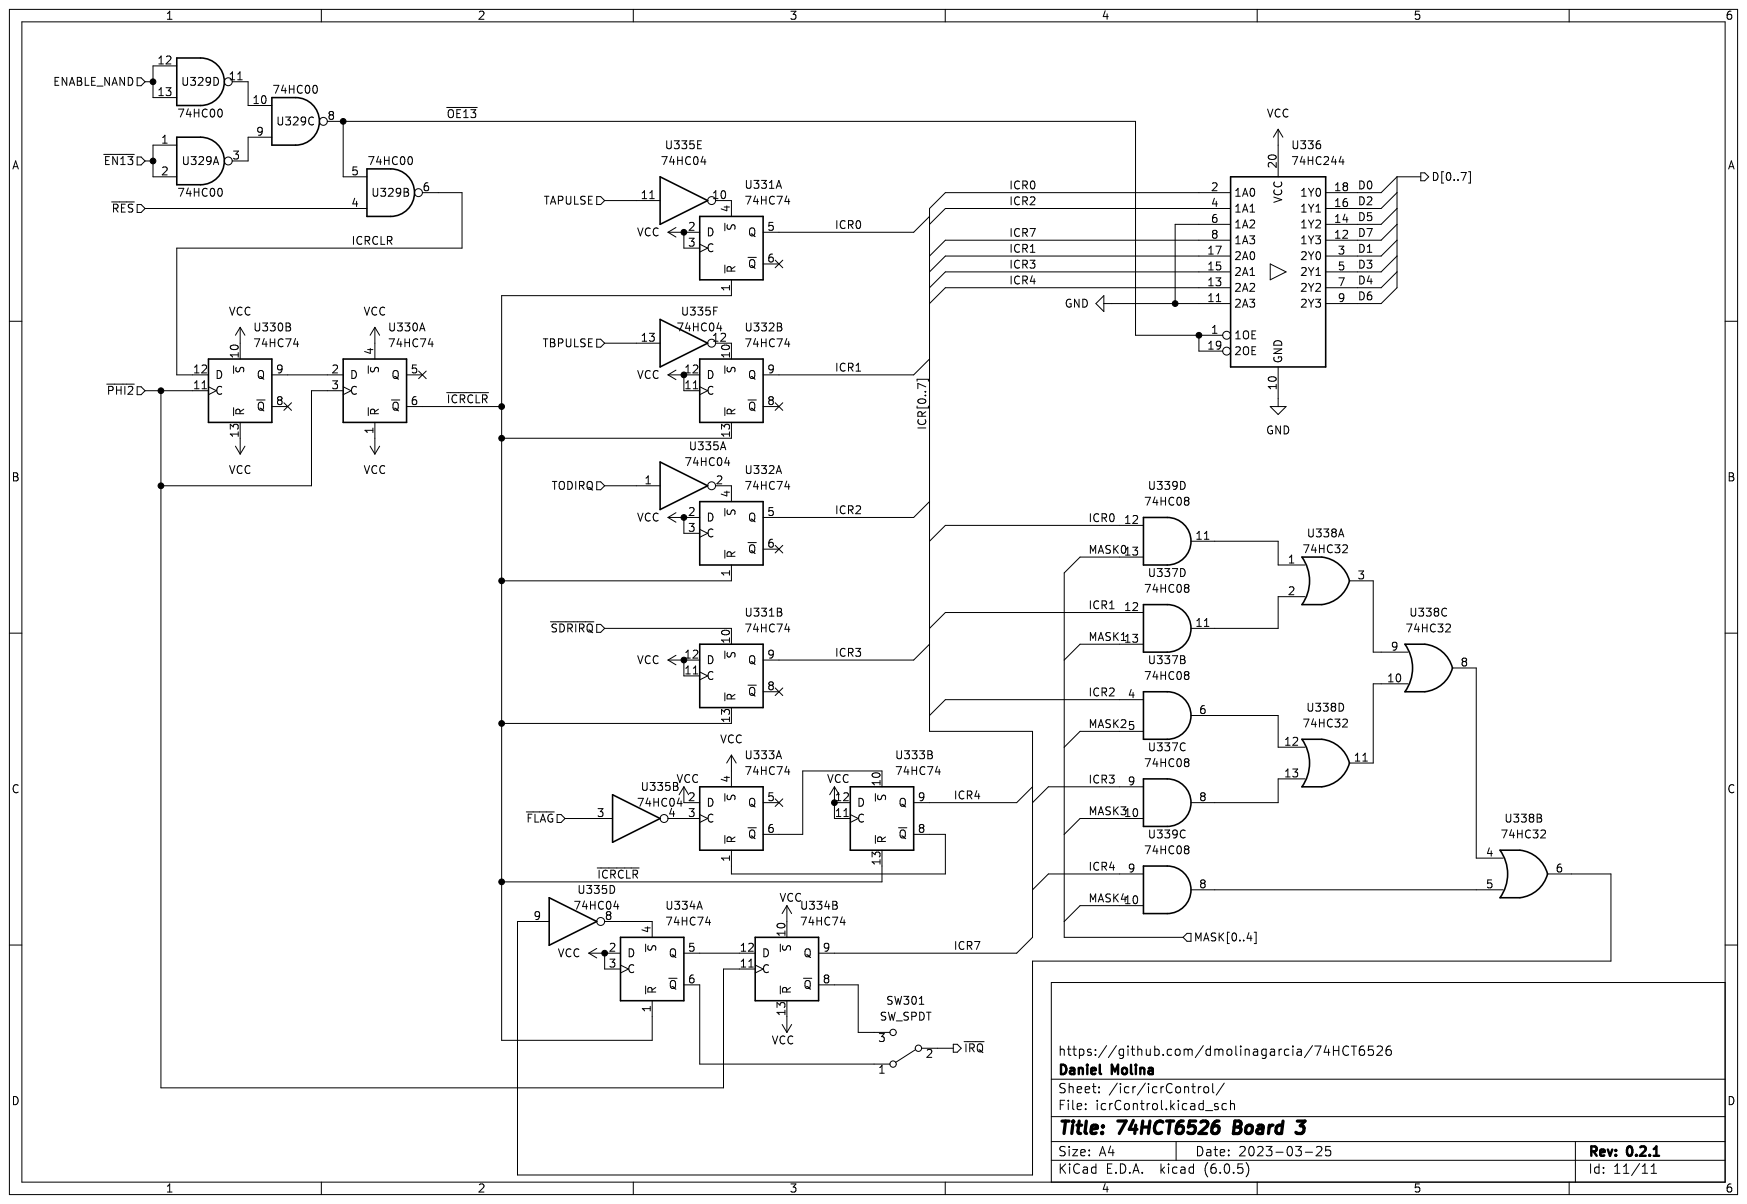
[picture p188: page 11]
