dmolinagarcia/74HCT6526/pdf/B0.pcb.v0.1.0.pdf

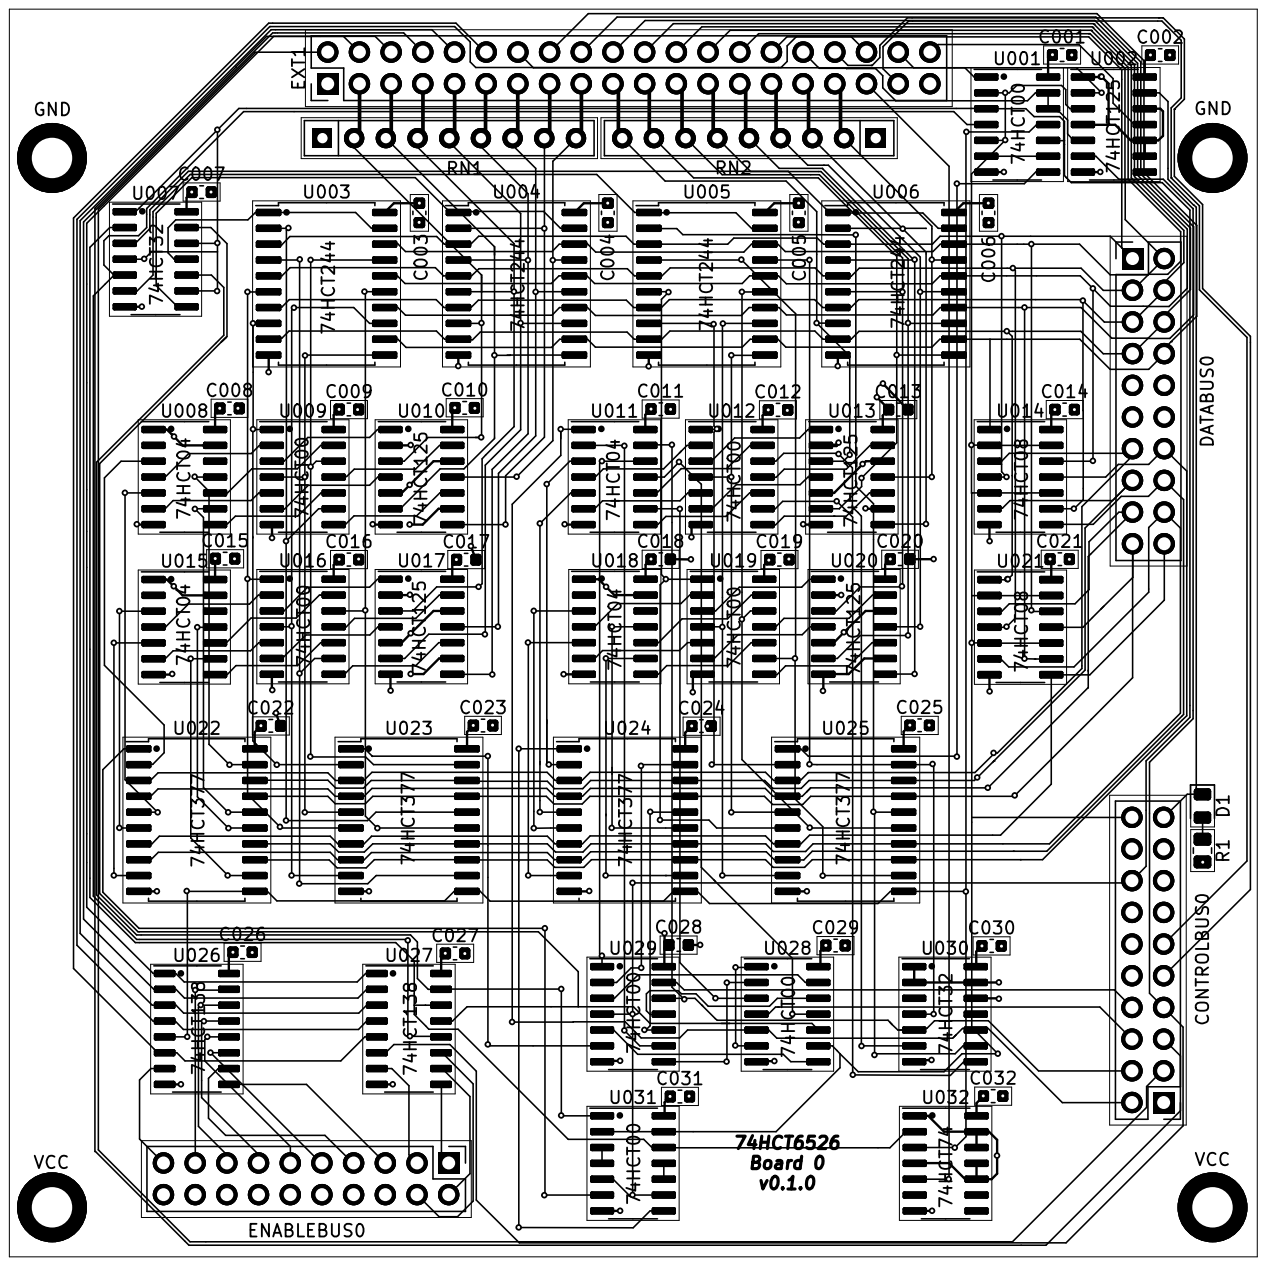
[picture p189: page 1]
