dmolinagarcia/74HCT6526/pdf/B0.pcb.v0.1.1.pdf

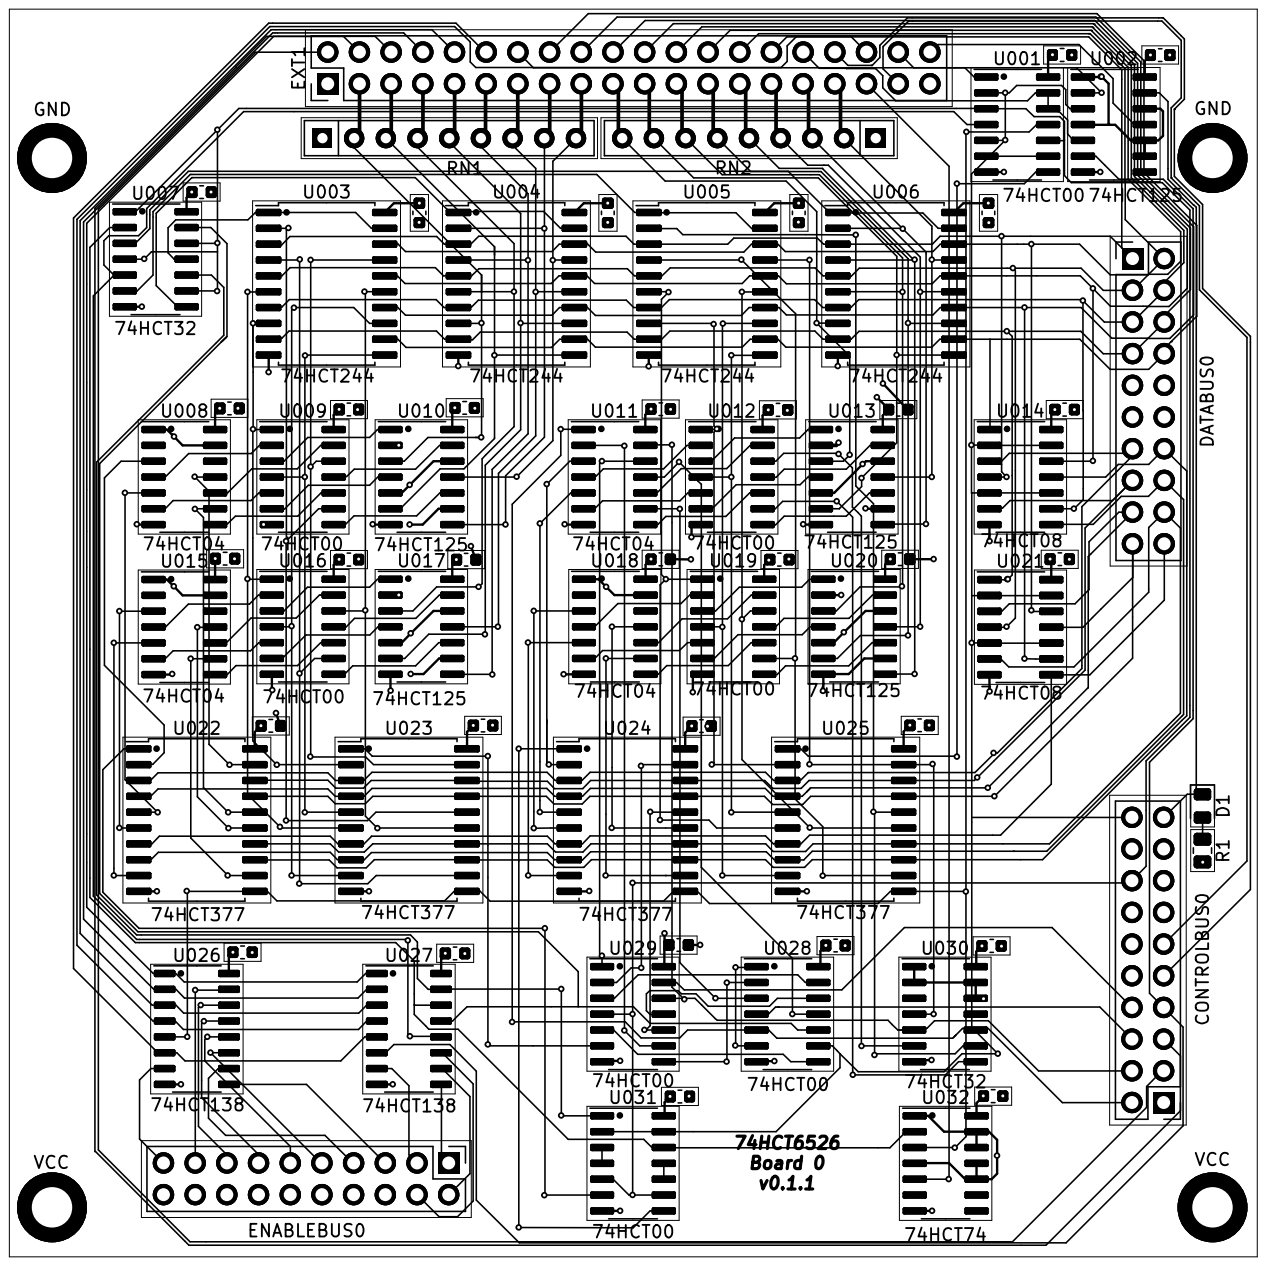
[picture p190: page 1]
