dmolinagarcia/74HCT6526/pdf/B0.pcb.v0.1.2.pdf

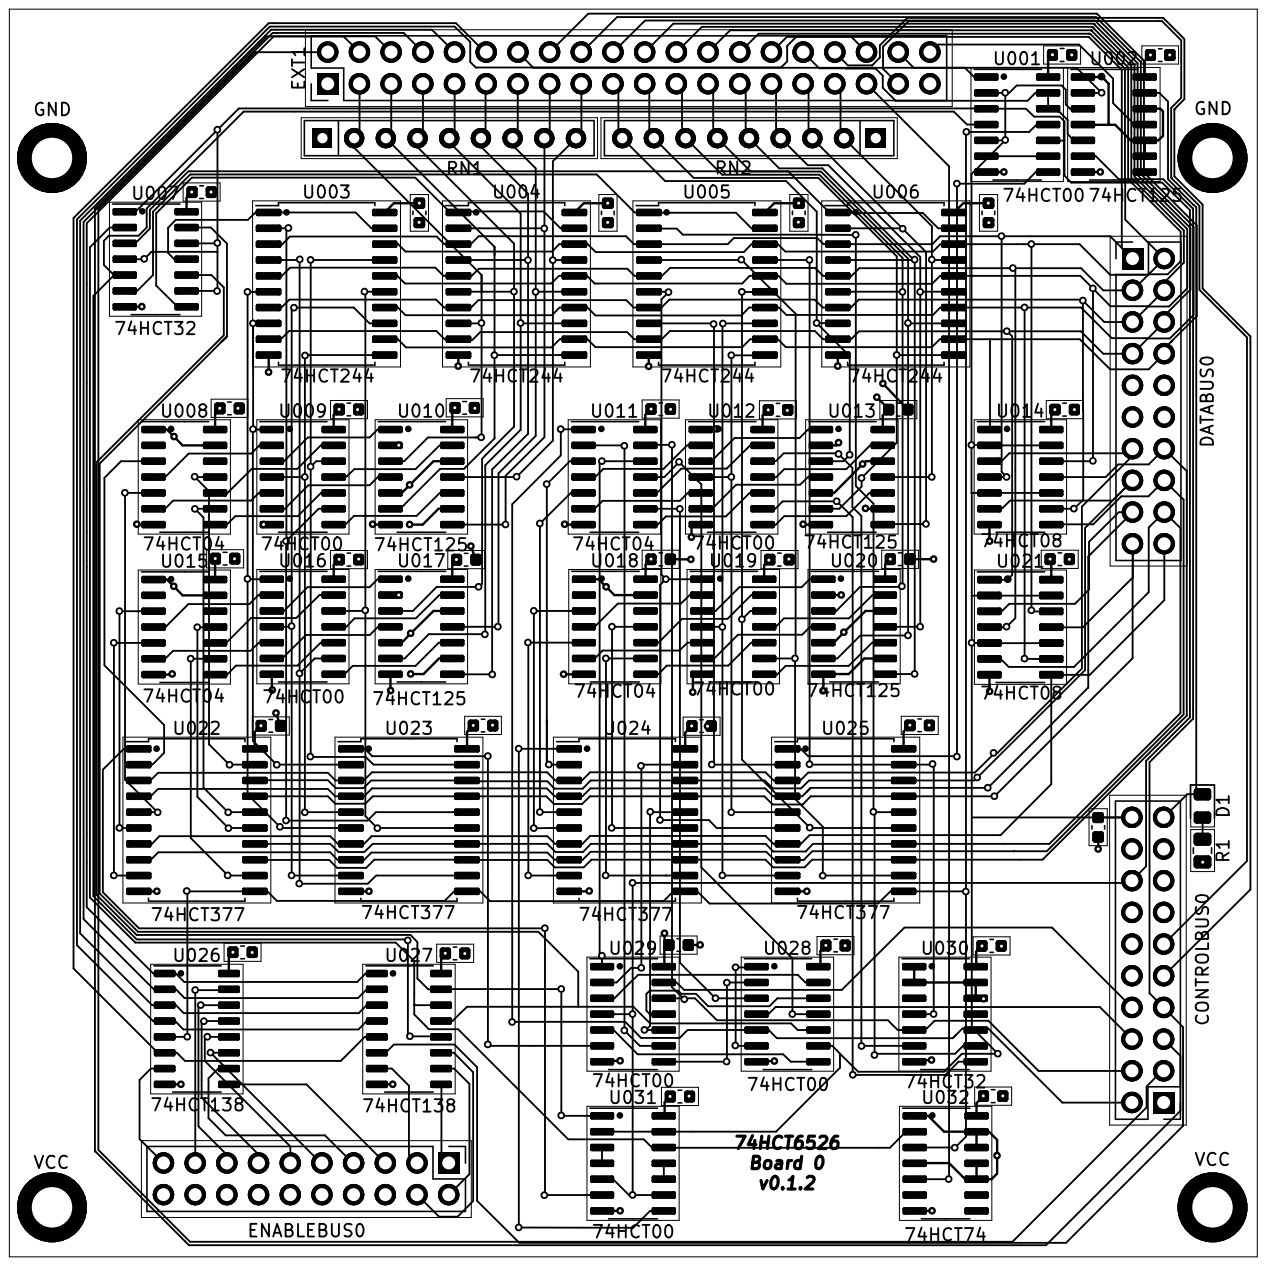
[picture p191: page 1]
