dmolinagarcia/74HCT6526/pdf/B0.pcb.v0.2.0.pdf

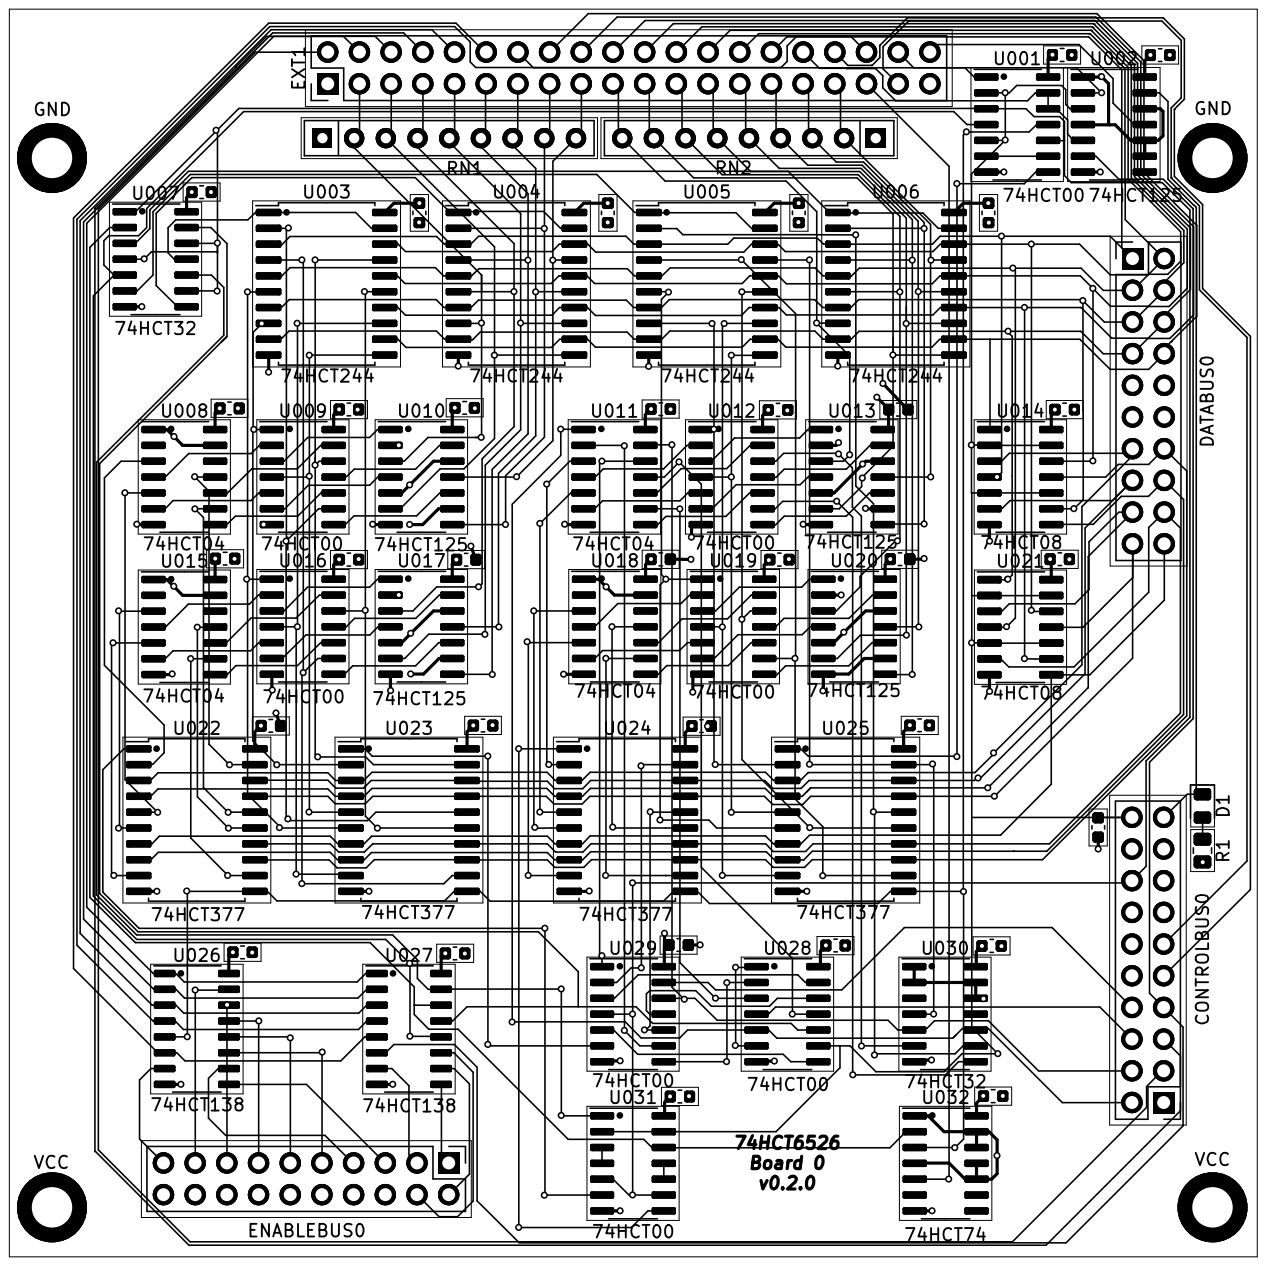
[picture p192: page 1]
