dmolinagarcia/74HCT6526/pdf/B1.pcb.v0.1.0.pdf

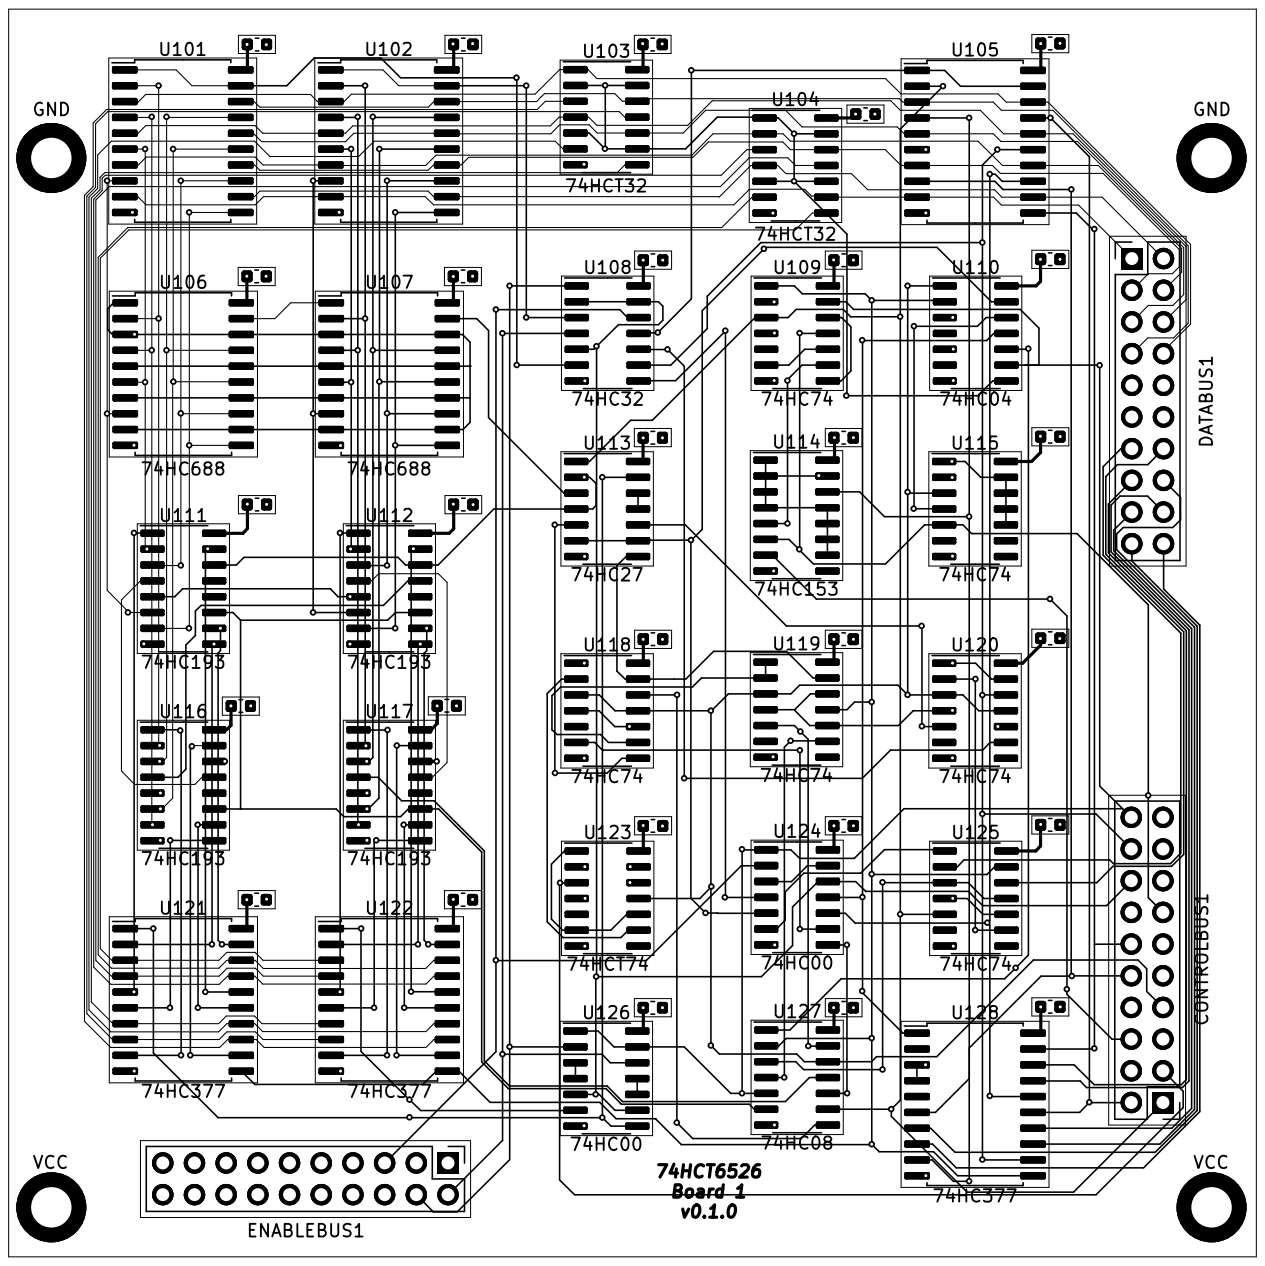
[picture p193: page 1]
