dmolinagarcia/74HCT6526/pdf/B1.pcb.v0.1.1.pdf

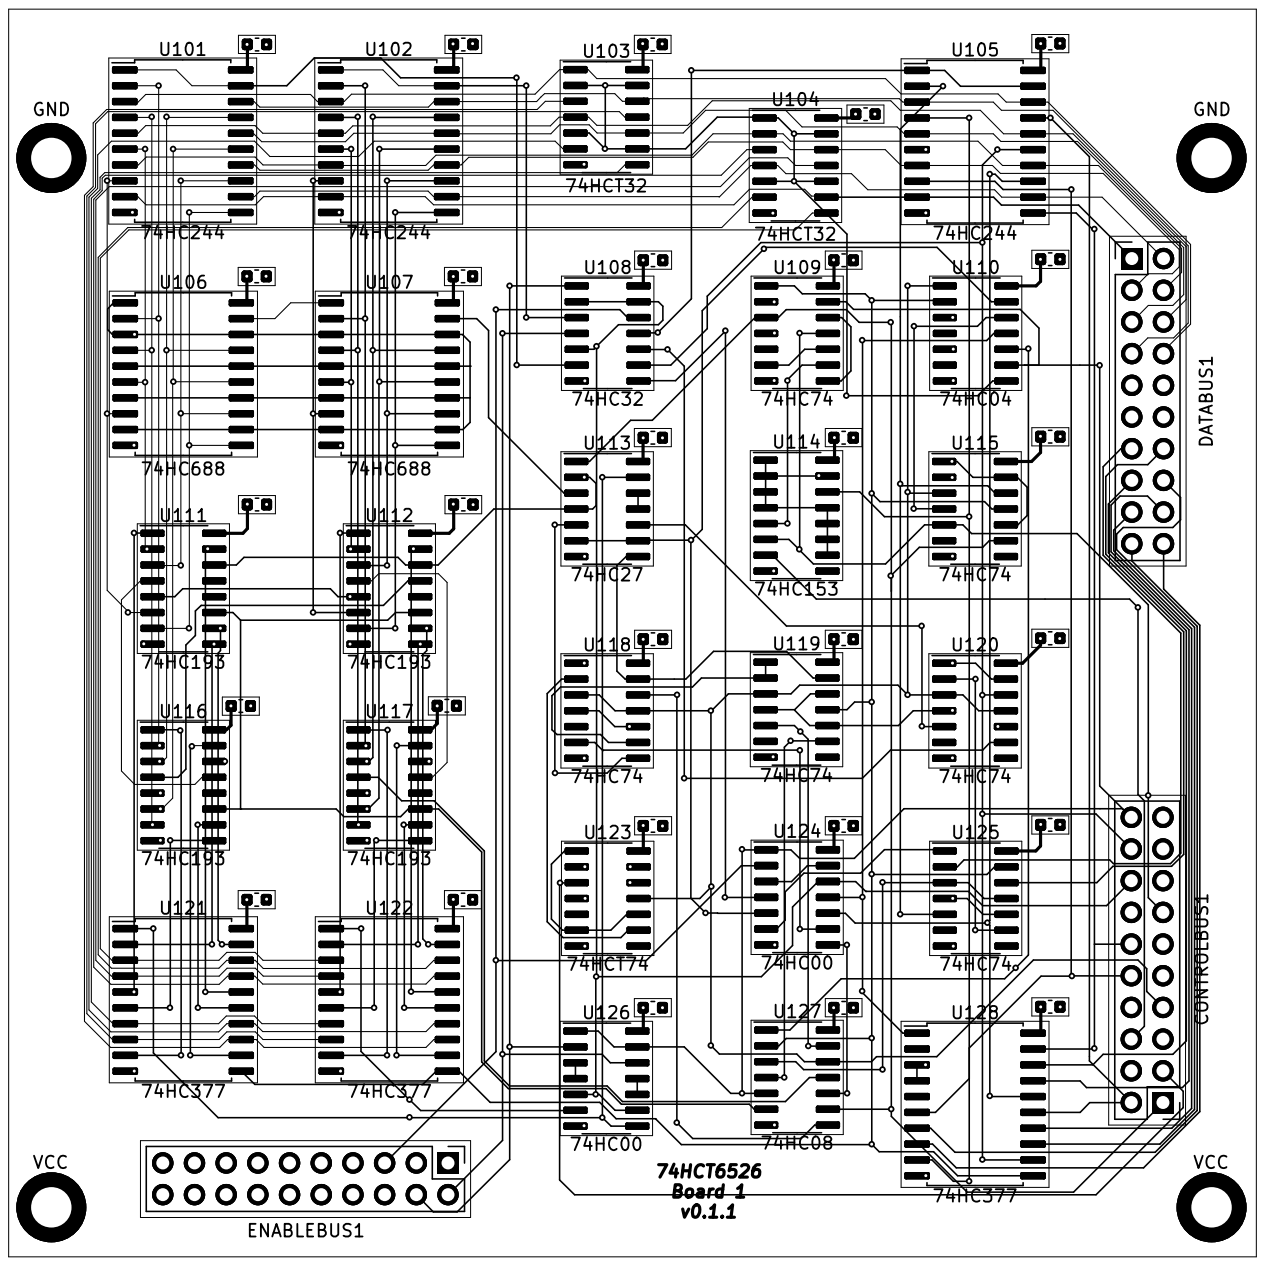
[picture p194: page 1]
