dmolinagarcia/74HCT6526/pdf/B1.pcb.v0.1.2.pdf

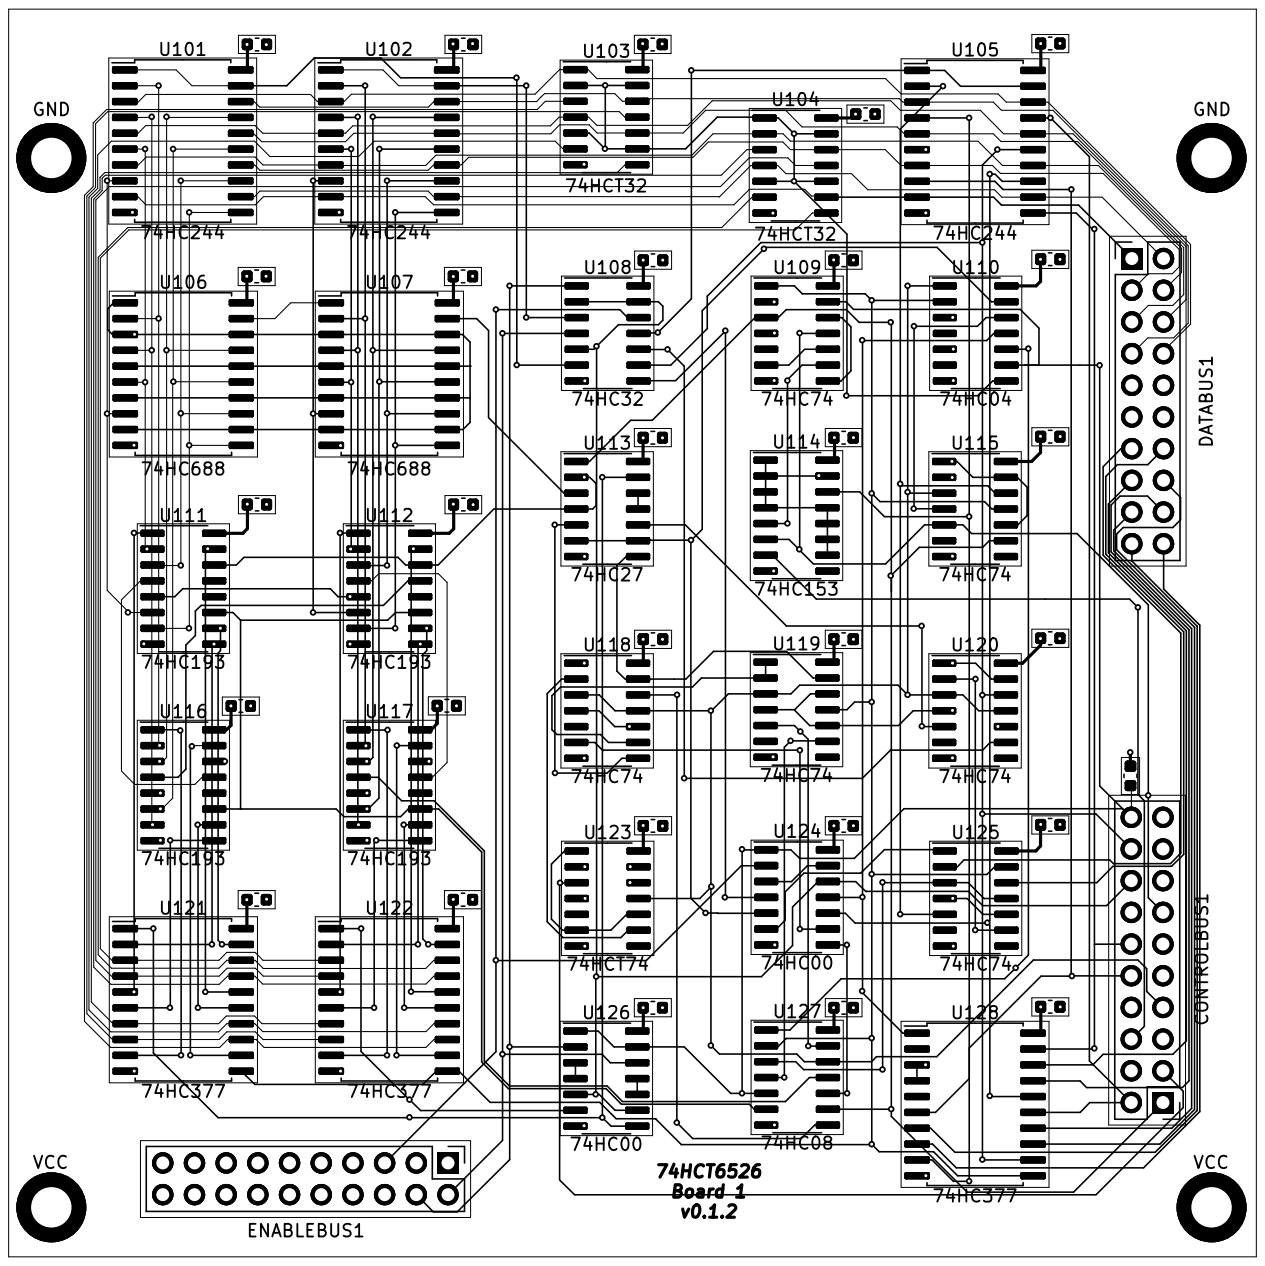
[picture p195: page 1]
