dmolinagarcia/74HCT6526/pdf/B1.pcb.v0.2.0.pdf

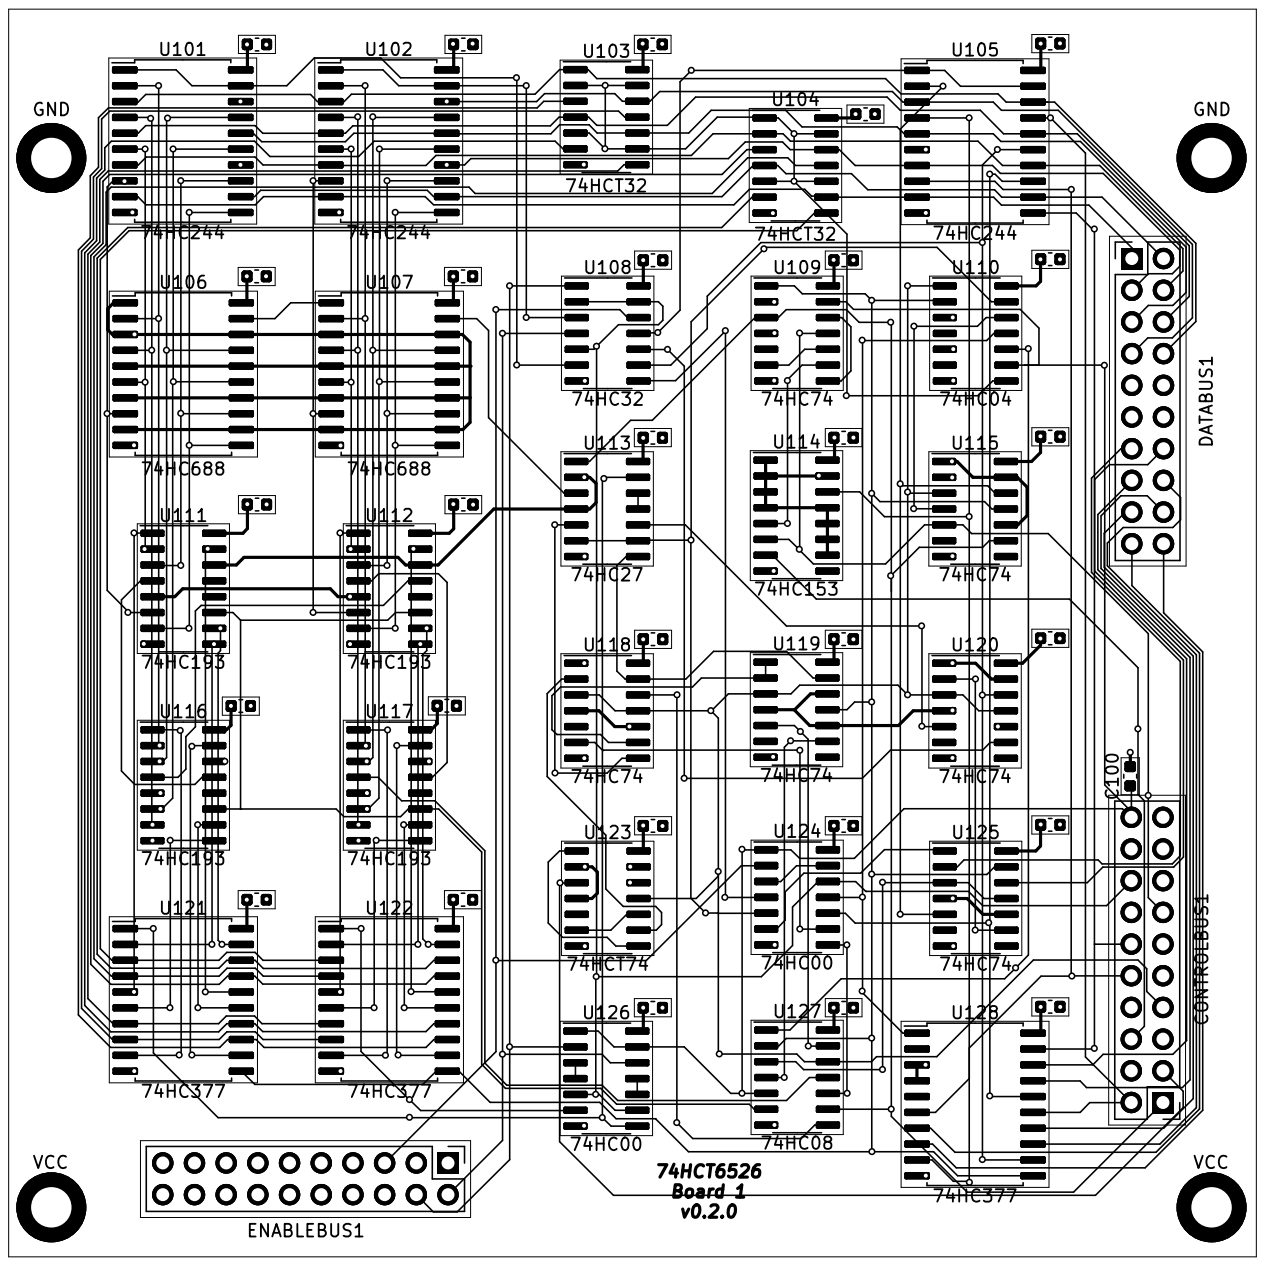
[picture p196: page 1]
