dmolinagarcia/74HCT6526/pdf/B2.pcb.v0.1.1.pdf

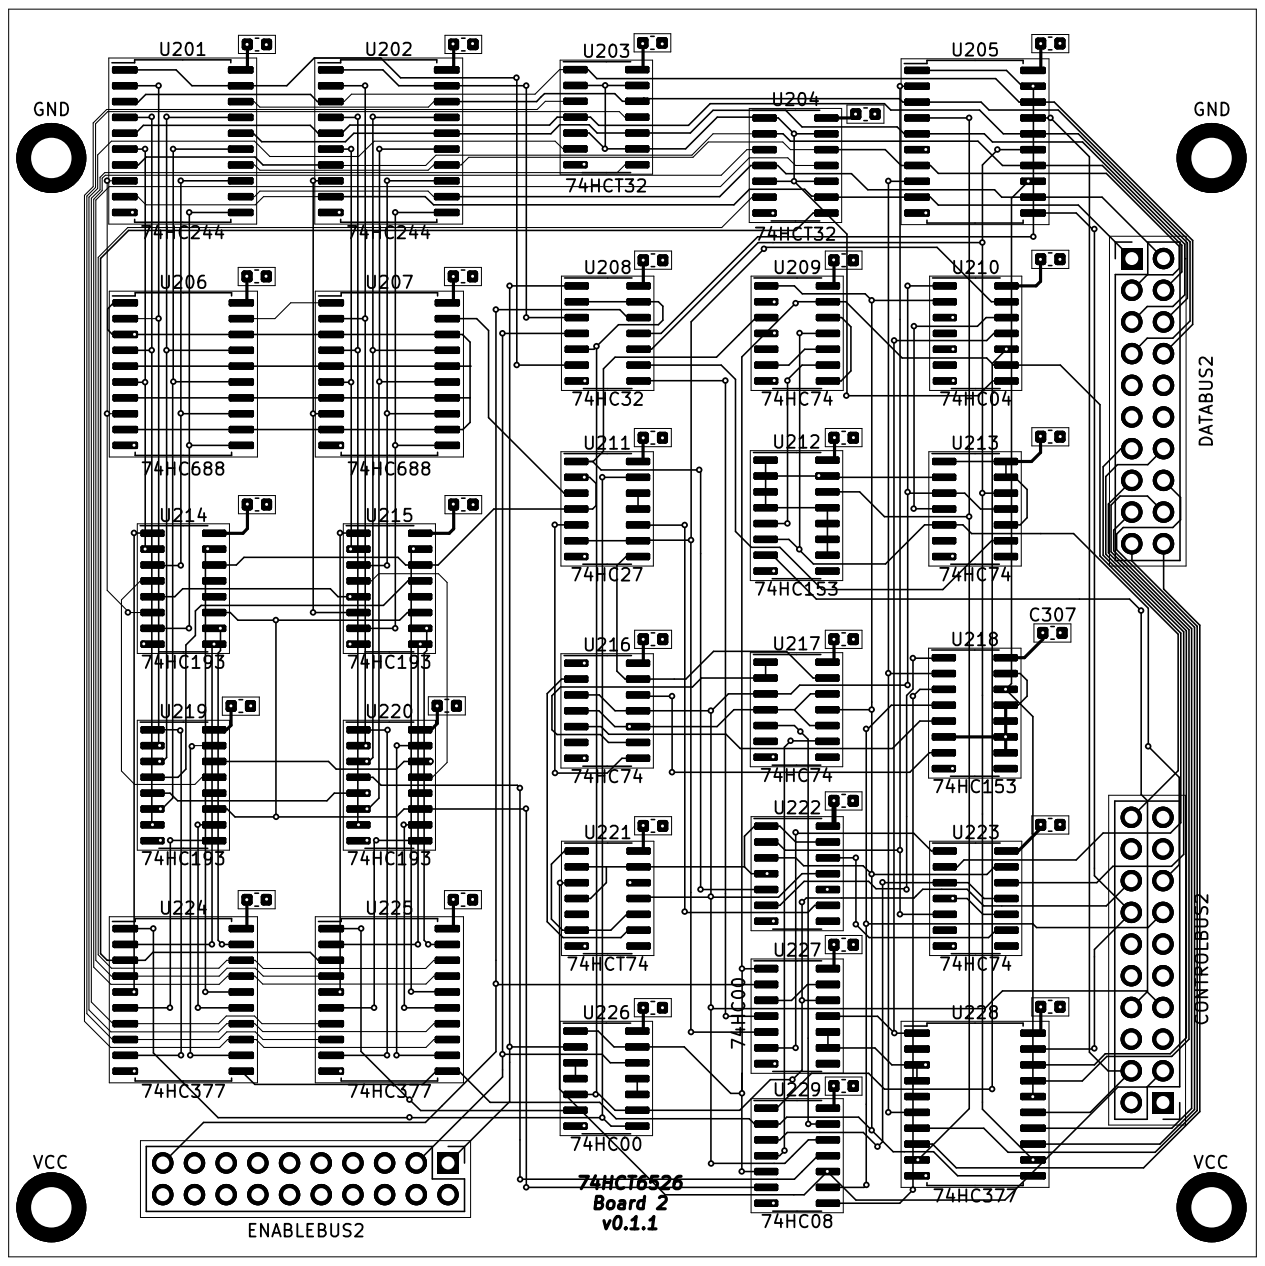
[picture p197: page 1]
