dmolinagarcia/74HCT6526/pdf/B2.pcb.v0.1.2.pdf

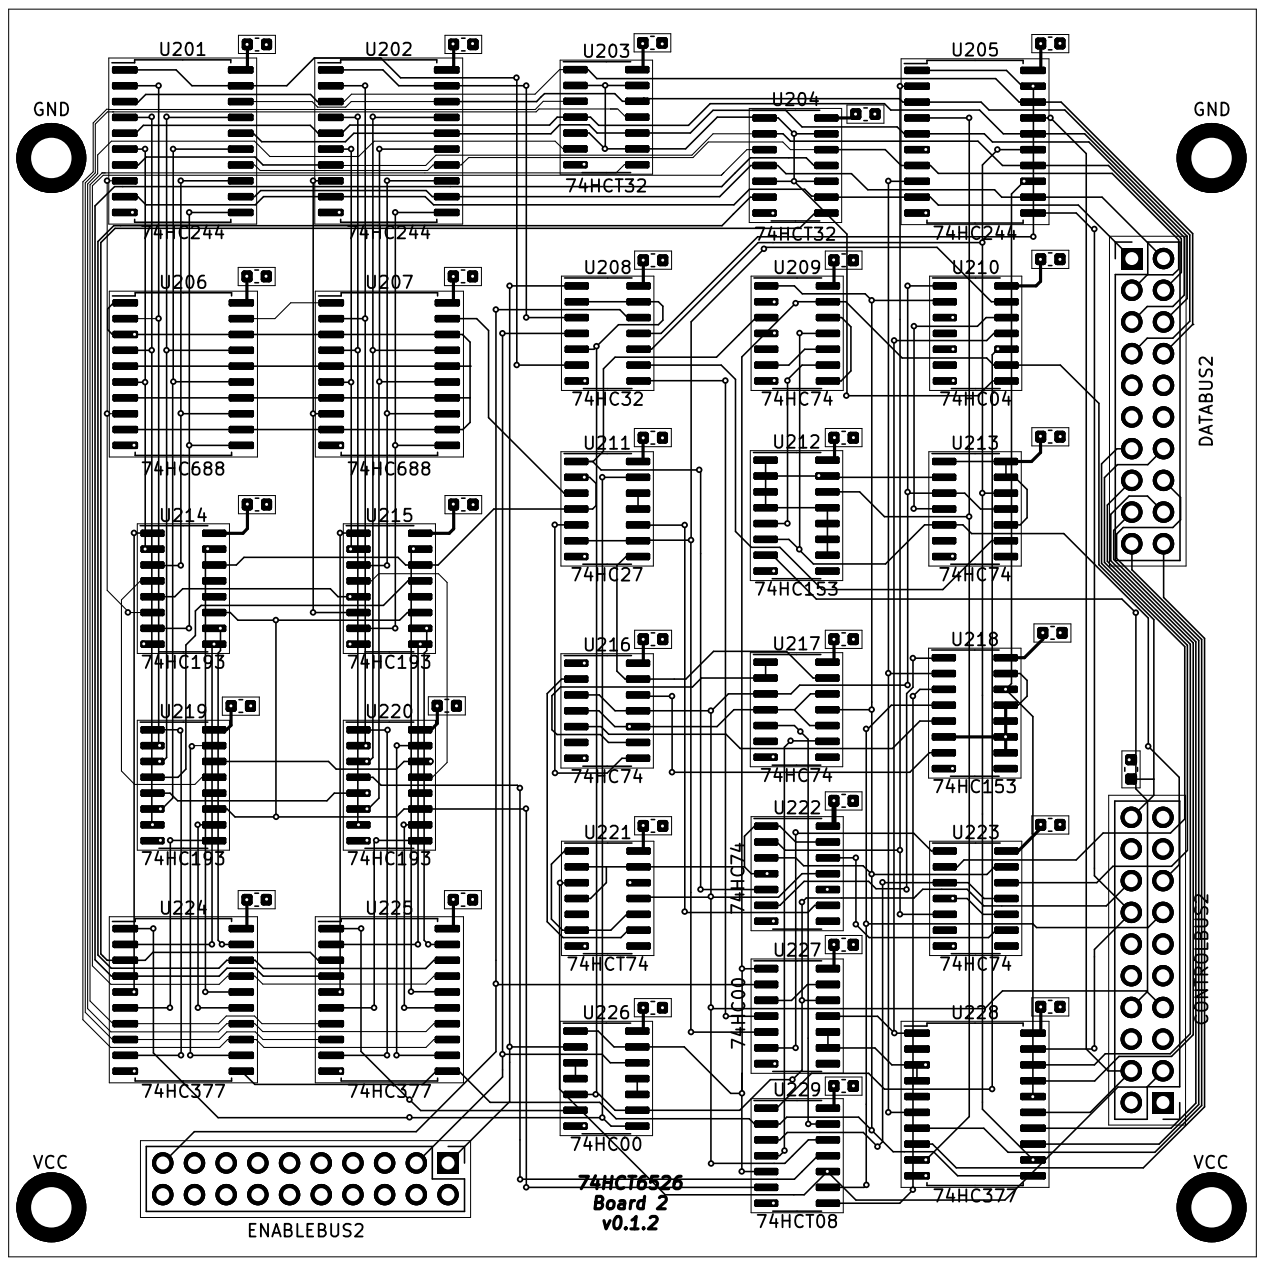
[picture p198: page 1]
