dmolinagarcia/74HCT6526/pdf/B2.pcb.v0.2.0.pdf

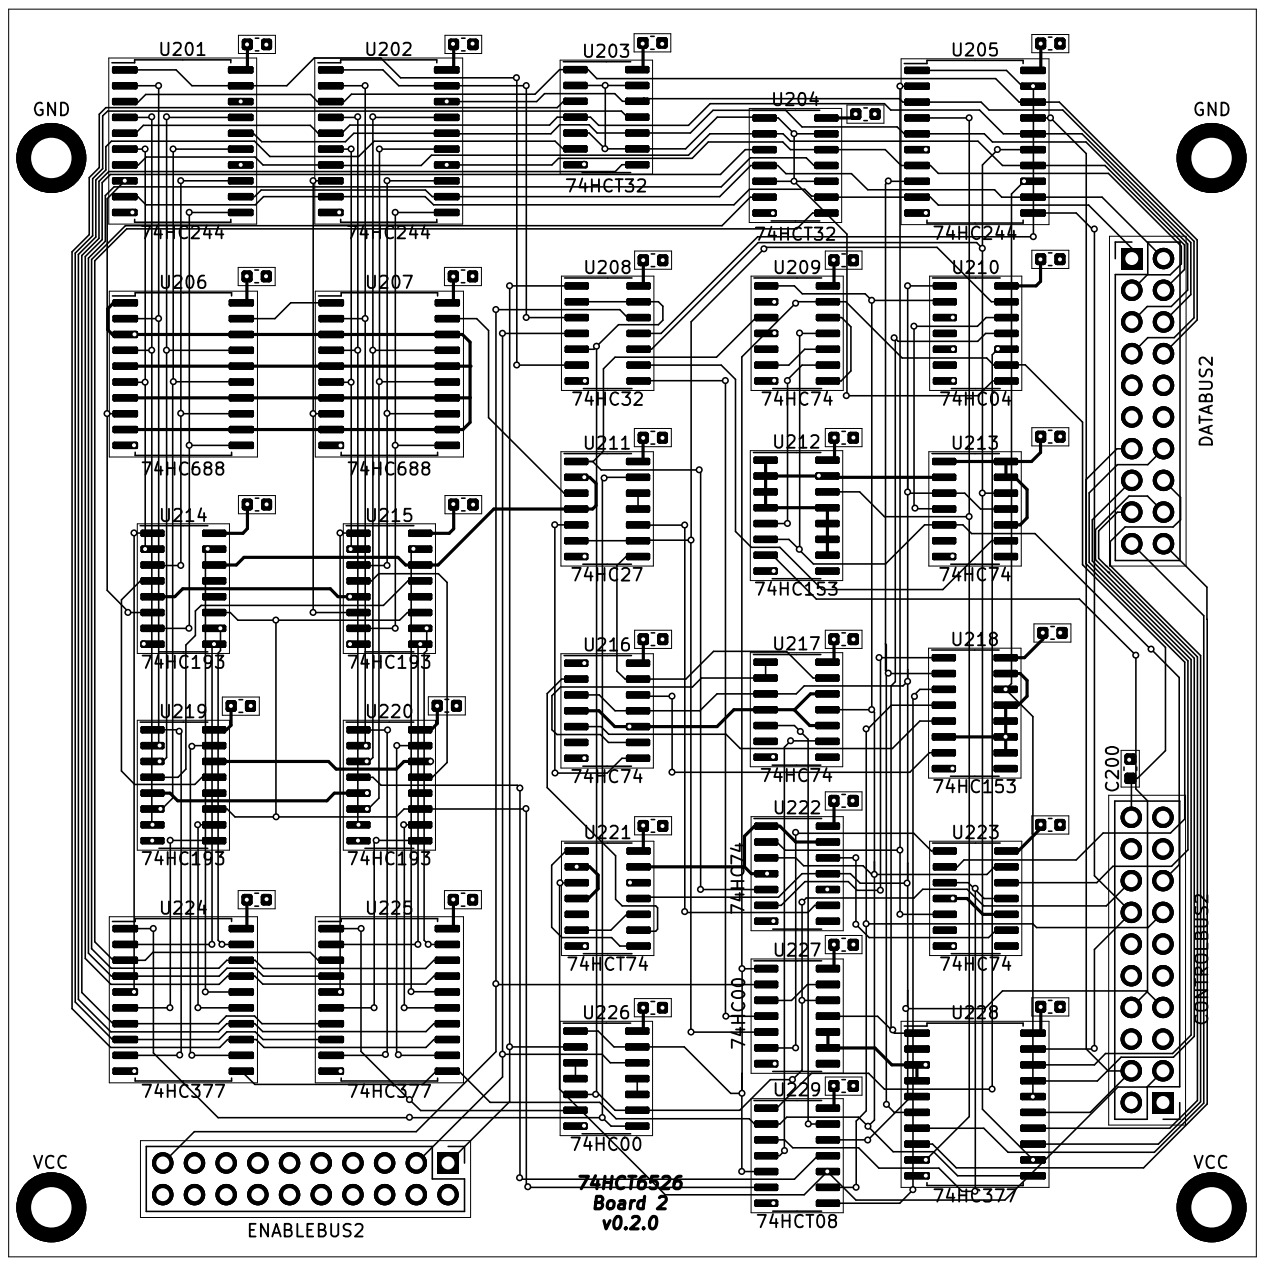
[picture p199: page 1]
