dmolinagarcia/74HCT6526/pdf/B3.pcb.v0.1.2.pdf

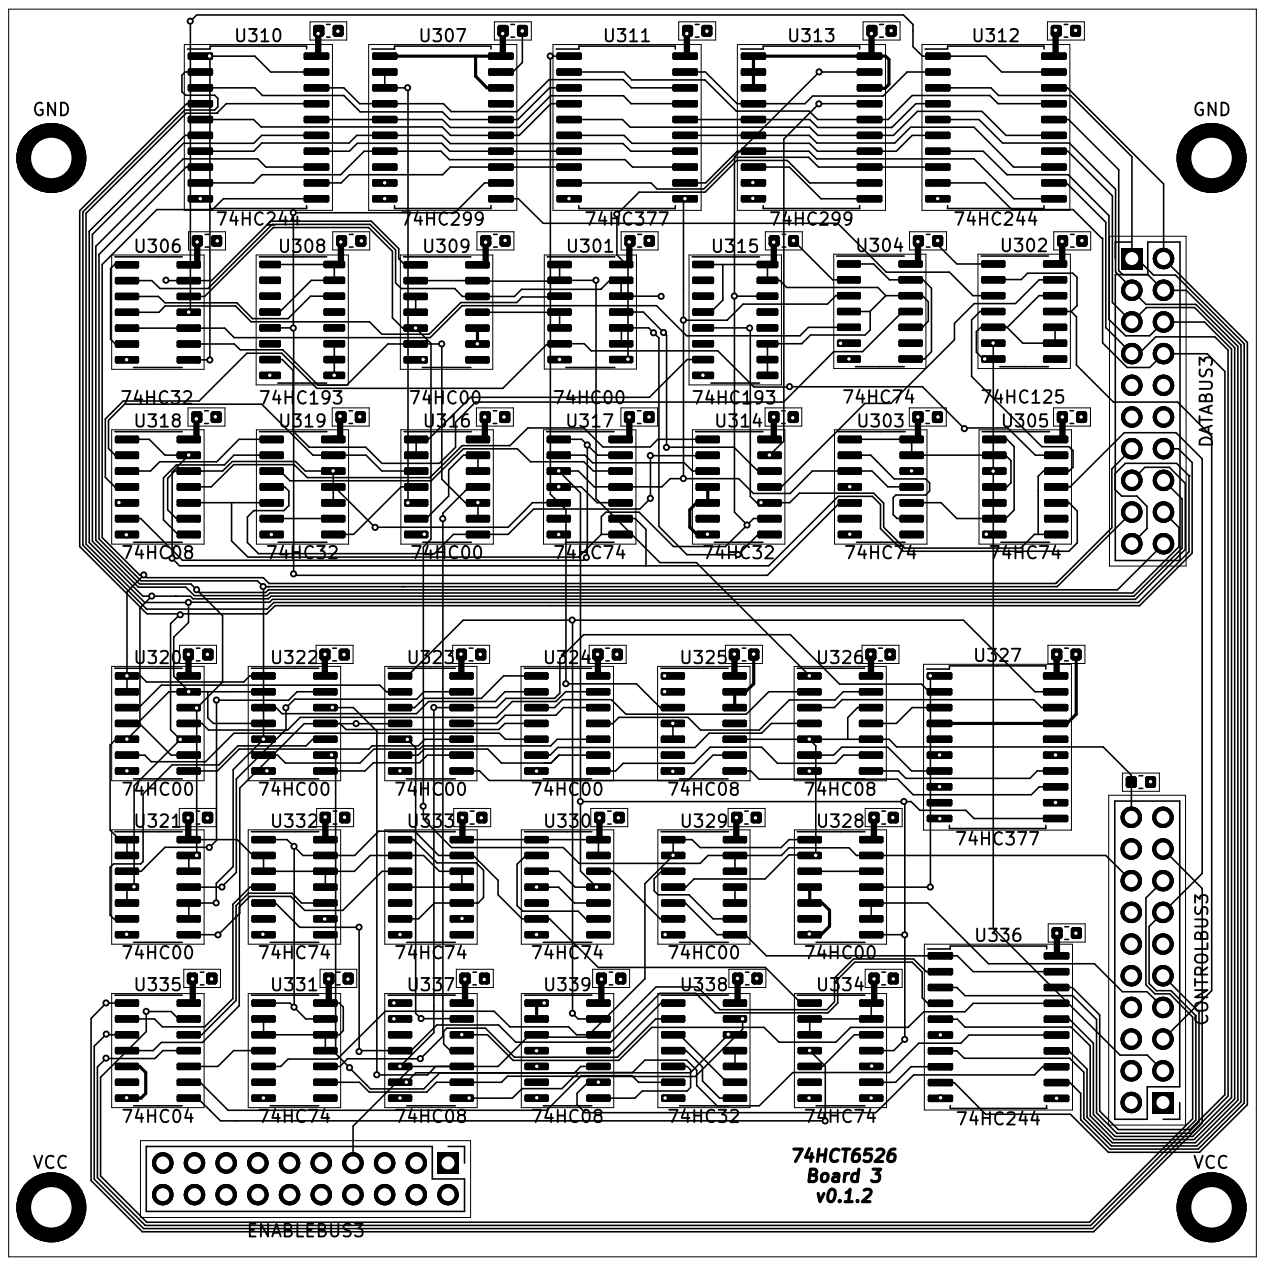
[picture p200: page 1]
