dmolinagarcia/74HCT6526/pdf/B3.pcb.v0.2.0.pdf

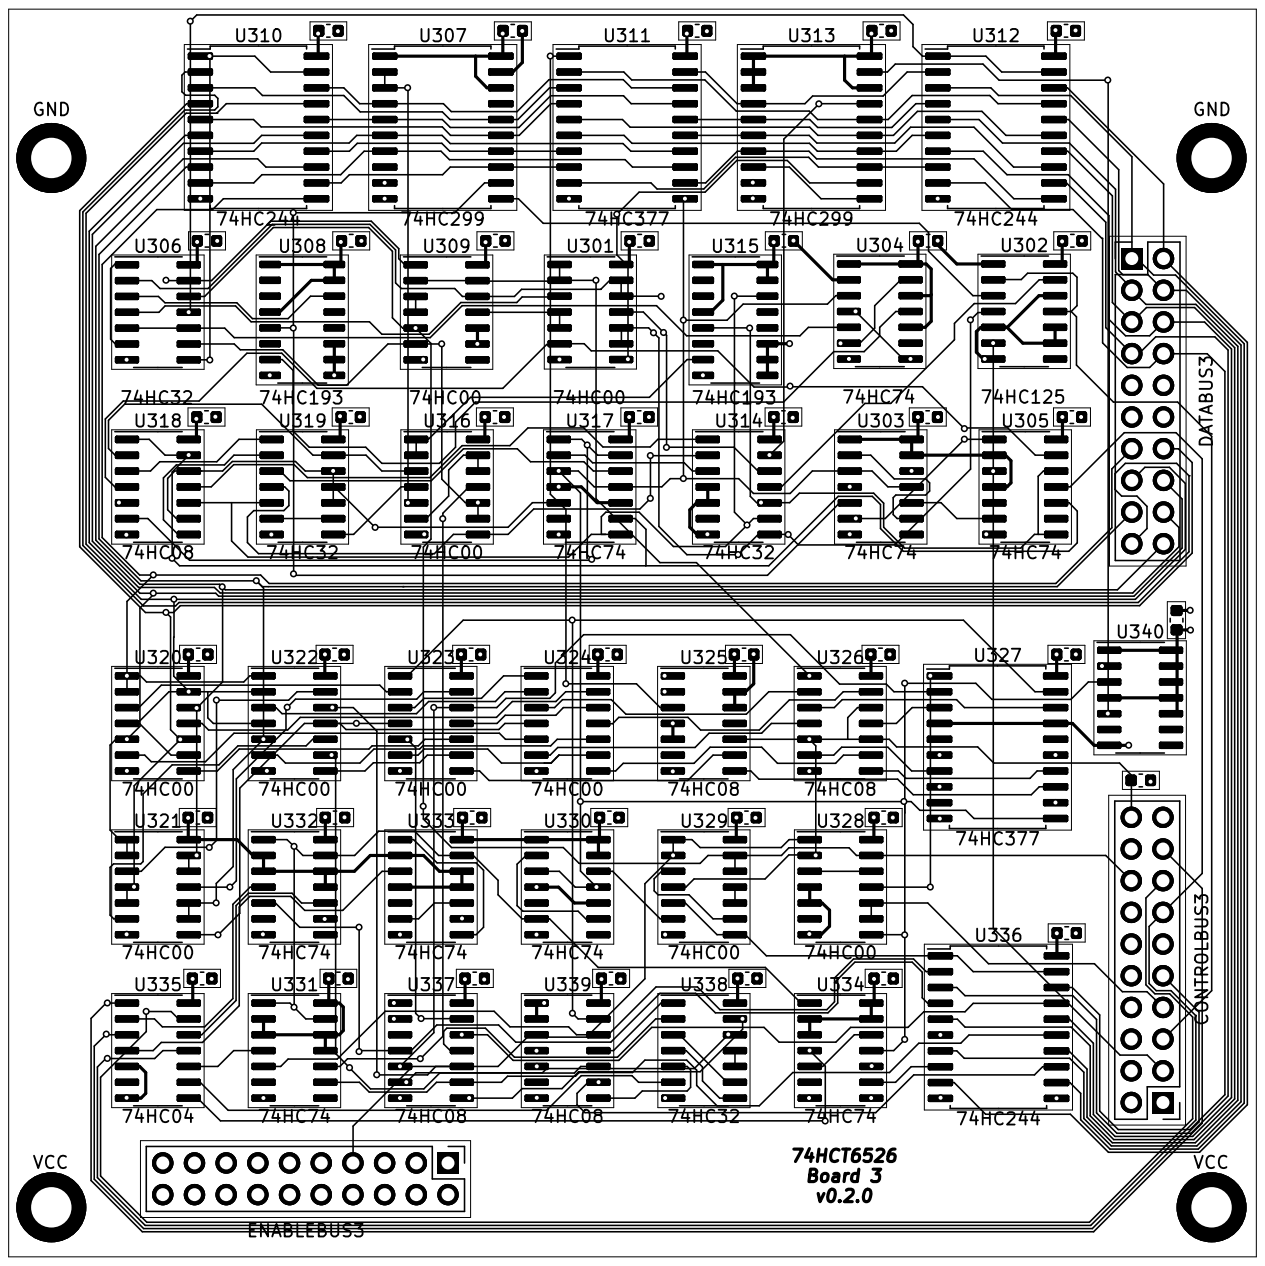
[picture p201: page 1]
