dmolinagarcia/74HCT6526/pdf/B3.sch.v0.2.0.pdf

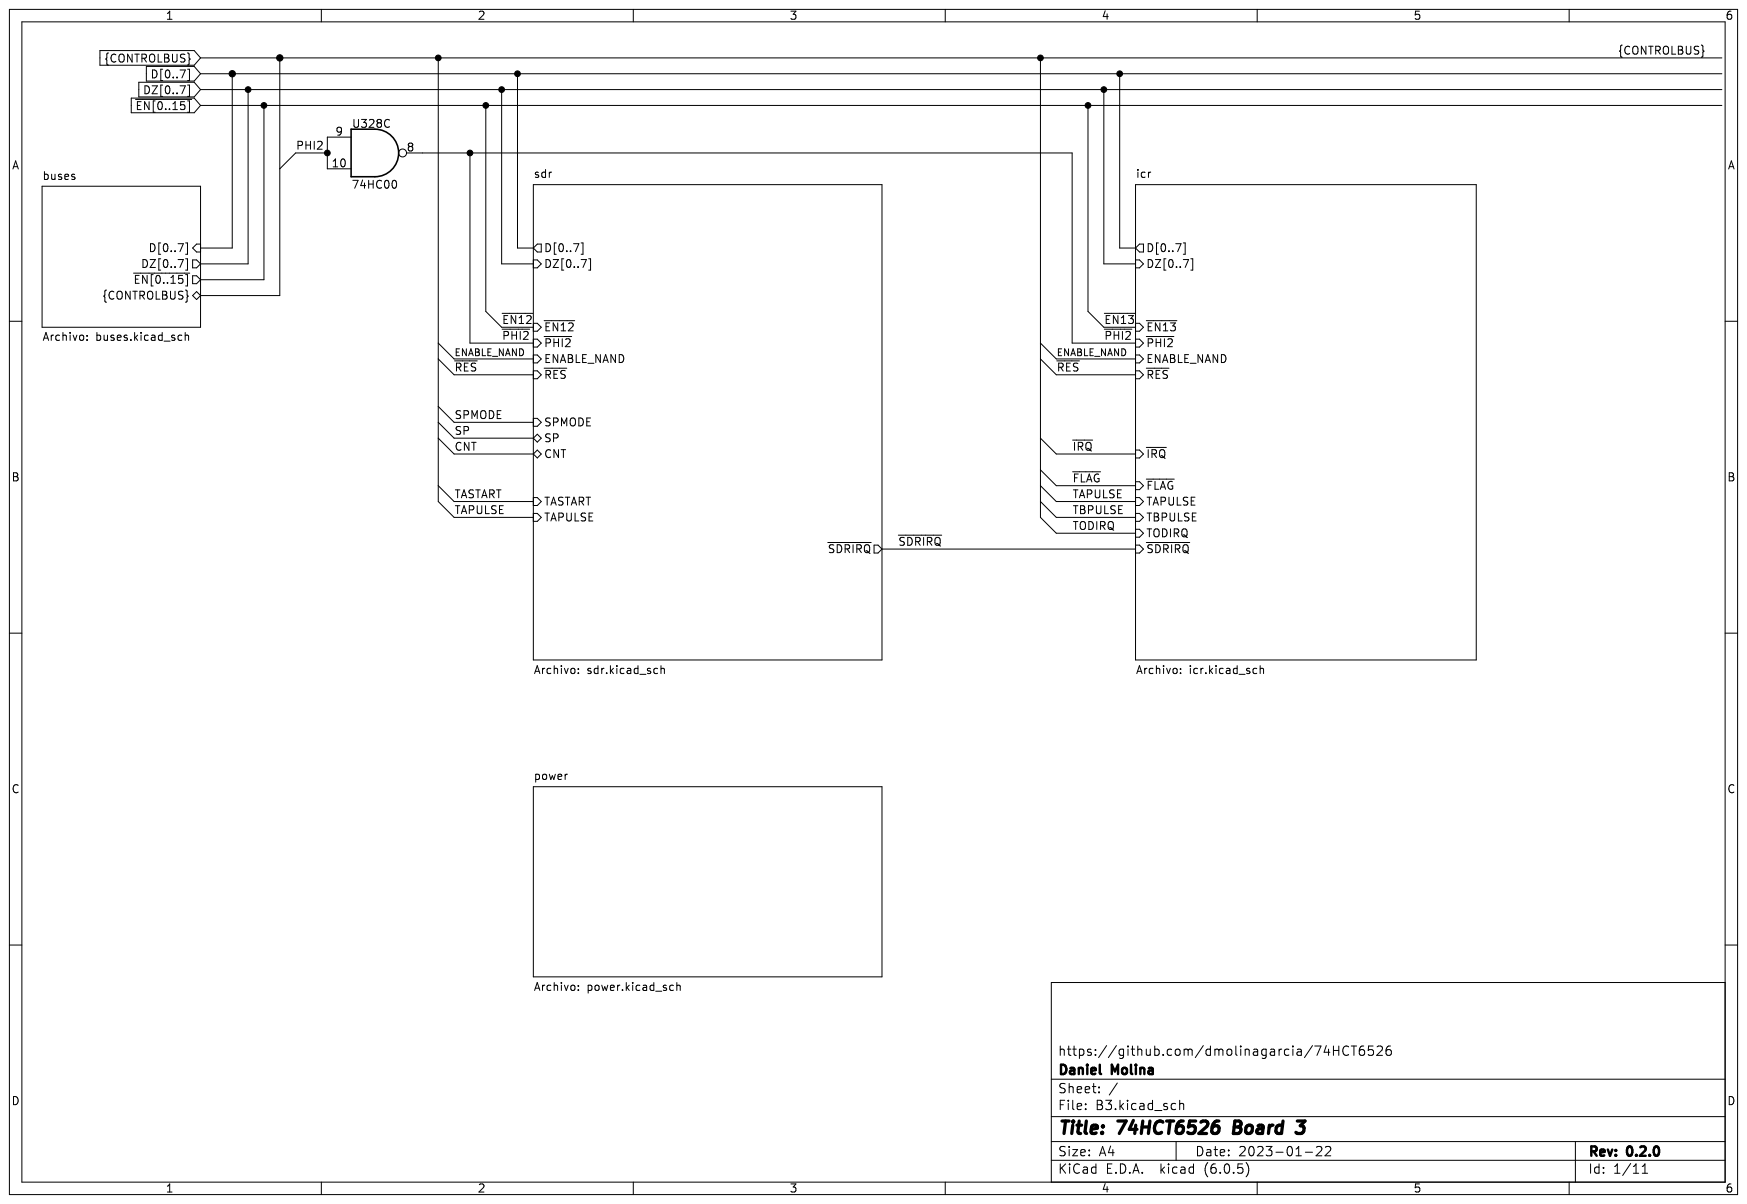
[picture p202: page 1]


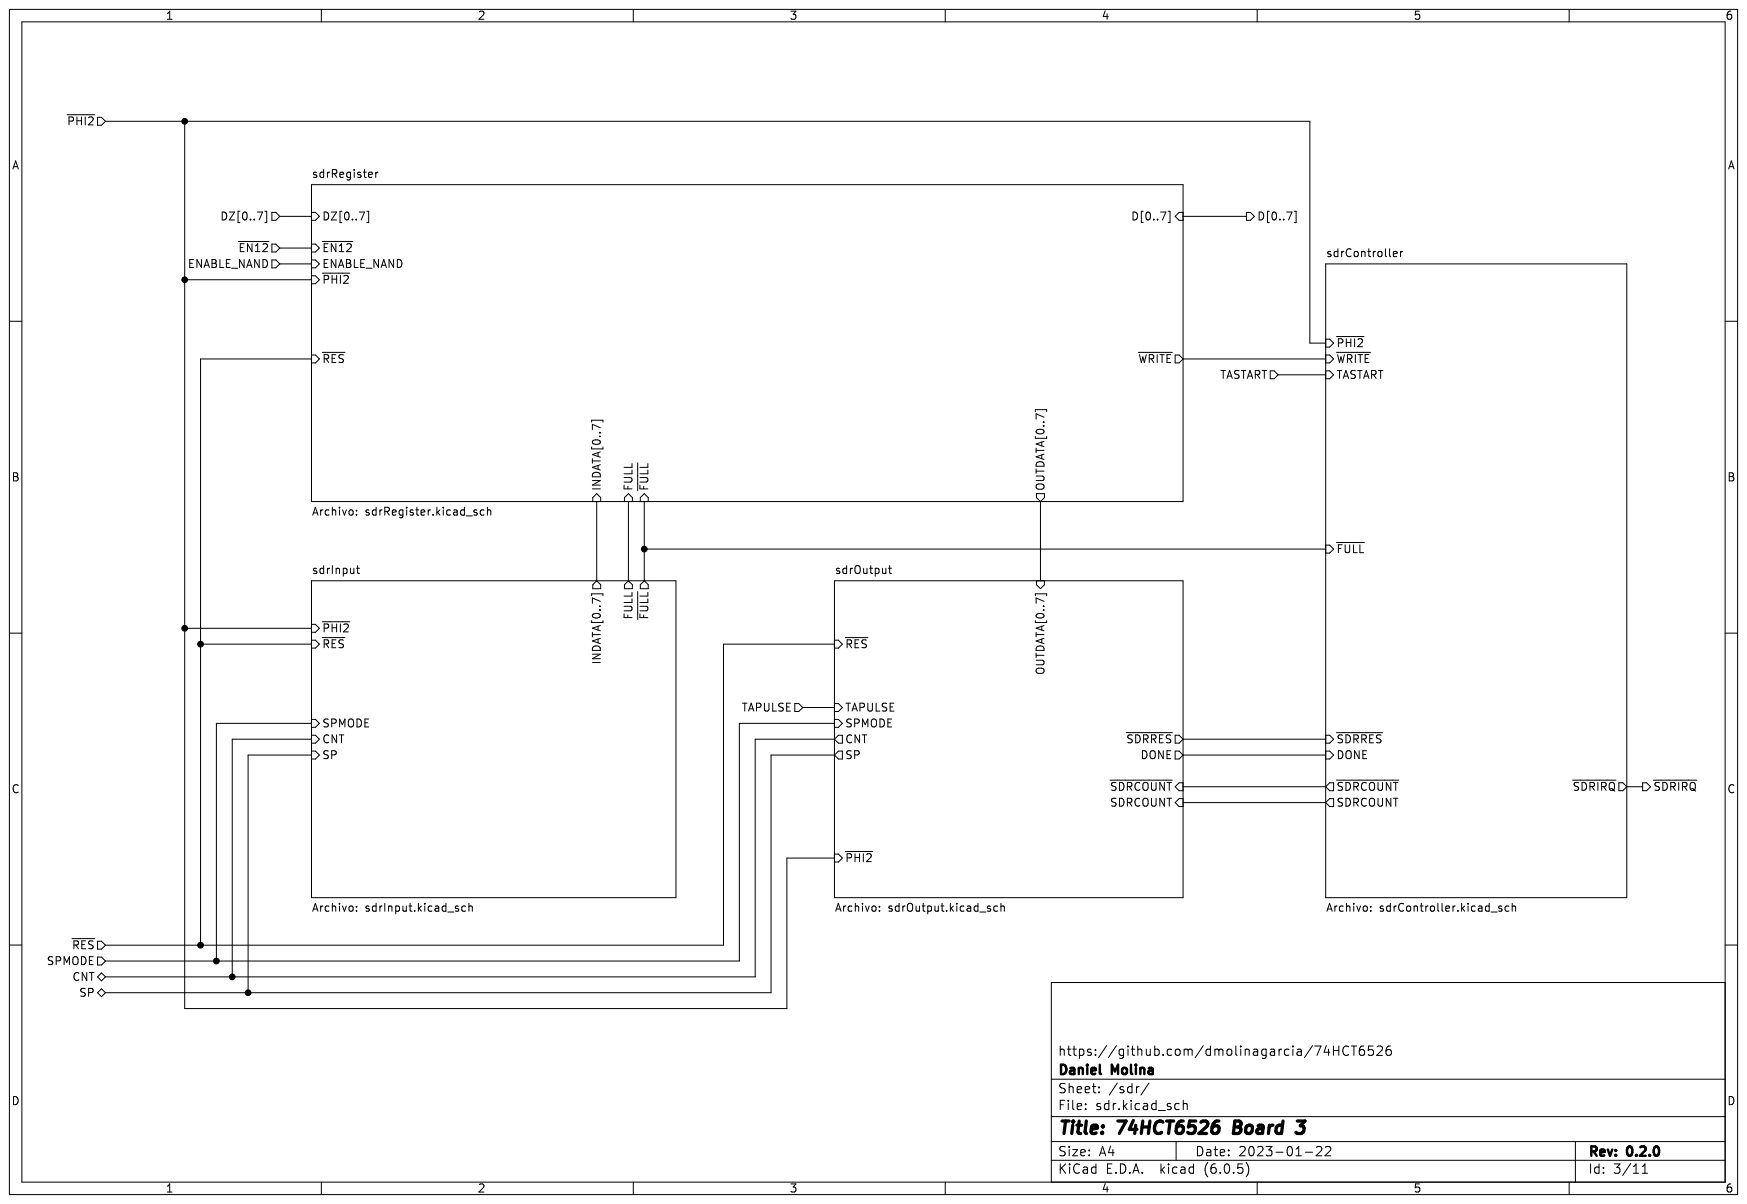
[picture p203: page 3]

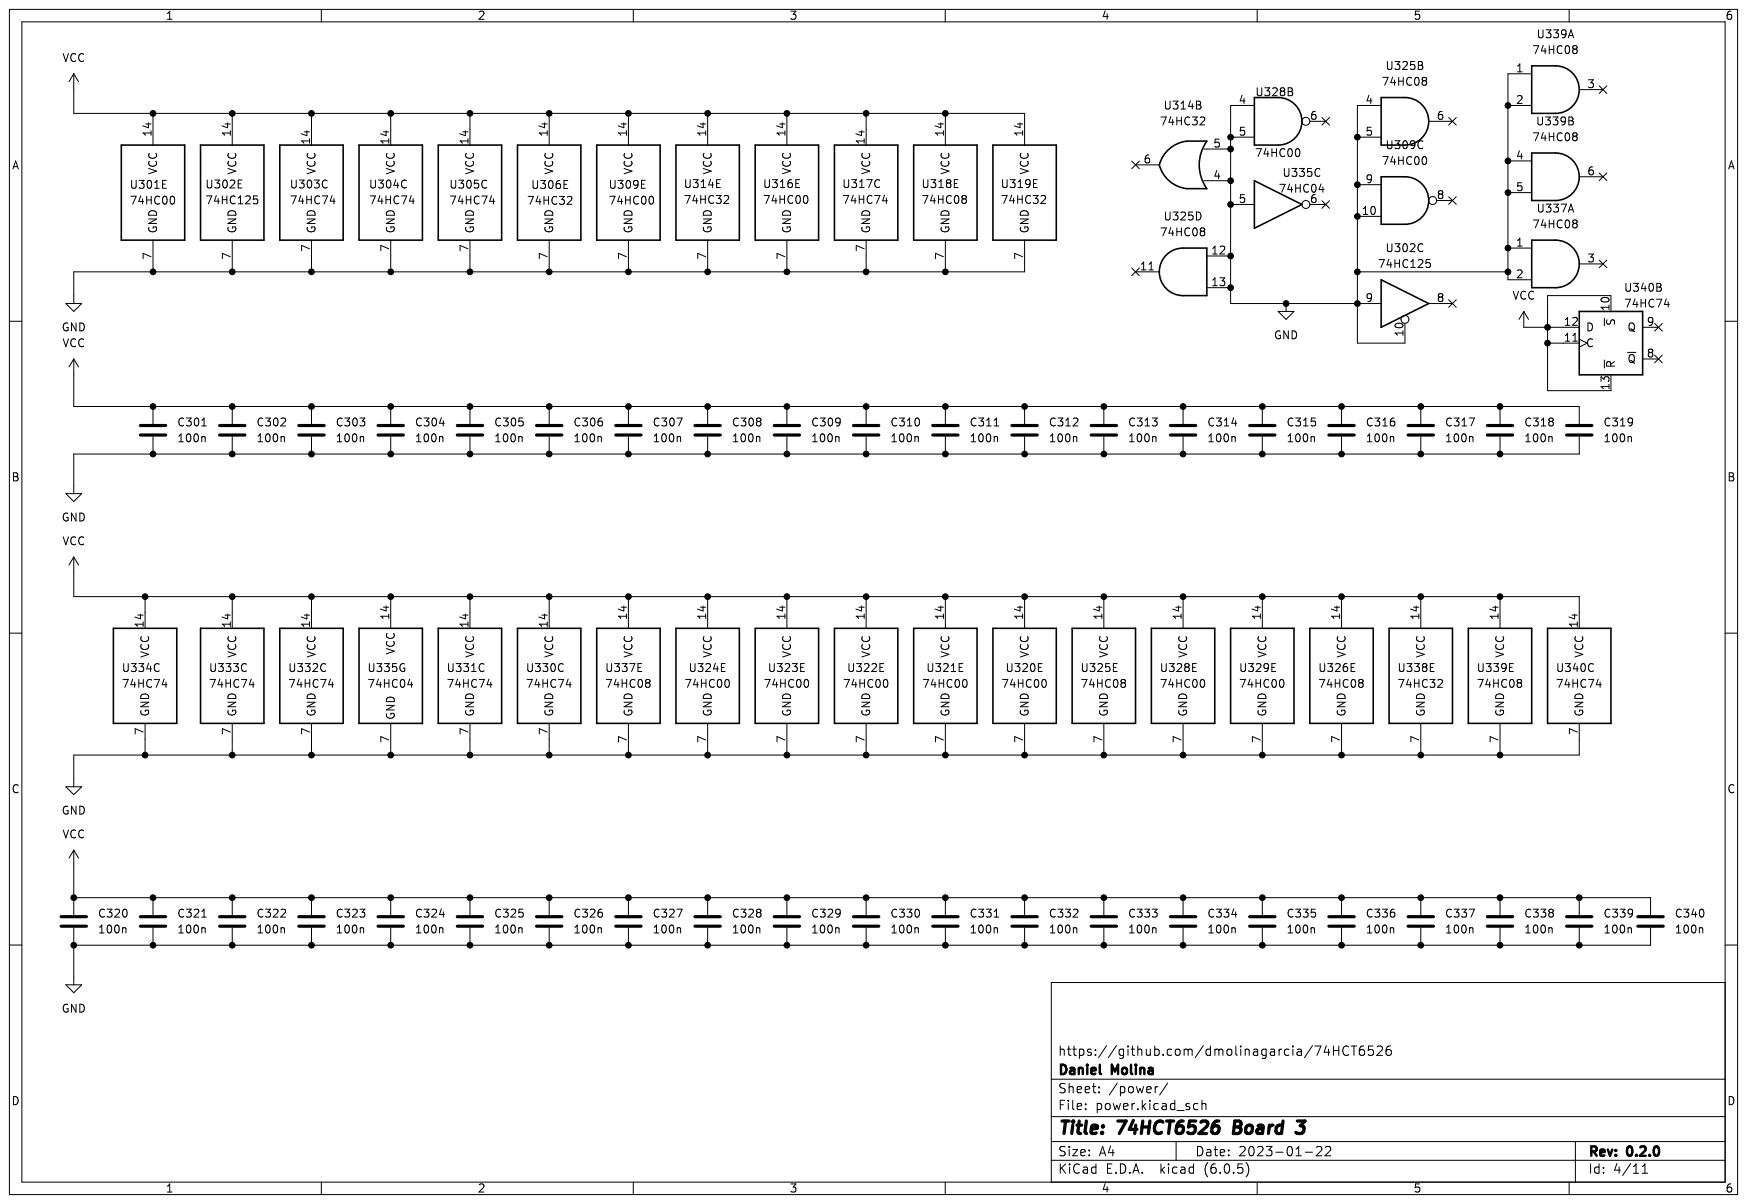
[picture p204: page 4]

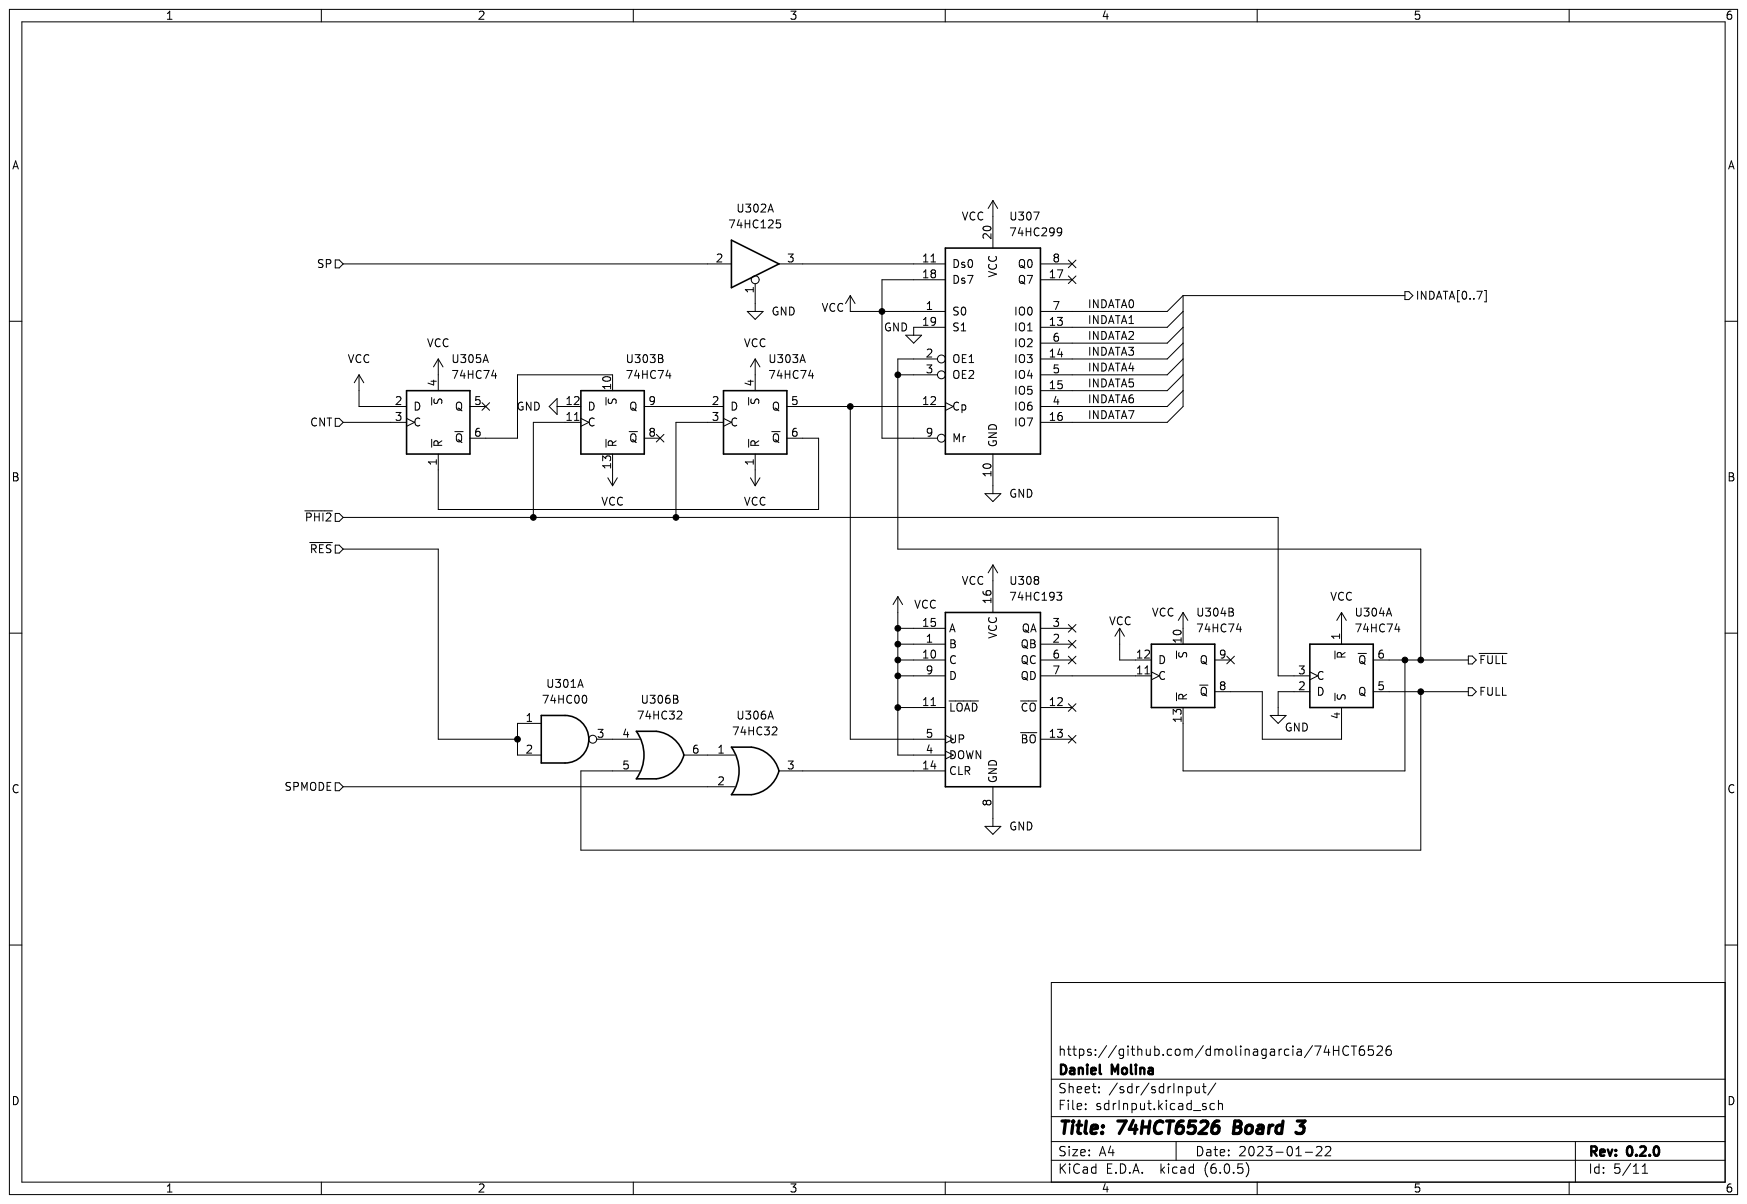
[picture p205: page 5]

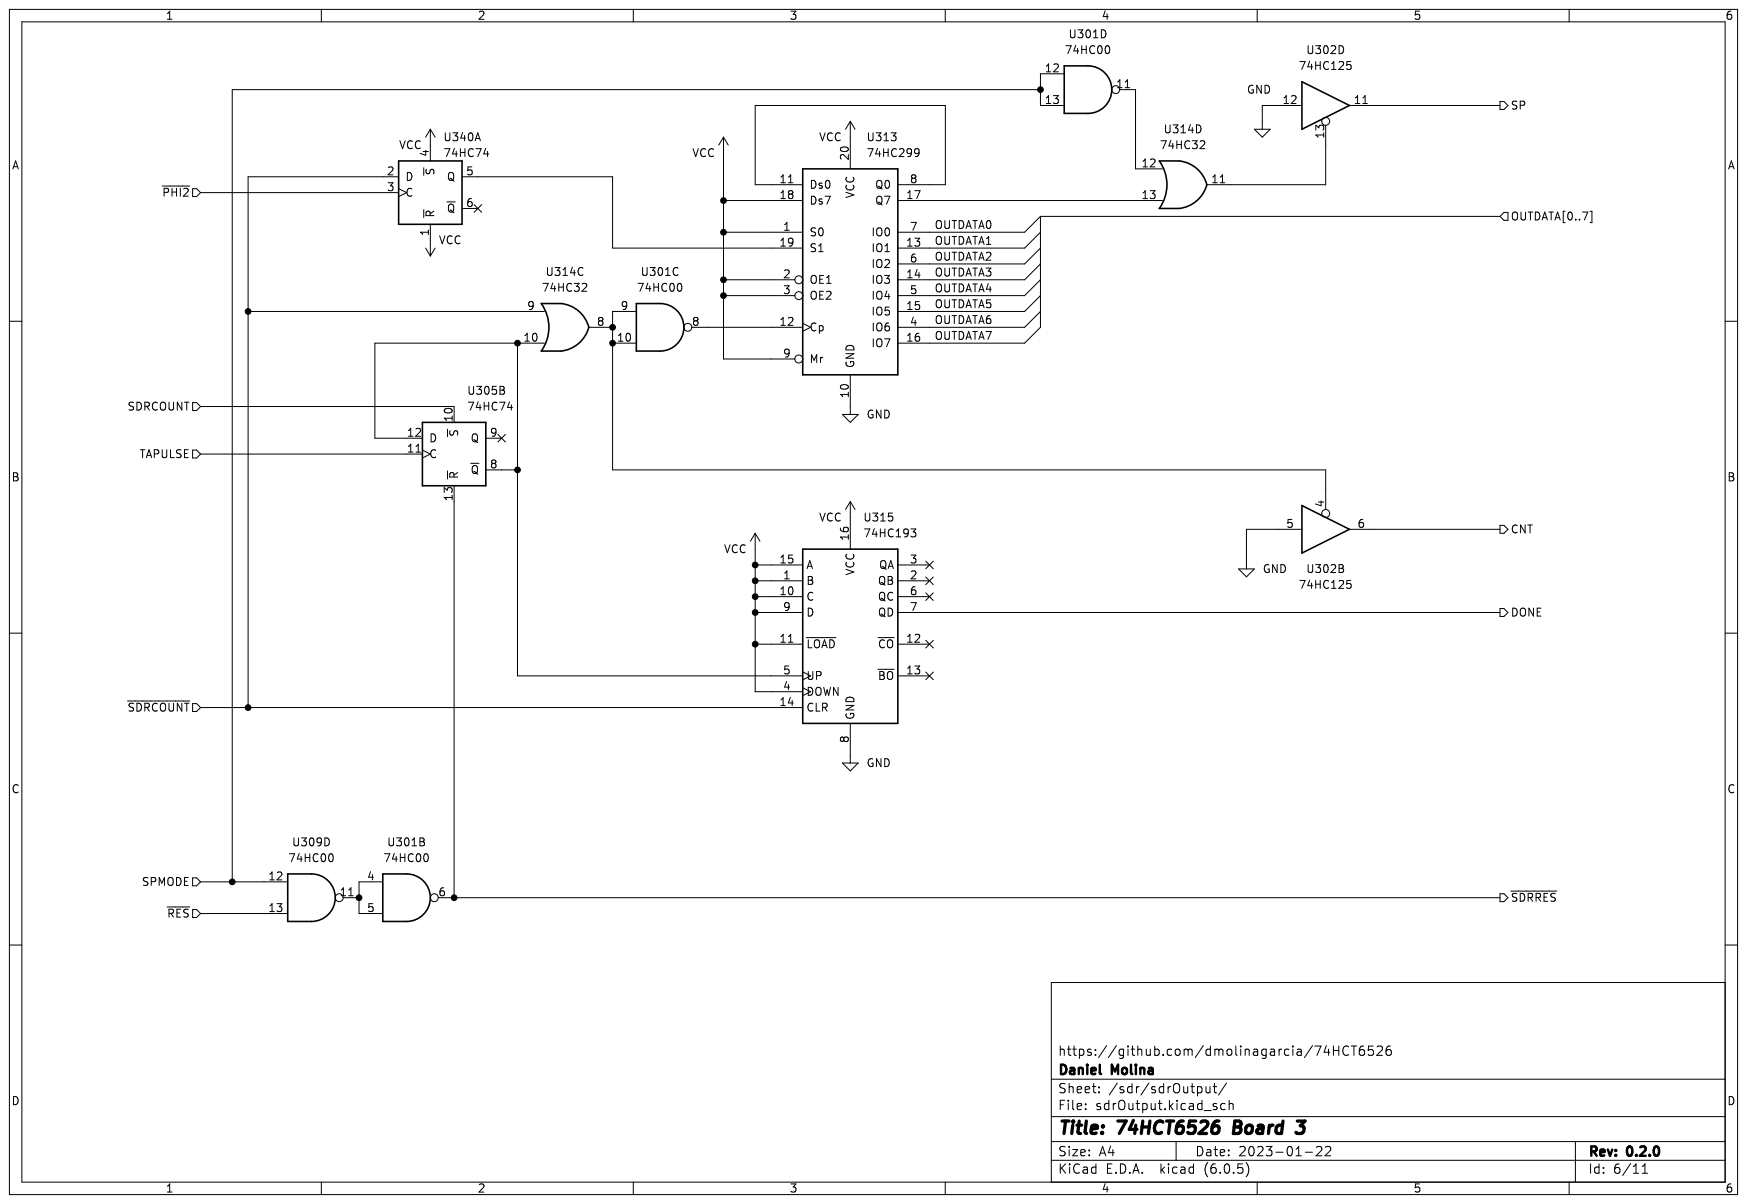
[picture p206: page 6]

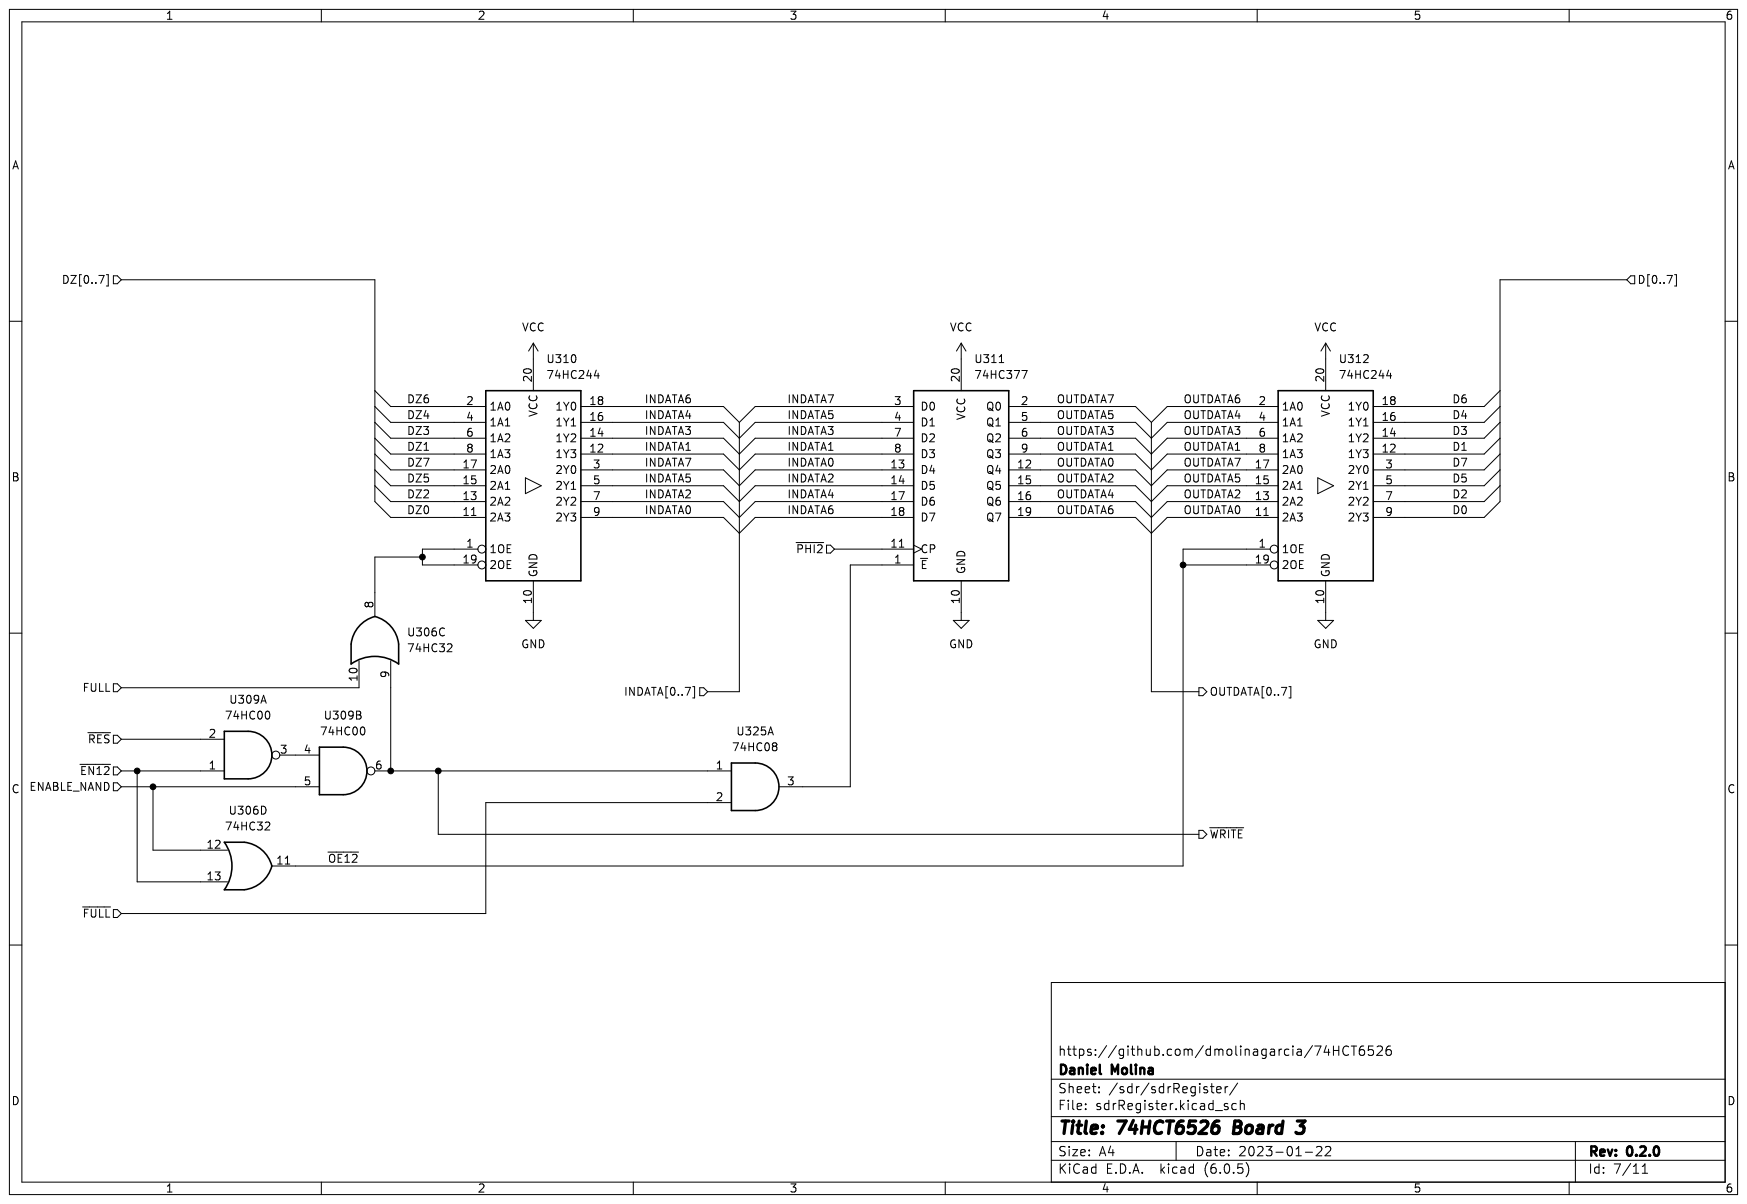
[picture p207: page 7]

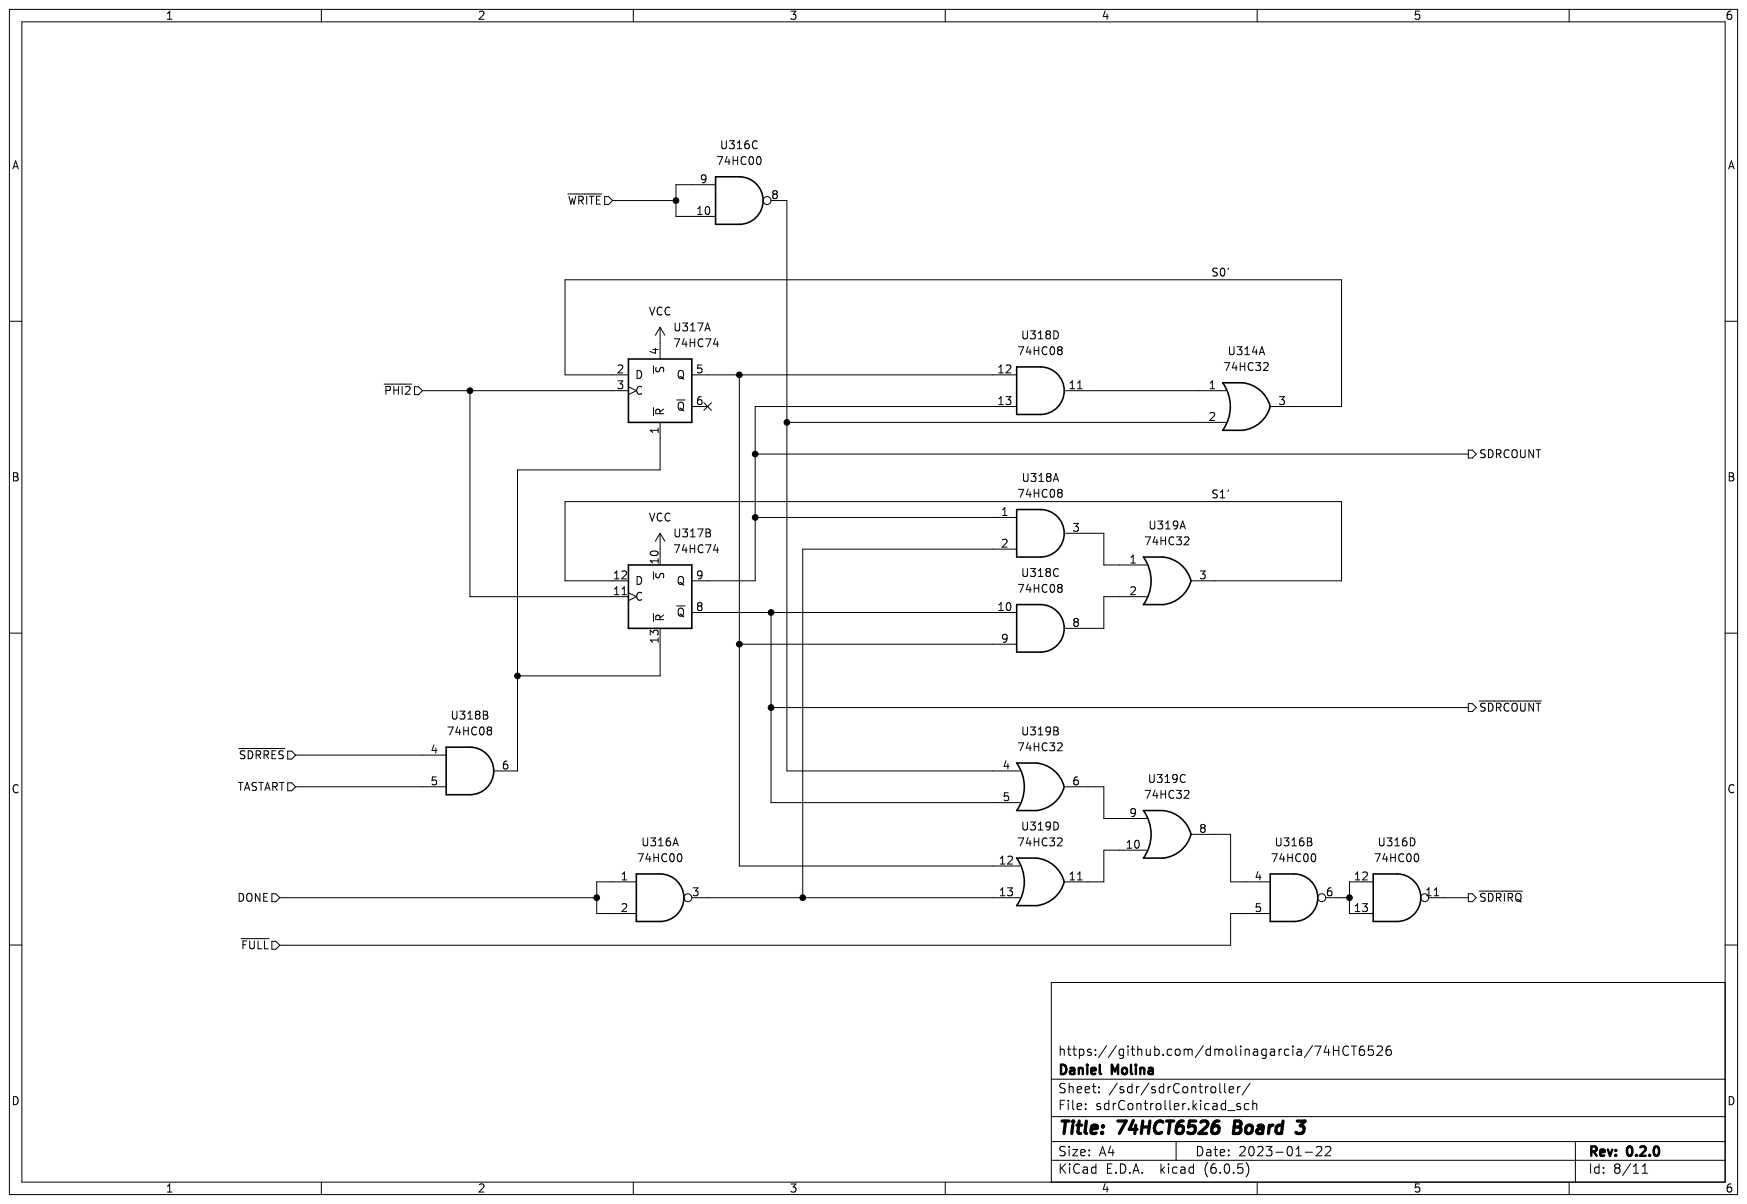
[picture p208: page 8]

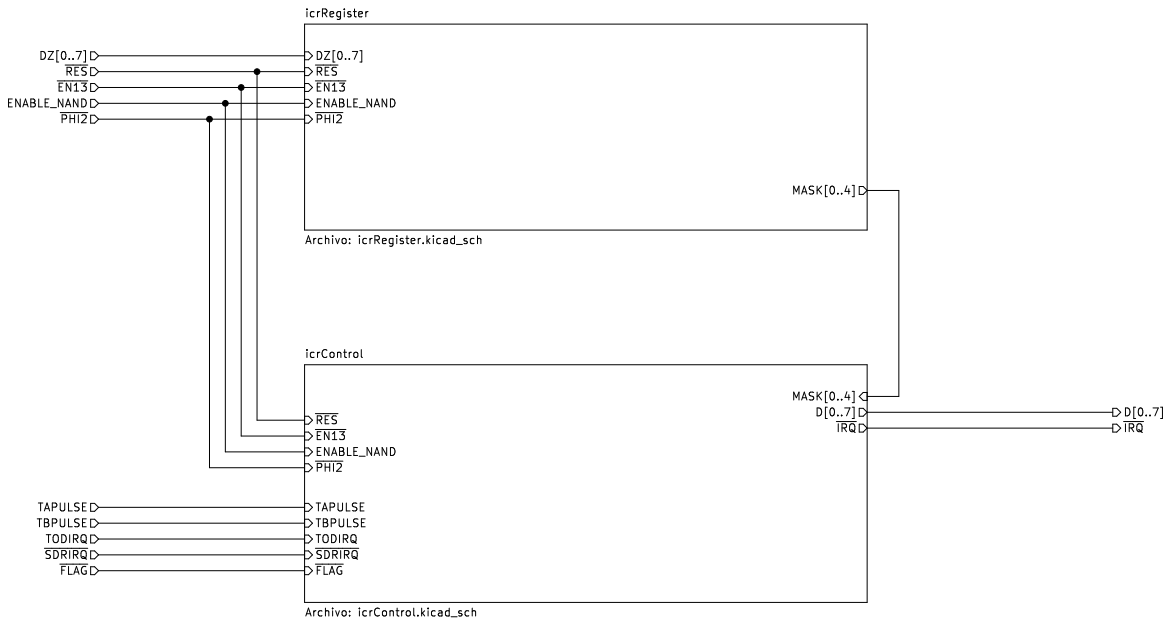
[picture p209: page 9]

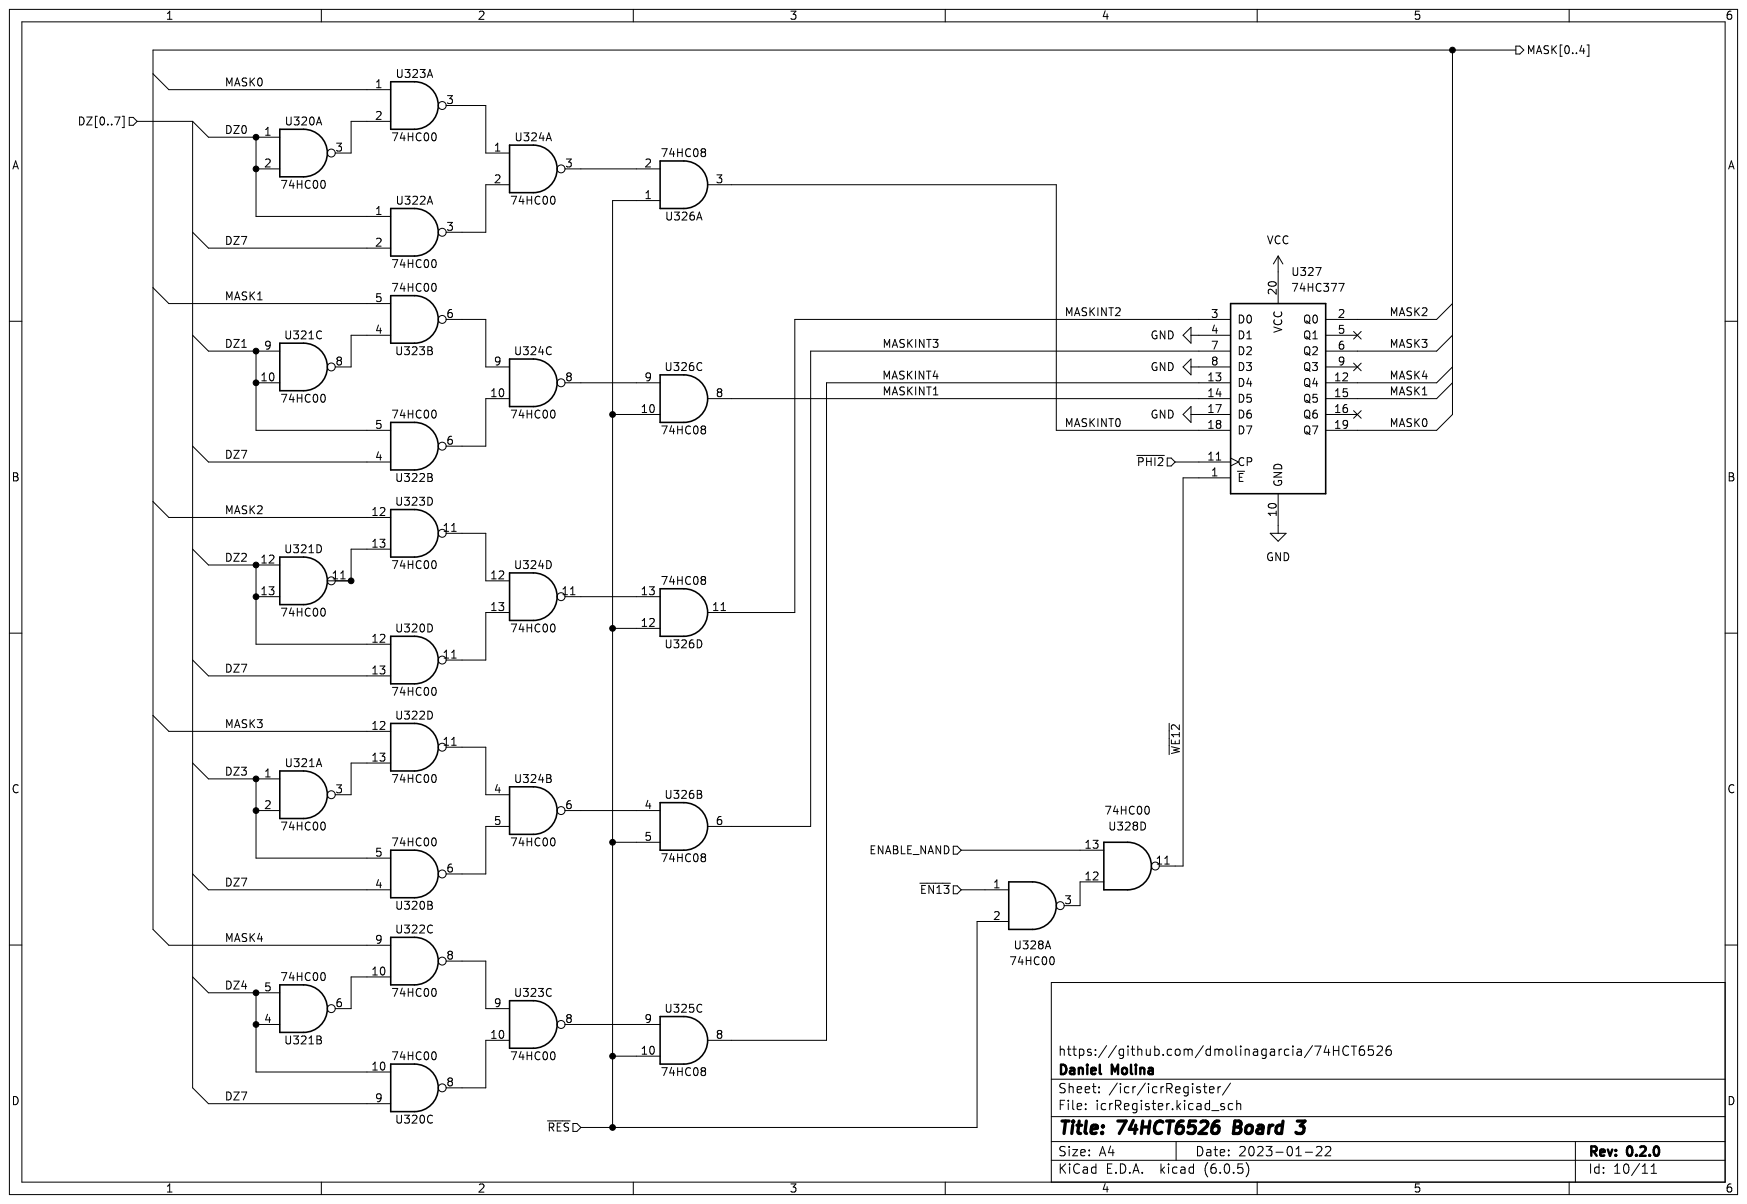
[picture p210: page 10]

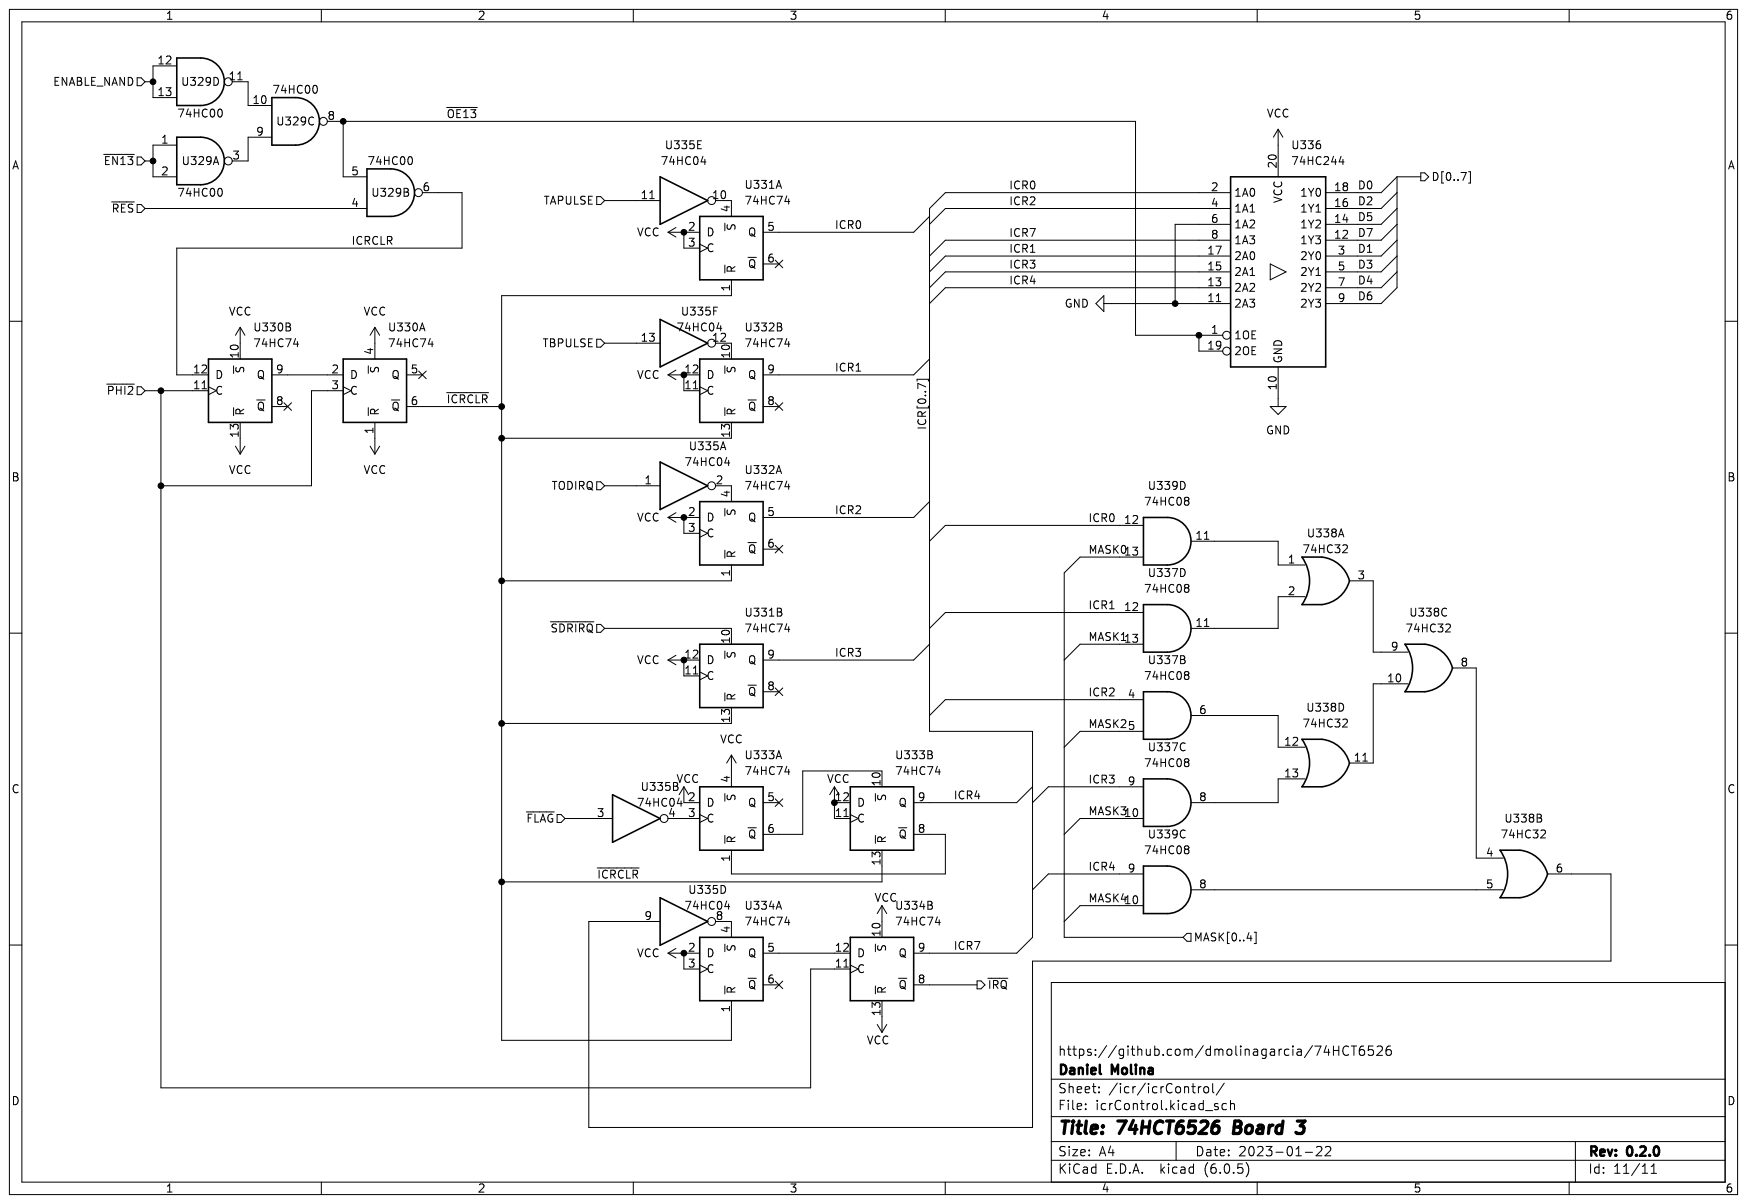
[picture p211: page 11]
