dmolinagarcia/74HCT6526/pdf/B2.sch.v0.2.0.pdf

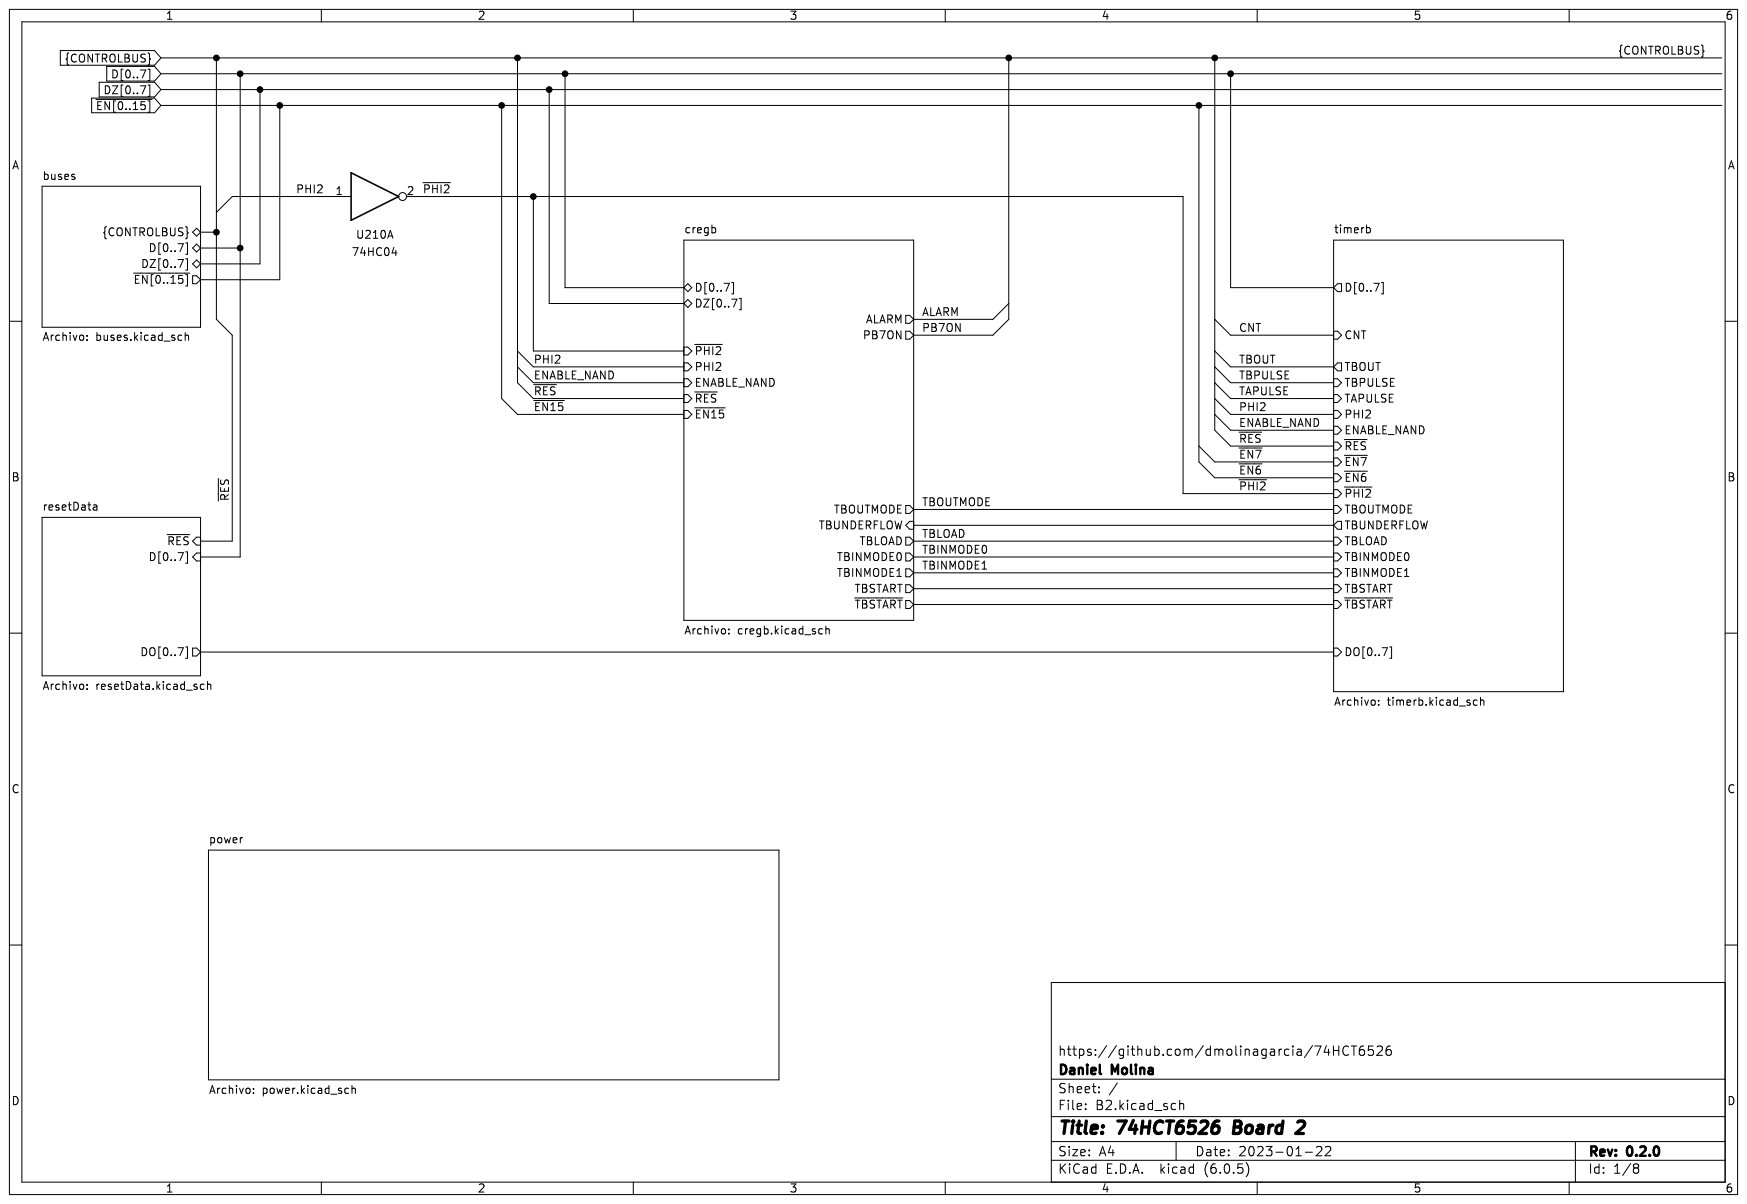
[picture p212: page 1]


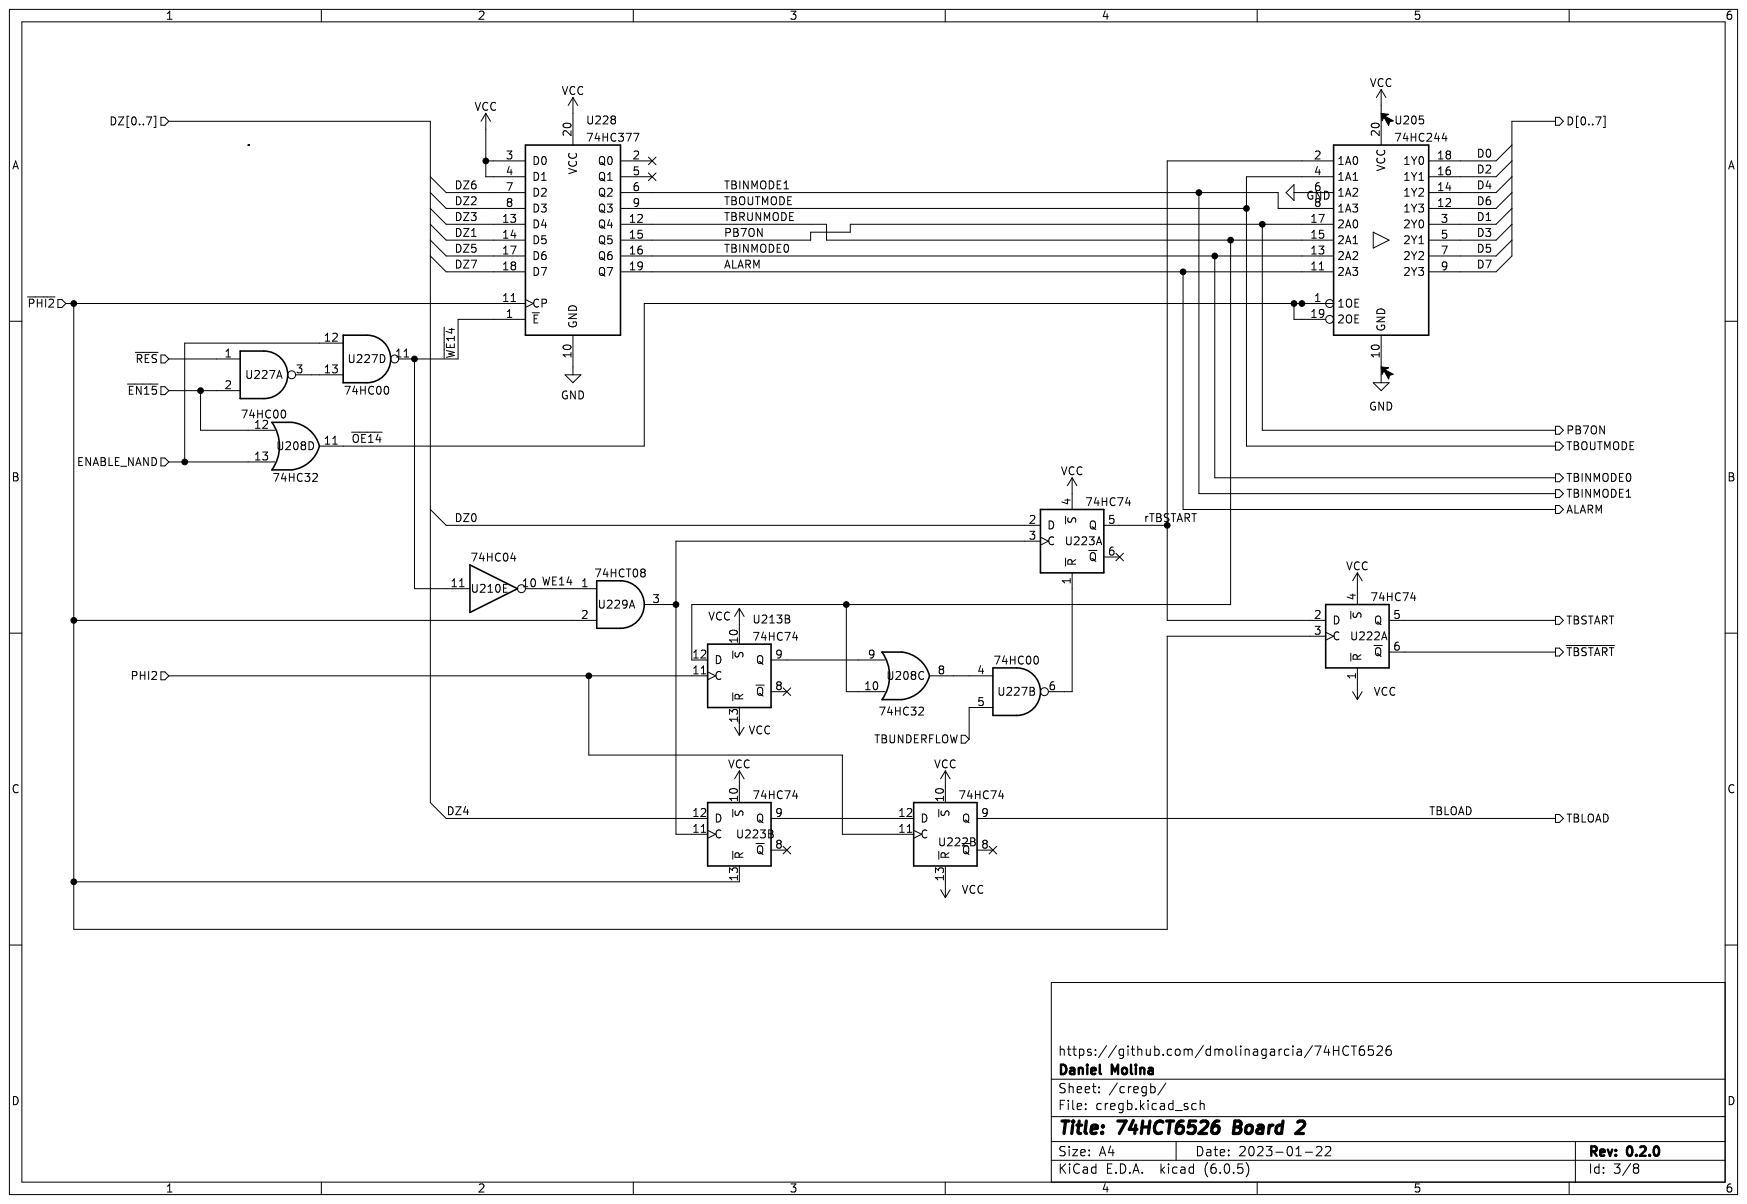
[picture p213: page 3]

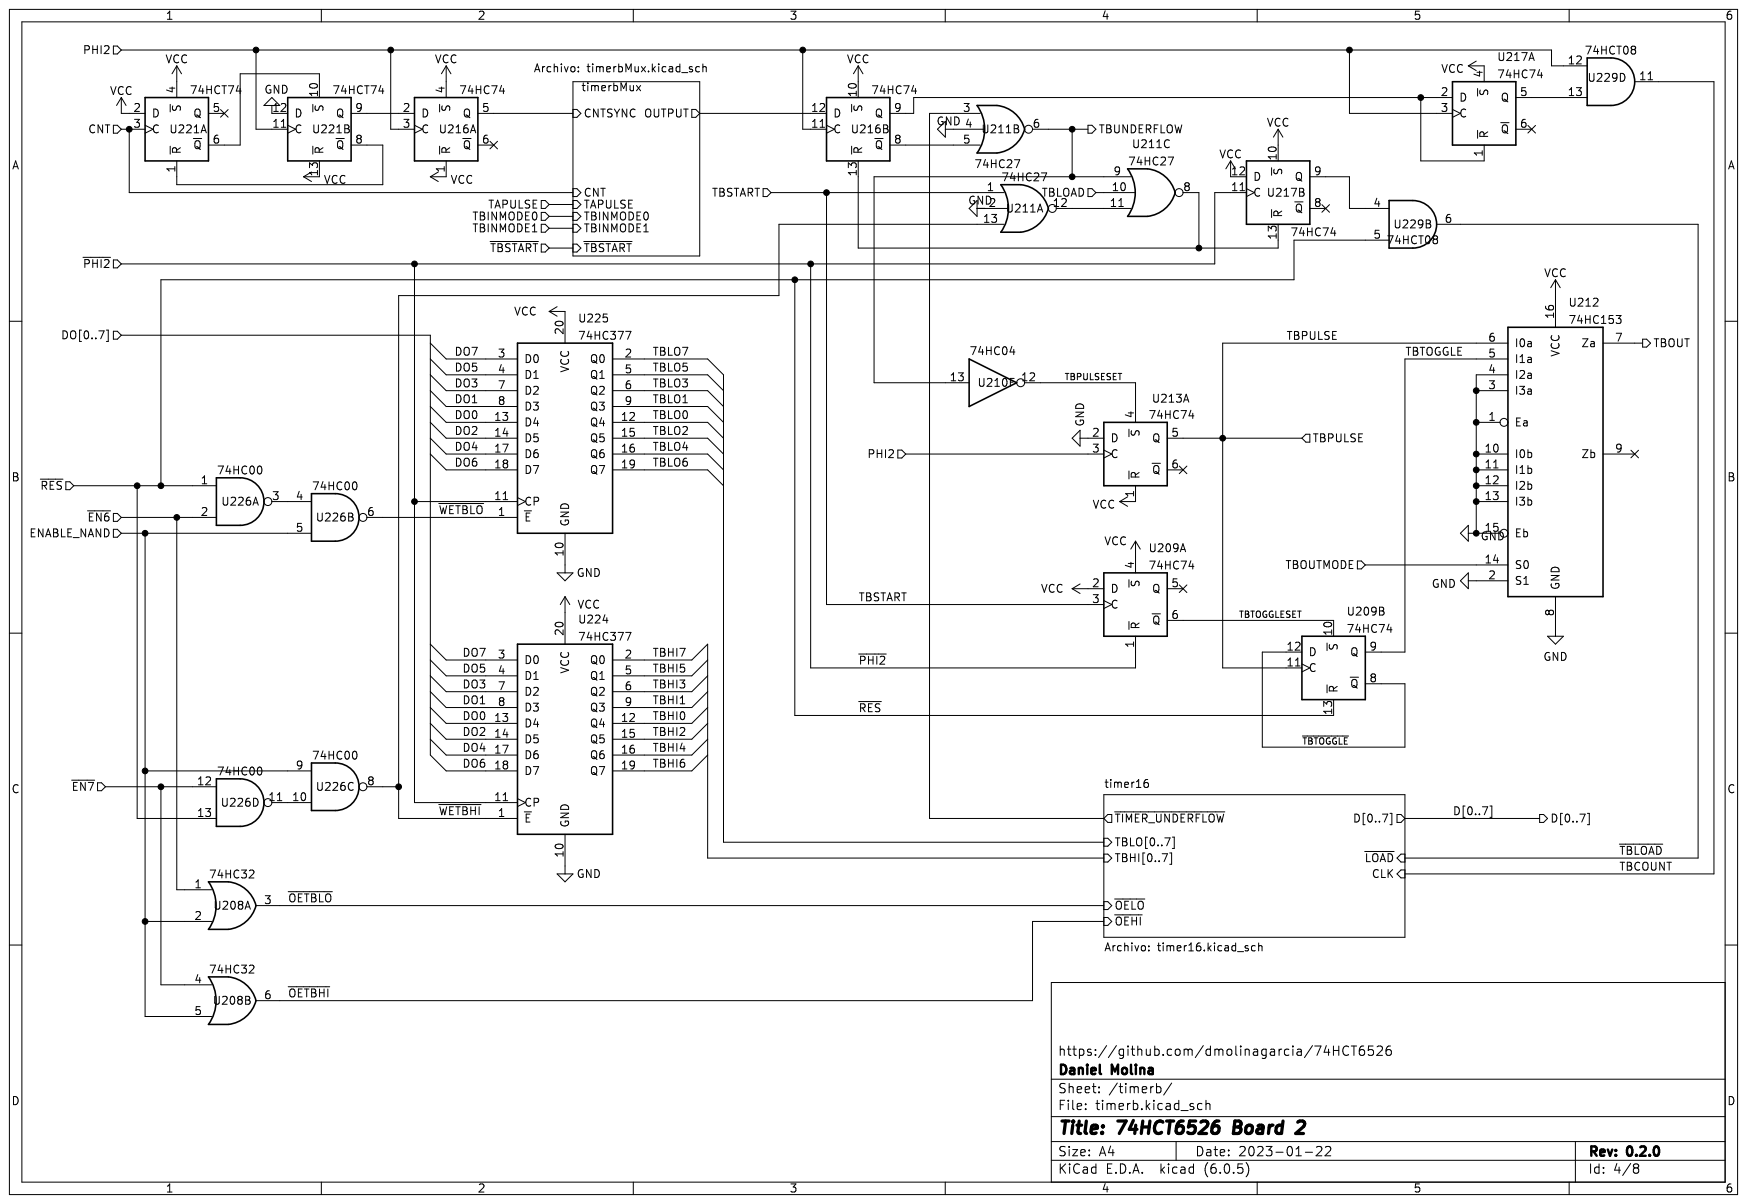
[picture p214: page 4]


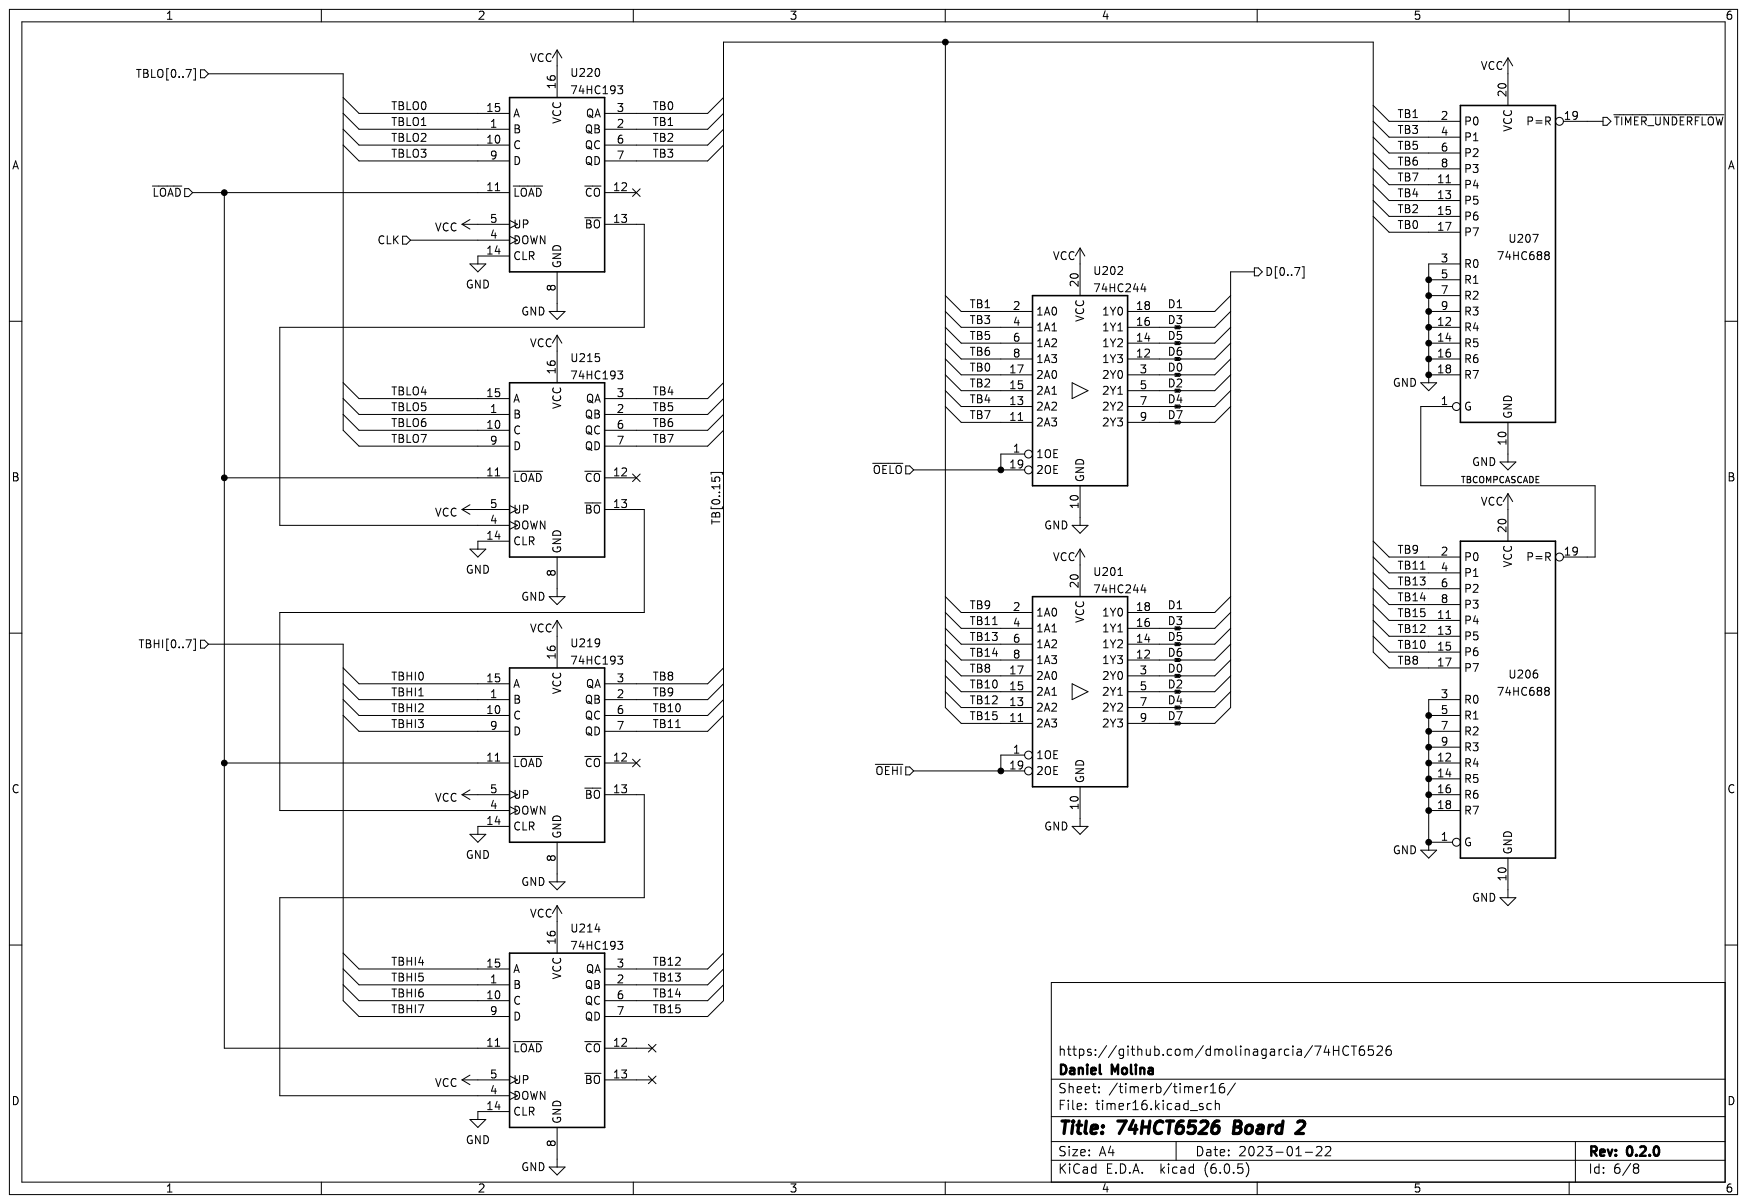
[picture p215: page 6]

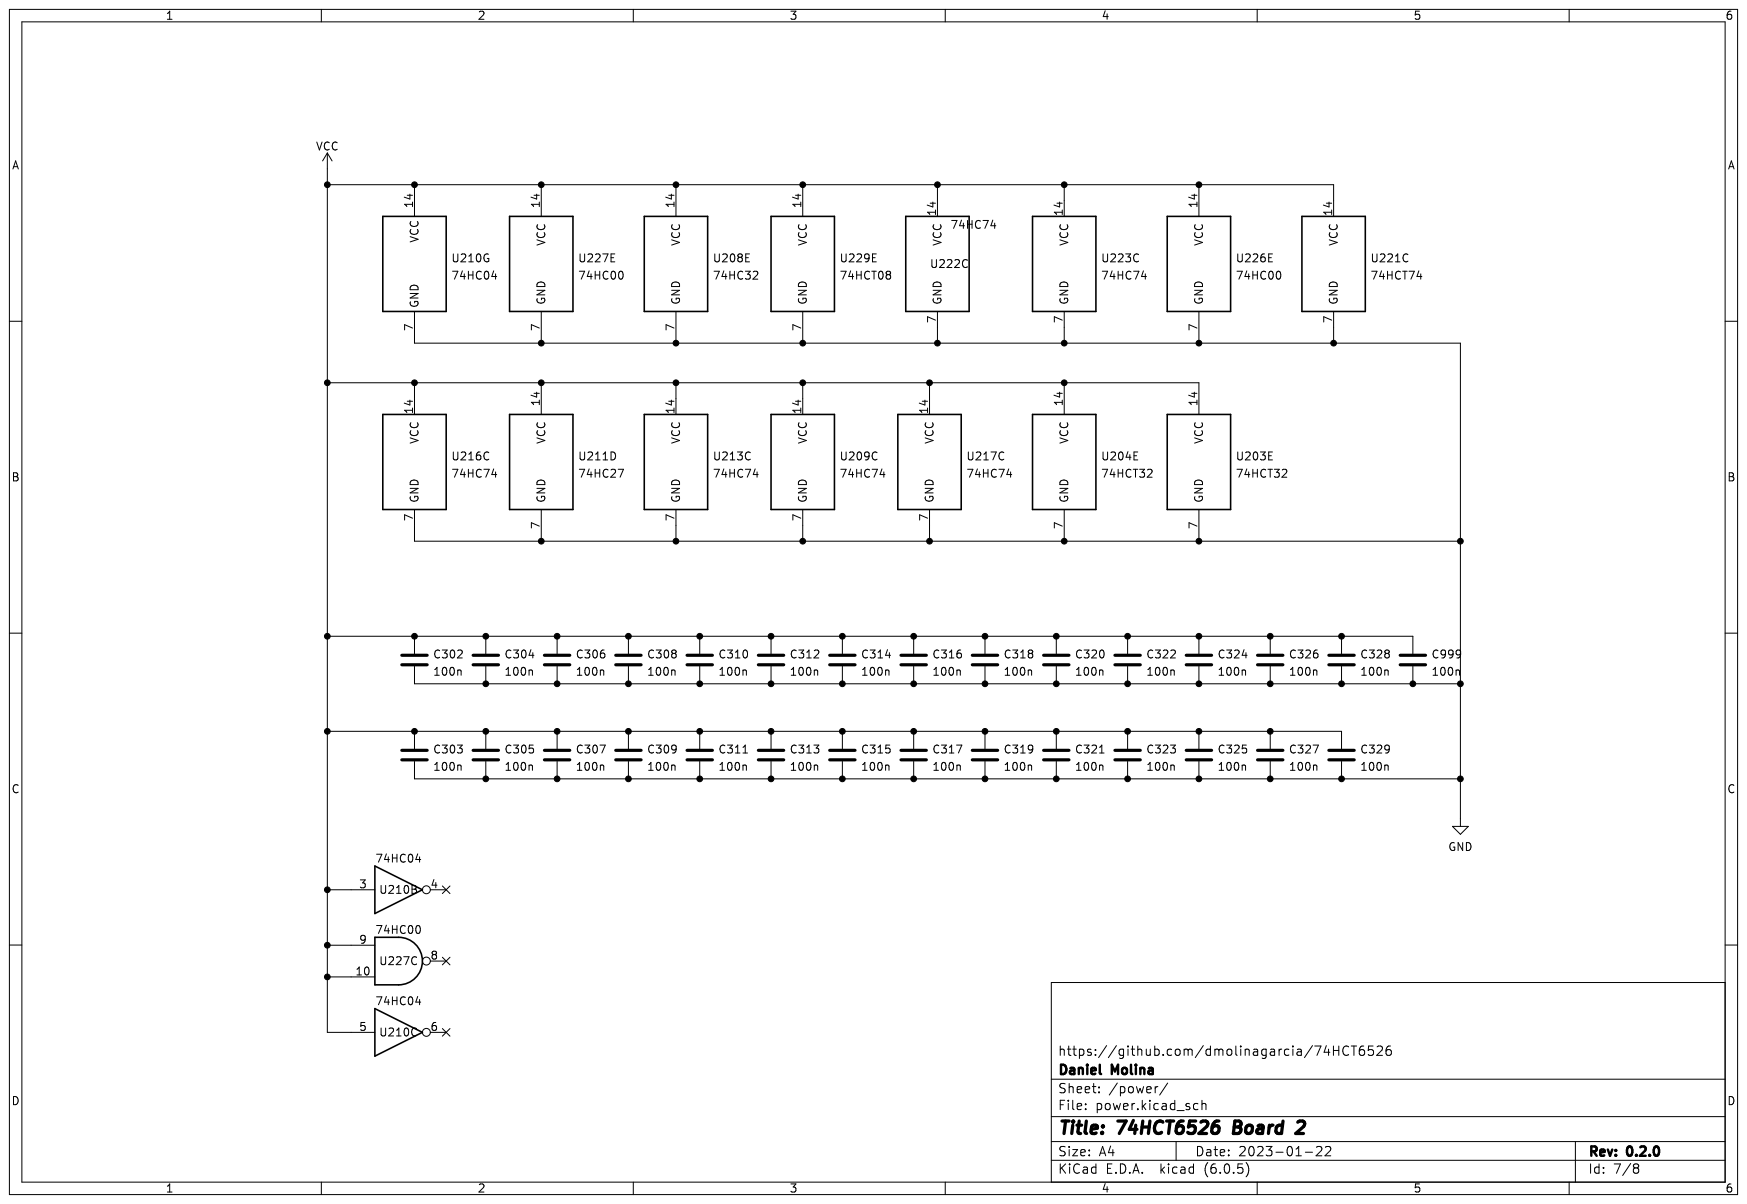
[picture p216: page 7]
