dmolinagarcia/74HCT6526/pdf/B1.sch.v0.2.0.pdf

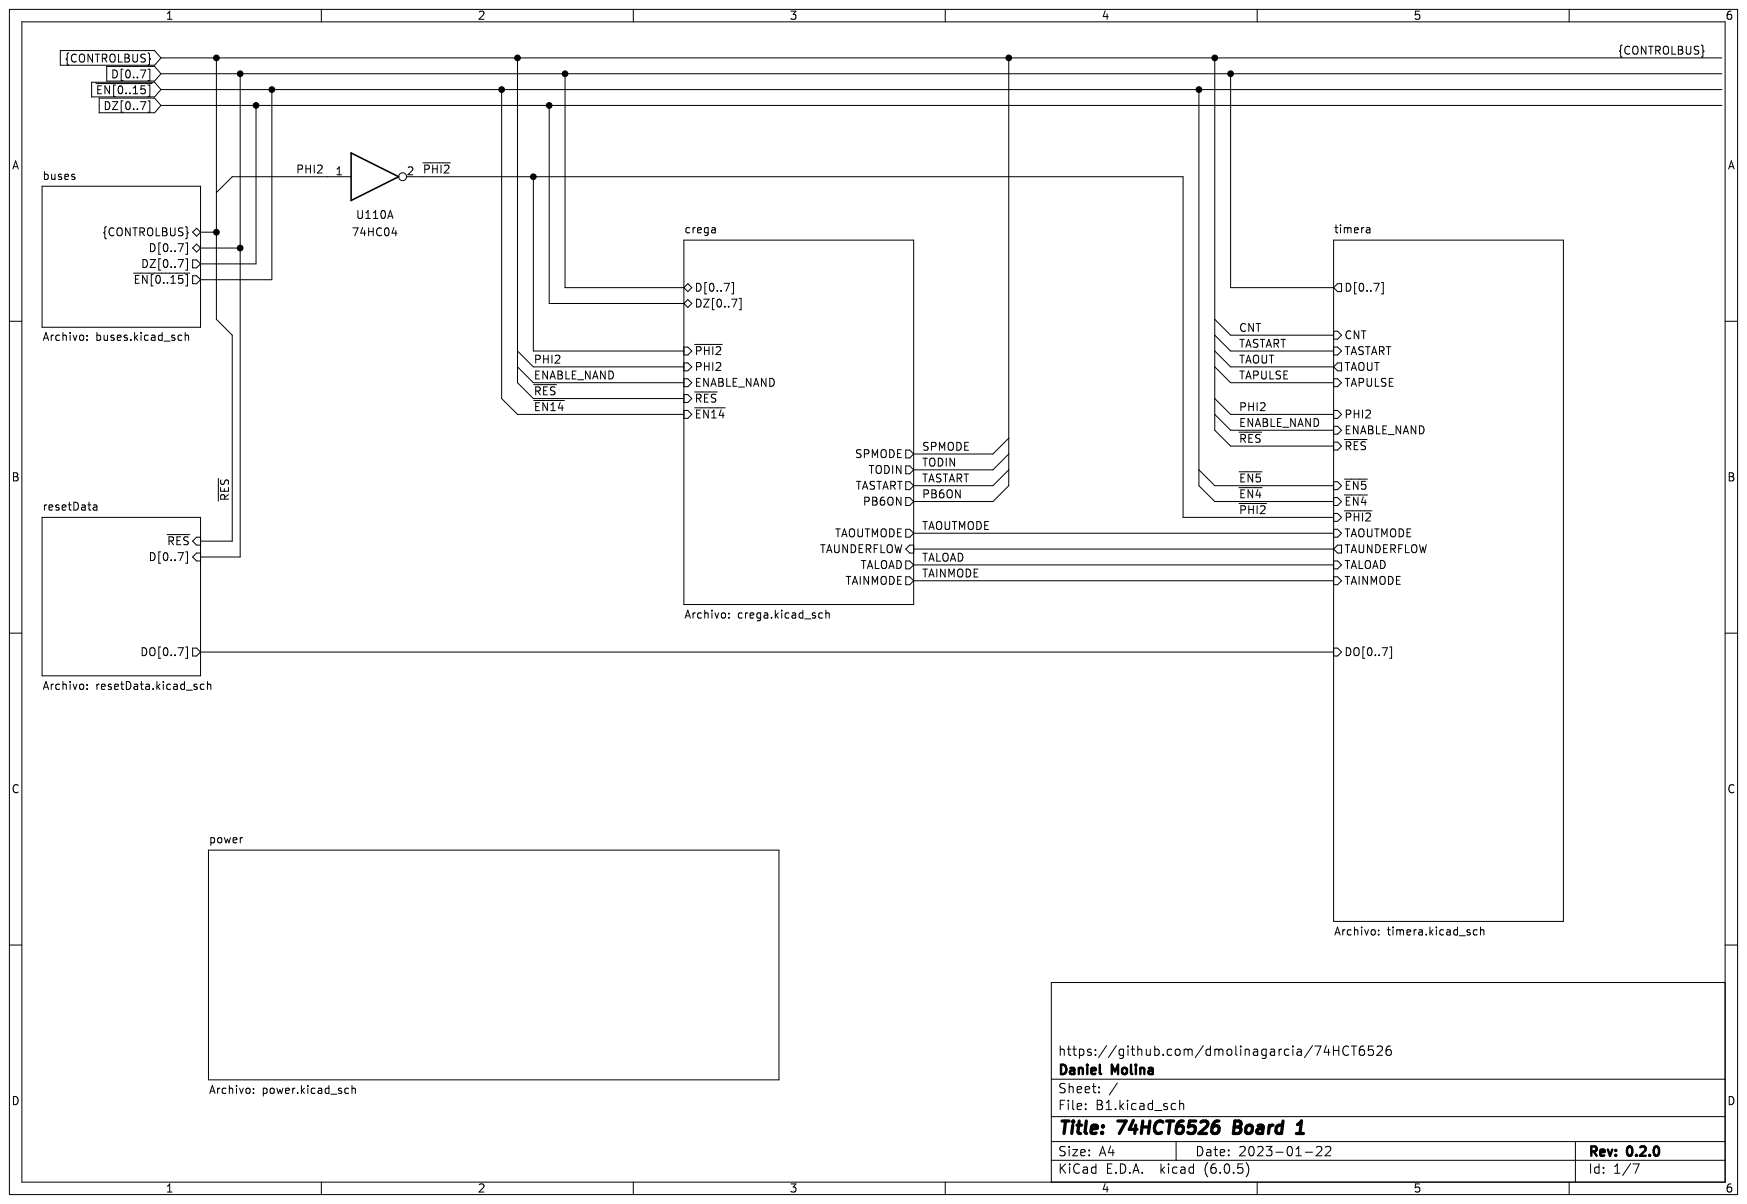
[picture p217: page 1]

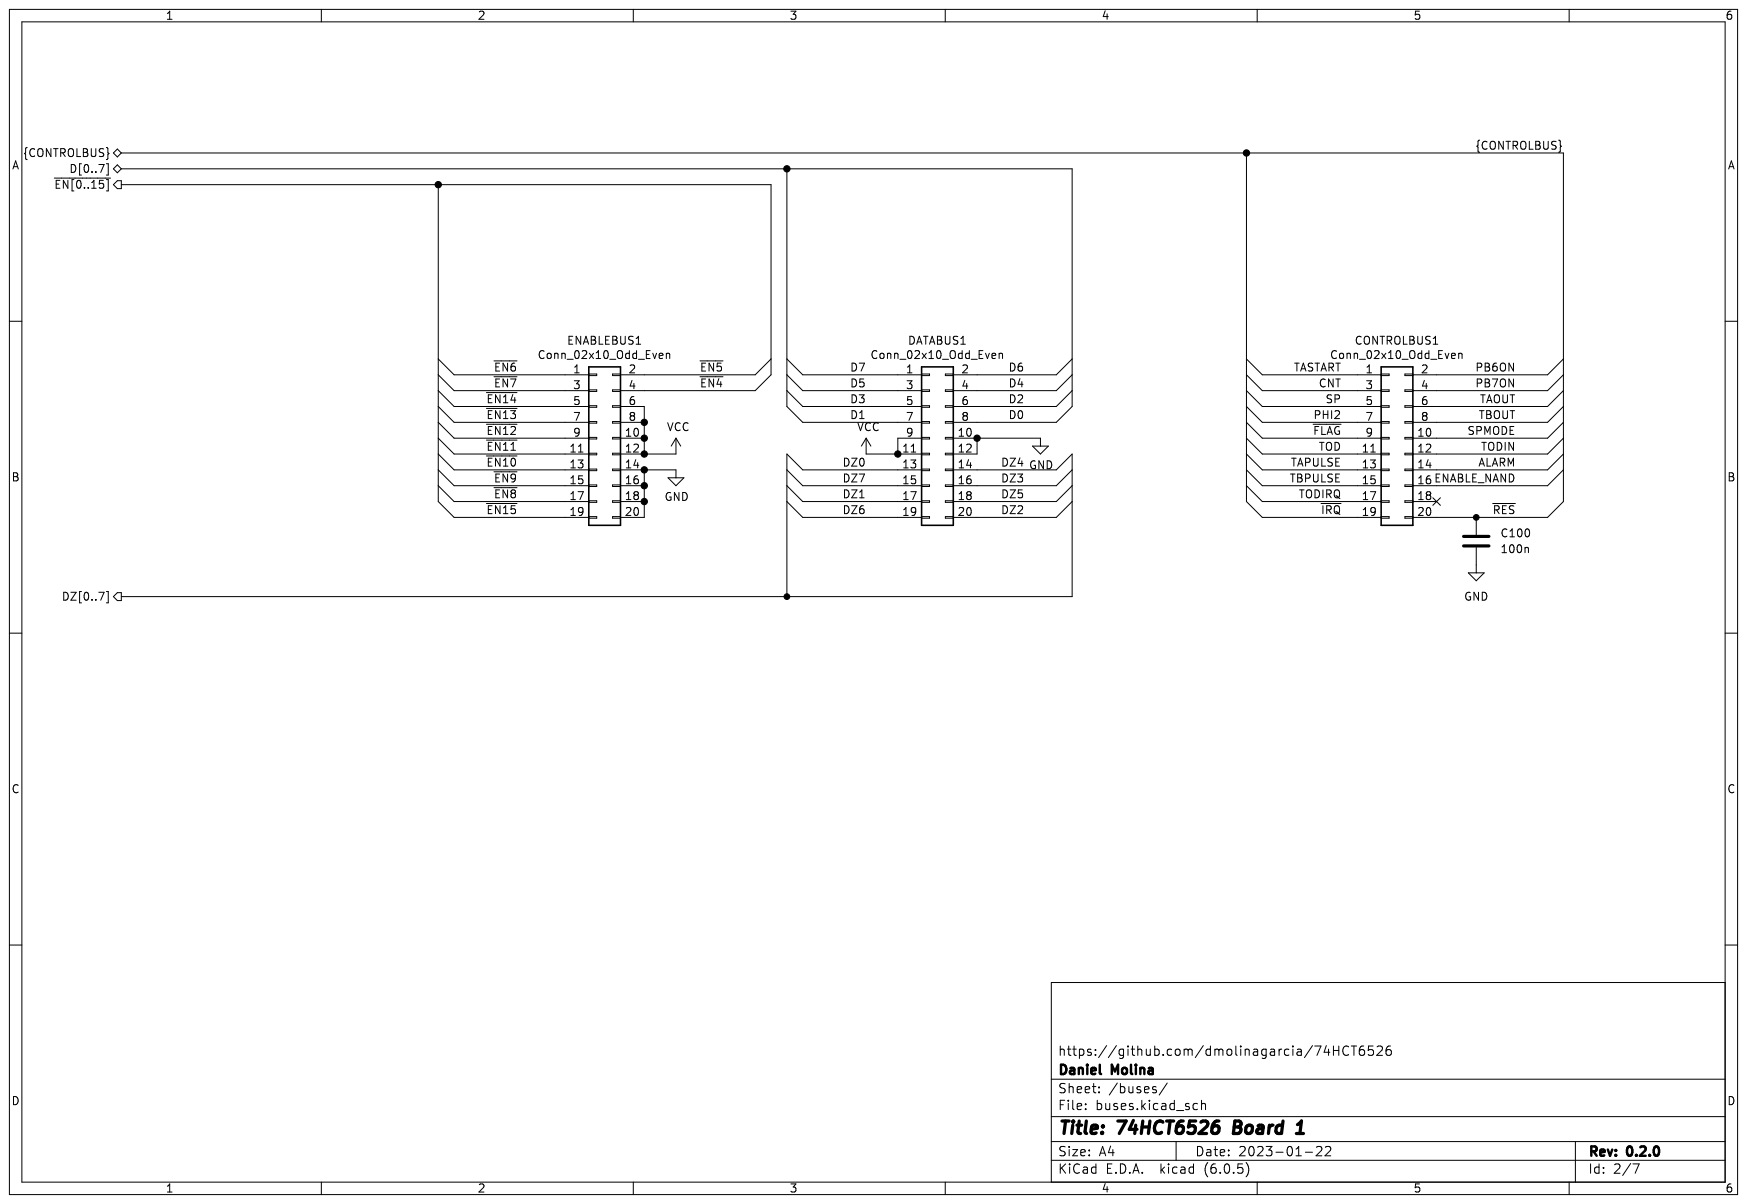
[picture p218: page 2]

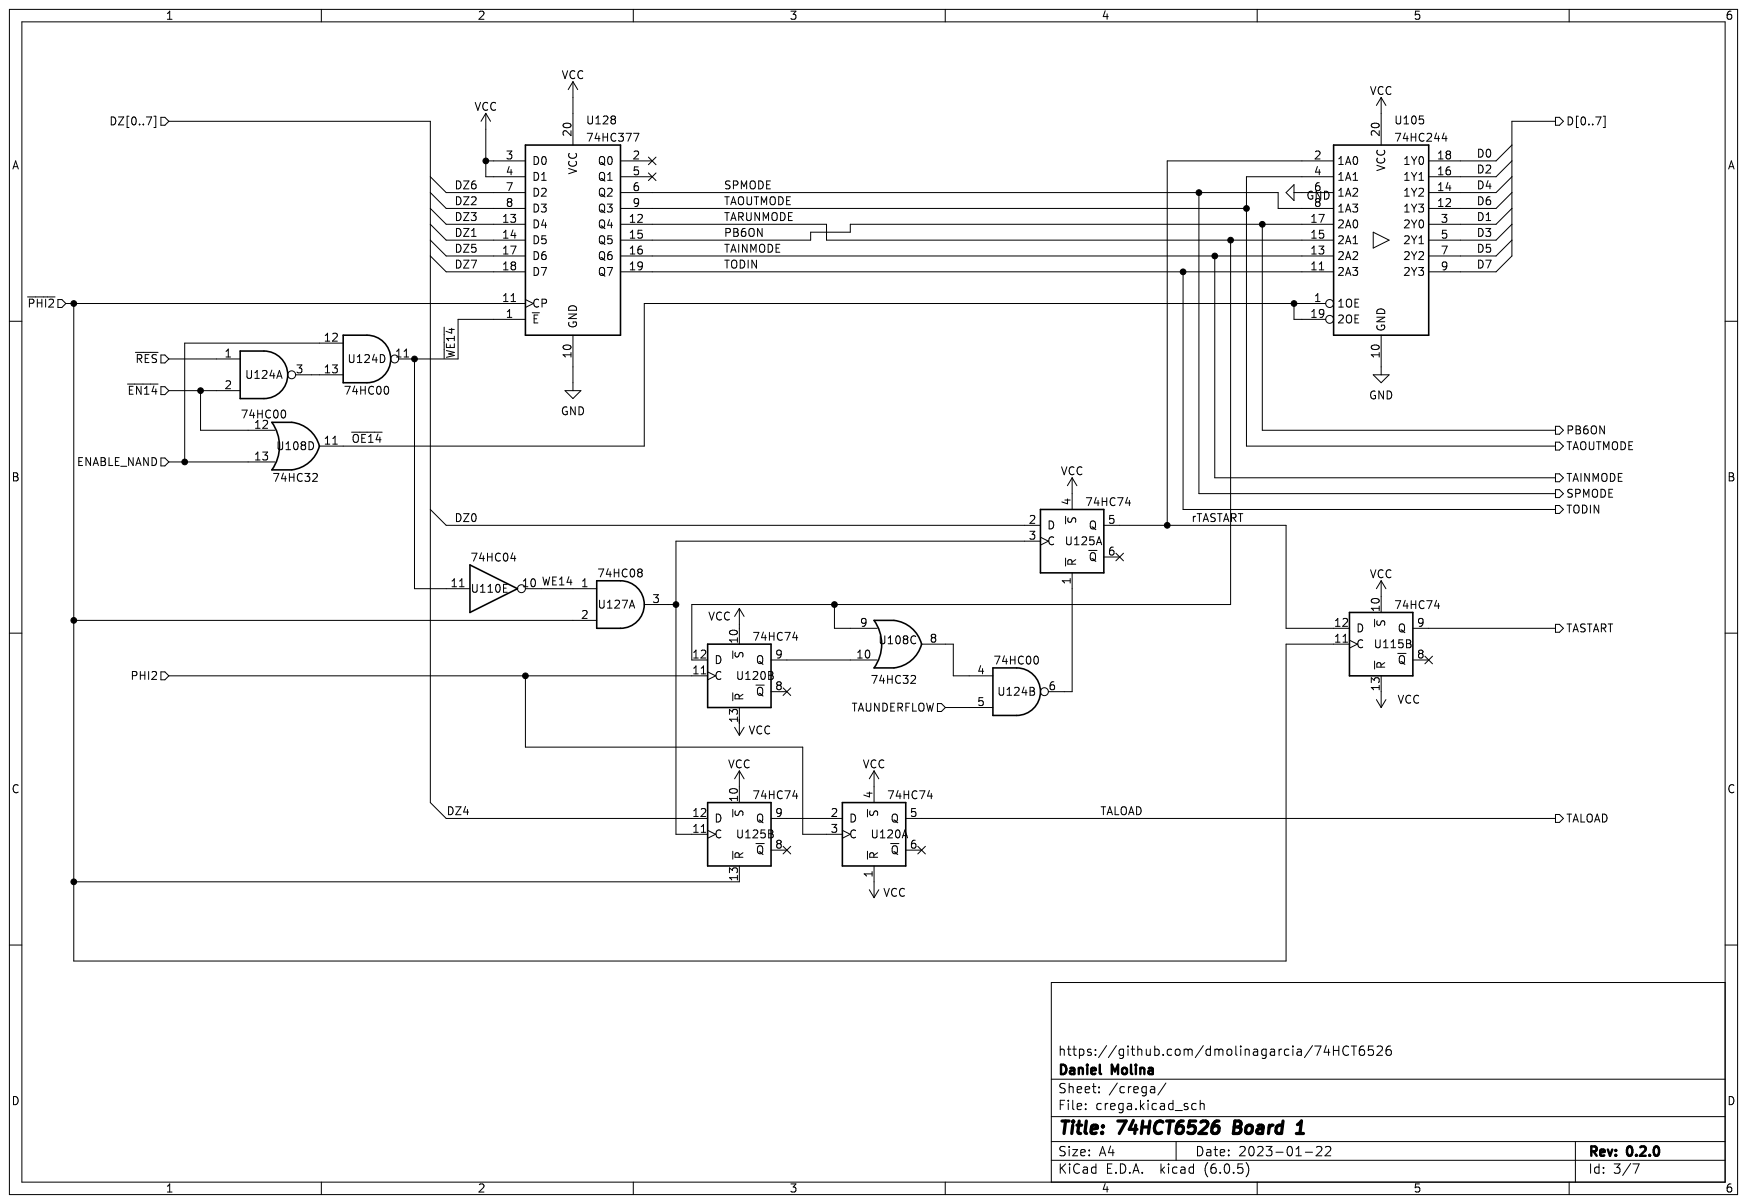
[picture p219: page 3]

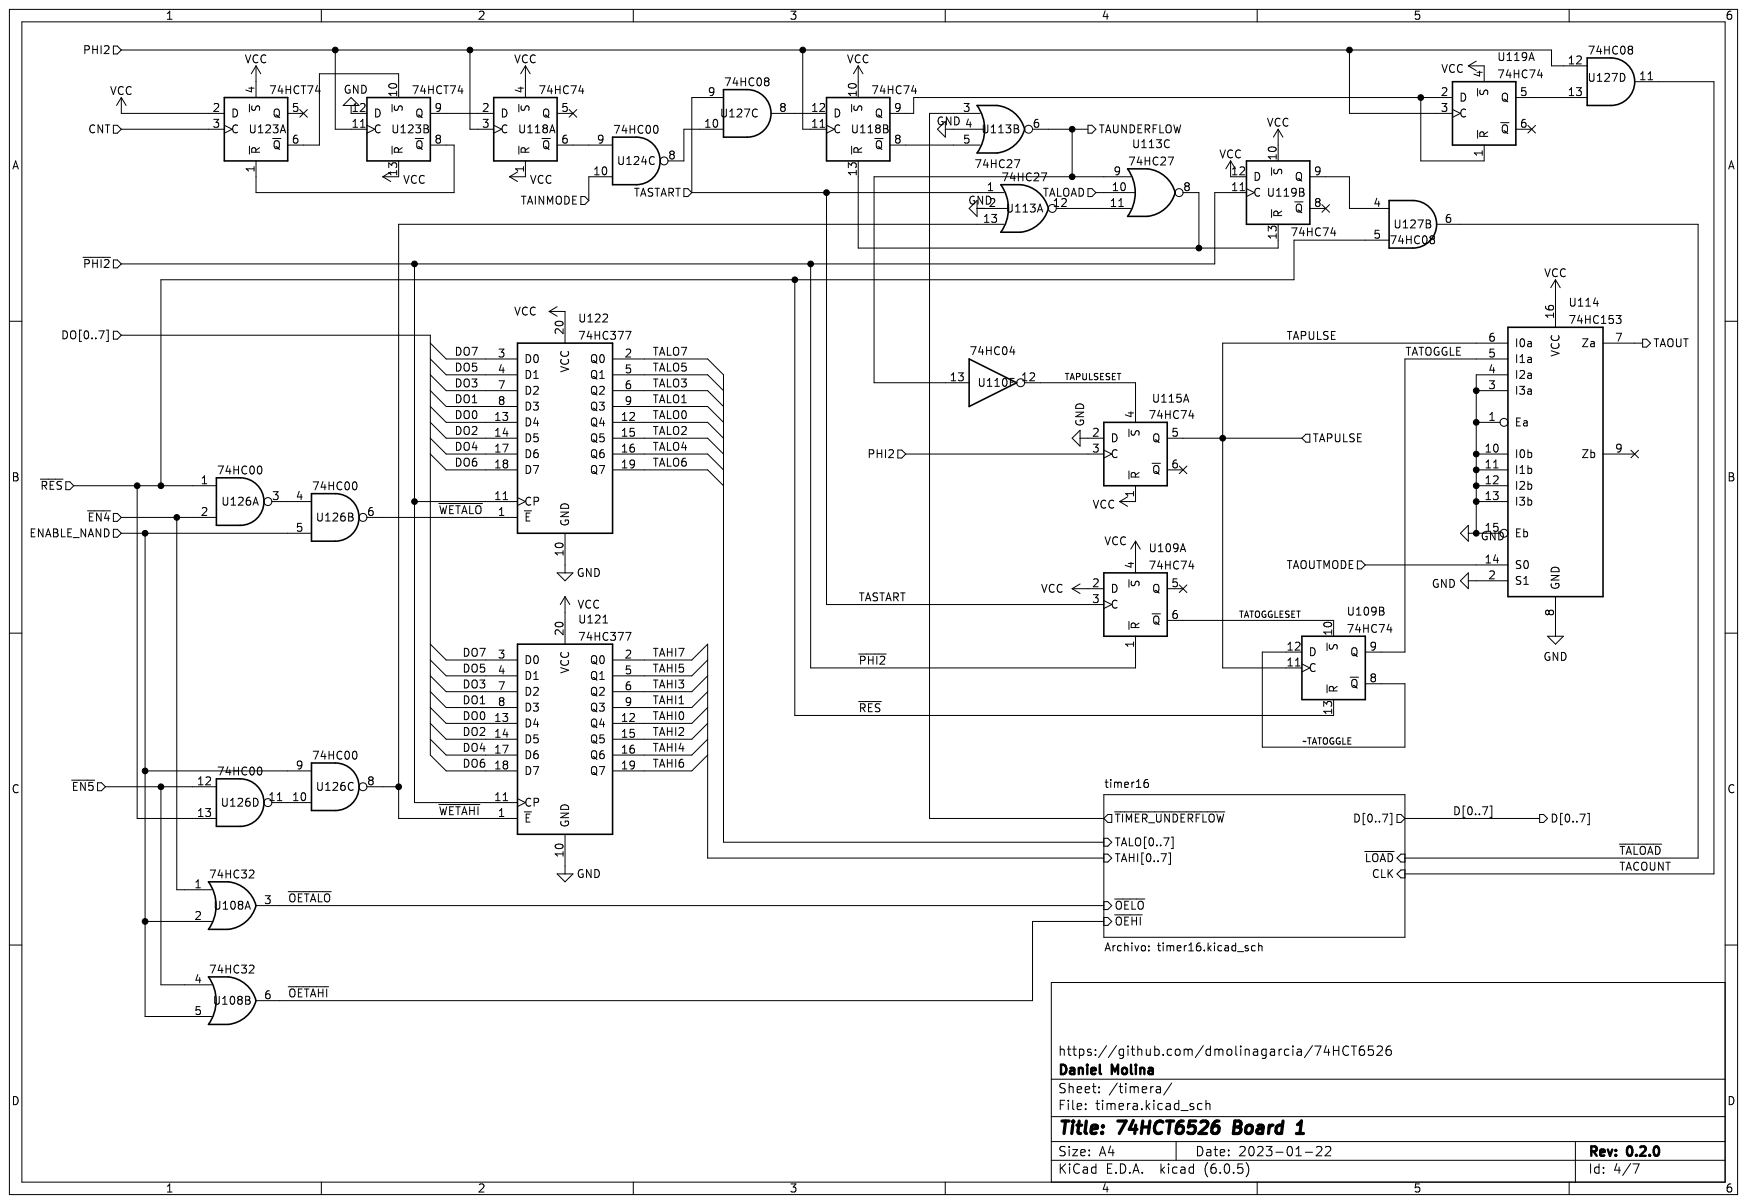
[picture p220: page 4]

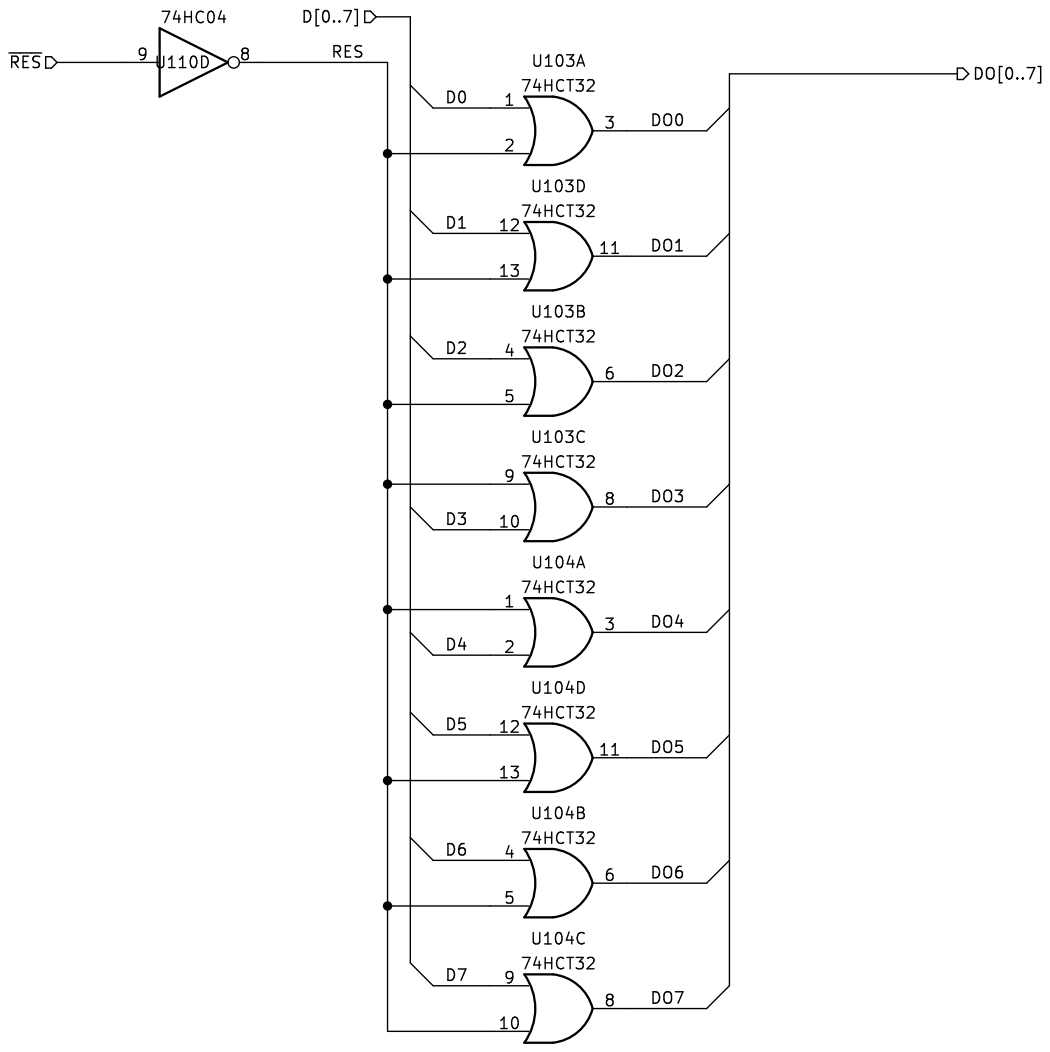
[picture p221: page 5]

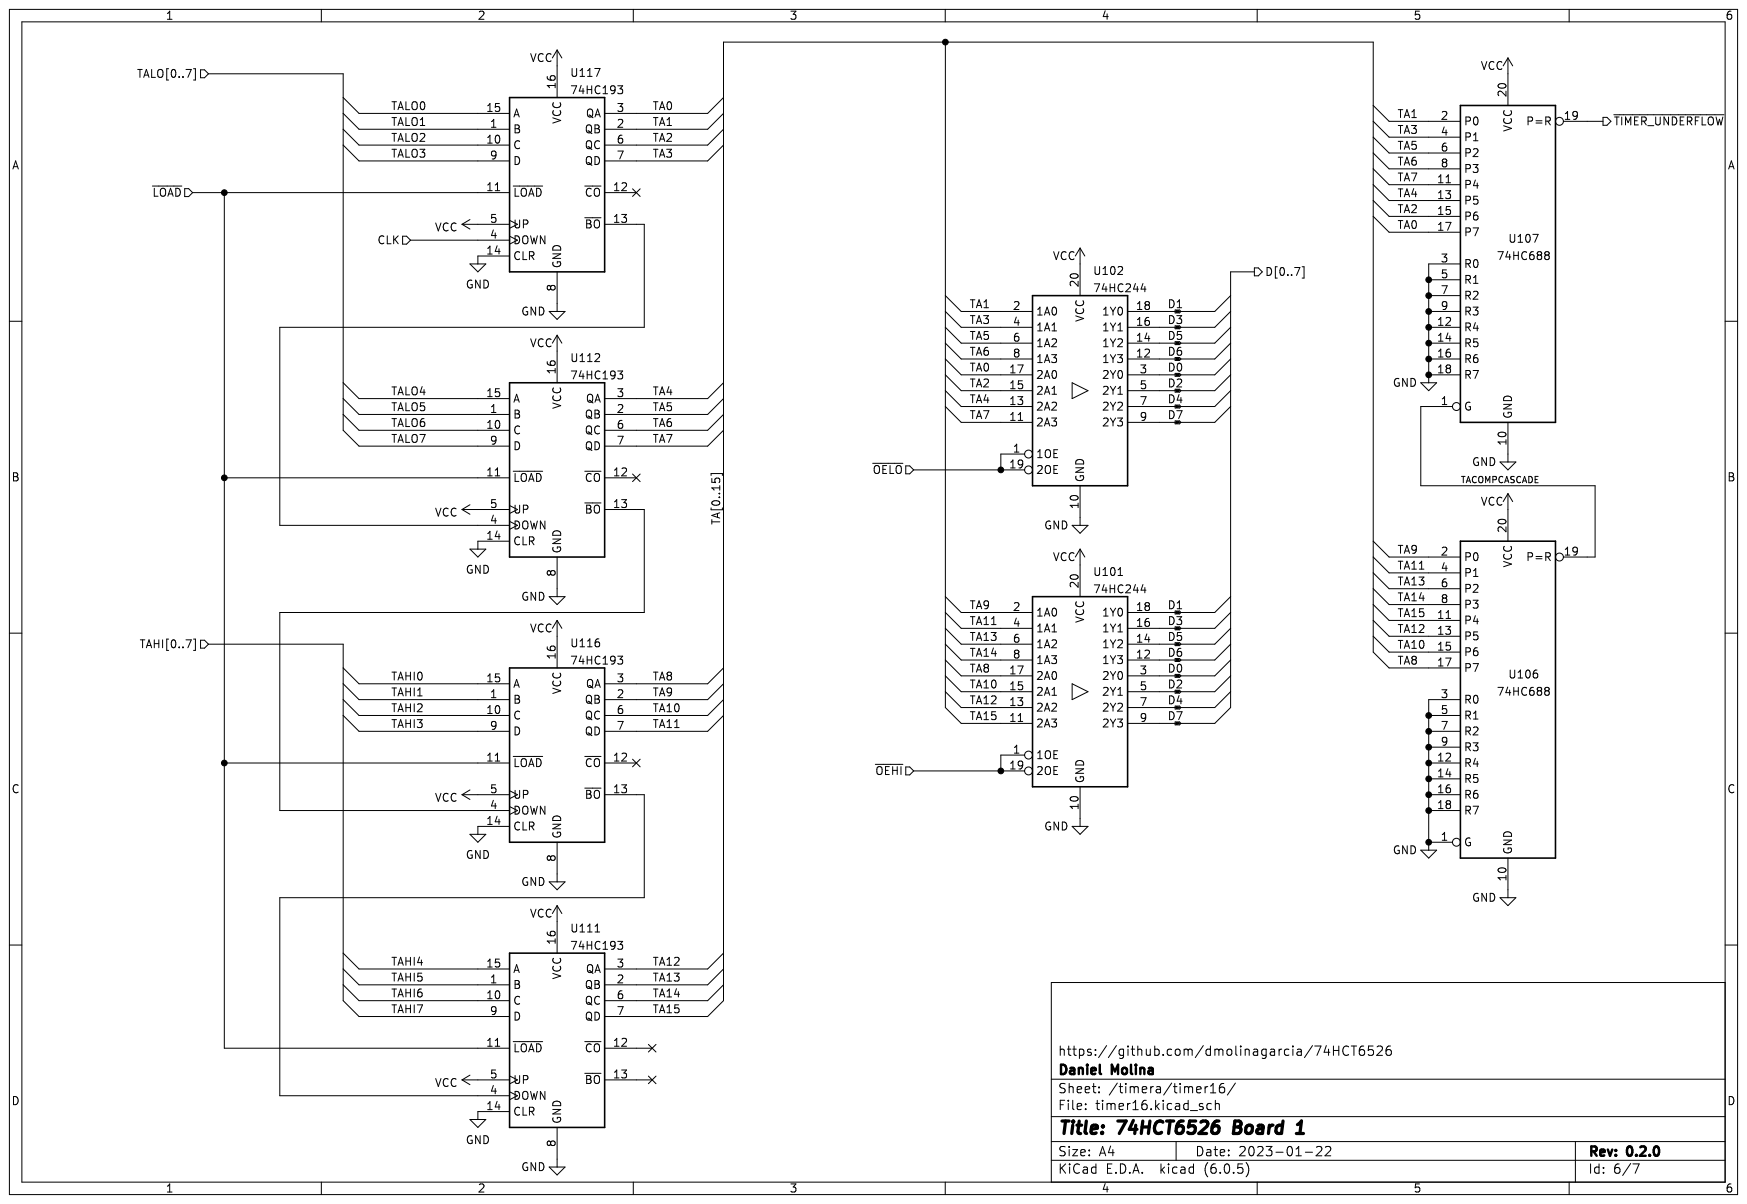
[picture p222: page 6]

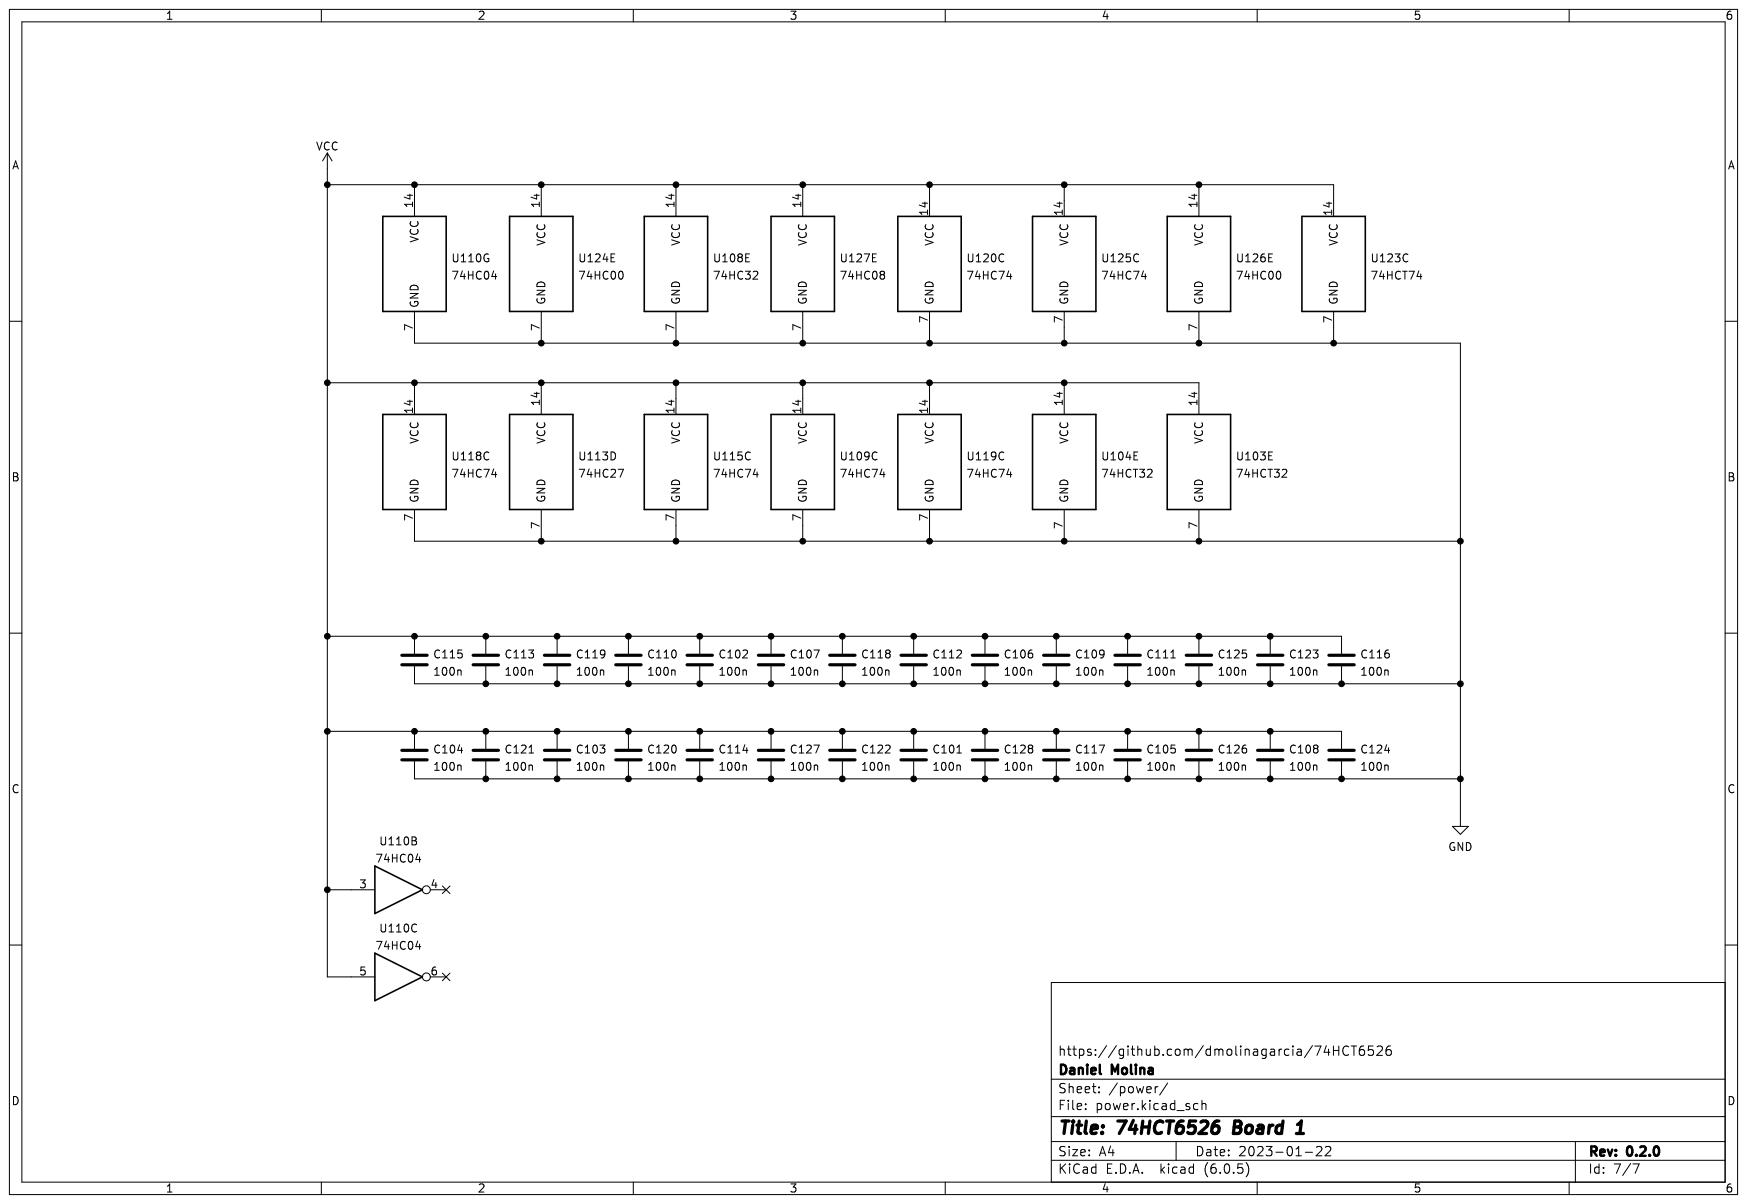
[picture p223: page 7]
