dmolinagarcia/74HCT6526/pdf/B0.sch.v0.2.0.pdf

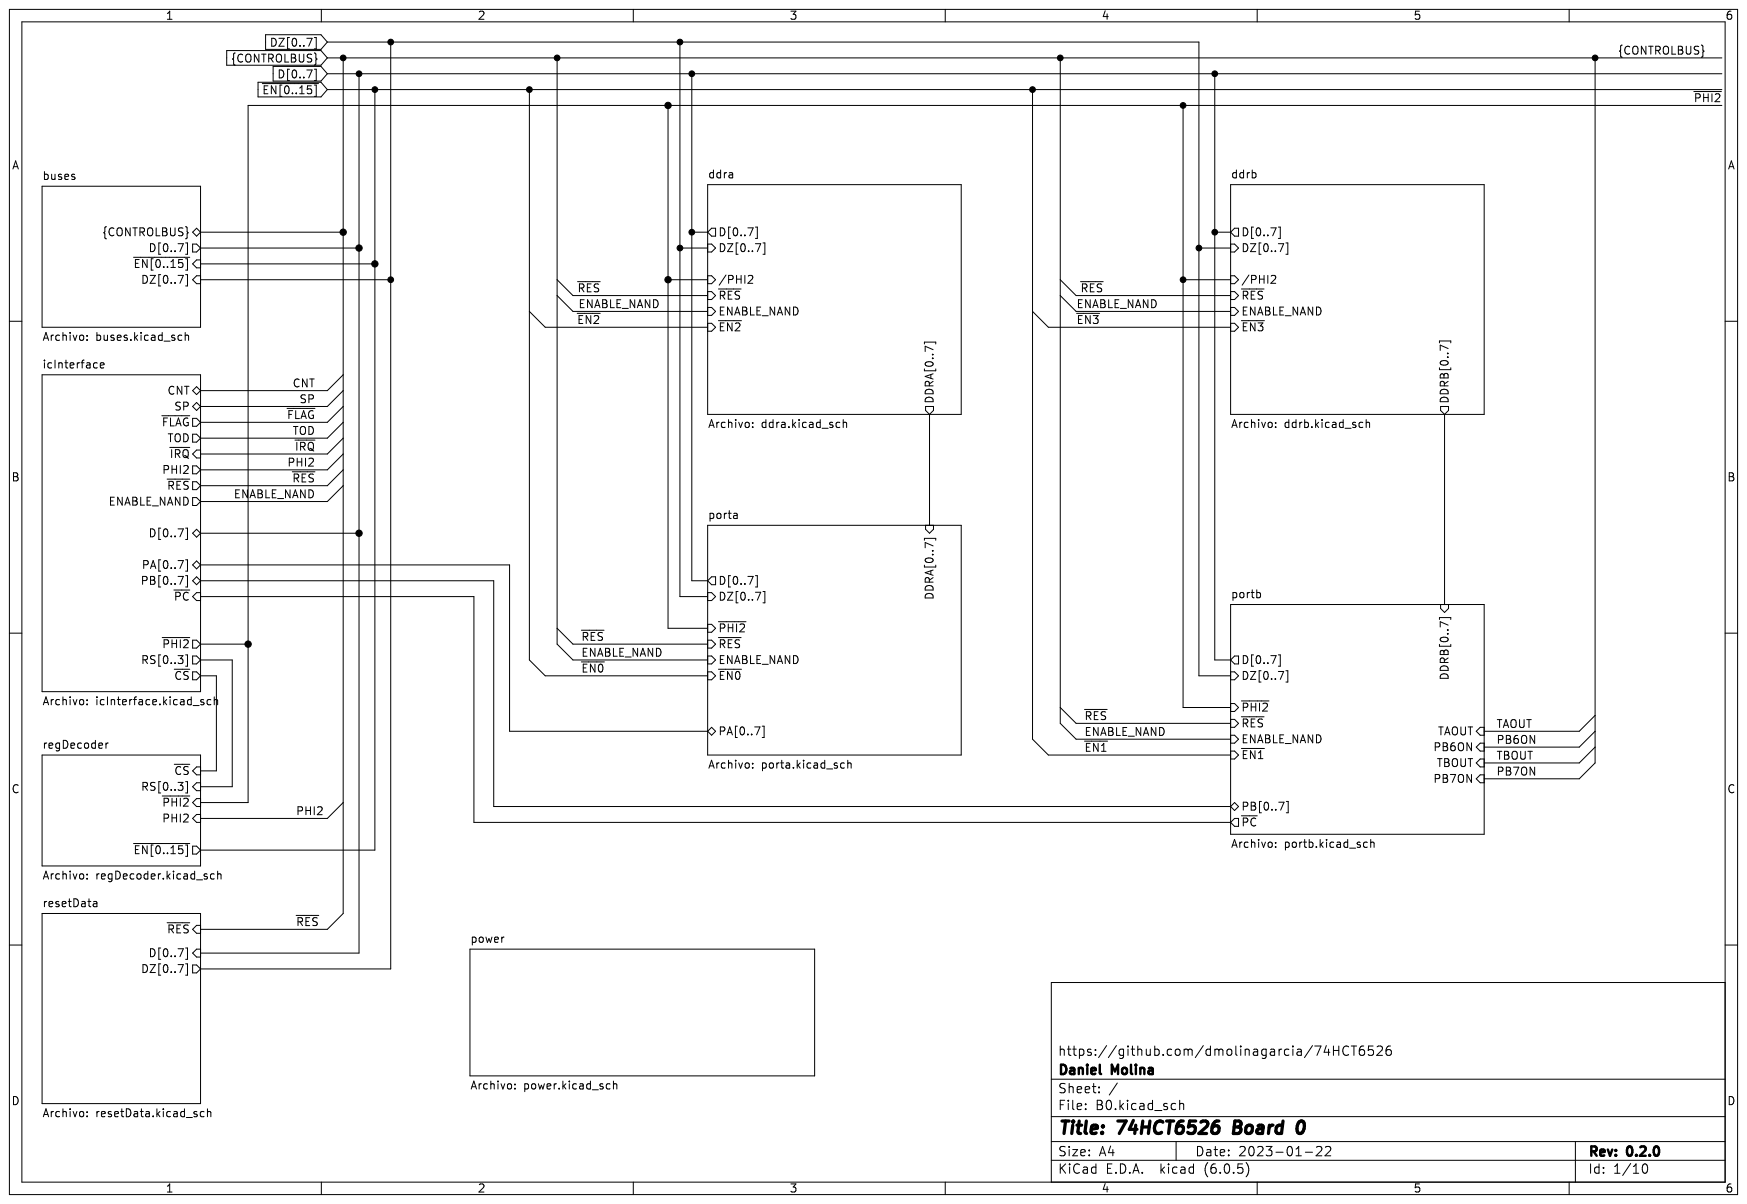
[picture p224: page 1]


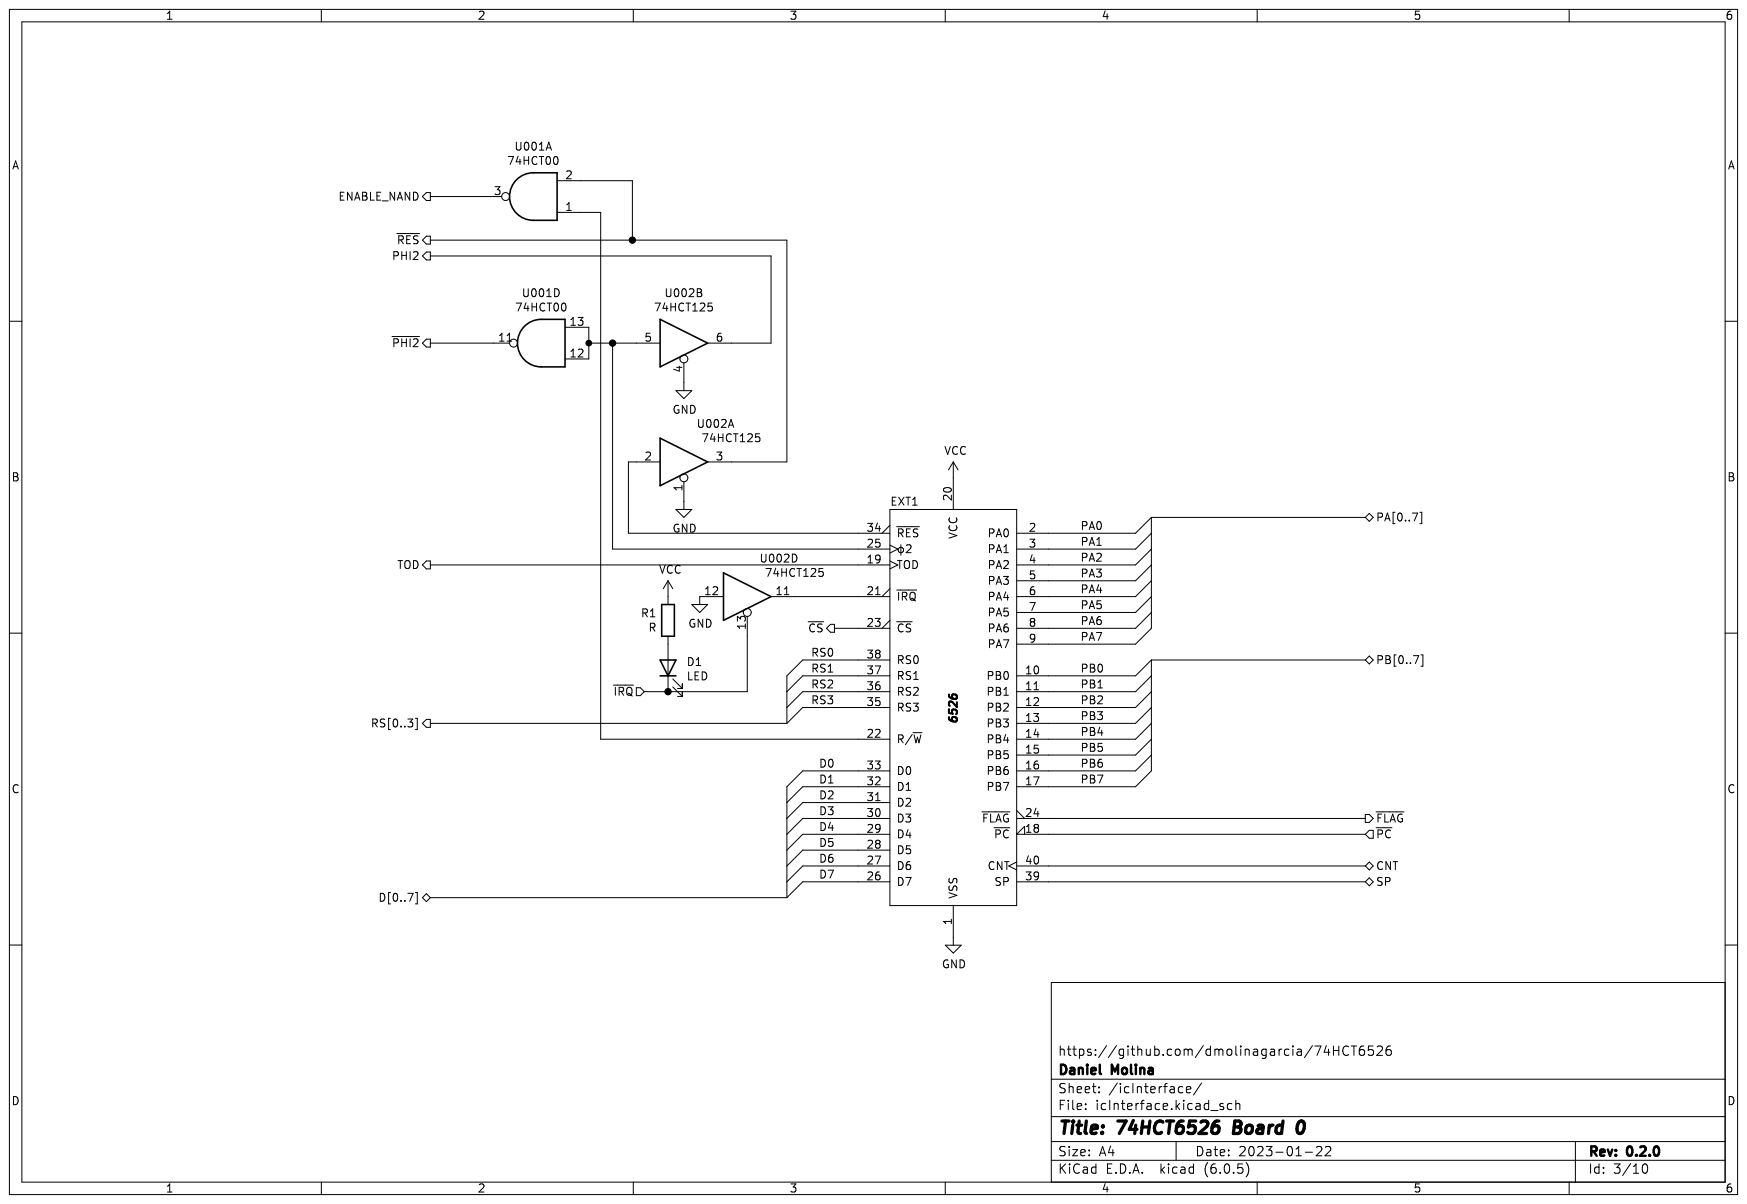
[picture p225: page 3]



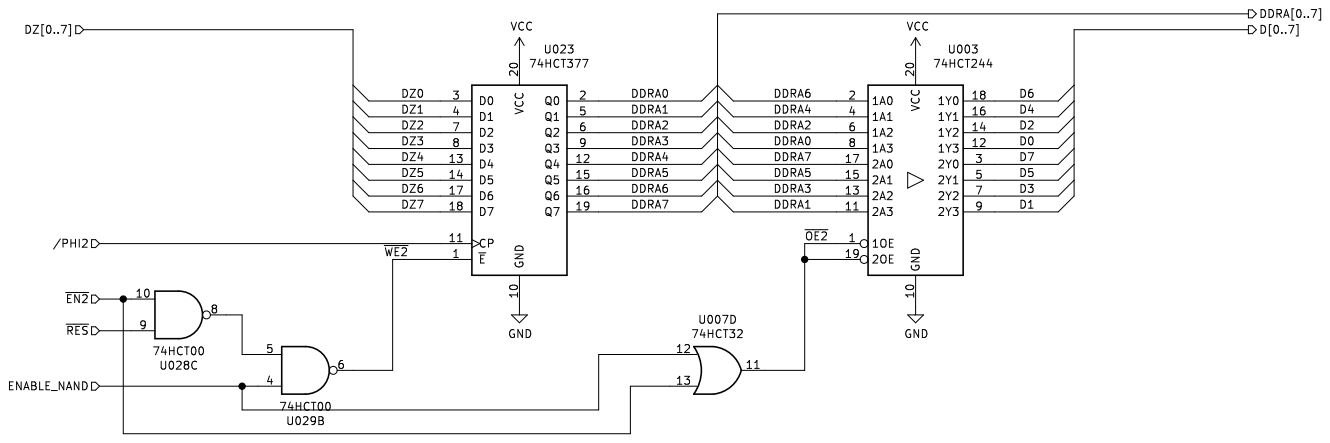
[picture p226: page 6]

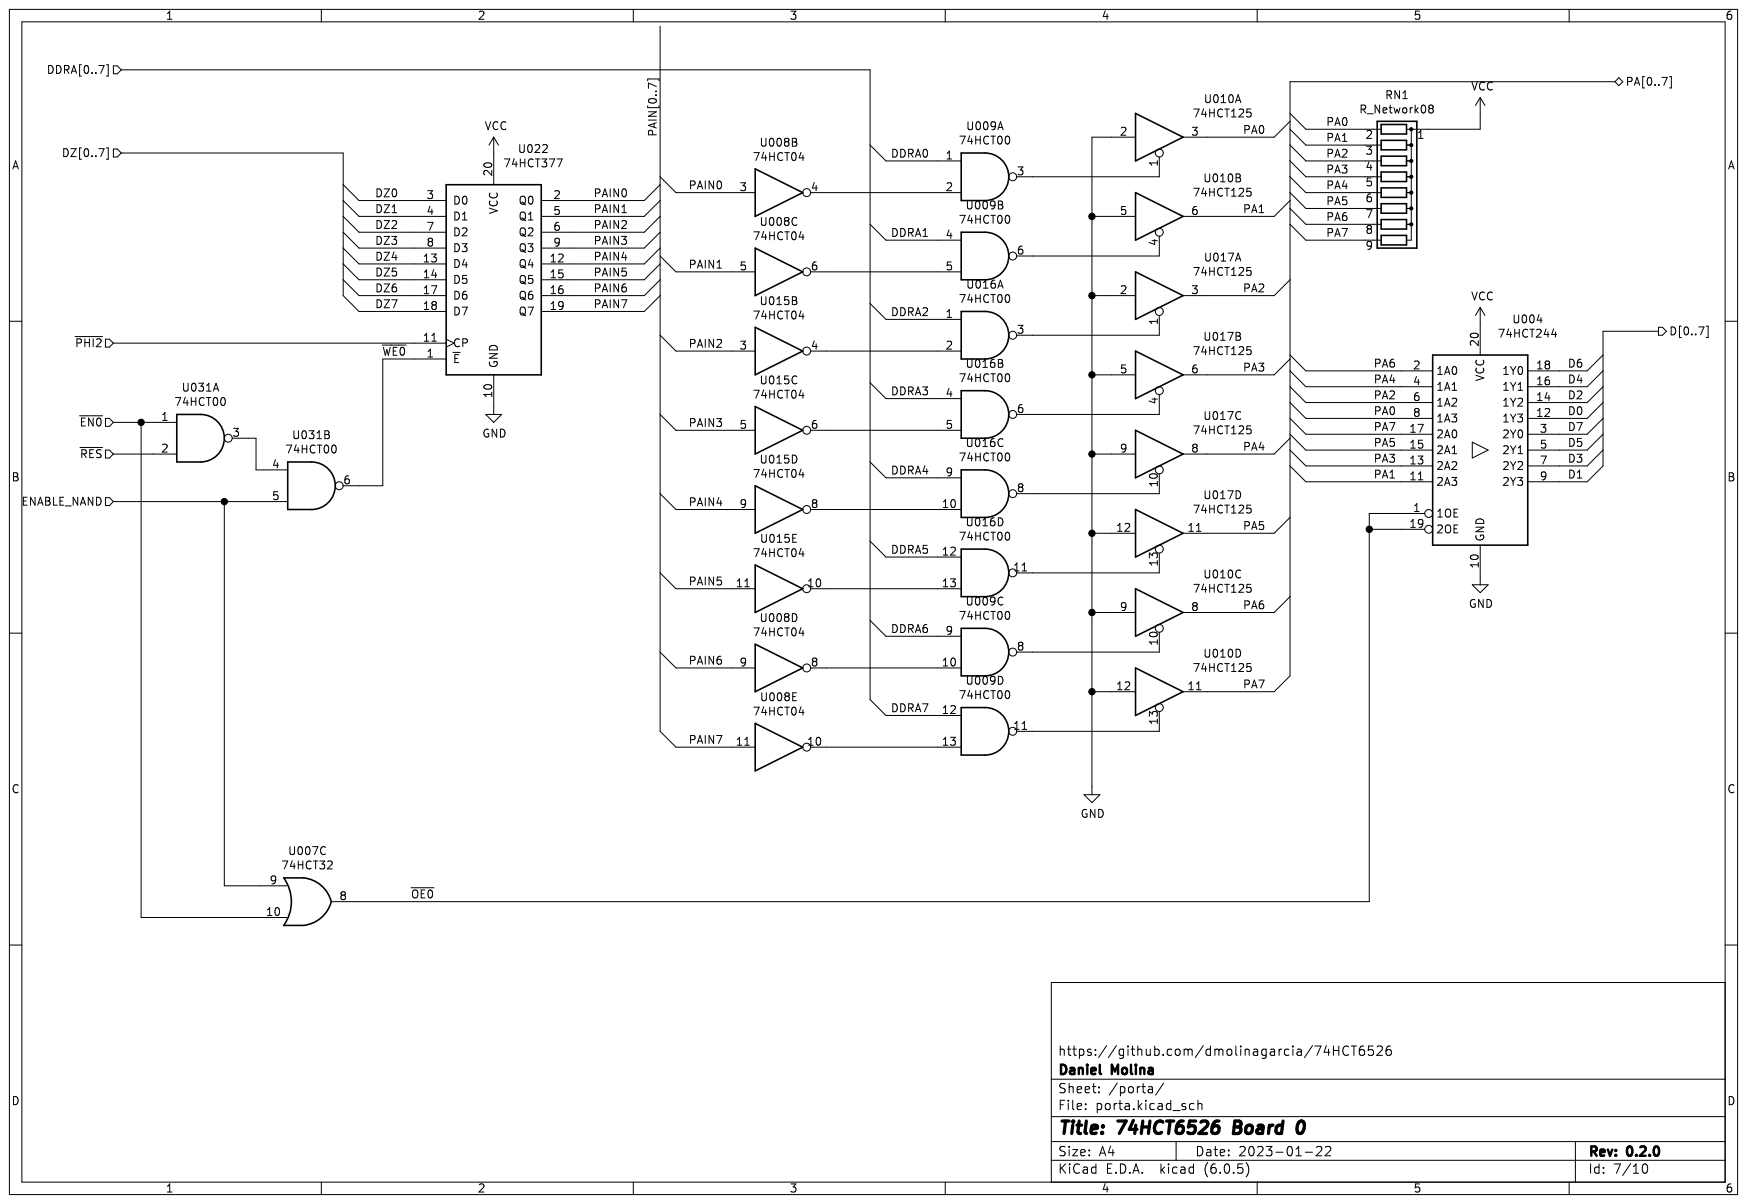
[picture p227: page 7]

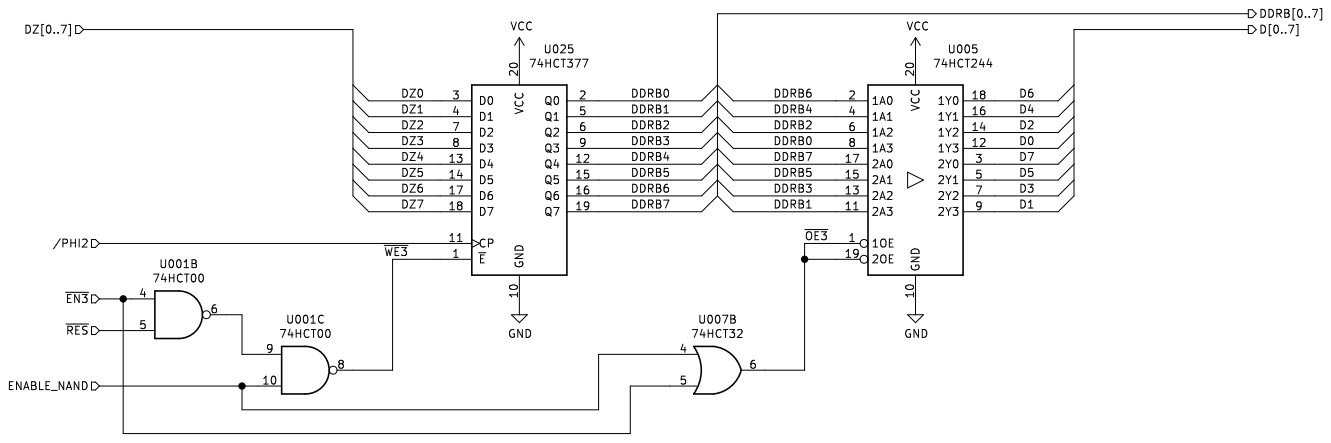
[picture p228: page 8]

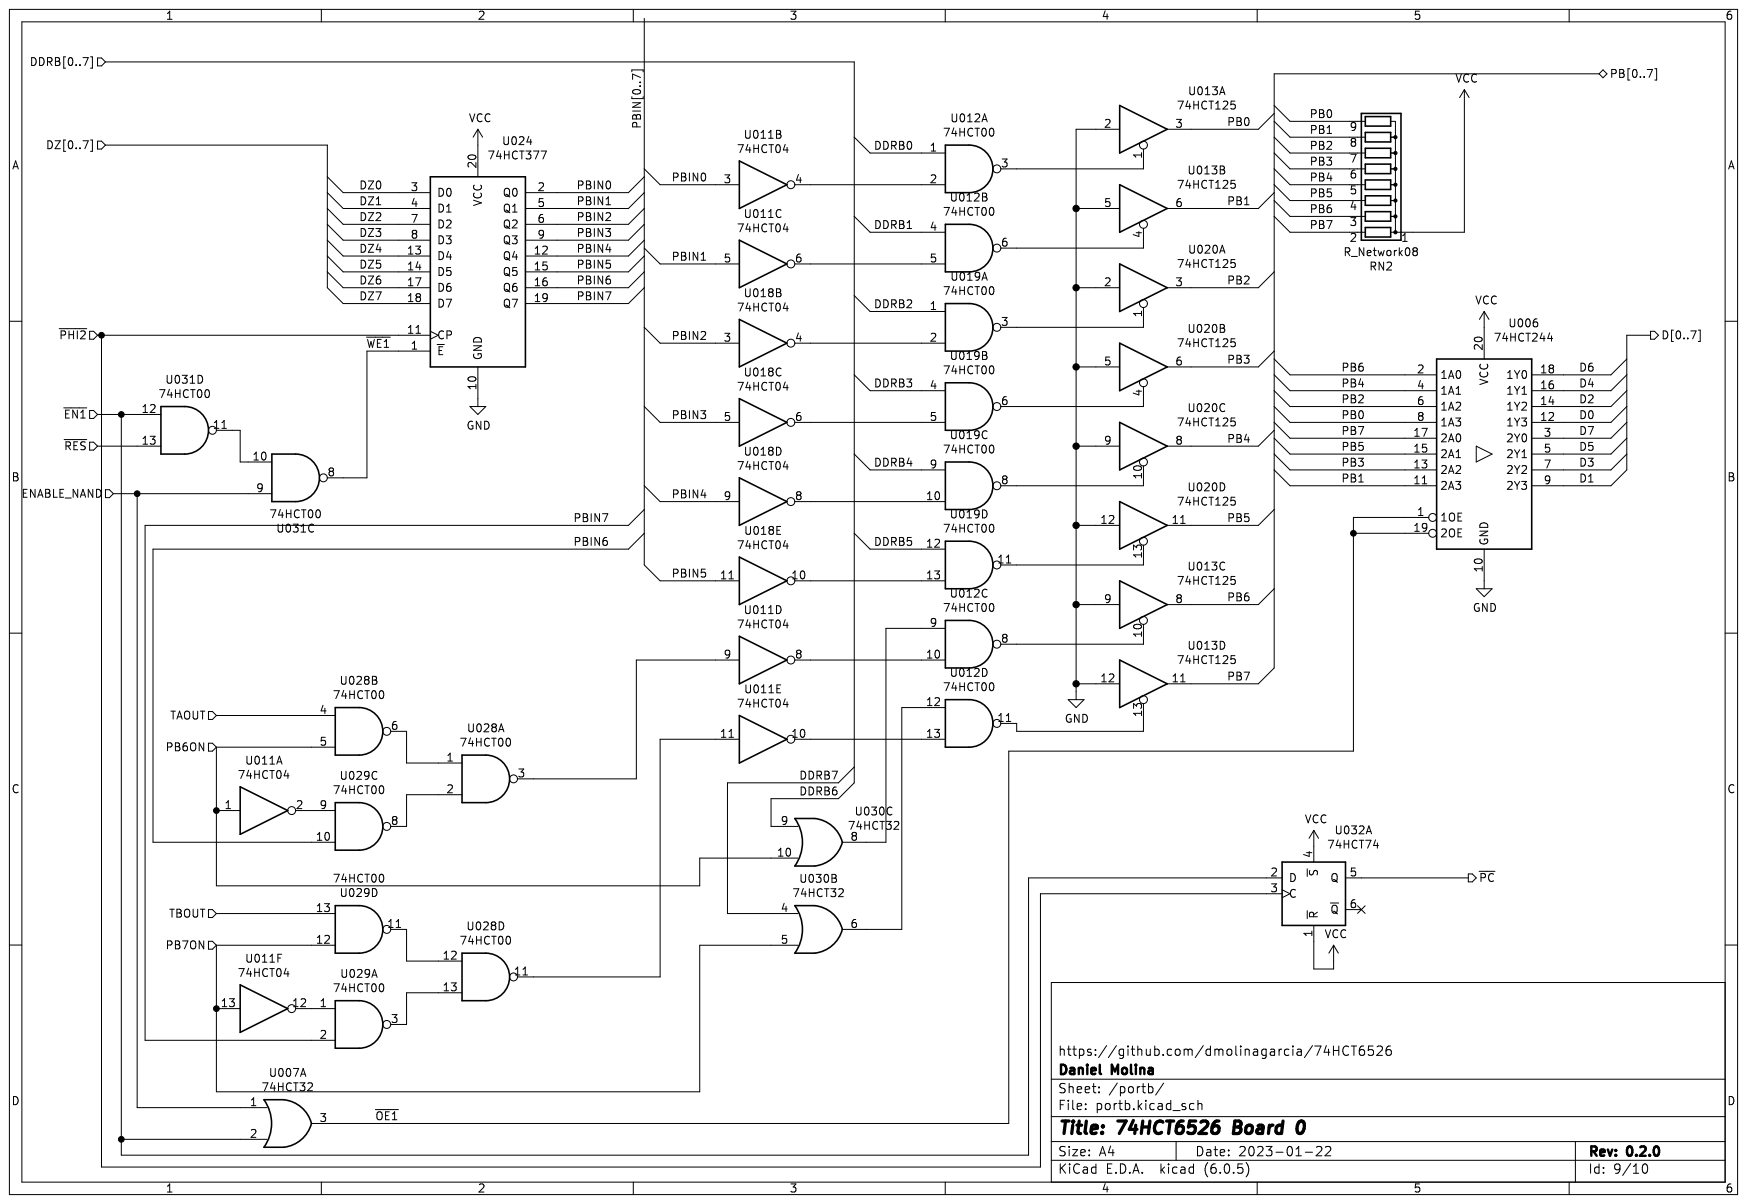
[picture p229: page 9]

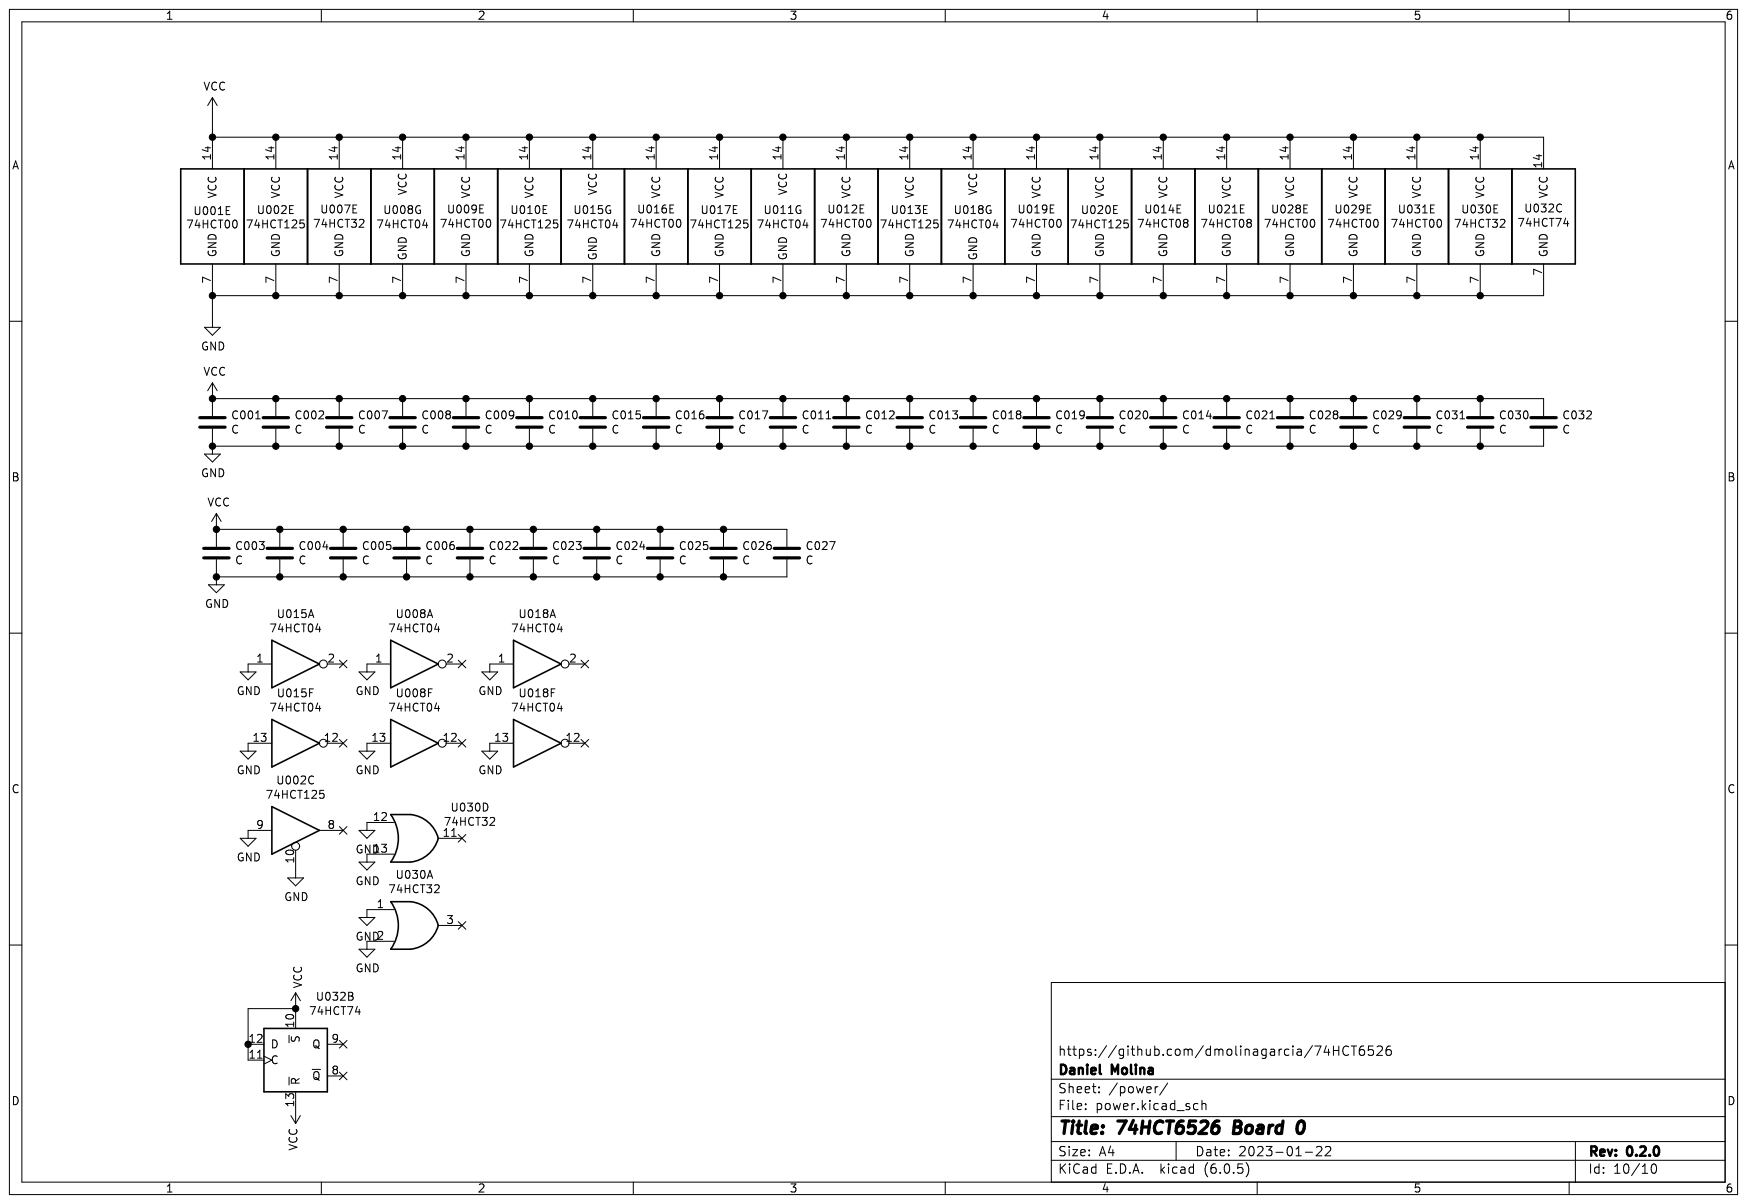
[picture p230: page 10]
